digitie/canview/docs/reviews/adversarial/evidence/2026-09-05-r1-hardware-navigation-postfix-manifest.md

# Post-fix 동일 기준선 재검토 요청

## 최종 상세 sheet 수 표기 교정 요청

- 시각:2026-09-05 04:30:31 UTC
- A submission: `01a06fd5-1714-72a0-8322-d575cbdc0821`
- B submission: `01a06fd5-187f-79b1-8d61-fd06d04ad2ec`
- 두 post-fix 원문을 확정·보존한 뒤 동일하게 요청했다. 타 reviewer의 post-fix 판정은 공개하지 않았다.

```text
두 post-fix 원문을 서로 공개하기 전 파일로 보존했습니다. 마지막 기계적 count 교정 1줄만 독립 확인 요청합니다. 최종 c1c15b573476e176e0f445ea74d408bc923fa025, parent 57ac03a7394c98a1464bf0d9f2777df666f711ad. Windows Git object-only diff이며 hardware/communicator/README.md의 27개 상세 sheet를 28개(+root 총29)로 고칩니다. USB 감지 LDO sheet가 늘어난 최종 root/schematic.pdf와 수가 일치하는지, 다른 diff 없고 기존 PASS가 그대로 유지되는지 짧은 final addendum을 주세요. 기존 전체 review 반복 필요 없음. 두 reviewer에게 같은 요청. 타 reviewer의 post-fix verdict는 전달하지 않음.
```

## 기능 수정 재검토 요청

- 요청 시각:2026-09-05 04:17:14 UTC
- Reviewer A: `01a06f2e-7129-7261-99bc-1bf2a1d6d490`, submission `01a06fc8-ea0f-7b73-97ec-02bd05ec7990`
- Reviewer B: `01a06f2e-735a-7221-9541-de848f1984b2`, submission `01a06fc8-eb7c-72b2-8a0a-a746994bc732`
- Windows KiCad Python의 Git blob 검사 결과: revision `59b2412627eb9773410545690f0609175b80e756`, `git_blob_digest_mismatches=[]`, exit0

## 두 reviewer에게 전달한 공통 요청 원문

```text
R1 post-fix 동일 immutable 재검토 요청.
기준 commit=59b2412627eb9773410545690f0609175b80e756; parent/base(initial candidate)=06bb51c72180f9c040db3ccf0b223a823c570409. Repository F:/dev/canview. Windows native Git object-only 방식 유지. plain worktree는 계속 source 금지, 생성/코드 실행이 필요하면 Git blob bytes를 메모리로 로드하거나 별도 clean detached 방식 사용. 기존 AGENTS/runbook 적용. 두 최초 원문은 docs/reviews/adversarial/evidence/2026-09-05-r1-hardware-navigation-reviewer-a.md / -reviewer-b.md에 모두 독립 확정 후 보존했으므로 이제 cross-report 확인 가능.
Scope: 본인 findings 전부 closure 확인 + initial->postfix 전체 delta 회귀. 특히 Q1/Q2 BUK7Y12 DC±20V vs LM14.5/13V; FT U28/U29 active-high SN74AHCT1G126-Q1 CAHCT1G126DBVRQ1, AUTO5V supply +OE마다1k GND PD; USB detection-only U16 TPS7A2033 pre-limiter supply, U1/U2/pullup USB_CC3V3; USB3k minimum1mAload; PHY0 fault, startup/rail sequencing and other logic effects. 새 manufacturer PDF2개 저장(전체56개1745p). Current exports343physical BOM1235namedpads,4ERC0/waiver0. Main Windows full exporter completed including5hardware net/Boolean tests;16protocol host tests pass; allPDFhash/parse pass. 정적 회귀는 analog HIL이 아님.
B fixes: rate-array-derived mask, DR/profile/NAV/age crosschecks, UNAUTHORIZED non-public zero/digest, version strict2u8, WaveJ8 25TX43/27RX44 NC labels; encode와 raw-wire decode 모두 test. LF normalization+.gitattributes; --git-revision 검사로 immutable bytes check. Main command Windows KiCadPython validate_exports.py --git-revision 59b2412627eb9773410545690f0609175b80e756 --git-executable C:/Program Files/Git/cmd/git.exe.
Additional delta: native export normalization, artifact checks, document link validator preserving immutable reviewer original absolute paths, current docs/ref index/HIL cases, original reports preservation. Main independent C-01 hashes/C-02 FTpower duplicates are coordinator-audit.md.
Expected output: actual hash/isolation/time/id, each originalfinding FIXED or stillOPEN with primary evidence, whole delta newfoundP0~P3, scope/unperformedtests, final PASS/CONDITIONAL/BLOCK only for design-review integration. Explicitly do not approve PCB/G1/HIL/vehicleTX. Land90-0409 and missing latestPDFs/PCBthermal/SOA/micSI remain known physical release gates. No mutations. Please perform focused closure in ~5-10min without extending to unrelated backlog; do not omit non-fabrication defects.
```

A 추가 요청: 본인의 R1-A-001..004 원판정을 재확인하며 P1 closure를 명확히 판정하십시오.

B 추가 요청: 본인의 B-R1-001..004와 추가 version boundary를 재현하여 closure 확인하십시오.

## 후속 단일 쪽수 교정 — 동일 추가 요청

```text
작업을 처음부터 다시 시작하지 말고 마지막에 이 추가1줄 correction도 확인해 주세요. 추가 immutable commit 57ac03a7394c98a1464bf0d9f2777df666f711ad (parent59b2412627eb9773410545690f0609175b80e756)는 hardware/references/README.md의 AHCT DBV 도면 쪽수만17~19로 바로잡습니다. 20~22는DCK였고 실제회로/footprint에는변화없습니다. main이PDF17/19/20/22를 직접읽어확인했습니다. 기존59b2412의 전체postfix closure검토를 계속하되 final에서 이추가diff원문도확인하고 최종57ac03a까지대상으로 기록하십시오. 두 reviewer에게 동일하게전달합니다. 감사범위를 다른backlog로확장할필요없습니다.
```
