digitie/canview/docs/reviews/adversarial/evidence/2026-09-05-r1-hardware-navigation-postfix-reviewer-b.md

# Reviewer B 수정 후 원문

- 대상: `57ac03a7394c98a1464bf0d9f2777df666f711ad`
- 원 서브에이전트: `01a06f2e-735a-7221-9541-de848f1984b2`
- [공통 요청](2026-09-05-r1-hardware-navigation-postfix-manifest.md)
- 아래는 다른 reviewer의 수정 후 판정을 전달하기 전에 보존한 최종 응답 원문이다.

---

## Reviewer B 판정: PASS — 설계 검토본 통합에 한정

**B-R1-001~004와 추가 version boundary 모두 FIXED입니다.** 전체 post-fix delta에서 새 P0~P3 결함은 확인하지 못했습니다. PCB 제작·G1·HIL·차량 TX는 승인하지 않습니다.

### 실행·격리

- 실행 ID: `CANVIEW-R1-B-CLOSURE-20260905T041729Z`
- 시작/종료 UTC: `2026-09-05 04:17:29` → `04:25:05`
- initial: `06bb51c72180f9c040db3ccf0b223a823c570409`
- post-fix: `59b2412627eb9773410545690f0609175b80e756`
- **최종 대상: `57ac03a7394c98a1464bf0d9f2777df666f711ad`**
- Windows native Git으로 두 후속 commit의 type/hash/parent를 확인했습니다.
- **Object-only, clean=N/A — working tree를 소스로 사용하지 않았습니다.**
- 코드·시험은 Git blob에서 메모리로 로드했습니다. 파일 수정·Git mutation 없음.
- 허용된 최초 A/B 원문과 coordinator audit를 확인하되, closure는 실제 코드·생성물·제조사 PDF로 재검증했습니다.

### 기존 finding closure

| 항목 | 상태 | 확인 근거 |
|---|---|---|
| **B-R1-001 · P2** capability 모순 | **FIXED** | [codec:38](/mnt/f/dev/canview/tools/protocol/navigation_codec.py:38)의 배열 기반 mask와 profile/NAV/DR/age 교차 검사 확인. 기존 두 공격 입력 및 추가 undefined-bit 47개를 **encode·raw-wire decode 양쪽에서 거부**. DR age 0/1/45000/45001 경계도 확인했습니다. |
| **B-R1-002 · P2** UNAUTHORIZED snapshot 노출 | **FIXED** | [codec:67](/mnt/f/dev/canview/tools/protocol/navigation_codec.py:67)에서 status3의 공개 필드 외 값·digest를 0으로 강제합니다. 기존 노출 payload와 비공개 필드별 변조를 양방향에서 거부하고 정상 redacted 응답은 수용했습니다. |
| **B-R1-003 · P2** immutable hash 불일치 | **FIXED** | [LF 정책](/mnt/f/dev/canview/.gitattributes:1), [normalizer](/mnt/f/dev/canview/tools/hardware/normalize_exports.py:8), [immutable 검사](/mnt/f/dev/canview/tools/hardware/validate_exports.py:91) 확인. **59b2412와 최종 57ac03a 모두 16개 artifact digest mismatch=0, exit=0**입니다. |
| **B-R1-004 · P3** Waveshare UART 이름 반전 | **FIXED** | [생성 입력:76](/mnt/f/dev/canview/tools/hardware/sensor_circuits.py:76)과 생성물에서 **25=TXD43_NC, 27=RXD44_NC**, 두 접점 NC 유지 확인. 공식 schematic J8과 일치합니다. |
| 추가 version boundary | **FIXED** | [codec:89](/mnt/f/dev/canview/tools/protocol/navigation_codec.py:89)가 정확히 두 u8 정수만 허용합니다. 추가 원소·float·bool·누락·None·문자열·범위 초과를 거부하고 정상 tuple/list 경계는 수용했습니다. |

### 전체 delta의 전원·논리 회귀 확인

- **Q1/Q2:** BUK7Y12-100E의 DC VGS ±20V와 LM74800 최대 HGATE 14.5V/DGATE 13V를 원문으로 대조했습니다. 연결과 LFPAK56 유지도 확인했습니다. DC 여유는 각각 5.5V/7V이며, 동적 overshoot·SOA 승인은 아닙니다. 근거: [BUK7Y12 p.2](/mnt/f/dev/canview/hardware/references/pdf/buk7y12-100e.pdf), [LM7480 p.6](/mnt/f/dev/canview/hardware/references/pdf/lm7480.pdf).
- **FT U28/U29:** `CAHCT1G126DBVRQ1`, AUTO5V 공급, active-high OE, 각 1k GND pull-down을 실제 netlist에서 확인했습니다. 제조사 핀·진리표와 일치하며, PHY3V3=0의 정상상태에서는 TXD pull-up/EN pull-down으로 차단됩니다. 1k의 약 3.3mA 부하는 permit 구동기의 정상 전원 구동 능력 안입니다. 근거: [AHCT p.3–5, 8, 13](/mnt/f/dev/canview/hardware/references/pdf/sn74ahct1g126-q1.pdf).
- **USB 감지부:** 두 보드 모두 U16이 limiter/mux 앞에서 USB_CC3V3를 만들고 U1/U2/pull-up을 공급합니다. SYS3V3 순환 의존성이 없습니다. 3k 최소부하와 LDO ±1.5% 조건, TUSB320LAI 권장 VDD 범위도 대조했습니다. 급격한 collapse·느린 ramp·detach 과도응답은 정적 검사로 승인하지 않았습니다.

A의 원 finding에 대한 공식 closure 판정은 Reviewer A의 재확인이 별도로 필요합니다.

### 마지막 1줄 correction

`59b2412 → 57ac03a` 전체 diff는 **[reference 색인:68](/mnt/f/dev/canview/hardware/references/README.md:68)의 한 줄뿐**입니다.

PDF를 직접 확인한 결과:

- 17/18/19쪽: **DBV0005A** 외형/land/stencil
- 20/21/22쪽: **DCK0005A** 외형/land/stencil

수정이 정확하며 회로·footprint·코드·시험 객체에는 변화가 없습니다.

### 실제 재현 결과

| 검증 | 결과 |
|---|---|
| Windows protocol host 시험 | **16/16 PASS** |
| Hardware net·정상상태 Boolean 시험 | **5/5 PASS** |
| 생성 소스 → 연결 모델 → BOM/pinmap/XML/sexpr netlist/named pad | **343개 / 1,235개 일치** |
| Schematic S-expression 파싱 | **45개 PASS** |
| 제조사 PDF hash·크기·전체 페이지 파싱 | **56개 / 1,745쪽 / 95,230,736byte PASS** |
| 문서 링크 검사 | **113문서 / 690 local target, 오류 0** |
| CRLF 주입·LF 정규화·재실행 무변경 | 메모리의 지정 24파일에서 **PASS** |
| Margin 계산 | 저장 결과와 일치 |
| 저장된 ERC/waiver | 네 보드 **0/0 확인** |

시험·전체 생성물 검사는 `59b2412`에서 수행했고, 마지막 commit의 변경이 색인 한 줄뿐임을 확인했습니다. 최종 hash에 대한 immutable digest 검사는 별도로 재실행했습니다.

Native 전체 export/ERC 자체, analog fault injection, PCB/열/SOA, 실제 replay cache·동시 allocator, GNSS/PPS qualification, 마이크 3m SI는 실행하지 않았습니다. `embedded-documentation`은 변경된 핀·전원 소유권·문서 계약의 정합성 기준으로만 사용했습니다.

**결론: Reviewer B의 비제작 결함은 모두 닫혔습니다. 설계 검토본 통합은 PASS이며, land90-0409·미확보/최신 PDF·물리 검증 및 기존 제작/G1 차단은 그대로 유지해야 합니다.**
