digitie/canview/firmware/docs/esp-core-bench.md

# ESP32 공용 bench core

[T-200a](../../docs/tasks/T-200a-esp32-core-bench.md)의 Communicator core를 [T-400a](../../docs/tasks/T-400a-bridge-core-bench.md)에서 Bridge와 공용화한다. 후속 UART/무선/OTA와 실물 T-200/T-400 gate는 포함하지 않는다.

## 구성·소유권

`firmware/app/esp_core.c`는 SDK가 생성한 main task에서 BSP/runtime → portable boot → 고정 pool → 주기 health를 조합한다. `firmware/module/esp_core/health.c`, `pool.c`와 `firmware/interface/canview_esp_*.h`는 strict C99이며 HAL·SDK·FreeRTOS·heap API를 포함하지 않는다. 각 project의 `bsp/board.c`는 생성 pin 정본으로 안전 출력을 설정하고, `bsp/runtime.c`는 메모리와 진단 입력 pin을 SDK 독립 config에 연결한다. 실제 SDK include와 호출은 `firmware/platform/esp32s3/core_runtime.c`/`canview_esp32_runtime` component 하나에 둔다.

core·pool·runtime은 app의 정적 저장소이며 reset 전 재초기화하지 않는다. app stack에는 작은 port 사본만 둔다. 입력 config와 port, 0이 아닌 Flash/PSRAM 가용 byte 계약은 값으로 복사하며 callback context는 사용 완료까지 살아 있어야 한다. runtime의 main owner identity와 고정 주기 tick은 다른 task에서 접근하지 않는다. SDK adapter의 private 정적 spinlock 두 개는 watchdog과 pool용으로 분리한다. core callback은 open한 main owner task만 호출할 수 있으며 ISR과 같은 runtime callback의 재진입을 `INVALID_ARGUMENT`으로 거부한다. app은 그 실패를 service fault로 처리해 feed를 중단한다.

## Boot와 실패

| 단계 | 성공 조건 | 실패 시 |
|---|---|---|
| Communicator BSP | RUN_OK7 LOW → BOOT0 요청2 LOW → GPS47 LOW → reset1 HIGH → recovery9 OD HIGH → RTS15 HIGH → TX17 HIGH, 입력8/16/18/48/38 pull 없음 | 이후 단계 중단, 외부 default-safe gate 유지 필요 |
| Bridge BSP | LED5 LOW → button4 입력, 내부 pull 없음(R14 외부10k pull-up) | 이후 단계 중단, 입력이 서비스/페어링 허가로 승격되지 않음 |
| watchdog | TWDT2초 panic, 두 idle core 감시, 현재 main task 신규 등록 | 기존 subscription 탈취·자동 재시도 없음 |
| memory/clock | BSP 고정 Flash/PSRAM 정확 일치, internal heap≥80KiB/largest≥32KiB, main stack 여유≥1024B | 최초 fault 보존, feed 없음 |
| bench | pool 초기화와 USB metadata 진단 후 주기 health | UART/radio/CAN/OTA/NVS write 시작 없음 |

state는 UNINITIALIZED → STARTING → SAFE_BENCH 또는 FAULT다. boot 성공 자체는 watchdog feed가 아니다. clock backward/freeze, 이전 진척250ms 초과, health 실행20ms 초과, SDK 오류 또는 메모리 하한 위반이면 FAULT로 고정한다. callback에서 이미 latch한 fault도 덮어쓰지 않는다. wait/pool 오류도 app의 service status로 기록하고 loop를 빠져나가 더 이상 feed하지 않는다. `core.state`는 마지막 core 검사 상태이며 로그의 `status`와 함께 해석한다.

GPIO는 latch를 먼저 기록한 뒤 mode를 바꾼다. Communicator ESP와 Bridge는 partial GPIO 오류가 나도 이 표의 모든 safe output/input을 순서대로 시도하고 최초 오류를 보존한 뒤 다음 lifecycle 단계로 가지 않는다. RTS HIGH는 송신 흐름 정지, TX HIGH는 idle이다. UART driver를 설치하지 않는다. sense48은 서비스 RUN 감지, sense38은 USB mux 선택 진단일 뿐 rail PGOOD나 차량 권한이 아니다. cap/TX는 항상0이다. MCU 코드 실행 이전 reset/brownout 안전은 외부 pull/gate와 실물 계측 없이는 증명할 수 없다.

## 보드별 계약과 진단

| 보드 | Flash/PSRAM 실제 SDK 가용량 | 입력 valid mask와 bit 의미 | SDK project metadata |
|---|---|---|---|
| Communicator N16R8 | 16777216 /7864320B, Octal80MHz·ECC | 3: bit0 GPIO48 RUN sense, bit1 GPIO38 USB sense | canview_communicator_esp32 |
| Bridge N8R2 | 8388608 /2097152B, Quad80MHz·ECC 없음 | 1: bit0 GPIO4 PAIR_BUTTON_N, LOW=눌림, bit1 부재 | canview_diagnostic_bridge |

메모리는 board manifest/generator가 raw 용량과 ECC overhead를 구분하여 BSP header로 제공한다. generator는 wire와 무관한 0이 아닌 `CANVIEW_BOARD_PROFILE`도 header에 고정한다. 이 tag는 board ID만이 아니라 canonical board manifest 항목과 pin source를 함께 digest하므로 같은 ID의 stale pin contract도 다른 profile이 된다. `app_main()`은 BSP port를 한 번 복사한 뒤 `canview_esp_board_preflight()`로 runtime object의 생성 profile을 GPIO·idle·SDK open보다 먼저 대조한다. Communicator/Bridge runtime은 다시 같은 preflight를 적용하므로 서로 다른 BSP object를 교차 link하면 GPIO 0회·runtime open 0회로 거부한다. SDK sample은 측정값이며 boot/health의 고정 계약을 바꾸지 않는다. 다른 보드의 Flash 또는 PSRAM 값을 섞으면 terminal memory fault다. 공용 core는 SKU나 GPIO를 알지 않는다. 역할 표시는 SDK의 고정 project metadata에서 오며 외부 패킷으로 선택하지 않는다.

runtime은 입력 수1..2, SoC GPIO 유효성·중복·미사용 원소0을 검사한다. 실제 모듈 pad 제한은 generator가 별도로 검사하고, 독립 BSP fixture는 고정 핀을 대조한다. 로그의 input-valid는 존재하고 읽은 입력, input-level은 그 bit의 전기적 HIGH다. 미존재 bit를 LOW로 해석하지 않는다. Bridge 버튼은 폴링 진단이며 debounce/ISR/서비스 window/OTA/페어링을 시작하지 않는다. 어떤 sense 조합에서도 cap/TX0은 변하지 않는다.

## RTOS·시간·watchdog

| owner | 분류·우선순위·stack | 주기·예산 | 통신/감시 |
|---|---|---|---|
| IDF main service | soft real-time bench health, IDF main priority1/CPU0, stack8192B | 100ms fixed-rate, 이전 진척250ms, 실행20ms | 현재 task TWDT subscription 하나 |
| SDK idle CPU0/1 | SDK 소유, idle priority | SDK 스케줄링 | 각각 TWDT 감시; main은 대리 feed하지 않음 |

SDK 초기화·watchdog 등록에서 SDK 내부 allocation은 존재할 수 있다. core/pool runtime에는 malloc/free가 없다. Flash/PSRAM은 SDK 부팅이 초기화하며 application이 재초기화하거나 NVS를 열지 않는다. IDF6.0.3 `uxTaskGetStackHighWaterMark`는 **byte** 단위다. PSRAM get_size는 ECC 제외 가용 크기다. heap 수치는 internal·8-bit capability의 free와 largest block이며 PSRAM을 internal RAM으로 합산하지 않는다.

첫 wait에서 tick 기준을 잡고 이후 `xTaskDelayUntil`의 이전 wake tick을 보존한다. 지연 없이 반환되는 overrun은 TIMEOUT이다. catch-up loop로 여러 feed를 만들지 않는다. 32-bit tick wrap은 SDK API에 맡기며 health는 별도의 64-bit monotonic microsecond clock을 검사한다.

core는 sample 완료 뒤 시간을 검사하고, adapter는 자신의 critical section 진입 뒤 clock을 검사한 후 `esp_task_wdt_reset`을 호출하며 호출 직후 clock을 다시 확인한다. `fed_at`은 SDK 호출 직후 확인한 **post-call 시각**이다. task 선점은 막지만 SDK 내부 spinlock 대기, NMI/고우선순위 interrupt·cache stall 상한과 watchdog reset latency는 HIL 미검증이다. 이 상한을 이미 보장했다고 주장하거나 차량 safety deadline으로 재사용하면 안 된다. 다른 worker를 추가할 때 각 worker가 자기 subscription과 진척을 소유해야 한다.

실패 후 app은 한 번 상태를 출력하고 idle만 호출한다. 등록 후에는 main이 feed하지 않아 TWDT panic/reset을 기다리며, 등록 전 실패는 safe idle로 남는다. USB가 연결되지 않은 경우 출력 지연도 health deadline에 포함된다. journal/자동 NVS erase/reboot 복구는 구현하지 않는다.

## 고정 pool 계약

정적16slot × payload256B, capacity1..16이다. 초기화와 acquire/copy/release/stats 모두 platform context validator를 먼저 호출해 ISR을 상태 변경·lock 진입 전에 거부한다. task 또는 SDK callback이 동일 bounded lock을 통해 acquire/copy/release/stats를 호출한다. pool은 lock을 잡은 채 client callback을 실행하지 않으며, consumer가 lock 내부에서 다시 pool API를 호출하는 것은 금지한다. ISR·lock 내부 callback·token의 동시 다중 owner 사용은 금지한다. 256B 복사/clear는 lock 아래 수행하며 실제 critical WCET는 아직 계측하지 않았다. radio ingress에 사용하기 전 T-202에서 예산을 측정한다.

acquire는 payload를 복사하고 pool 주소·slot·generation token을 반환한다. 내부 pointer를 노출하지 않는다. context/output/source alias와 크기 오류를 거부한다. 해제는 payload를 지우고 generation이 UINT32_MAX인 slot은 영구 retire하여 wrap ABA를 막는다. token은 RAM 전용이며 serialize/reboot 뒤 재사용하지 않는다. exhaustion/stale은 UINT32_MAX에서 포화하며 used/high-water/retired를 lock 아래 snapshot으로 반환한다. 부족하거나 잘못된 token이면 출력 버퍼/길이를 변경하지 않는다.
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
