digitie/canview/docs/tasks/T-400a-bridge-core-bench.md

# T-400a Bridge 최소 core와 ESP 공용화

- 상태: `DONE`
- merge: [PR #23](https://github.com/digitie/canview/pull/23), `25eba080907257c6d90abaeec6d578d9dff6585a`
- 우선순위: `P0`
- Gate: `G0 / G1 software 준비`; 실제 G1/G2 물리 gate는 `NOT_RUN`
- 선행: `T-001`, `T-200a`

## 목표와 분리 이유

Communicator ESP32 core merge 다음으로 Bridge N8R2의 boot/health/watchdog 기반을 구현한다. T-400의 SoftAP·인증·무선·휴대폰·부하·실물 acceptance는 유지하고 최소 core 소프트웨어만 분리한다. 공통 동작을 복제하지 않고 재사용하되 Communicator N16R8의 검증된 안전 초기화와 실패 동작을 보존한다.
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
