digitie/canview/docs/reviews/adversarial/evidence/2026-09-09-T-104-validation-14ea3c9.md

# T-104 수정 candidate 로컬 검증

- Candidate: `14ea3c9bcad22ac27fa8989291ea54656f6f4952`
- Base: `b17bdfc0bb2a1bfa9d300c1e7662cac05c96df40`
- 실행: 2026-09-09, Windows PowerShell; Linux는 WSL 보충 검증이다.
- firmware/shared/protocol canonical source SHA-256:
  `8ccfe8d227ba3454dab51864cc65634f4922c5351aabe4296564061f63e47b56`
- 검증은 commit 직전 동일 source에서 수행했고, host fixture provenance의 commit
  필드는 당시 HEAD `bdc6798`이다. firmware source digest로 수정 source를 구분한다.
- 독립 reviewer verdict나 CI 결과를 이 문서가 대신하지 않는다.

## 실제 실행 결과

| Gate | 결과 |
|---|---|
| Windows Clang Debug CTest | 120/120, 24.17초 |
| Windows Clang Release CTest | 120/120, 19.98초 |
| Python unit (Windows CTest 포함) | 117/117 |
| WSL GCC Release CTest | 120/120, 117.88초 |
| WSL Clang ASan/UBSan CTest | 120/120, 120.84초 |
| WSL TSan `esp32-pool-threads` | 1/1 |
| SDK 설정 negative/mutation | 13/13 |
| STM32 core binary gate unit | 7/7, GNU note/symbol/BIN malformed 포함 |
| STM32 coverage 기존 core/FDCAN/register | 설정된 function100/line95/branch90 gate 통과 |
| UART owner coverage function/line/branch | 100/73.4844/58.4282%, gate 100/70/50 |
| UART platform coverage function/line/branch | 100/79.5812/58.3851%, gate 100/70/50 |
| ESP32 core/pool/runtime coverage | function100/line95/branch90 및 app/wrong-BSP profile gate 통과 |
| shared wire/app coverage | line/function100%, branch99% 이상 |
| Doxygen 1.18.0 + Sphinx strict | PASS, 설정된 public API 71개 |
| board/UART/generated/plan/link | PASS; 문서 313개, local target 1317개, 오류 0 |
| staged diff 수동·제한된 secret/VIN/key pattern scan | match 0 |

HELLO reset의 digest 보존 assertion 추가 후 Windows/WSL 전체 시험과 STM32·ESP32·
shared wire/app coverage를 모두 재실행했다. STM32 UART source 실측 수치는 동일했다.

WSL 첫 GCC 실행은 Python provenance suite 실패로 전체 `FAIL`이었다. Windows
worktree `.git` 파일 안의 `F:/...`가 Linux에서 유효하지 않아 commit이 `unknown`으로
반환됐다. `GIT_DIR=/mnt/f/dev/canview/.git/worktrees/t104-stm32-uart-control`와
`GIT_WORK_TREE=/mnt/f/dev/canview-wt/t104-stm32-uart-control`를 해당 shell에만 설정하고
`git rev-parse HEAD`를 대조한 뒤 위 전체 GCC/ASan/UBSan 성공 결과를 얻었다.
Git metadata, source, timeout, 검사 조건은 수정하지 않았다.

## STM32 실제 target

STM32CubeG4 `1.6.3`, Arm GNU `15.3.rel1`, Ninja, Windows native build다.
각 build의 `cmake --build <build> --clean-first -j 6` stdout/stderr를
`t104-final-build.log`에 저장하고 `warning:|CMake Warning|ld\.exe: warning|error:`를
대소문자 무관 scan했다. Debug/Release 모두 compiler/linker/CMake 진단 0건이다.

| 항목 | Debug (`build-t104-target-debug3`) | Release (`build-t104-target-release`) |
|---|---:|---:|
| Flash used | 51716 B | 39720 B |
| RAM used | 79816 B | 79816 B |
| CCMRAM used | 0 B | 0 B |
| 최대 개별 stack frame | 928 B | 992 B |
| GNU SHA-1 build ID 앞 16 byte | `579f8e9de845abfc08abb195dfa5cf74` | `20cc3b17ecdec7df7dcc061ca8675d52` |

개별 frame은 최악 call-chain·ISR 중첩 stack 실측이 아니다. ELF note를 objcopy로
추출해 GNU owner/type/20-byte descriptor를 확인하고, BSP linker symbol 주소와
Flash BIN의 동일 위치를 자동 대조했다. 독립 `readelf -n`도 해당 ID를 확인했다.
FDCAN RAM layout·54 CMSIS/model constants·23 C object stack 파일 gate도 통과했다.

artifact basename은 모두 `canview-communicator-stm32`다.

| Build | 형식 | 크기 B | SHA-256 |
|---|---|---:|---|
| Debug | BIN | 51716 | `865d82ebaf54d0b4dee61844fe3f7288a088ff6e6fd1dc64727b04a60f6d0f8b` |
| Debug | ELF | 1078332 | `b6fa73b82b1a8986067d715e7a69a281ecbfd26f7dbeeebd0dedd1caf60f0908` |
| Debug | HEX | 145564 | `a874298a2de897d8af7d9f0613688f33dcef2ca53b607868076f35f15860b8d4` |
| Debug | MAP | 322532 | `083378ab841f1f5823da6fe3d905251c950fd91524d176a904a9880bdb58c833` |
| Release | BIN | 39720 | `5694eea4399f67954420aff56ad41db3e76792e8ededd9f11391ba0ca1a68469` |
| Release | ELF | 62576 | `f11a5fddf9ef49eec779378f4f4e4c48dd97f621e98c618ee07122a1ef80c3e3` |
| Release | HEX | 111814 | `714e6b9234a8b846beeaaca37f02fc24edb99ddb781e4dc6bbf1409d083c2bab` |
| Release | MAP | 236658 | `75226b55ce550863c99e419f6834f9db245ff45ba1b9cd1ad6975a76ad604b53` |

build log SHA-256:

- Debug: `1cbe67488ddc10319eb10f28a9b8f1b454cd0ff2c18e2da5259d63512778de54`
- Release: `fc891b0f5fbe0b27ff23a9b3865abe01a2cb404fe353a1939be9969f2a08115e`

## 남은 gate

최신 candidate CI와 세 ESP target의 CI artifact 대조, 원 reviewer post-fix verdict는
별도 closure 대상이다. 이전 `bdc6798` CI `34322587967`의 6개 job 성공은 확인했지만
이를 `14ea3c9`의 CI 결과로 사용하지 않는다. 이전 24시간 분량 가속 C codec soak는
전기선·DMA·RTS/CTS 24시간 측정이 아니다.

실제 board flash/ST-LINK/USB, 전원·reset·brownout·watchdog 장시간 실측, 4 Mbps
UART·DMA/IRQ·CTS/RTS 및 physical 24시간 PRBS, CAN analyzer·차량 evidence,
security provisioning은 모두 `NOT_RUN`이다. G1/G2 물리 승인이나 vehicle TX
권한을 부여하지 않는다. 현재 `CAPTURE_ONLY`, 차량 CAN TX `NO-GO`를 유지한다.
