digitie/canview/docs/reviews/adversarial/evidence/2026-09-05-latest-toolchain-bootstrap-post-fix-reviewer-a.md

# Reviewer A 원본 결과

- Review ID: `CV-20260905-ENV-01-POST-A`
- 실행 ID: `01a06f3e-a770-7d61-a07a-32bbb40e928a`
- 전문 영역: embedded safety·target build·PowerShell
- 기준 commit: `cb7aae92e741f4bdeb5dc9a8a81011fc3b17c391`
- parent: `e7ad3c9e3a13ddcb2fe5b53364f12f582e9eaf2f`
- 작업 방식: read-only commit review, 파일 변경·commit 없음

## 결과

**PASS — P0–P3 finding 없음.**

`cb7aae9`와 parent hash를 확인했다. 추가된 recursive submodule cleanliness check가 incomplete·dirty clone을 올바르게 차단하며, tag·peeled commit·PATH·failure cleanup 검증을 약화시키지 않는다.

Windows PowerShell 실행과 target build는 이 Linux review 환경에 필요한 도구가 없어 미검증이다. build 성공으로 표시하지 않았다.
