digitie/canview/docs/reviews/adversarial/evidence/2026-09-05-latest-toolchain-bootstrap-post-fix-reviewer-b.md

# Reviewer B 원본 결과

- Review ID: `CV-20260905-ENV-01-POST-B`
- 실행 ID: `01a06f3e-a9c9-75a1-a3d3-6969e1b0dbd8`
- 전문 영역: protocol·security·reproducibility·integration·문서
- 기준 commit: `cb7aae92e741f4bdeb5dc9a8a81011fc3b17c391`
- parent: `e7ad3c9e3a13ddcb2fe5b53364f12f582e9eaf2f`
- 작업 방식: read-only commit review, 파일 변경·commit 없음

## 결과

**PASS — P0–P3 finding 없음.**

`cb7aae9`와 parent hash를 확인했다. 최종 commit은 `tools/environment/setup-windows.ps1`의 recursive submodule dirty-worktree 검증만 변경하며, manifest·version·source·CMake·문서·secret leakage를 악화시키지 않는다.

PowerShell, CMake, Ninja, Arm toolchain executable이 이 Linux review 환경에 없어 target build/runtime 검증은 미실행이다. build 성공으로 표시하지 않았다.
