digitie/canview/docs/reviews/adversarial/evidence/2026-09-05-document-information-architecture-post-fix-reviewer-a.md

# Reviewer A post-fix 재검토 결과 — 문서 정보구조

- Review ID: `ADV-2026-09-05-DOC-IA-01`
- Reviewer 역할: 문서 정보구조·AI agent 인지부하·Windows/worktree·CodeGraph·탐색성
- Subagent thread ID: `01a06e67-2e3f-7343-b605-e72ad615a94b`
- 분석 turn ID: `01a06ef2-bcc8-7651-a62a-43b04313e637`
- 결과 재출력 turn ID: `01a06ef8-9395-7ed3-b8ea-b22245c23166`
- 시작: `2026-09-05T09:23:17+09:00`
- 종료: `2026-09-05T09:29:58+09:00`
- Review candidate: `b6f523fe1d5fdaa01b337facbbda127cc384cda5`
- Post-fix commit: `ab613c8f70d6bb5658c20b662e152e61d421c239`
- 격리 방식: commit object-only (`git cat-file`, `git rev-parse`, `git show`, `git diff`)
- 작업 트리 변경·commit·push: 없음
- Reviewer verdict: `CONDITIONAL`

## 실행과 관찰

두 commit을 object로 확인하고 plain working-tree 내용 대신 snapshot과 diff만 읽었다. `git diff --check`가 통과했고 Markdown 87개의 상대 link 487개에서 누락 target 0개를 확인했다. task 없는 작업 진입 규칙, stale label, Windows 문서의 workflow 위임, 일반·detached worktree parent directory 생성, report와 두 최초 evidence의 연결을 교차 검사했다.

## Finding 재판정

| Finding | 판정 | 근거 |
|---|---|---|
| A-P1-01 | `FIXED*` | 통합 report, Reviewer A/B 최초 evidence와 archive index가 추가됐다. 별표 조건은 post-fix 결과를 report에 기록하는 closure뿐이다. |
| A-P2-01 | `FIXED` | task가 있을 때만 상세 task를 읽고 문서·review 전용 작업은 관련 runbook/template을 사용하도록 정본이 정렬됐다. |
| A-P3-01 | `FIXED` | 이동 전 basename label이 역할 기반 label로 교체됐다. |
| A 추가 관찰 — worktree 중복 | `FIXED` | Windows 문서는 실행 절차를 agent workflow에 위임한다. |
| A 추가 관찰 — parent directory | `FIXED` | 일반 worktree와 detached review 절차 모두 parent directory를 먼저 만든다. |

`b6f523f..ab613c8`에서 firmware, protocol schema, hardware source 변경이나 신규 `P0`/`P1` 회귀는 발견하지 못했다.

## 한계와 verdict

실제 Windows PowerShell, CodeGraph CLI, SDK/build, CI, HIL·hardware와 외부 link 내용은 실행하지 않았다. Reviewer A는 자신의 모든 항목을 해소된 것으로 판정했고, Reviewer B 재검토와 통합 report의 post-fix hash·두 verdict·최종 disposition 기록을 조건으로 `CONDITIONAL`을 부여했다. 통합 report의 closure 절에서 이 조건의 충족을 기록한다.
