digitie/canview/docs/reviews/adversarial/evidence/2026-09-05-document-information-architecture-post-fix-reviewer-b.md

# Reviewer B post-fix 재검토 결과 — 리뷰 gate와 감사성

- Review ID: `ADV-2026-09-05-DOC-IA-01`
- Reviewer 역할: 품질 gate·독립성·disposition·ADR/task/review 책임·Git/PR 감사성
- Subagent thread ID: `01a06e67-3b80-77f1-80b0-e6616ec4e4eb`
- Turn ID: `01a06ef2-c439-7fc3-8495-7ee835dd6870`
- 시작: `2026-09-05T09:23:19+09:00`
- 종료: `2026-09-05T09:26:33+09:00`
- Review candidate: `b6f523fe1d5fdaa01b337facbbda127cc384cda5`
- Post-fix commit: `ab613c8f70d6bb5658c20b662e152e61d421c239`
- 격리 방식: commit object-only (`git cat-file`, `git rev-parse`, `git show`, `git diff`)
- 작업 트리 변경·commit·push: 없음
- Reviewer verdict: `CONDITIONAL`

## 실행과 관찰

두 commit object와 full hash를 확인하고 post-fix commit의 parent가 review candidate와 정확히 일치함을 검증했다. `git diff --check`가 통과했고 snapshot Markdown local link 471개에서 누락 0개를 확인했다. P0/P1 disposition과 면제 규칙의 상충 검색, reviewer evidence metadata, T-001의 Windows/Linux 역할, template field와 `ui/prototype/README.md` 존재를 교차 검사했다.

## Finding 재판정

| Finding | 판정 | 근거 |
|---|---|---|
| B-P1-01 | `FIXED` | workflow가 object-only와 detached worktree, hash·clean 검증을 실행 명령으로 정의한다. |
| B-P1-02 | `FIXED` | reviewer별 thread/turn, 시각, commit과 원본 evidence가 보존된다. |
| B-P1-03 | `FIXED` | P0/P1은 원 reviewer 확인을 거친 `FIXED` 또는 `REJECTED_WITH_EVIDENCE`만 허용한다. |
| B-P1-04 | `FIXED` | normative 문서는 면제하지 않고 일반 면제를 좁은 조건과 비작성자 승인으로 제한한다. |
| B-P1-05 | `FIXED` | T-001이 Windows 필수 기준과 Linux portability/sanitizer matrix를 분리한다. |
| B-P2-01 | `FIXED` | template에 재현·실패 형태와 영향 field가 있다. |
| B-P2-02 | `FIXED` | workflow에 P0~P3 정의와 merge 효과가 있다. |
| B-P3-01 | `FIXED` | `ui/prototype/README.md`가 존재하고 문서 지도에서 직접 연결된다. |

`b6f523f..ab613c8`에서 신규 `P0`/`P1` 회귀는 발견하지 못했다.

## 한계와 verdict

firmware runtime, hardware safety, HIL과 외부 link 내용은 검토 범위 밖이다. Reviewer B는 자신의 모든 finding을 해소된 것으로 판정했고, Reviewer A 재확인과 통합 report의 `FIXED` 상태·최종 verdict·재검증 기록을 조건으로 `CONDITIONAL`을 부여했다. 통합 report의 closure 절에서 이 조건의 충족을 기록한다.
