digitie/canview/hardware/bridge/kicad/01_usb_c.kicad_sch

## KiCad design hardware/bridge/kicad/01_usb_c.kicad_sch (2026-09-06)

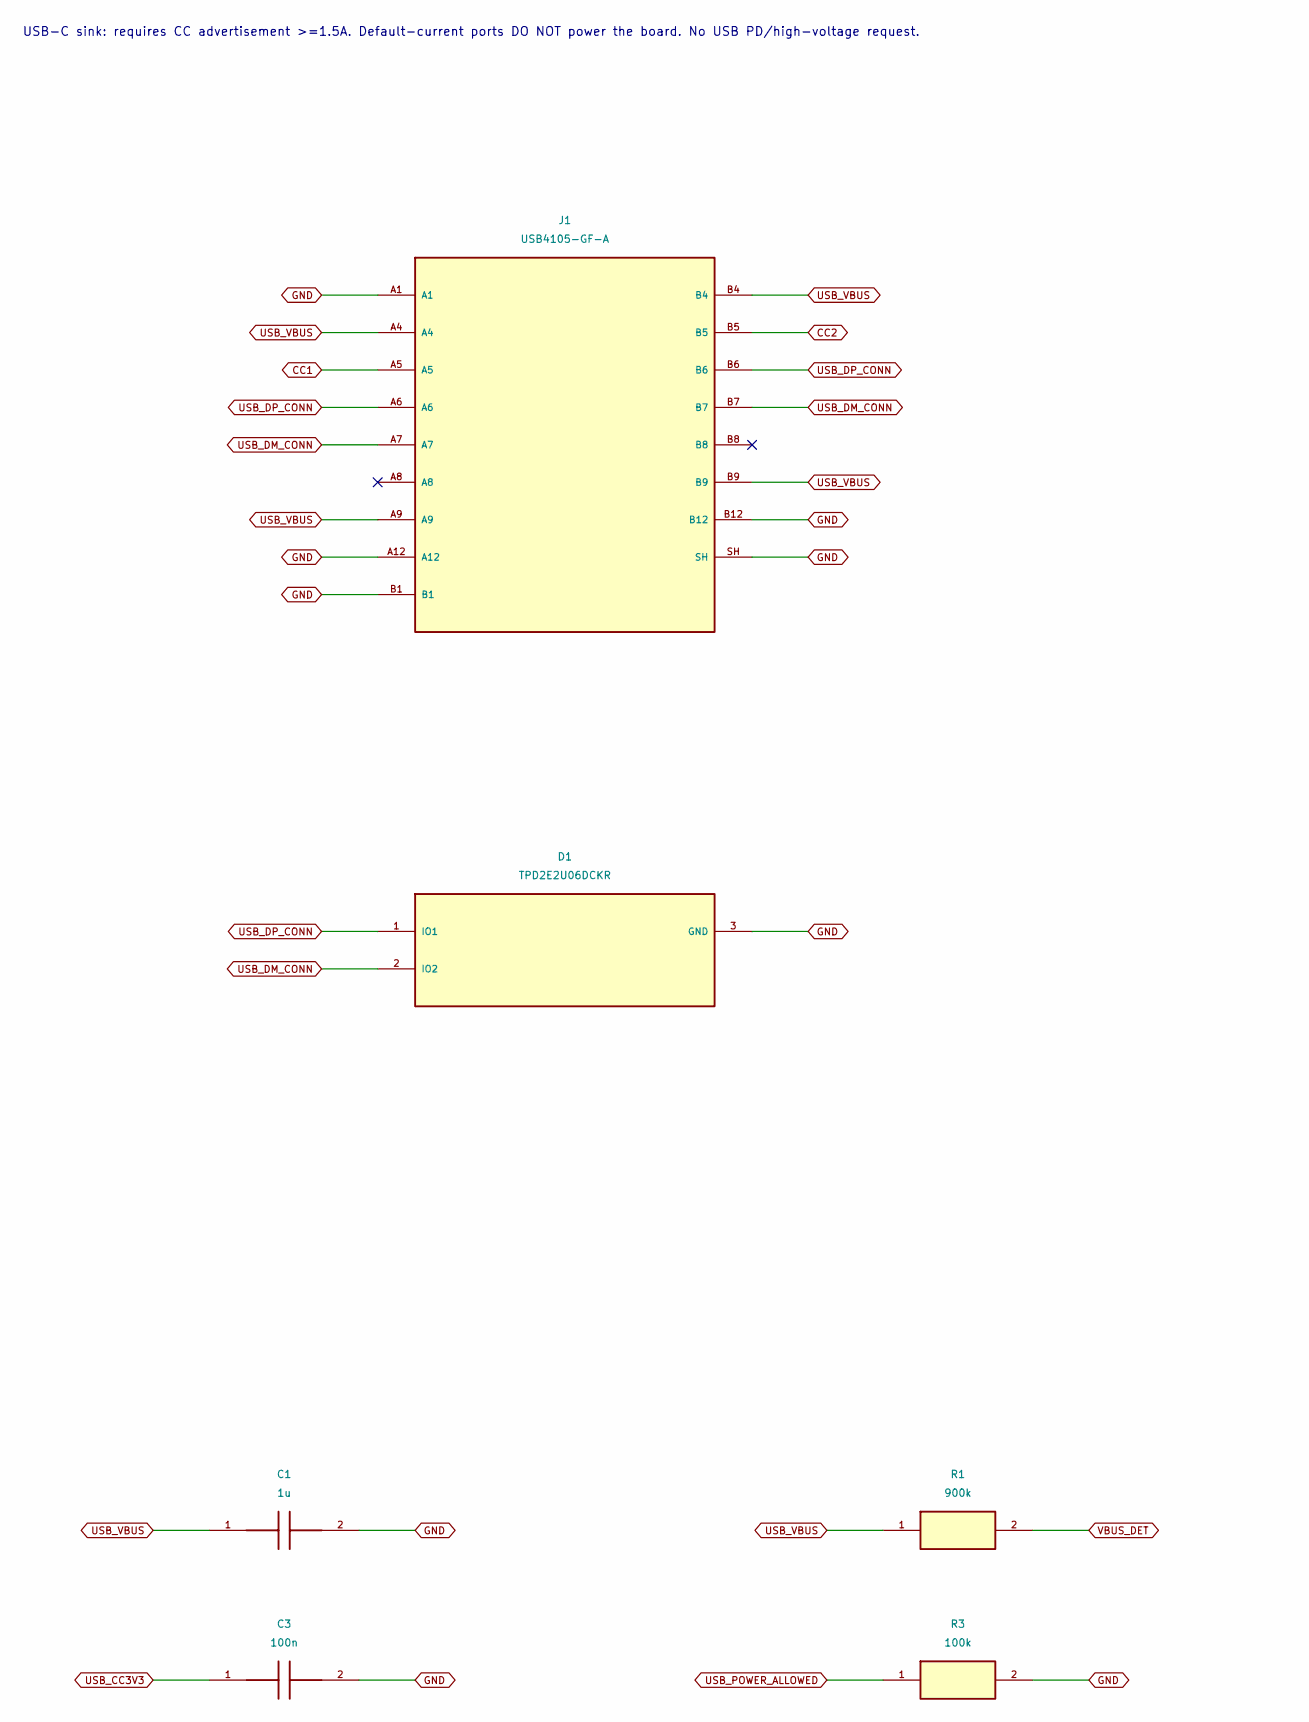
[picture p66: schematic 01_usb_c.kicad_sch, part in row 1, column 1]

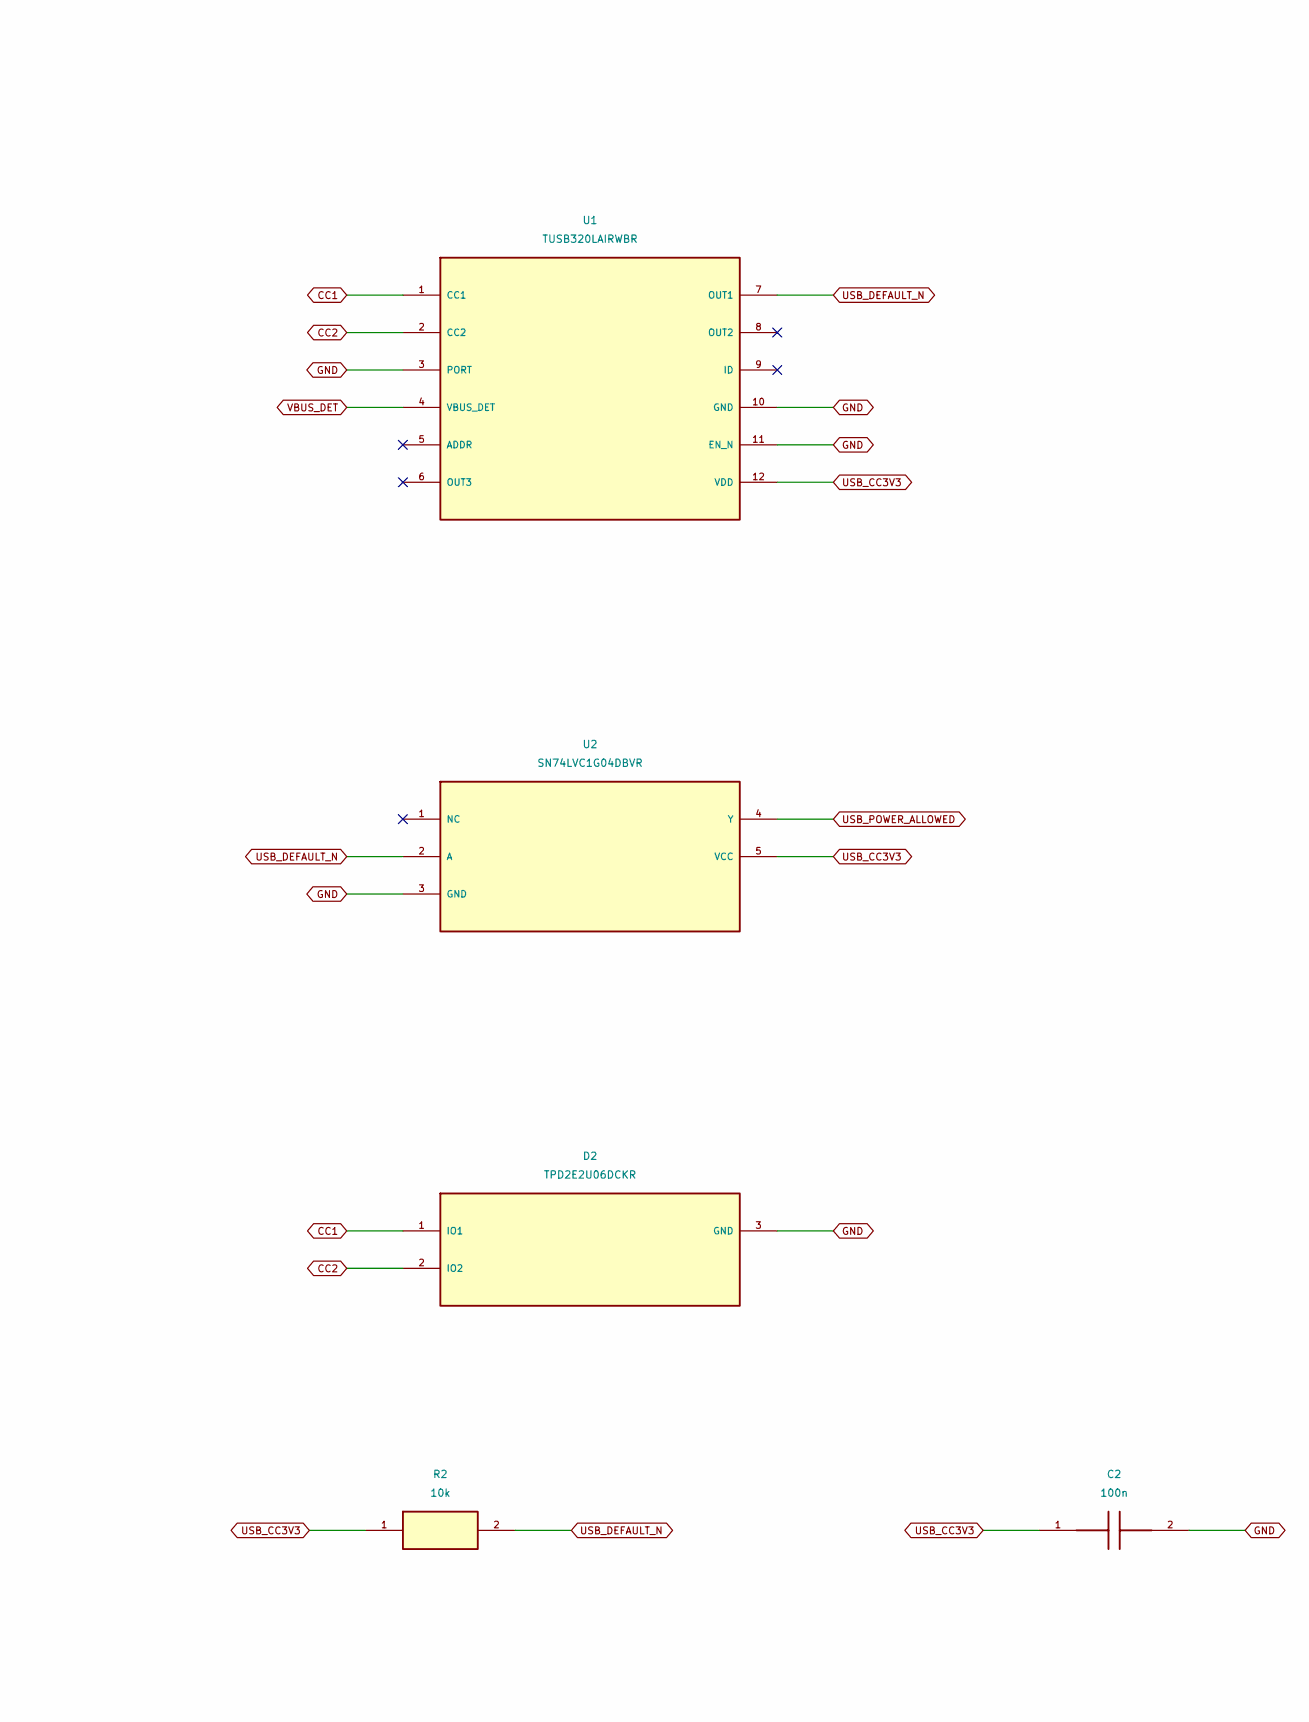
[picture p67: schematic 01_usb_c.kicad_sch, part in row 1, column 2]

Parts:
C1: 1u; Capacitor_SMD__C_0603_1608Metric; MPN GEN-C-0603-1u-16V-X7R
C2, C3: 100n; Capacitor_SMD__C_0402_1005Metric; MPN GEN-C-0402-100n-16V-X7R
D1, D2: TPD2E2U06DCKR; Package_TO_SOT_SMD__SOT-323_SC-70; MPN TPD2E2U06DCKR
J1: USB4105-GF-A; Connector_USB__USB_C_Receptacle_GCT_USB4105-xx-A_16P_TopMnt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; MPN USB4105-GF-A
R1: 900k; Resistor_SMD__R_0402_1005Metric; MPN GEN-R-0402-900k-1%
R2: 10k; Resistor_SMD__R_0402_1005Metric; MPN GEN-R-0402-10k-1%
R3: 100k; Resistor_SMD__R_0402_1005Metric; MPN GEN-R-0402-100k-1%
U1: TUSB320LAIRWBR; Package_DFN_QFN__Texas_X2QFN-12_1.6x1.6mm_P0.4mm; MPN TUSB320LAIRWBR
U2: SN74LVC1G04DBVR; Package_TO_SOT_SMD__SOT-23-5; MPN SN74LVC1G04DBVR

Connections:
CC1: D2.1 (IO1), J1.A5, U1.1 (CC1)
CC2: D2.2 (IO2), J1.B5, U1.2 (CC2)
GND: C1.2, C2.2, C3.2, D1.3 (GND), D2.3 (GND), J1.A1, J1.A12, J1.B1, J1.B12, J1.SH, R3.2, U1.3 (PORT), U1.10 (GND), U1.11 (EN_N), U2.3 (GND)
USB_CC3V3: C2.1, C3.1, R2.1, U1.12 (VDD), U2.5 (VCC)
USB_DEFAULT_N: R2.2, U1.7 (OUT1), U2.2 (A)
USB_DM_CONN: D1.2 (IO2), J1.A7, J1.B7
USB_DP_CONN: D1.1 (IO1), J1.A6, J1.B6
USB_POWER_ALLOWED: R3.1, U2.4 (Y)
USB_VBUS: C1.1, J1.A4, J1.A9, J1.B4, J1.B9, R1.1
VBUS_DET: R1.2, U1.4 (VBUS_DET)

Notes on the sheet:
USB-C sink: requires CC advertisement >=1.5A. Default-current ports DO NOT power the board. No USB PD/high-voltage request.
