digitie/canview/hardware/bridge/kicad/01a_usb_cc_supply.kicad_sch

## KiCad design hardware/bridge/kicad/01a_usb_cc_supply.kicad_sch (2026-09-06)

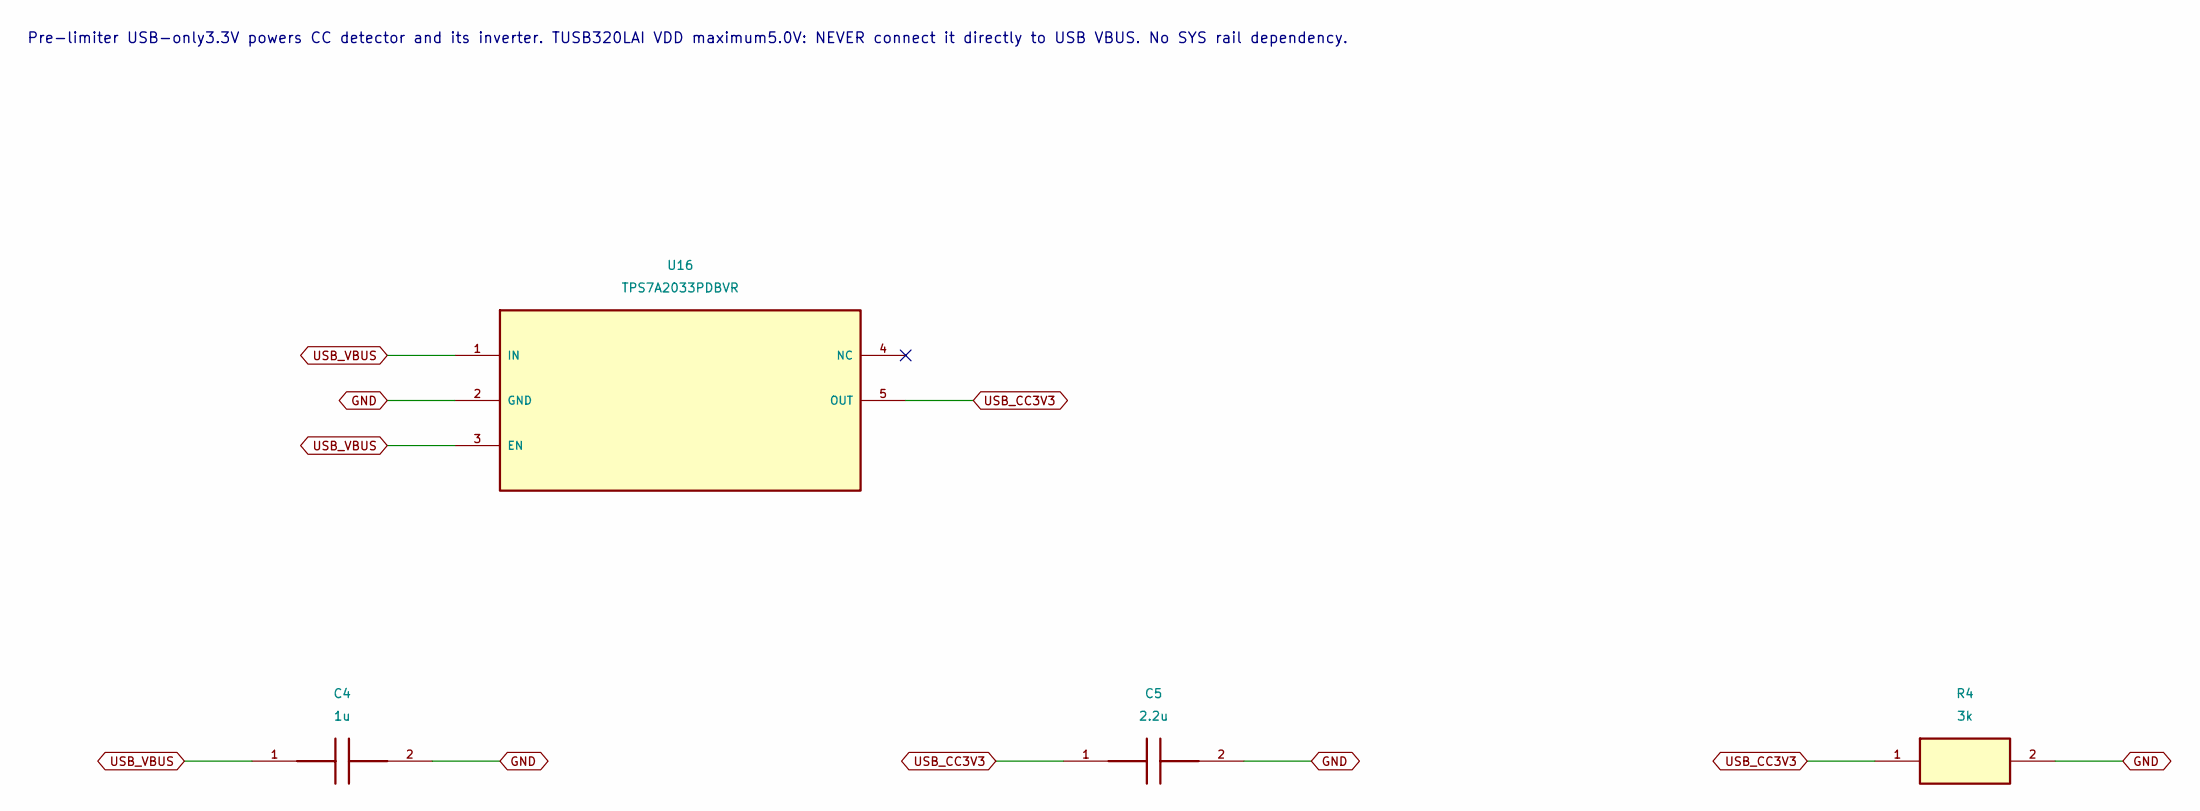
[picture p68: schematic 01a_usb_cc_supply.kicad_sch]

Parts:
C4: 1u; Capacitor_SMD__C_0603_1608Metric; MPN GEN-C-0603-1u-16V-X7R
C5: 2.2u; Capacitor_SMD__C_0603_1608Metric; MPN GEN-C-0603-2.2u-16V-X7R
R4: 3k; Resistor_SMD__R_0402_1005Metric; MPN GEN-R-0402-3k-1%
U16: TPS7A2033PDBVR; Package_TO_SOT_SMD__SOT-23-5; MPN TPS7A2033PDBVR

Connections:
GND: C4.2, C5.2, R4.2, U16.2 (GND)
USB_CC3V3: C5.1, R4.1, U16.5 (OUT)
USB_VBUS: C4.1, U16.1 (IN), U16.3 (EN)

Notes on the sheet:
Pre-limiter USB-only3.3V powers CC detector and its inverter. TUSB320LAI VDD maximum5.0V: NEVER connect it directly to USB VBUS. No SYS rail dependency.
