digitie/canview/hardware/bridge/kicad/02_esp32.kicad_sch

## KiCad design hardware/bridge/kicad/02_esp32.kicad_sch (2026-09-06)

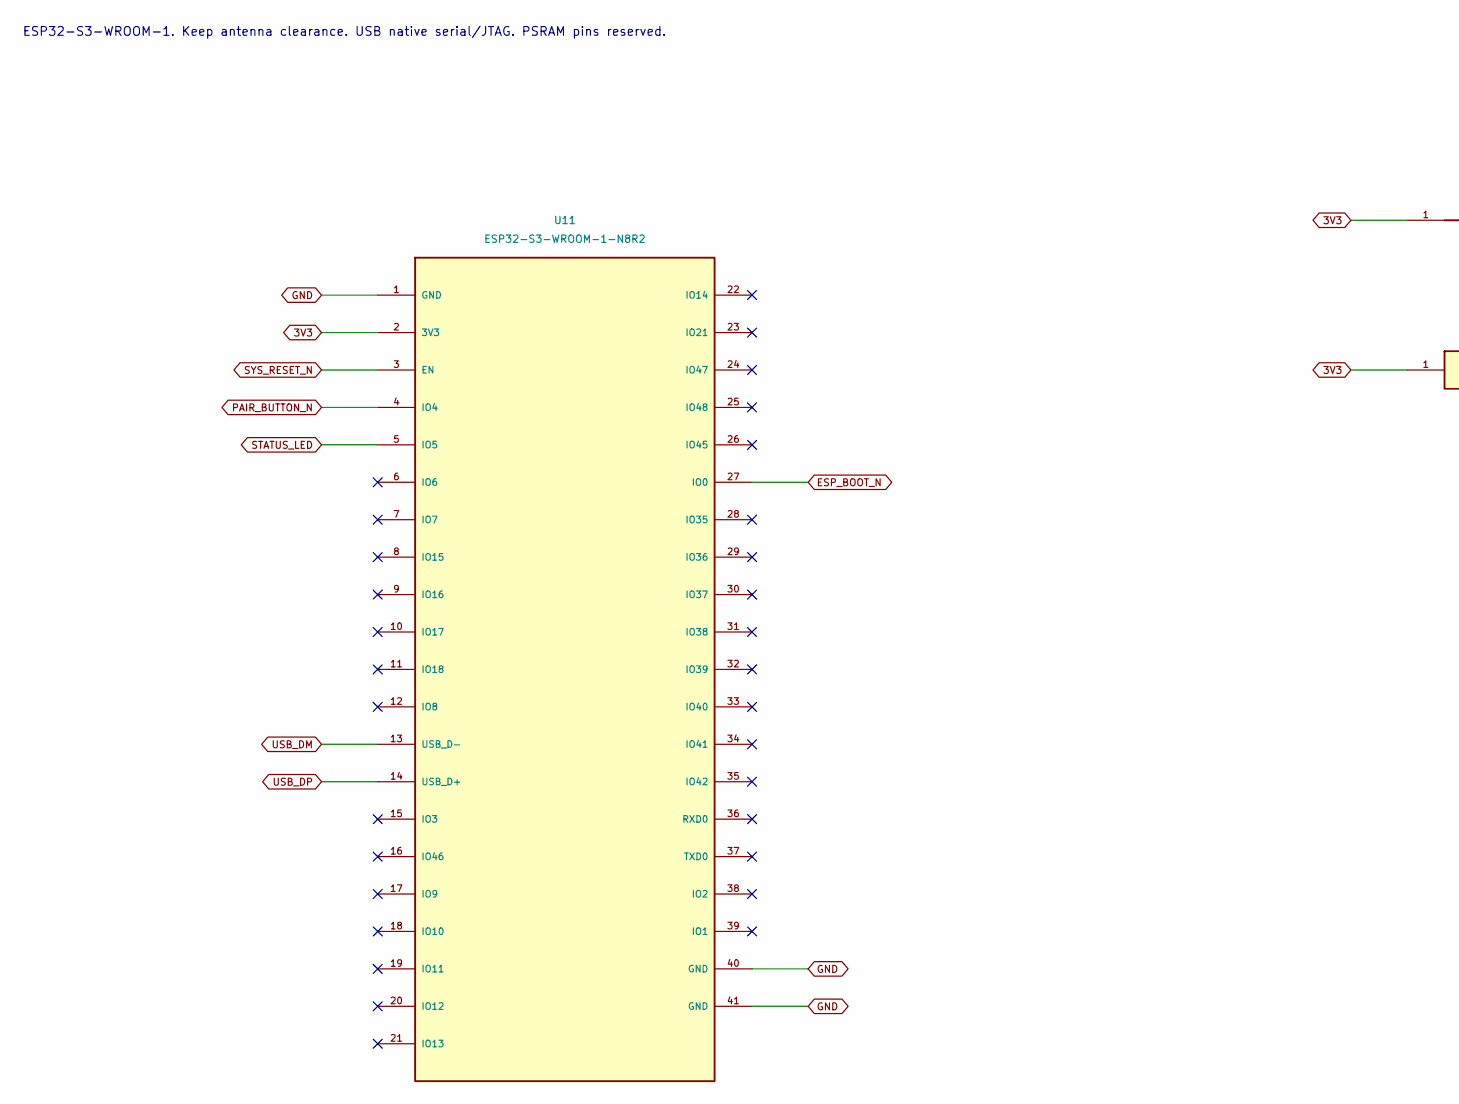
[picture p71: schematic 02_esp32.kicad_sch, part in row 1, column 1]

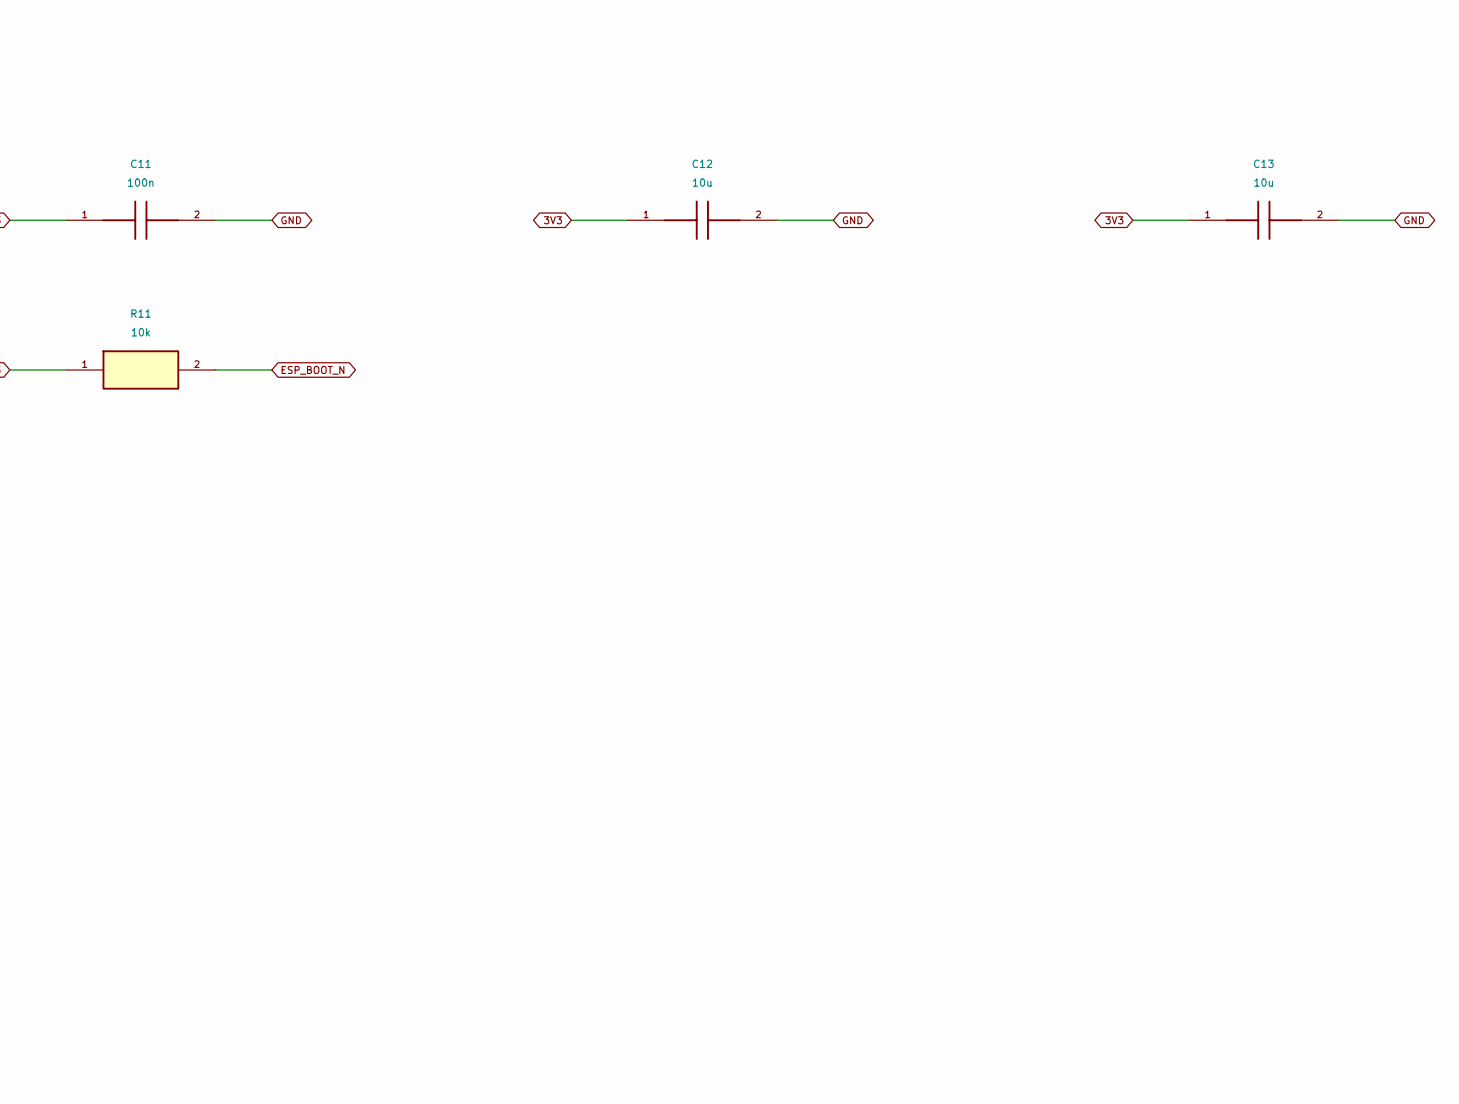
[picture p72: schematic 02_esp32.kicad_sch, part in row 1, column 2]

Parts:
C11: 100n; Capacitor_SMD__C_0603_1608Metric; MPN GEN-C-0603-100n-16V-X7R
C12, C13: 10u; Capacitor_SMD__C_0603_1608Metric; MPN GEN-C-0603-10u-16V-X7R
R11: 10k; Resistor_SMD__R_0402_1005Metric; MPN GEN-R-0402-10k-1%
U11: ESP32-S3-WROOM-1-N8R2; RF_Module__ESP32-S3-WROOM-1; MPN ESP32-S3-WROOM-1-N8R2

Connections:
3V3: C11.1, C12.1, C13.1, R11.1, U11.2 (3V3)
ESP_BOOT_N: R11.2, U11.27 (IO0)
GND: C11.2, C12.2, C13.2, U11.1 (GND), U11.40 (GND), U11.41 (GND)
PAIR_BUTTON_N: U11.4 (IO4)
STATUS_LED: U11.5 (IO5)
SYS_RESET_N: U11.3 (EN)
USB_DM: U11.13 (USB_D-)
USB_DP: U11.14 (USB_D+)

Notes on the sheet:
ESP32-S3-WROOM-1. Keep antenna clearance. USB native serial/JTAG. PSRAM pins reserved.
