digitie/canview/hardware/bridge/kicad/02_system_power.kicad_sch

## KiCad design hardware/bridge/kicad/02_system_power.kicad_sch (2026-09-06)

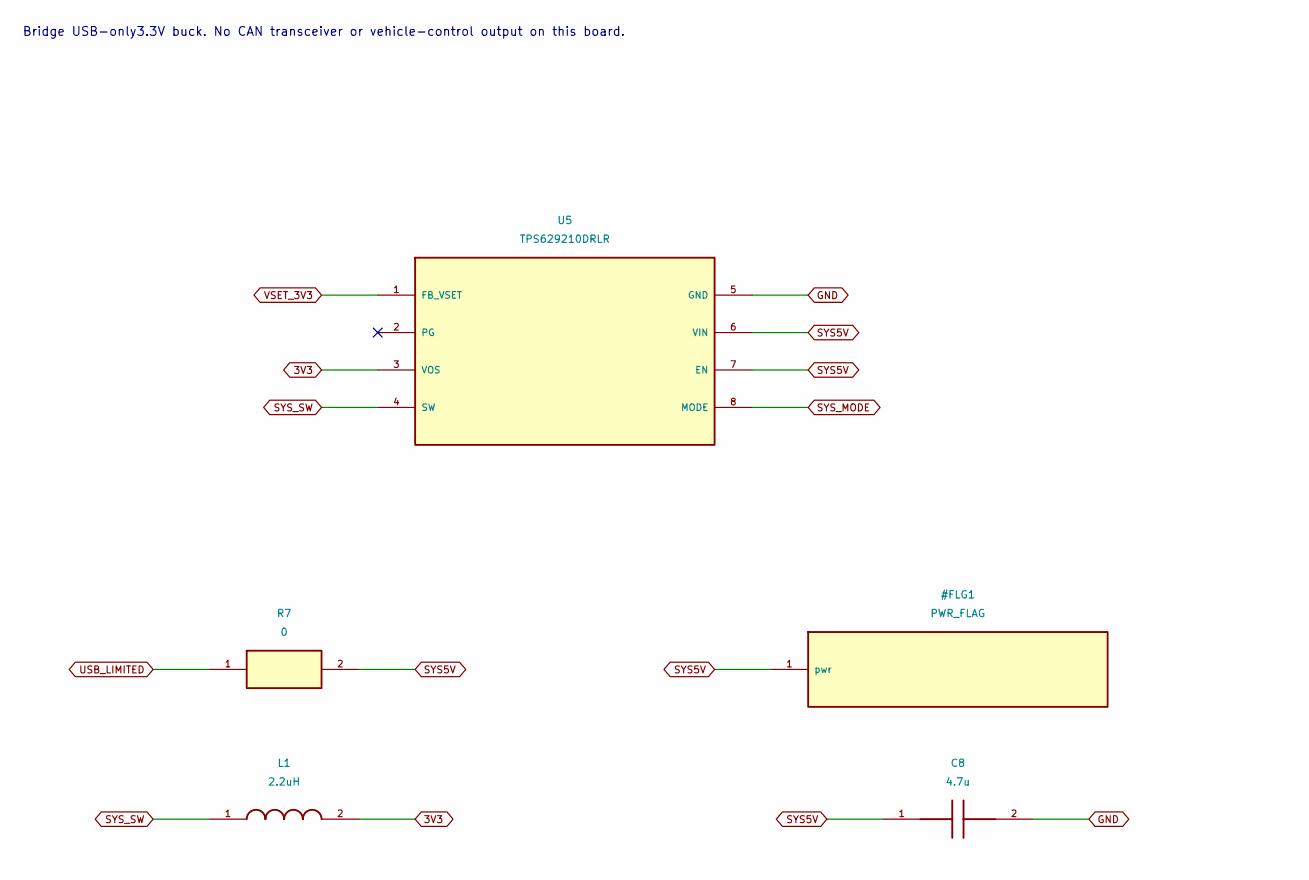
[picture p73: schematic 02_system_power.kicad_sch, part in row 1, column 1]

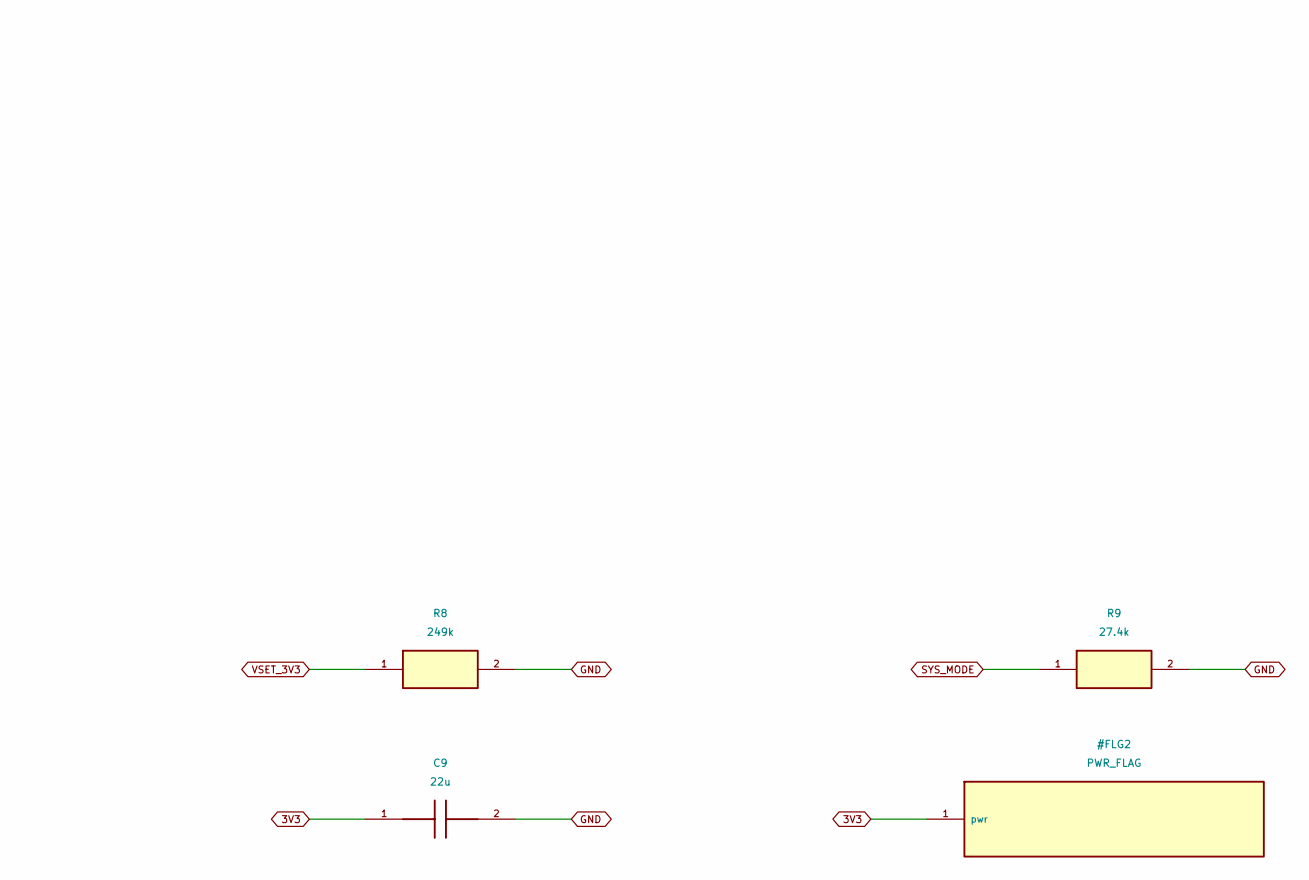
[picture p74: schematic 02_system_power.kicad_sch, part in row 1, column 2]

Parts:
C8: 4.7u; Capacitor_SMD__C_0603_1608Metric; MPN GEN-C-0603-4.7u-16V-X7R
C9: 22u; Capacitor_SMD__C_0805_2012Metric; MPN GEN-C-0805-22u-10V-X7R
L1: 2.2uH; Murata_DFE252012PD; MPN DFE252012PD-2R2M=P2
R7: 0; Resistor_SMD__R_0805_2012Metric; MPN GEN-R-0805-0-1%
R8: 249k; Resistor_SMD__R_0402_1005Metric; MPN GEN-R-0402-249k-1%
R9: 27.4k; Resistor_SMD__R_0402_1005Metric; MPN GEN-R-0402-27.4k-1%
U5: TPS629210DRLR; Package_TO_SOT_SMD__SOT-583-8; MPN TPS629210DRLR

Connections:
3V3: C9.1, L1.2, U5.3 (VOS)
GND: C8.2, C9.2, R8.2, R9.2, U5.5 (GND)
SYS5V: C8.1, R7.2, U5.6 (VIN), U5.7 (EN)
SYS_MODE: R9.1, U5.8 (MODE)
SYS_SW: L1.1, U5.4 (SW)
USB_LIMITED: R7.1
VSET_3V3: R8.1, U5.1 (FB_VSET)

Notes on the sheet:
Bridge USB-only3.3V buck. No CAN transceiver or vehicle-control output on this board.
