digitie/canview/hardware/bridge/kicad/03_reset.kicad_sch

## KiCad design hardware/bridge/kicad/03_reset.kicad_sch (2026-09-06)

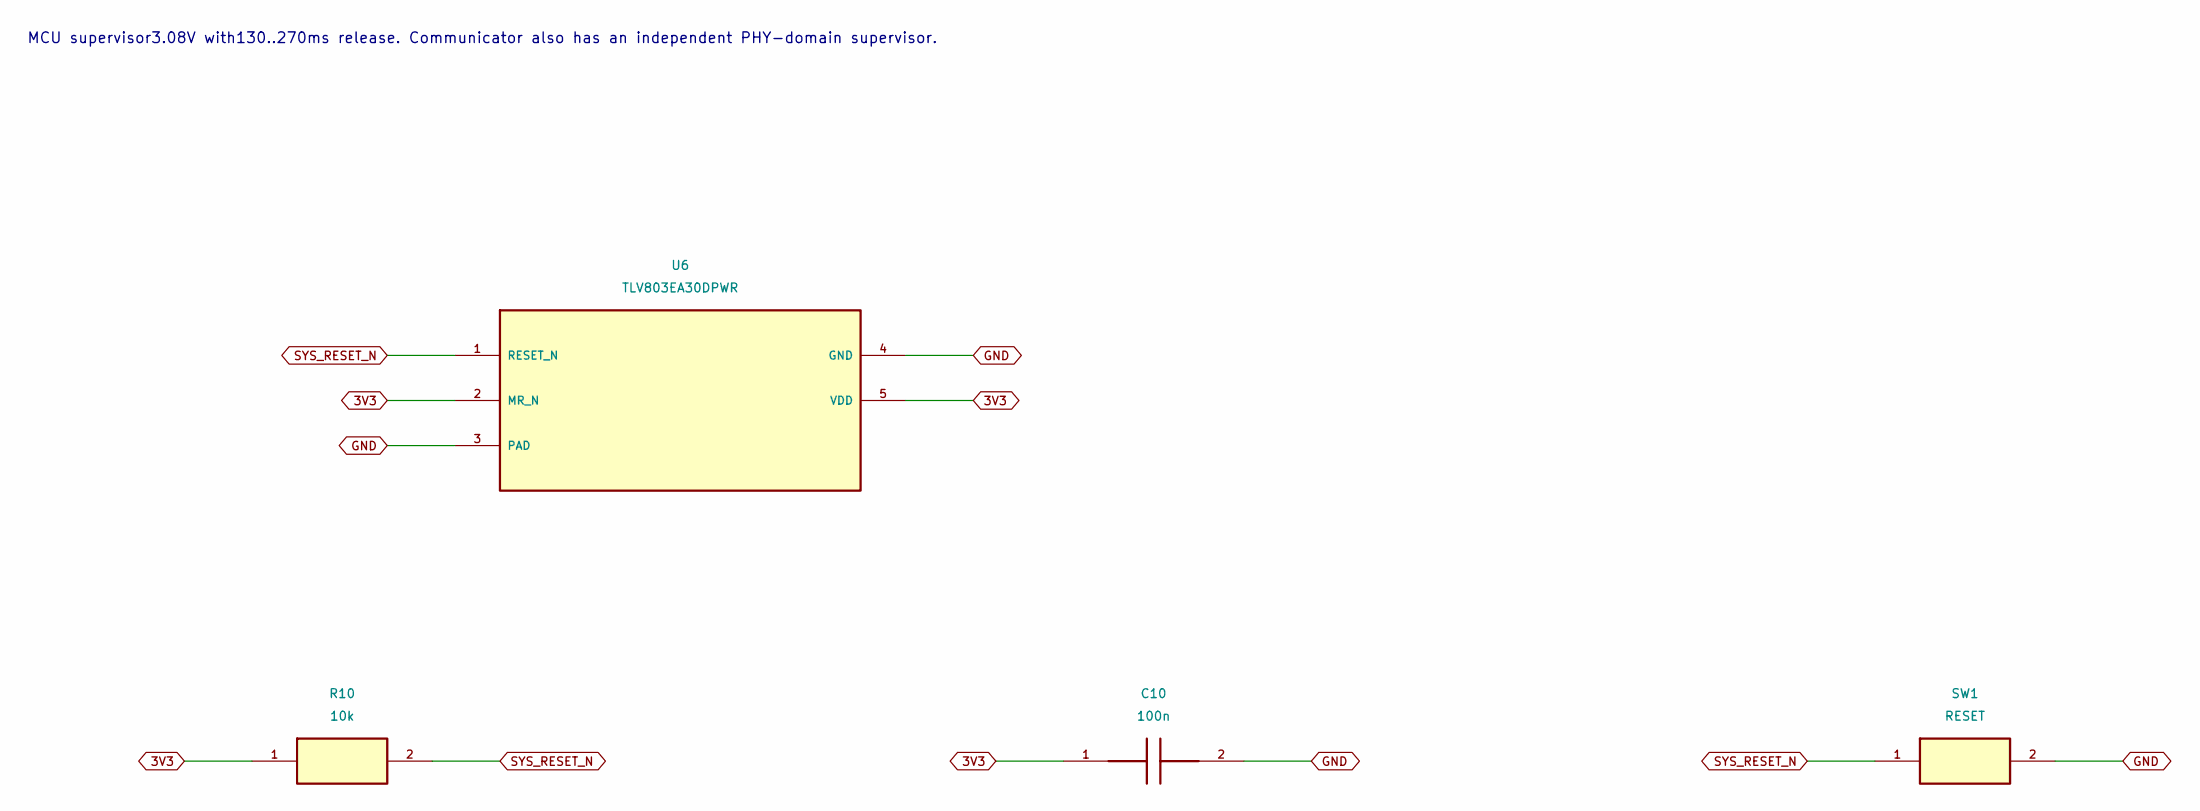
[picture p75: schematic 03_reset.kicad_sch]

Parts:
C10: 100n; Capacitor_SMD__C_0402_1005Metric; MPN GEN-C-0402-100n-16V-X7R
R10: 10k; Resistor_SMD__R_0402_1005Metric; MPN GEN-R-0402-10k-1%
SW1: RESET; Button_Switch_SMD__SW_SPST_TL3342; MPN TL3342F160QG
U6: TLV803EA30DPWR; Package_SON__Texas_X2SON-5_0.8x0.8mm_P0.48mm; MPN TLV803EA30DPWR

Connections:
3V3: C10.1, R10.1, U6.2 (MR_N), U6.5 (VDD)
GND: C10.2, SW1.2, U6.3 (PAD), U6.4 (GND)
SYS_RESET_N: R10.2, SW1.1, U6.1 (RESET_N)

Notes on the sheet:
MCU supervisor3.08V with130..270ms release. Communicator also has an independent PHY-domain supervisor.
