digitie/canview/hardware/bridge/kicad/03_service.kicad_sch

## KiCad design hardware/bridge/kicad/03_service.kicad_sch (2026-09-06)

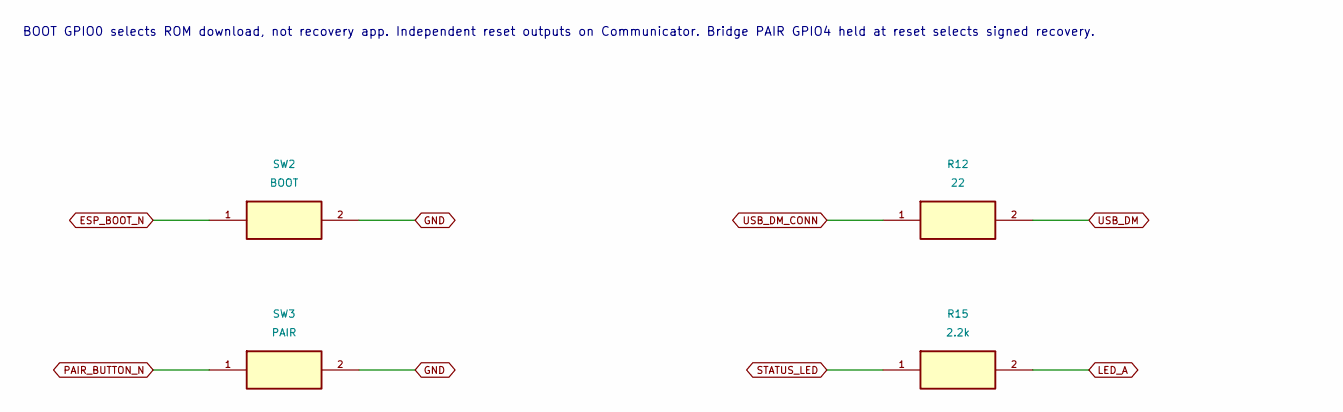
[picture p76: schematic 03_service.kicad_sch, part in row 1, column 1]

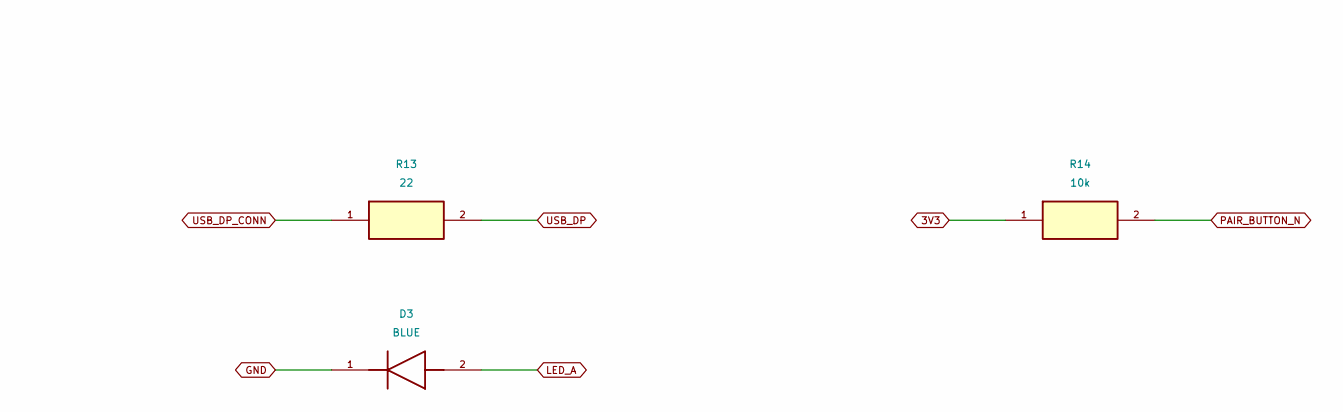
[picture p77: schematic 03_service.kicad_sch, part in row 1, column 2]

Parts:
D3: BLUE; LED_SMD__LED_0603_1608Metric; MPN GEN-LED-0603-BLUE
R12, R13: 22; Resistor_SMD__R_0402_1005Metric; MPN GEN-R-0402-22-1%
R14: 10k; Resistor_SMD__R_0402_1005Metric; MPN GEN-R-0402-10k-1%
R15: 2.2k; Resistor_SMD__R_0402_1005Metric; MPN GEN-R-0402-2.2k-1%
SW2: BOOT; Button_Switch_SMD__SW_SPST_TL3342; MPN TL3342F160QG
SW3: PAIR; Button_Switch_SMD__SW_SPST_TL3342; MPN TL3342F160QG

Connections:
3V3: R14.1
ESP_BOOT_N: SW2.1
GND: D3.1 (K), SW2.2, SW3.2
LED_A: D3.2 (A), R15.2
PAIR_BUTTON_N: R14.2, SW3.1
STATUS_LED: R15.1
USB_DM: R12.2
USB_DM_CONN: R12.1
USB_DP: R13.2
USB_DP_CONN: R13.1

Notes on the sheet:
BOOT GPIO0 selects ROM download, not recovery app. Independent reset outputs on Communicator. Bridge PAIR GPIO4 held at reset selects signed recovery.
