digitie/canview/hardware/communicator/kicad/00_vehicle_input.kicad_sch

## KiCad design hardware/communicator/kicad/00_vehicle_input.kicad_sch (2026-09-06)

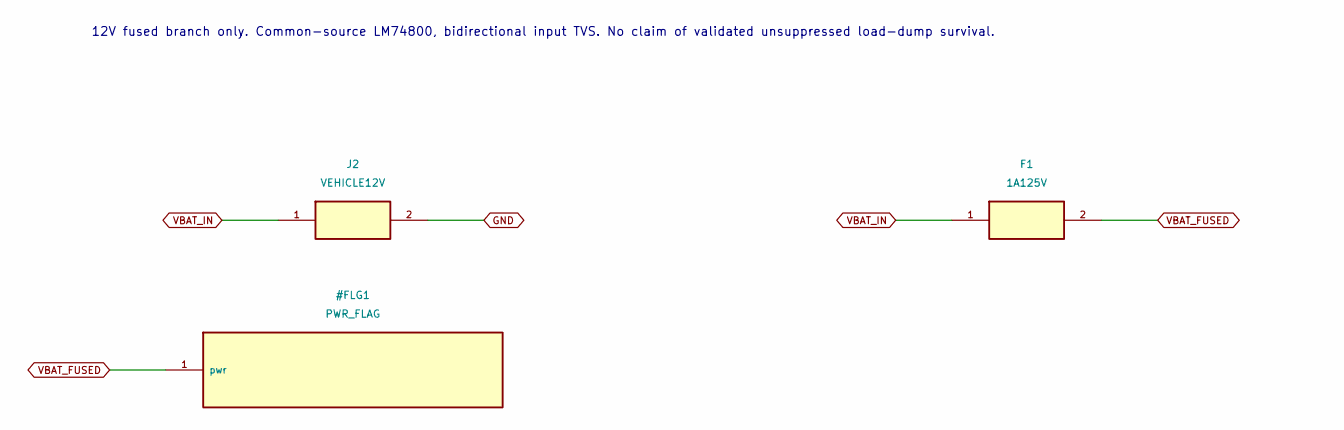
[picture p78: schematic 00_vehicle_input.kicad_sch, part in row 1, column 1]

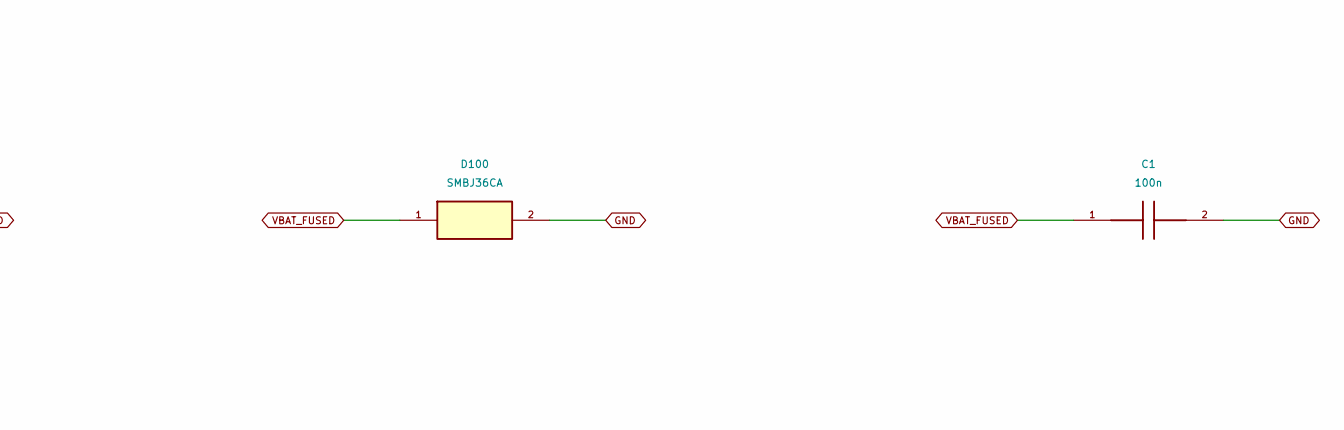
[picture p79: schematic 00_vehicle_input.kicad_sch, part in row 1, column 2]

Parts:
C1: 100n; Capacitor_SMD__C_0805_2012Metric; MPN GEN-C-0805-100n-100V-X7R
D100: SMBJ36CA; Diode_SMD__D_SMB; MPN SMBJ36CA
F1: 1A125V; Fuse__Fuse_Littelfuse-NANO2-451_453; MPN 0451001.MRL
J2: VEHICLE12V; Connector_JST__JST_XH_B2B-XH-A_1x02_P2.50mm_Vertical; MPN B2B-XH-A(LF)(SN)

Connections:
GND: C1.2, D100.2 (IO2), J2.2 (GND)
VBAT_FUSED: C1.1, D100.1 (IO1), F1.2
VBAT_IN: F1.1, J2.1 (VBAT)

Notes on the sheet:
12V fused branch only. Common-source LM74800, bidirectional input TVS. No claim of validated unsuppressed load-dump survival.
