digitie/canview/hardware/communicator/kicad/00b_reverse_ov.kicad_sch

## KiCad design hardware/communicator/kicad/00b_reverse_ov.kicad_sch (2026-09-06)

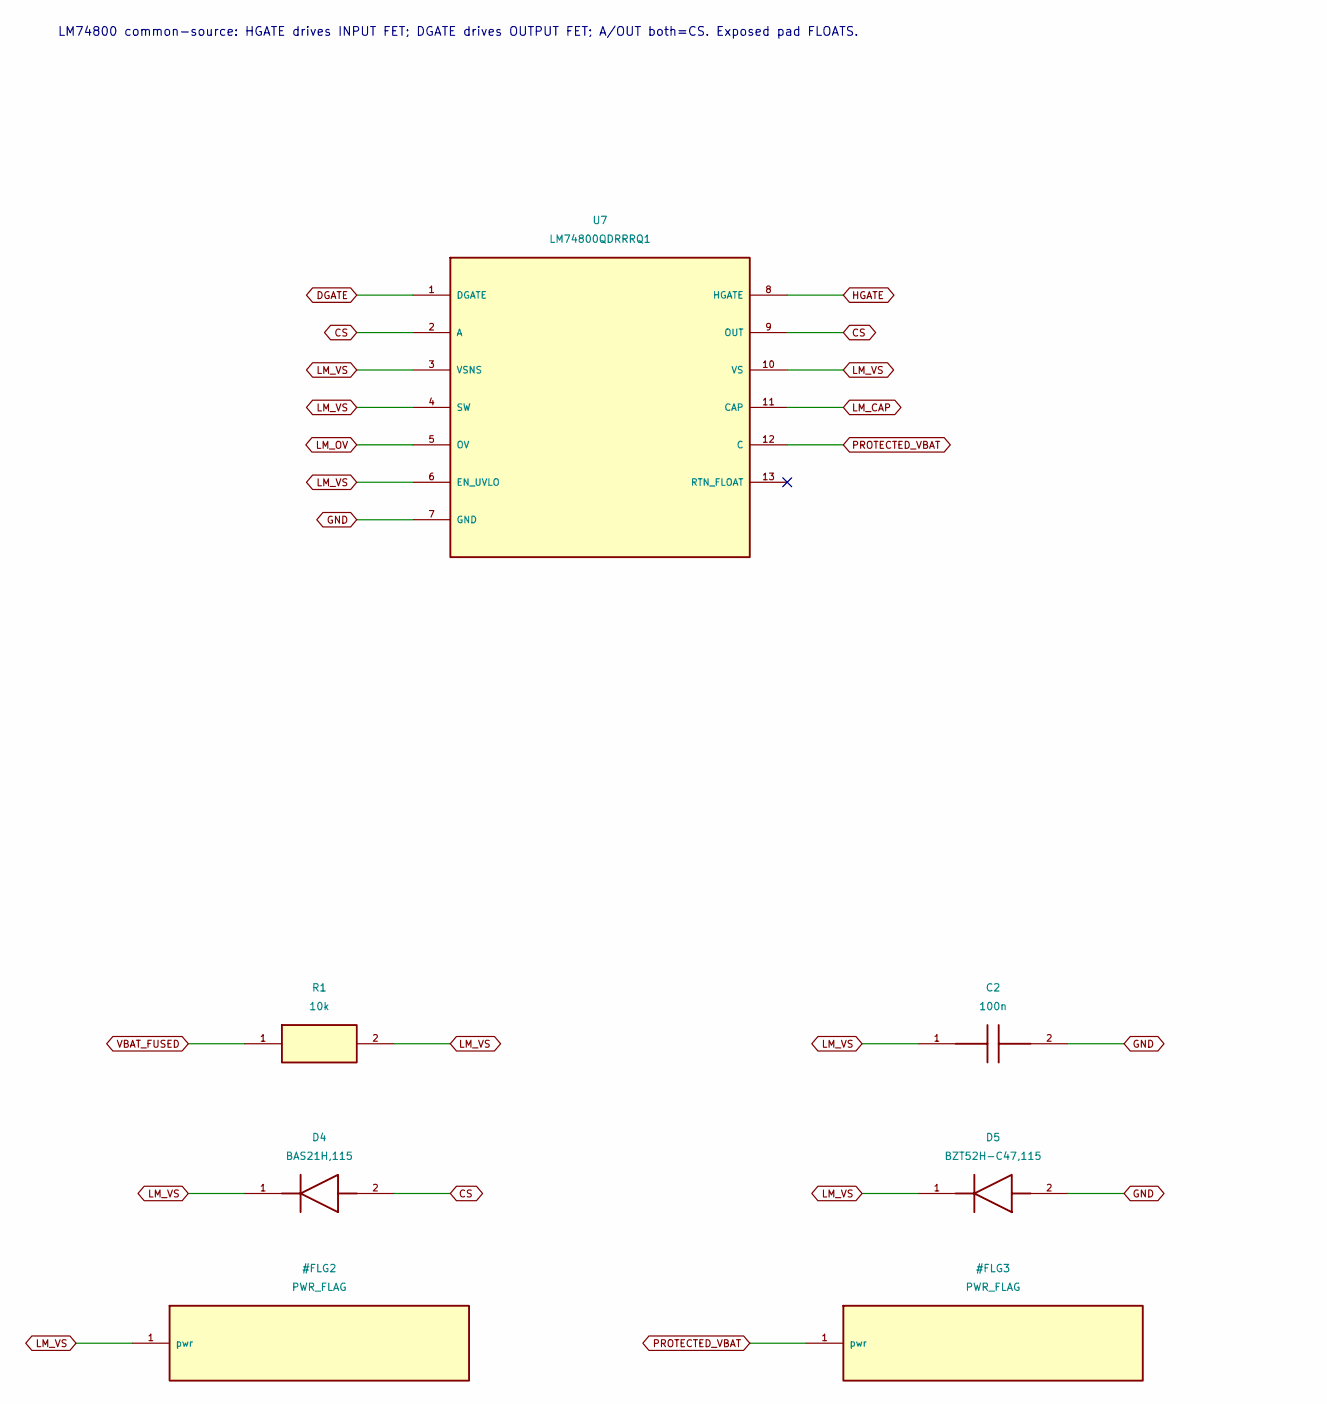
[picture p80: schematic 00b_reverse_ov.kicad_sch, part in row 1, column 1]

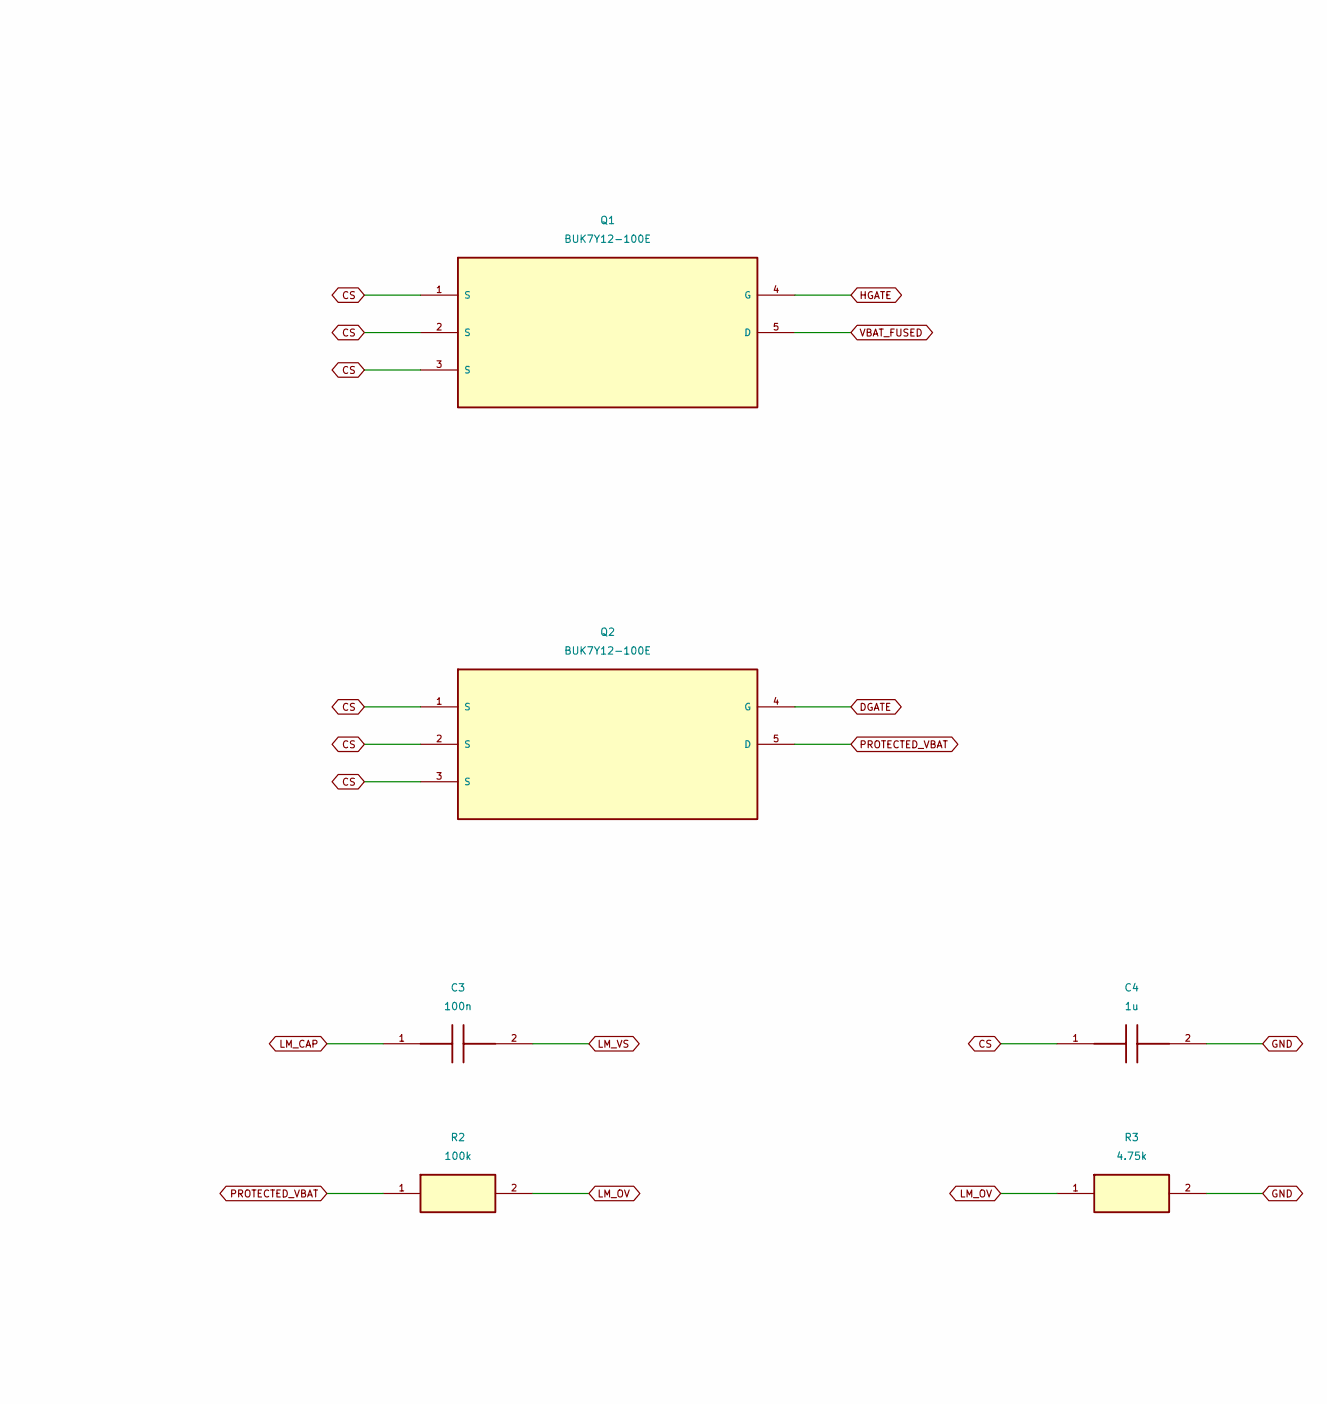
[picture p81: schematic 00b_reverse_ov.kicad_sch, part in row 1, column 2]

Parts:
C2: 100n; Capacitor_SMD__C_0805_2012Metric; MPN GEN-C-0805-100n-100V-X7R
C3: 100n; Capacitor_SMD__C_0402_1005Metric; MPN GEN-C-0402-100n-25V-X7R
C4: 1u; Capacitor_SMD__C_1206_3216Metric; MPN GEN-C-1206-1u-100V-X7R
D4: BAS21H,115; Diode_SMD__D_SOD-123F; MPN BAS21H,115
D5: BZT52H-C47,115; Diode_SMD__D_SOD-123F; MPN BZT52H-C47,115
Q1, Q2: BUK7Y12-100E; Package_TO_SOT_SMD__LFPAK56; MPN BUK7Y12-100E
R1: 10k; Resistor_SMD__R_0805_2012Metric; MPN GEN-R-0805-10k-1%
R2: 100k; Resistor_SMD__R_0603_1608Metric; MPN GEN-R-0603-100k-0.1%
R3: 4.75k; Resistor_SMD__R_0603_1608Metric; MPN GEN-R-0603-4.75k-0.1%
U7: LM74800QDRRRQ1; Package_SON__WSON-12-1EP_3x3mm_P0.5mm_EP1.5x2.5mm; MPN LM74800QDRRRQ1

Connections:
CS: C4.1, D4.2 (A), Q1.1 (S), Q1.2 (S), Q1.3 (S), Q2.1 (S), Q2.2 (S), Q2.3 (S), U7.2 (A), U7.9 (OUT)
DGATE: Q2.4 (G), U7.1 (DGATE)
GND: C2.2, C4.2, D5.2 (A), R3.2, U7.7 (GND)
HGATE: Q1.4 (G), U7.8 (HGATE)
LM_CAP: C3.1, U7.11 (CAP)
LM_OV: R2.2, R3.1, U7.5 (OV)
LM_VS: C2.1, C3.2, D4.1 (K), D5.1 (K), R1.2, U7.3 (VSNS), U7.4 (SW), U7.6 (EN_UVLO), U7.10 (VS)
PROTECTED_VBAT: Q2.5 (D), R2.1, U7.12 (C)
VBAT_FUSED: Q1.5 (D), R1.1

Notes on the sheet:
LM74800 common-source: HGATE drives INPUT FET; DGATE drives OUTPUT FET; A/OUT both=CS. Exposed pad FLOATS.
