digitie/canview/hardware/communicator/kicad/00c_auto_5v.kicad_sch

## KiCad design hardware/communicator/kicad/00c_auto_5v.kicad_sch (2026-09-06)

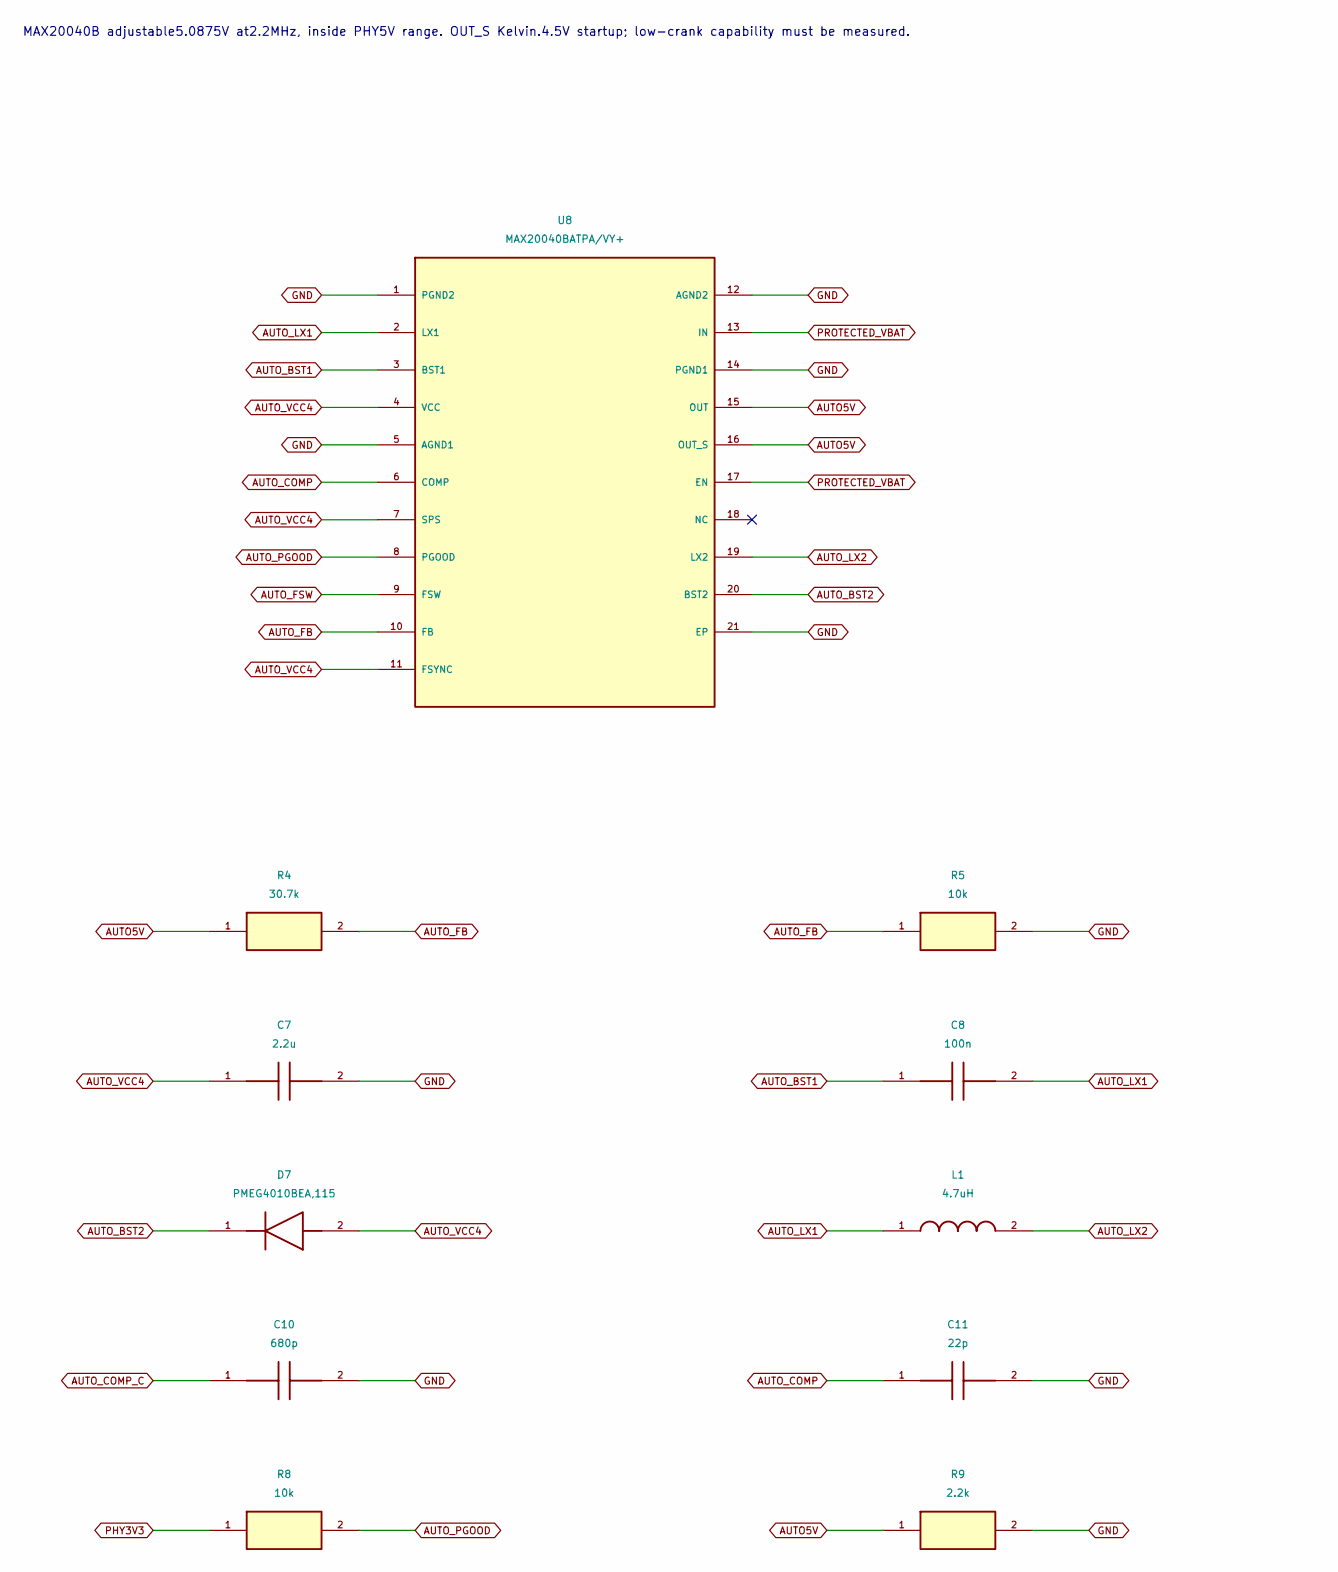
[picture p82: schematic 00c_auto_5v.kicad_sch, part in row 1, column 1]

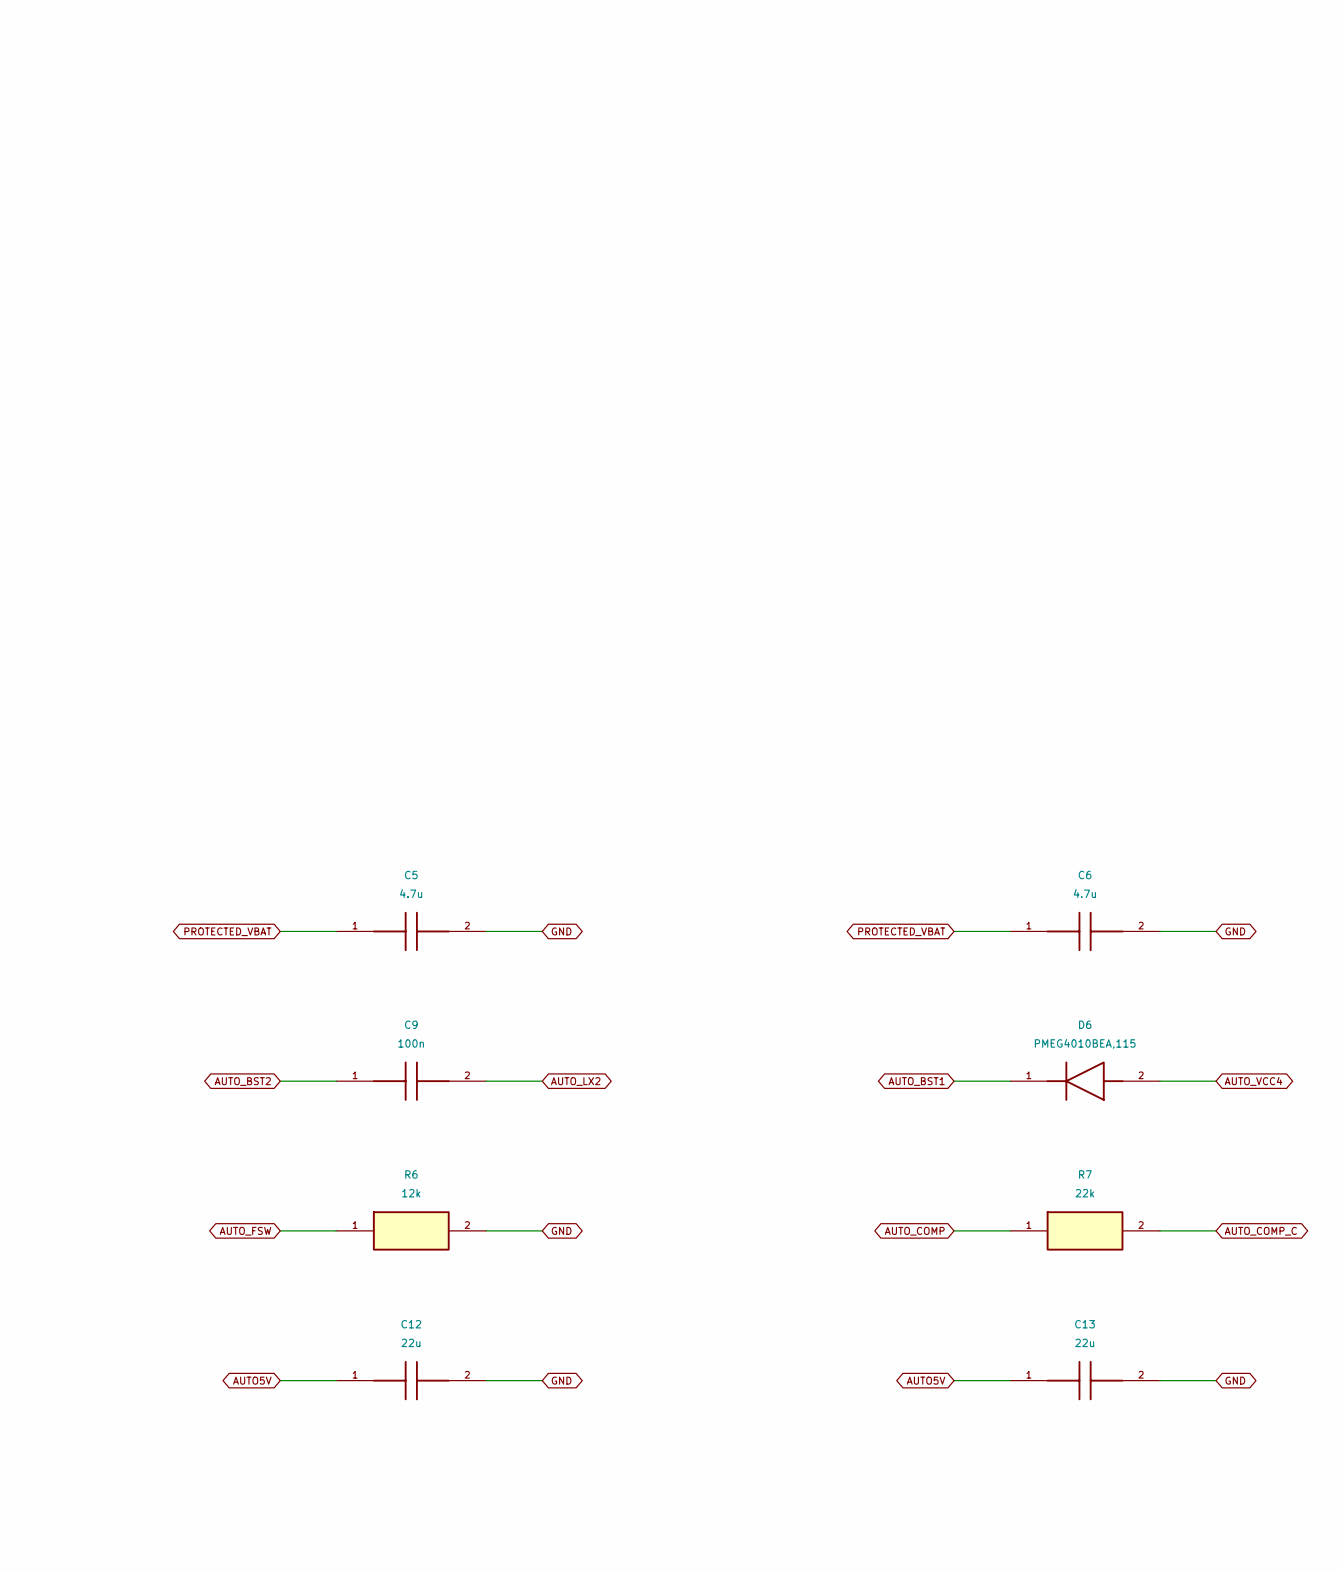
[picture p83: schematic 00c_auto_5v.kicad_sch, part in row 1, column 2]

Parts:
C5, C6: 4.7u; Capacitor_SMD__C_1210_3225Metric; MPN GRM32ER71H475KA88L
C7: 2.2u; Capacitor_SMD__C_0603_1608Metric; MPN GRM188R61C225KE15D
C8, C9: 100n; Capacitor_SMD__C_0402_1005Metric; MPN GRM155R71H104KE14D
C10: 680p; Capacitor_SMD__C_0402_1005Metric; MPN GEN-C-0402-680p-16V-C0G
C11: 22p; Capacitor_SMD__C_0402_1005Metric; MPN GEN-C-0402-22p-16V-C0G
C12, C13: 22u; Capacitor_SMD__C_1210_3225Metric; MPN GRM32ER71E226KE15L
D6, D7: PMEG4010BEA,115; Diode_SMD__D_SOD-323; MPN PMEG4010BEA,115
L1: 4.7uH; Inductor_SMD__L_Coilcraft_XAL5030-XXX; MPN XAL5030-472MEC
R4: 30.7k; Resistor_SMD__R_0603_1608Metric; MPN GEN-R-0603-30.7k-0.1%
R5: 10k; Resistor_SMD__R_0603_1608Metric; MPN GEN-R-0603-10k-0.1%
R6: 12k; Resistor_SMD__R_0402_1005Metric; MPN GEN-R-0402-12k-1%
R7: 22k; Resistor_SMD__R_0402_1005Metric; MPN GEN-R-0402-22k-1%
R8: 10k; Resistor_SMD__R_0402_1005Metric; MPN GEN-R-0402-10k-1%
R9: 2.2k; Resistor_SMD__R_0402_1005Metric; MPN GEN-R-0402-2.2k-1%
U8: MAX20040BATPA/VY+; Package_DFN_QFN__TQFN-20-1EP_4x4mm_P0.5mm_EP2.9x2.9mm; MPN MAX20040BATPA/VY+

Connections:
AUTO5V: C12.1, C13.1, R4.1, R9.1, U8.15 (OUT), U8.16 (OUT_S)
AUTO_BST1: C8.1, D6.1 (K), U8.3 (BST1)
AUTO_BST2: C9.1, D7.1 (K), U8.20 (BST2)
AUTO_COMP: C11.1, R7.1, U8.6 (COMP)
AUTO_COMP_C: C10.1, R7.2
AUTO_FB: R4.2, R5.1, U8.10 (FB)
AUTO_FSW: R6.1, U8.9 (FSW)
AUTO_LX1: C8.2, L1.1, U8.2 (LX1)
AUTO_LX2: C9.2, L1.2, U8.19 (LX2)
AUTO_PGOOD: R8.2, U8.8 (PGOOD)
AUTO_VCC4: C7.1, D6.2 (A), D7.2 (A), U8.4 (VCC), U8.7 (SPS), U8.11 (FSYNC)
GND: C5.2, C6.2, C7.2, C10.2, C11.2, C12.2, C13.2, R5.2, R6.2, R9.2, U8.1 (PGND2), U8.5 (AGND1), U8.12 (AGND2), U8.14 (PGND1), U8.21 (EP)
PHY3V3: R8.1
PROTECTED_VBAT: C5.1, C6.1, U8.13 (IN), U8.17 (EN)

Notes on the sheet:
MAX20040B adjustable5.0875V at2.2MHz, inside PHY5V range. OUT_S Kelvin.4.5V startup; low-crank capability must be measured.
