digitie/canview/hardware/communicator/kicad/01b_usb_limit.kicad_sch

## KiCad design hardware/communicator/kicad/01b_usb_limit.kicad_sch (2026-09-06)

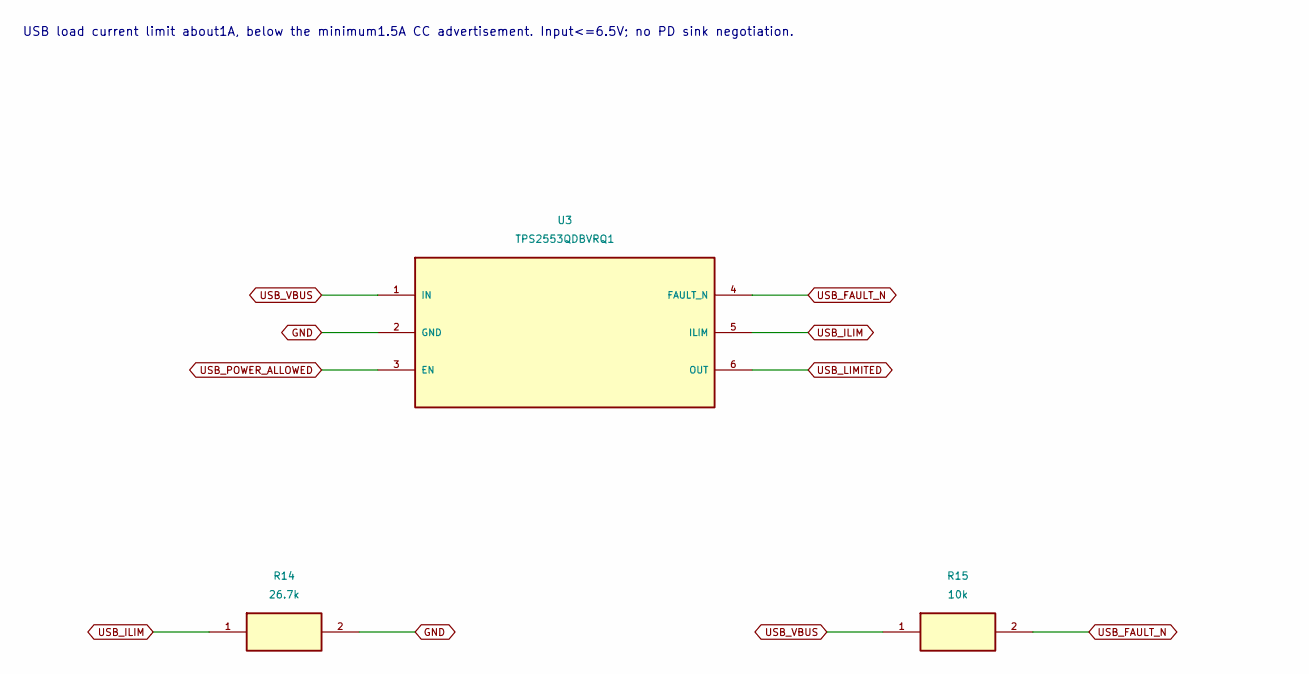
[picture p87: schematic 01b_usb_limit.kicad_sch, part in row 1, column 1]

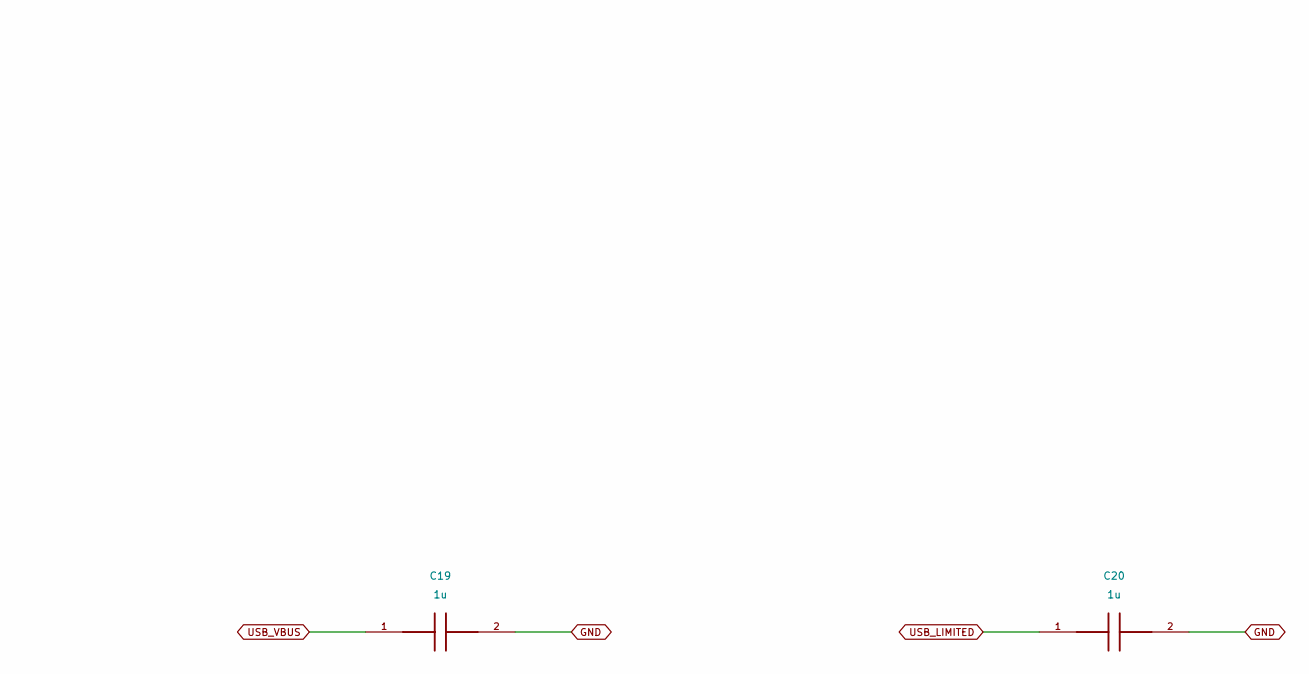
[picture p88: schematic 01b_usb_limit.kicad_sch, part in row 1, column 2]

Parts:
C19, C20: 1u; Capacitor_SMD__C_0603_1608Metric; MPN GEN-C-0603-1u-16V-X7R
R14: 26.7k; Resistor_SMD__R_0402_1005Metric; MPN GEN-R-0402-26.7k-1%
R15: 10k; Resistor_SMD__R_0402_1005Metric; MPN GEN-R-0402-10k-1%
U3: TPS2553QDBVRQ1; Package_TO_SOT_SMD__SOT-23-6; MPN TPS2553QDBVRQ1

Connections:
GND: C19.2, C20.2, R14.2, U3.2 (GND)
USB_FAULT_N: R15.2, U3.4 (FAULT_N)
USB_ILIM: R14.1, U3.5 (ILIM)
USB_LIMITED: C20.1, U3.6 (OUT)
USB_POWER_ALLOWED: U3.3 (EN)
USB_VBUS: C19.1, R15.1, U3.1 (IN)

Notes on the sheet:
USB load current limit about1A, below the minimum1.5A CC advertisement. Input<=6.5V; no PD sink negotiation.
