digitie/canview/hardware/communicator/kicad/02_system_power.kicad_sch

## KiCad design hardware/communicator/kicad/02_system_power.kicad_sch (2026-09-06)

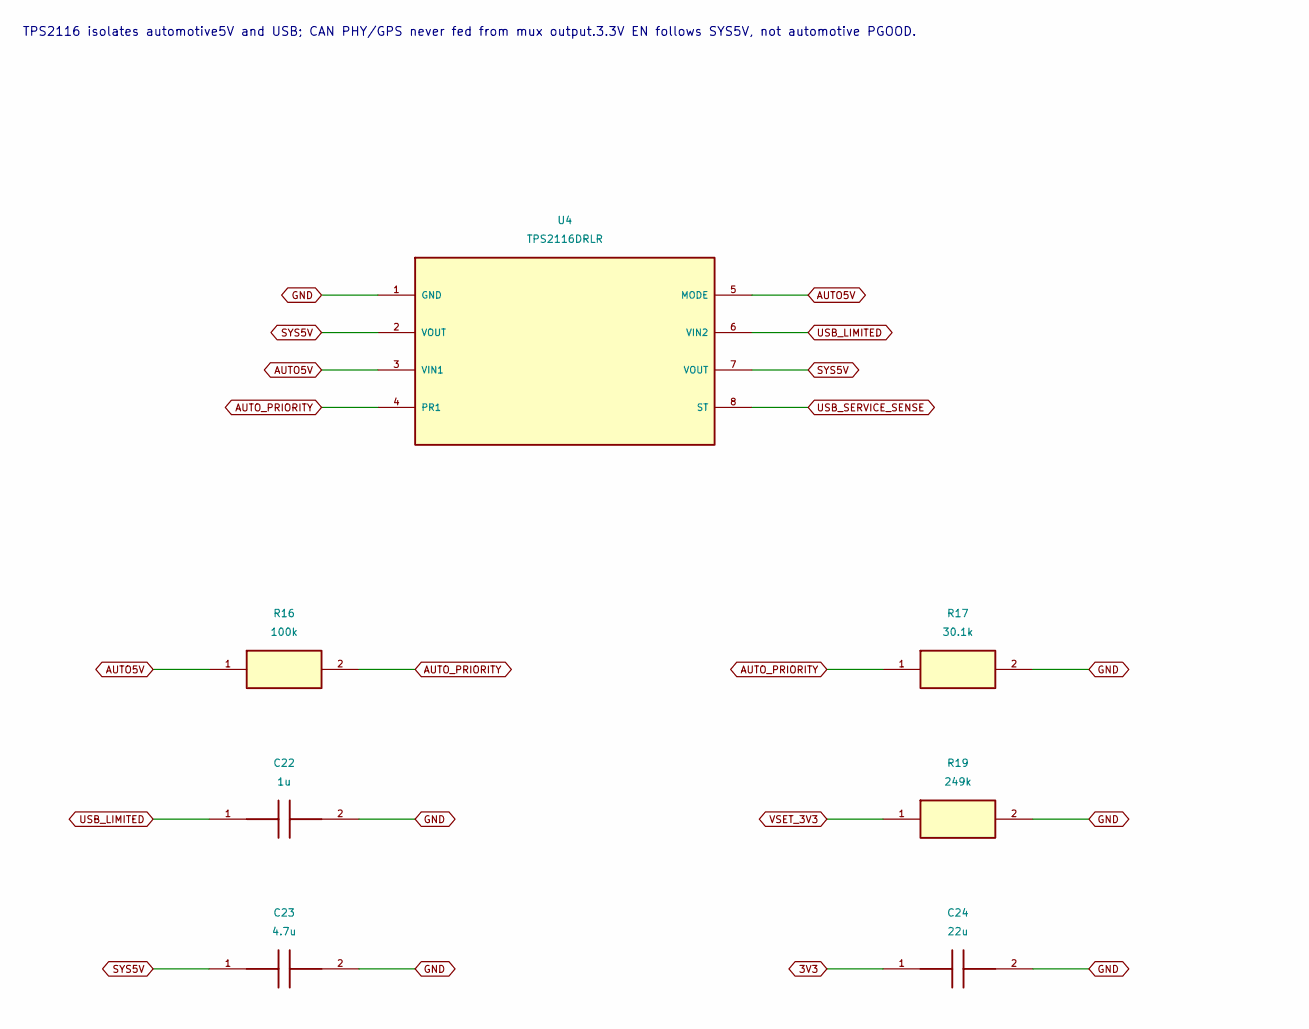
[picture p89: schematic 02_system_power.kicad_sch, part in row 1, column 1]

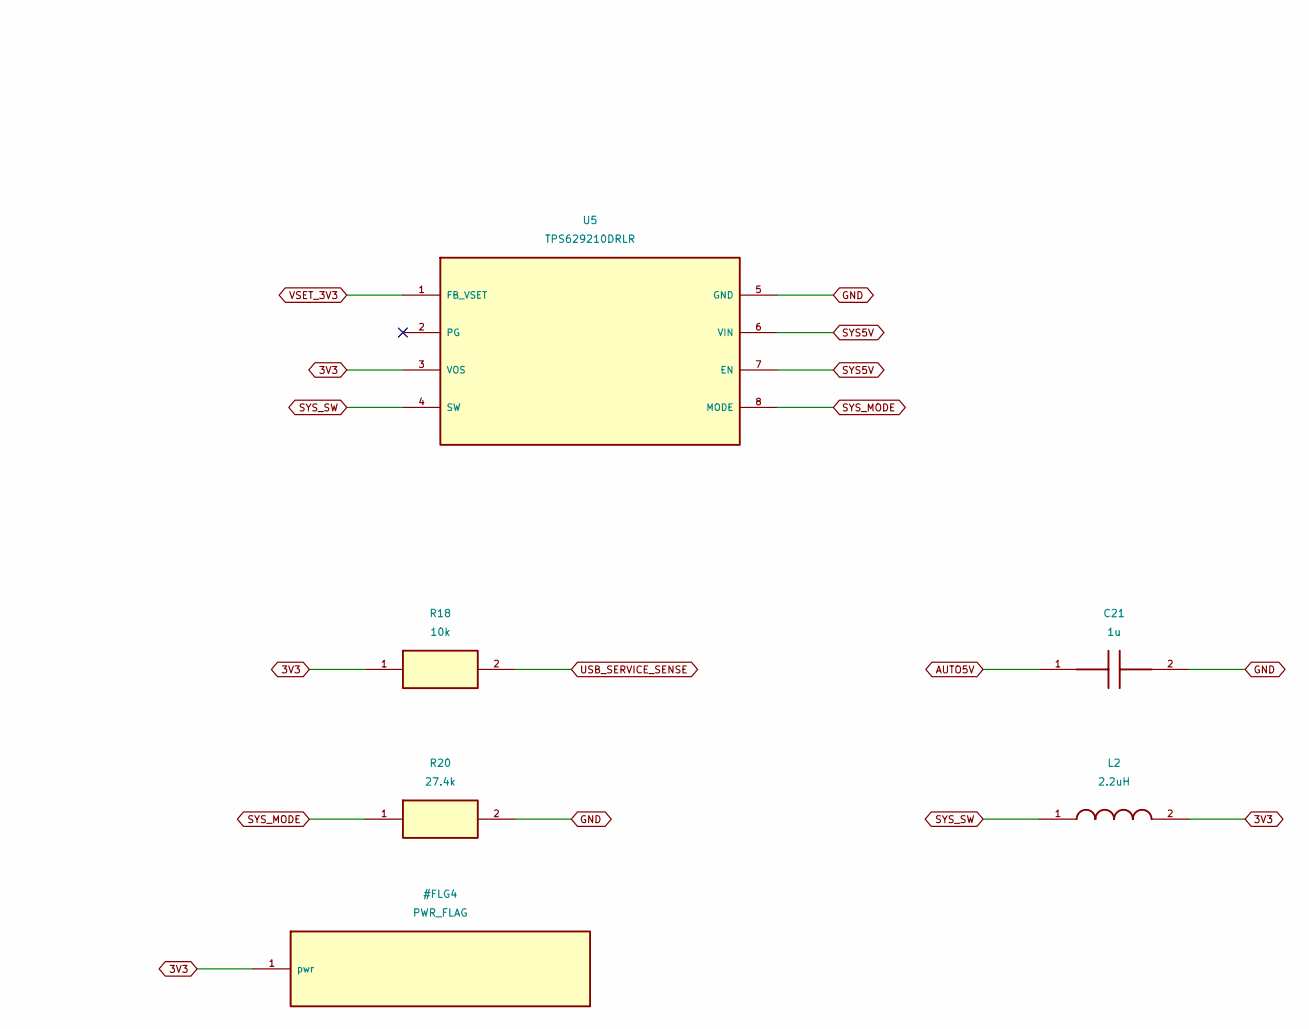
[picture p90: schematic 02_system_power.kicad_sch, part in row 1, column 2]

Parts:
C21, C22: 1u; Capacitor_SMD__C_0603_1608Metric; MPN GEN-C-0603-1u-16V-X7R
C23: 4.7u; Capacitor_SMD__C_0603_1608Metric; MPN GEN-C-0603-4.7u-16V-X7R
C24: 22u; Capacitor_SMD__C_0805_2012Metric; MPN GEN-C-0805-22u-10V-X7R
L2: 2.2uH; Murata_DFE252012PD; MPN DFE252012PD-2R2M=P2
R16: 100k; Resistor_SMD__R_0402_1005Metric; MPN GEN-R-0402-100k-1%
R17: 30.1k; Resistor_SMD__R_0402_1005Metric; MPN GEN-R-0402-30.1k-1%
R18: 10k; Resistor_SMD__R_0402_1005Metric; MPN GEN-R-0402-10k-1%
R19: 249k; Resistor_SMD__R_0402_1005Metric; MPN GEN-R-0402-249k-1%
R20: 27.4k; Resistor_SMD__R_0402_1005Metric; MPN GEN-R-0402-27.4k-1%
U4: TPS2116DRLR; Package_TO_SOT_SMD__SOT-583-8; MPN TPS2116DRLR
U5: TPS629210DRLR; Package_TO_SOT_SMD__SOT-583-8; MPN TPS629210DRLR

Connections:
3V3: C24.1, L2.2, R18.1, U5.3 (VOS)
AUTO5V: C21.1, R16.1, U4.3 (VIN1), U4.5 (MODE)
AUTO_PRIORITY: R16.2, R17.1, U4.4 (PR1)
GND: C21.2, C22.2, C23.2, C24.2, R17.2, R19.2, R20.2, U4.1 (GND), U5.5 (GND)
SYS5V: C23.1, U4.2 (VOUT), U4.7 (VOUT), U5.6 (VIN), U5.7 (EN)
SYS_MODE: R20.1, U5.8 (MODE)
SYS_SW: L2.1, U5.4 (SW)
USB_LIMITED: C22.1, U4.6 (VIN2)
USB_SERVICE_SENSE: R18.2, U4.8 (ST)
VSET_3V3: R19.1, U5.1 (FB_VSET)

Notes on the sheet:
TPS2116 isolates automotive5V and USB; CAN PHY/GPS never fed from mux output.3.3V EN follows SYS5V, not automotive PGOOD.
