digitie/canview/hardware/communicator/kicad/03b_phy_power.kicad_sch

## KiCad design hardware/communicator/kicad/03b_phy_power.kicad_sch (2026-09-06)

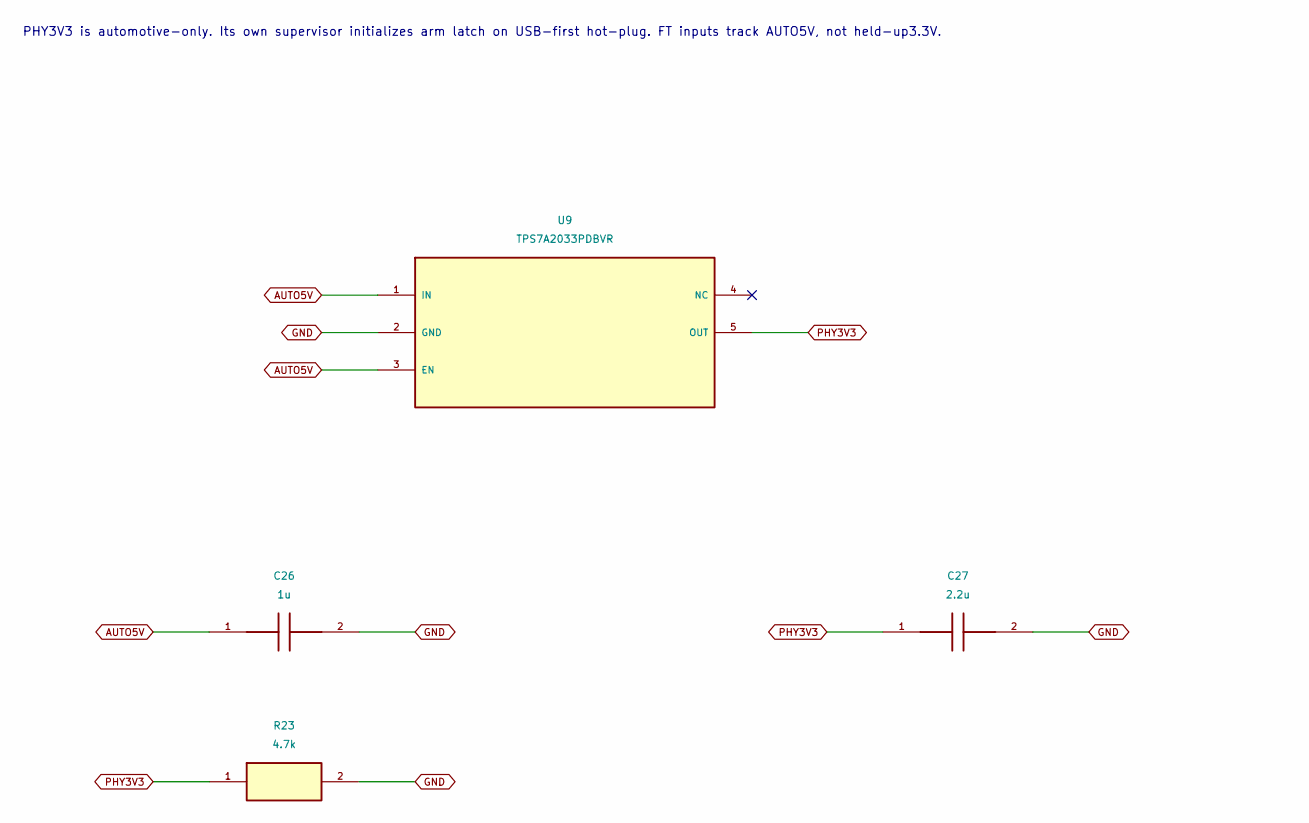
[picture p92: schematic 03b_phy_power.kicad_sch, part in row 1, column 1]

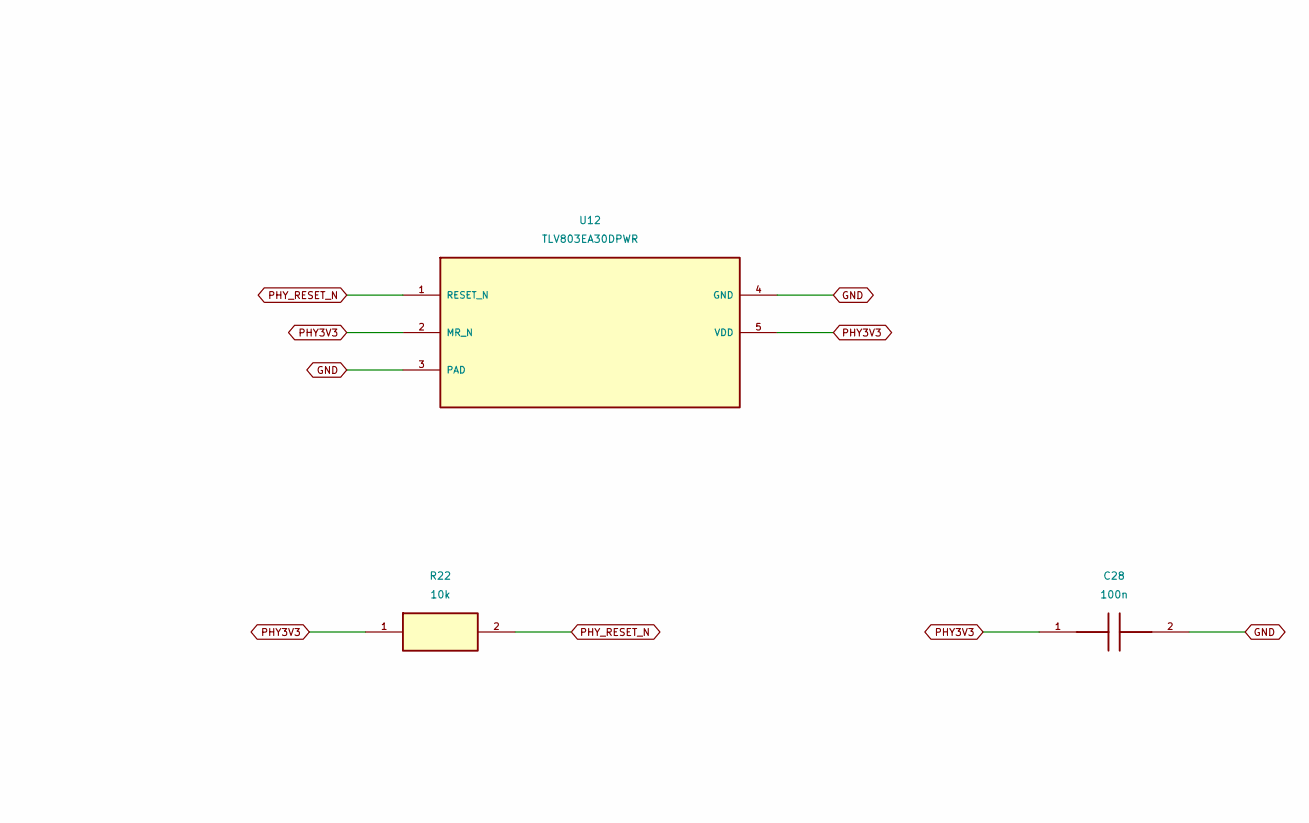
[picture p93: schematic 03b_phy_power.kicad_sch, part in row 1, column 2]

Parts:
C26: 1u; Capacitor_SMD__C_0603_1608Metric; MPN GEN-C-0603-1u-16V-X7R
C27: 2.2u; Capacitor_SMD__C_0603_1608Metric; MPN GEN-C-0603-2.2u-16V-X7R
C28: 100n; Capacitor_SMD__C_0402_1005Metric; MPN GEN-C-0402-100n-16V-X7R
R22: 10k; Resistor_SMD__R_0402_1005Metric; MPN GEN-R-0402-10k-1%
R23: 4.7k; Resistor_SMD__R_0402_1005Metric; MPN GEN-R-0402-4.7k-1%
U9: TPS7A2033PDBVR; Package_TO_SOT_SMD__SOT-23-5; MPN TPS7A2033PDBVR
U12: TLV803EA30DPWR; Package_SON__Texas_X2SON-5_0.8x0.8mm_P0.48mm; MPN TLV803EA30DPWR

Connections:
AUTO5V: C26.1, U9.1 (IN), U9.3 (EN)
GND: C26.2, C27.2, C28.2, R23.2, U9.2 (GND), U12.3 (PAD), U12.4 (GND)
PHY3V3: C27.1, C28.1, R22.1, R23.1, U9.5 (OUT), U12.2 (MR_N), U12.5 (VDD)
PHY_RESET_N: R22.2, U12.1 (RESET_N)

Notes on the sheet:
PHY3V3 is automotive-only. Its own supervisor initializes arm latch on USB-first hot-plug. FT inputs track AUTO5V, not held-up3.3V.
