digitie/canview/hardware/communicator/kicad/03c_auto_qualification.kicad_sch

## KiCad design hardware/communicator/kicad/03c_auto_qualification.kicad_sch (2026-09-06)

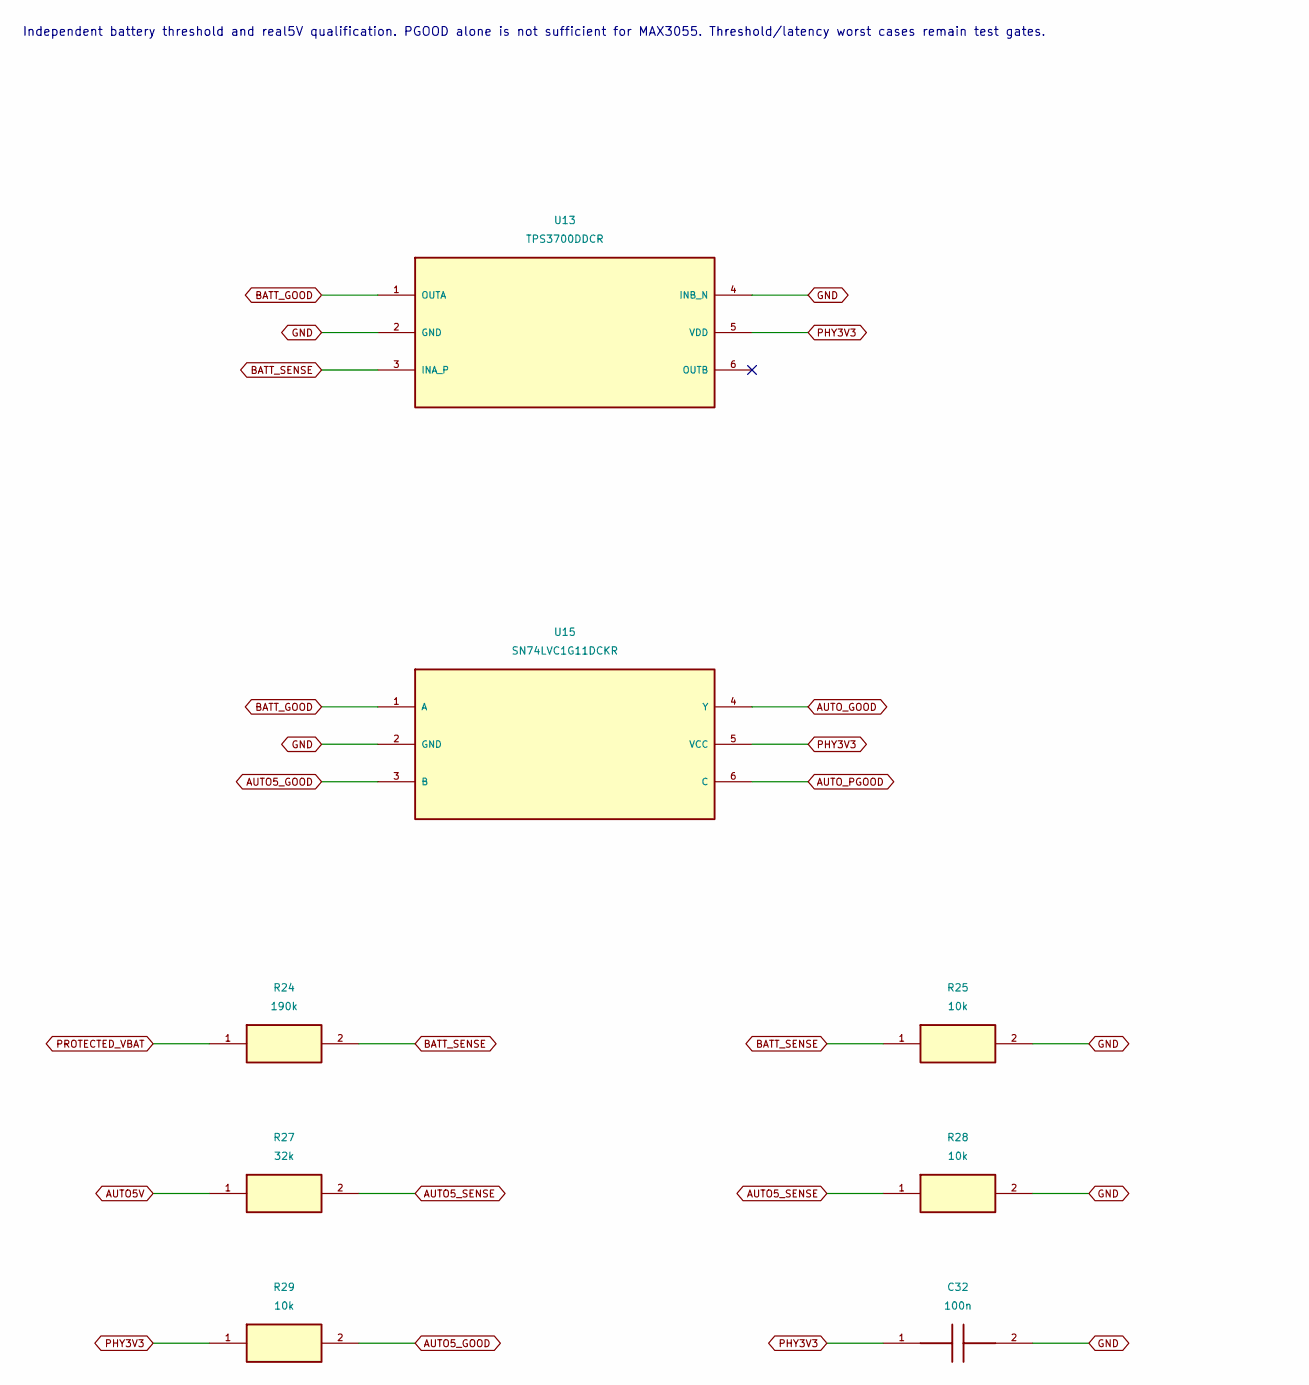
[picture p94: schematic 03c_auto_qualification.kicad_sch, part in row 1, column 1]

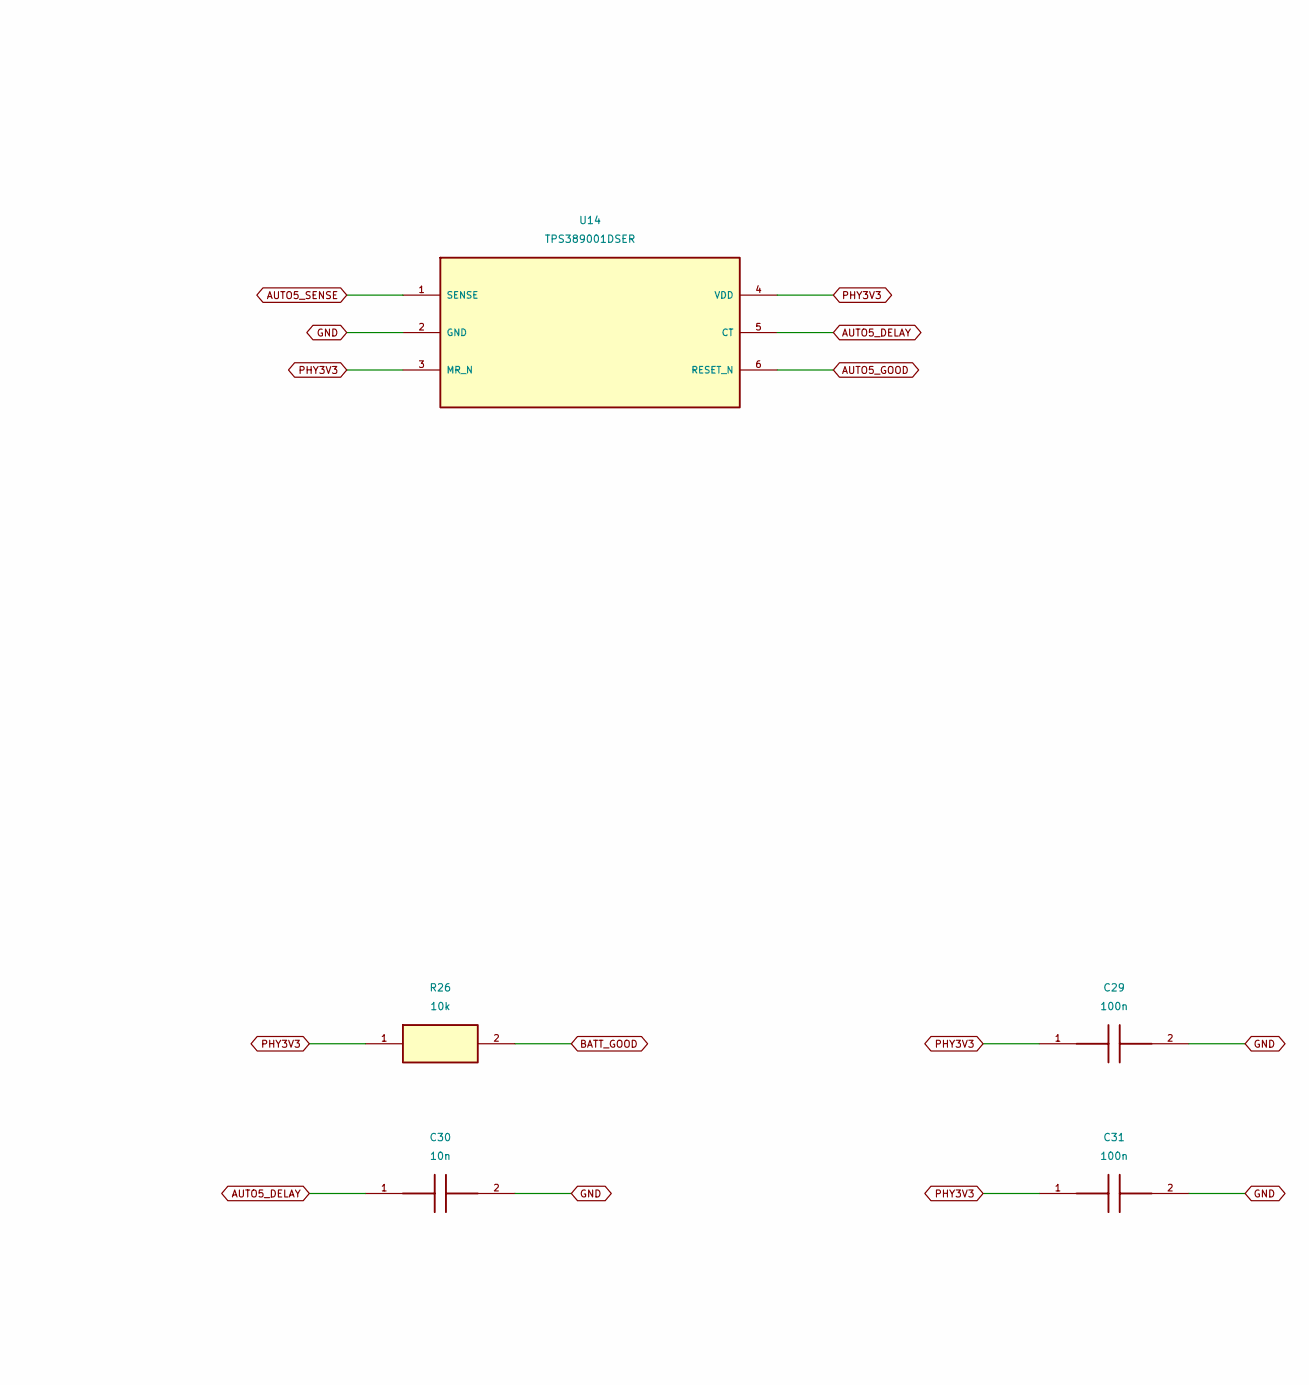
[picture p95: schematic 03c_auto_qualification.kicad_sch, part in row 1, column 2]

Parts:
C29, C31, C32: 100n; Capacitor_SMD__C_0402_1005Metric; MPN GEN-C-0402-100n-16V-X7R
C30: 10n; Capacitor_SMD__C_0603_1608Metric; MPN GEN-C-0603-10n-16V-C0G
R24: 190k; Resistor_SMD__R_0603_1608Metric; MPN GEN-R-0603-190k-0.1%
R25: 10k; Resistor_SMD__R_0402_1005Metric; MPN GEN-R-0402-10k-0.1%
R26, R29: 10k; Resistor_SMD__R_0402_1005Metric; MPN GEN-R-0402-10k-1%
R27: 32k; Resistor_SMD__R_0603_1608Metric; MPN GEN-R-0603-32k-0.05%
R28: 10k; Resistor_SMD__R_0603_1608Metric; MPN GEN-R-0603-10k-0.05%
U13: TPS3700DDCR; Package_TO_SOT_SMD__SOT-23-6; MPN TPS3700DDCR
U14: TPS389001DSER; Package_SON__WSON-6_1.5x1.5mm_P0.5mm; MPN TPS389001DSER
U15: SN74LVC1G11DCKR; Package_TO_SOT_SMD__SOT-363_SC-70-6; MPN SN74LVC1G11DCKR

Connections:
AUTO5V: R27.1
AUTO5_DELAY: C30.1, U14.5 (CT)
AUTO5_GOOD: R29.2, U14.6 (RESET_N), U15.3 (B)
AUTO5_SENSE: R27.2, R28.1, U14.1 (SENSE)
AUTO_GOOD: U15.4 (Y)
AUTO_PGOOD: U15.6 (C)
BATT_GOOD: R26.2, U13.1 (OUTA), U15.1 (A)
BATT_SENSE: R24.2, R25.1, U13.3 (INA_P)
GND: C29.2, C30.2, C31.2, C32.2, R25.2, R28.2, U13.2 (GND), U13.4 (INB_N), U14.2 (GND), U15.2 (GND)
PHY3V3: C29.1, C31.1, C32.1, R26.1, R29.1, U13.5 (VDD), U14.3 (MR_N), U14.4 (VDD), U15.5 (VCC)
PROTECTED_VBAT: R24.1

Notes on the sheet:
Independent battery threshold and real5V qualification. PGOOD alone is not sufficient for MAX3055. Threshold/latency worst cases remain test gates.
