digitie/canview/hardware/communicator/kicad/04_stm32.kicad_sch

## KiCad design hardware/communicator/kicad/04_stm32.kicad_sch (2026-09-06)

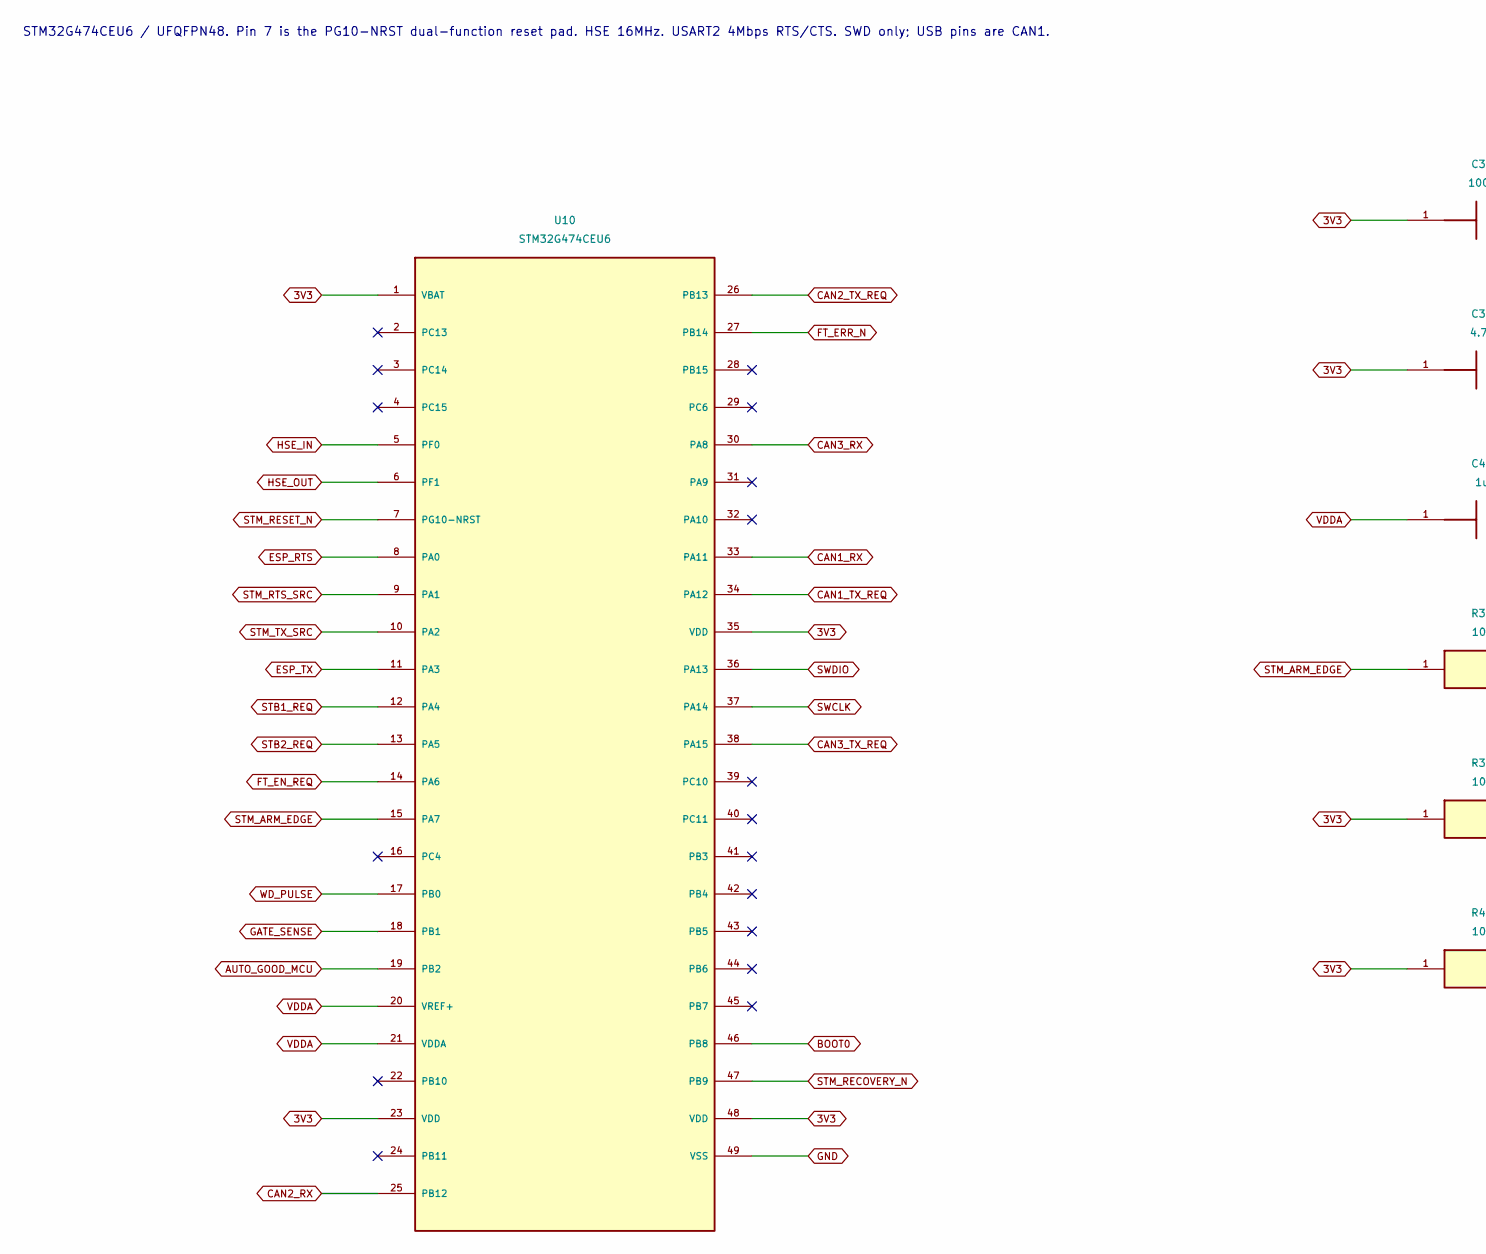
[picture p96: schematic 04_stm32.kicad_sch, part in row 1, column 1]

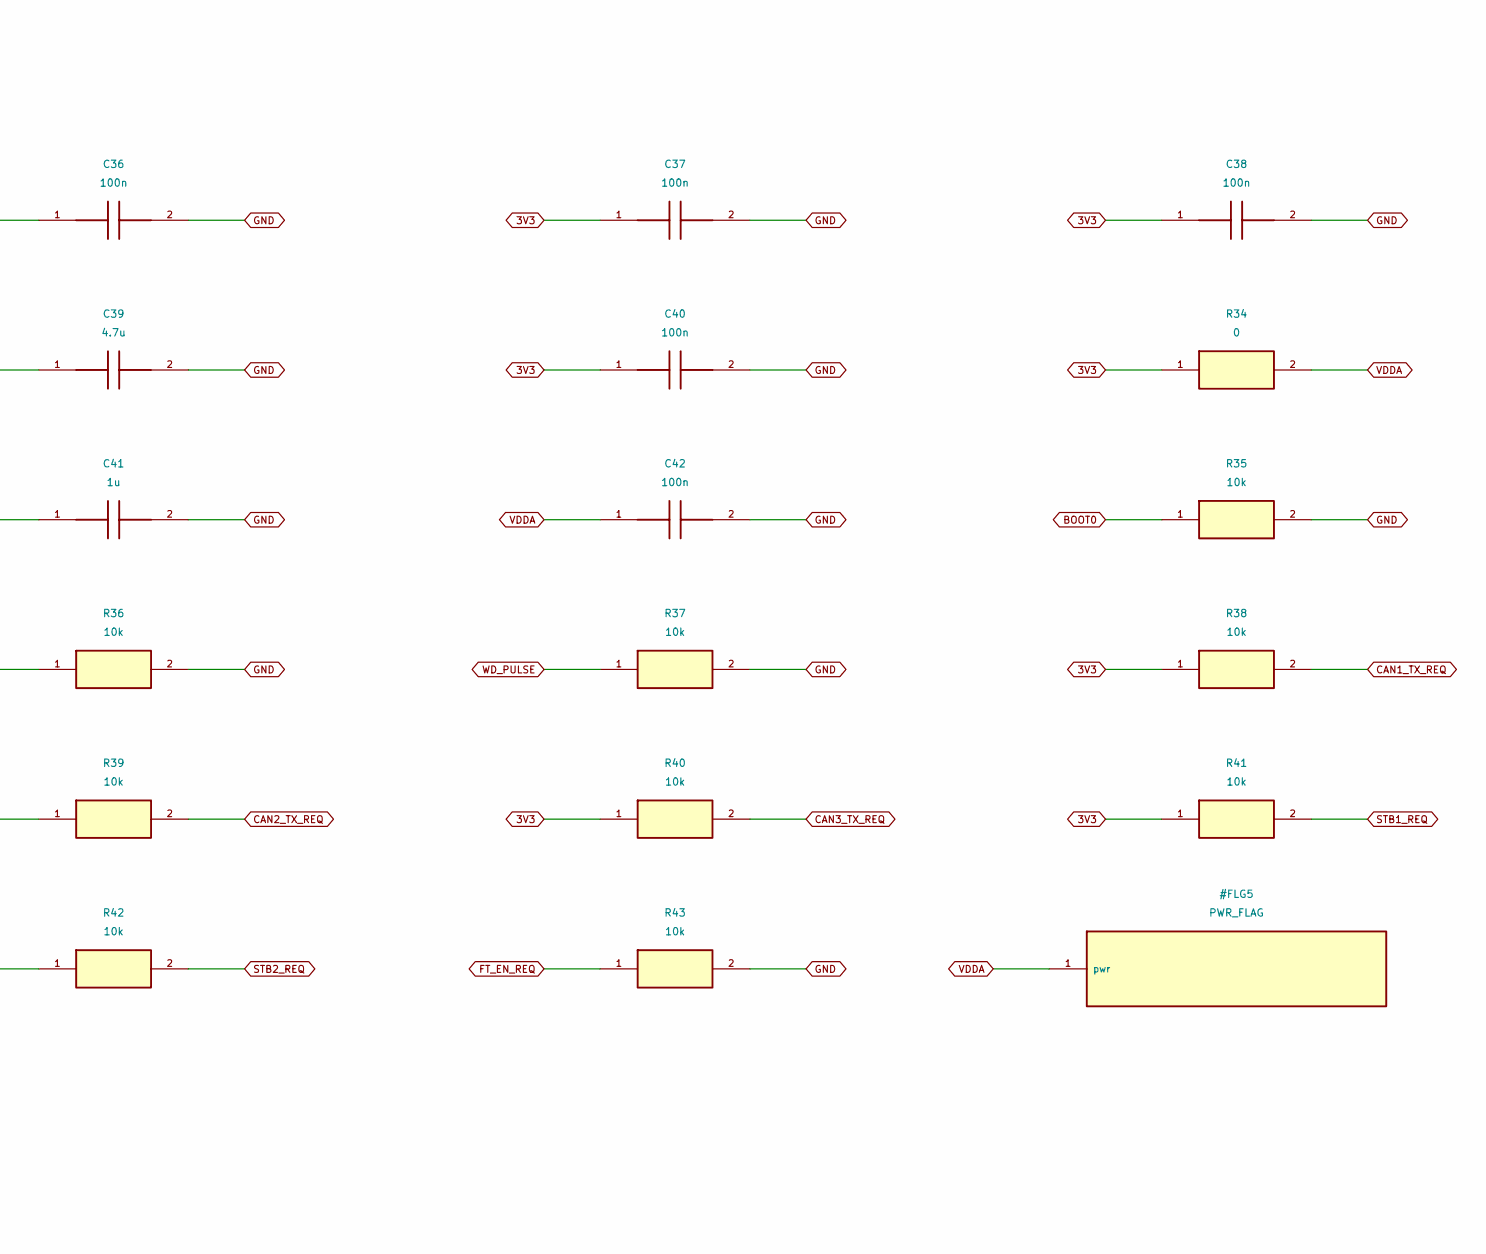
[picture p97: schematic 04_stm32.kicad_sch, part in row 1, column 2]

Parts:
C36, C37, C38, C40, C42: 100n; Capacitor_SMD__C_0402_1005Metric; MPN GEN-C-0402-100n-16V-X7R
C39: 4.7u; Capacitor_SMD__C_0603_1608Metric; MPN GEN-C-0603-4.7u-16V-X7R
C41: 1u; Capacitor_SMD__C_0603_1608Metric; MPN GEN-C-0603-1u-16V-X7R
R34: 0; Resistor_SMD__R_0402_1005Metric; MPN GEN-R-0402-0-1%
R35, R36, R37, R38, R39, R40, R41, R42, R43: 10k; Resistor_SMD__R_0402_1005Metric; MPN GEN-R-0402-10k-1%
U10: STM32G474CEU6; Package_DFN_QFN__QFN-48-1EP_7x7mm_P0.5mm_EP5.6x5.6mm; MPN STM32G474CEU6

Connections:
3V3: C36.1, C37.1, C38.1, C39.1, C40.1, R34.1, R38.1, R39.1, R40.1, R41.1, R42.1, U10.1 (VBAT), U10.23 (VDD), U10.35 (VDD), U10.48 (VDD)
AUTO_GOOD_MCU: U10.19 (PB2)
BOOT0: R35.1, U10.46 (PB8)
CAN1_RX: U10.33 (PA11)
CAN1_TX_REQ: R38.2, U10.34 (PA12)
CAN2_RX: U10.25 (PB12)
CAN2_TX_REQ: R39.2, U10.26 (PB13)
CAN3_RX: U10.30 (PA8)
CAN3_TX_REQ: R40.2, U10.38 (PA15)
ESP_RTS: U10.8 (PA0)
ESP_TX: U10.11 (PA3)
FT_EN_REQ: R43.1, U10.14 (PA6)
FT_ERR_N: U10.27 (PB14)
GATE_SENSE: U10.18 (PB1)
GND: C36.2, C37.2, C38.2, C39.2, C40.2, C41.2, C42.2, R35.2, R36.2, R37.2, R43.2, U10.49 (VSS)
HSE_IN: U10.5 (PF0)
HSE_OUT: U10.6 (PF1)
STB1_REQ: R41.2, U10.12 (PA4)
STB2_REQ: R42.2, U10.13 (PA5)
STM_ARM_EDGE: R36.1, U10.15 (PA7)
STM_RECOVERY_N: U10.47 (PB9)
STM_RESET_N: U10.7 (PG10-NRST)
STM_RTS_SRC: U10.9 (PA1)
STM_TX_SRC: U10.10 (PA2)
SWCLK: U10.37 (PA14)
SWDIO: U10.36 (PA13)
VDDA: C41.1, C42.1, R34.2, U10.20 (VREF+), U10.21 (VDDA)
WD_PULSE: R37.1, U10.17 (PB0)

Notes on the sheet:
STM32G474CEU6 / UFQFPN48. Pin 7 is the PG10-NRST dual-function reset pad. HSE 16MHz. USART2 4Mbps RTS/CTS. SWD only; USB pins are CAN1.
