digitie/canview/hardware/communicator/kicad/05_debug_clock_uart.kicad_sch

## KiCad design hardware/communicator/kicad/05_debug_clock_uart.kicad_sch (2026-09-06)

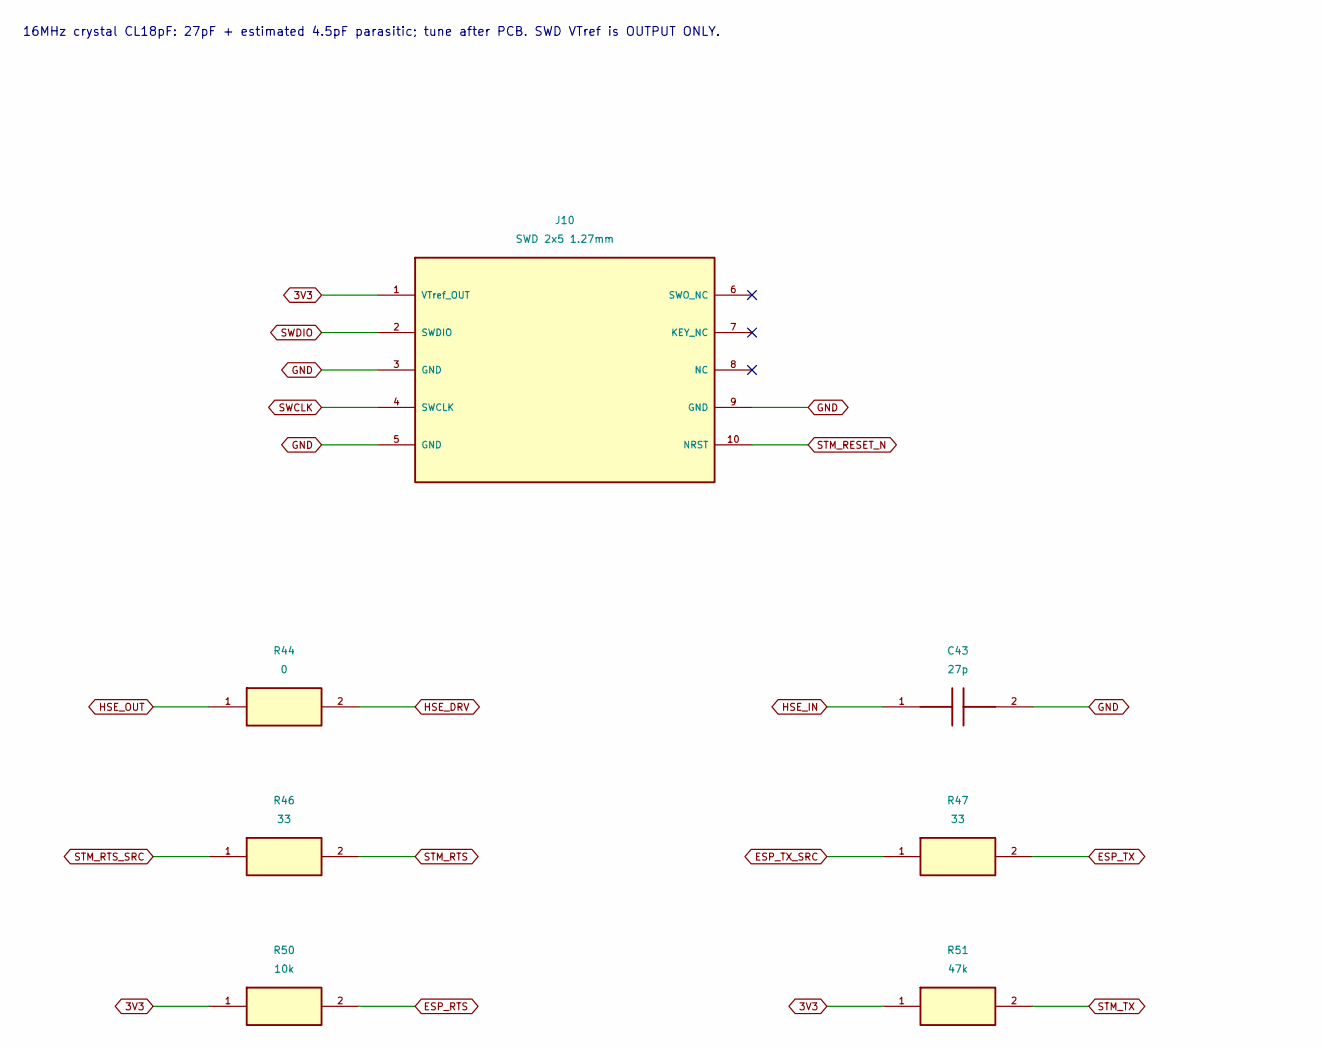
[picture p98: schematic 05_debug_clock_uart.kicad_sch, part in row 1, column 1]

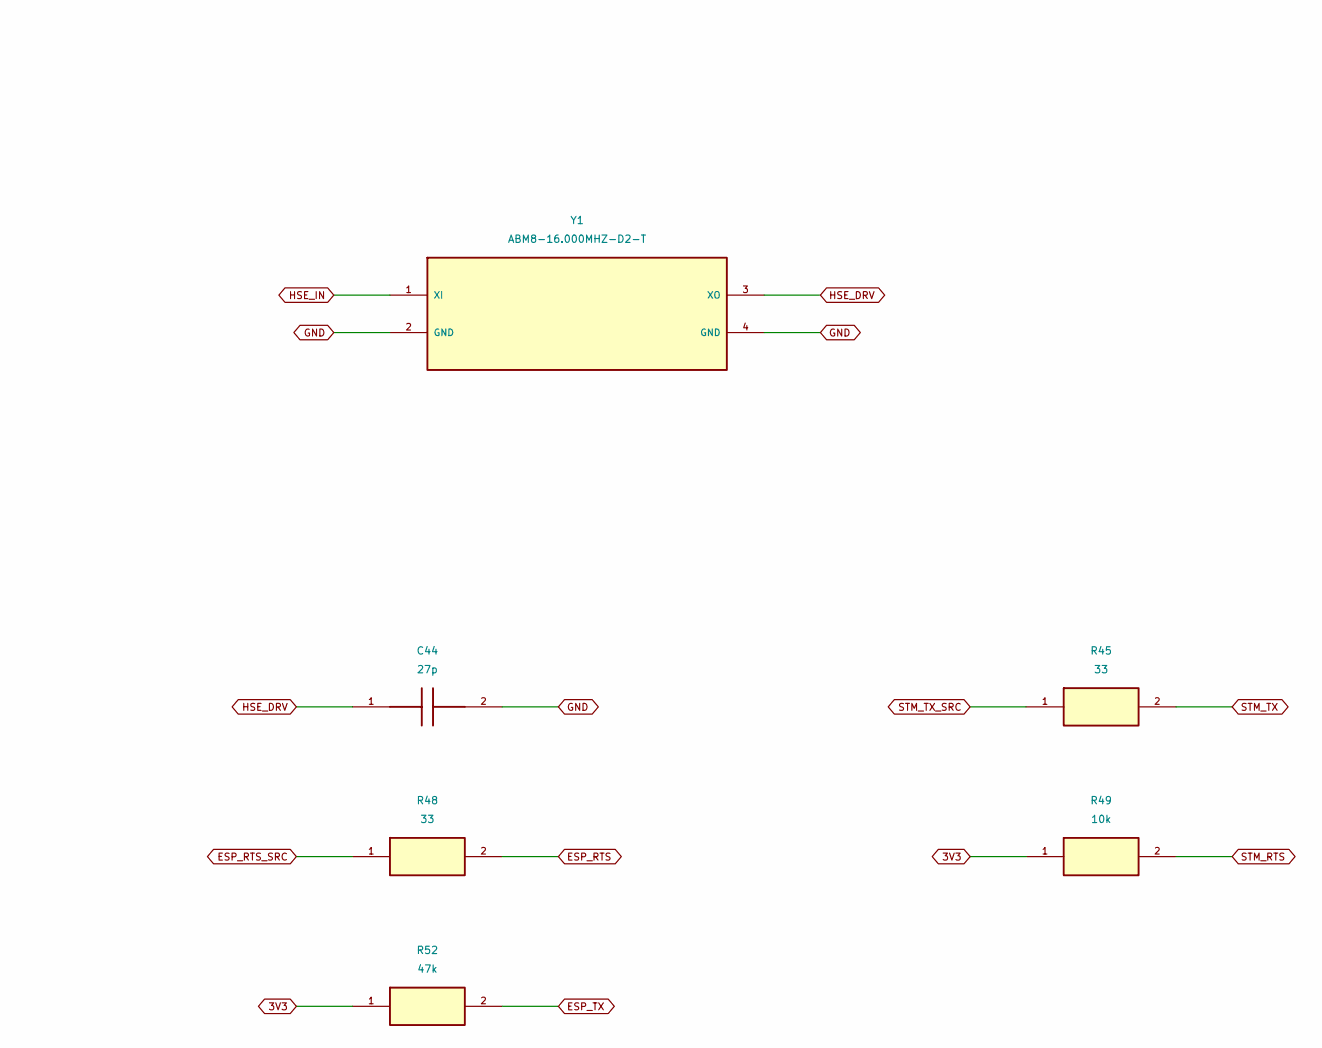
[picture p99: schematic 05_debug_clock_uart.kicad_sch, part in row 1, column 2]

Parts:
C43, C44: 27p; Capacitor_SMD__C_0402_1005Metric; MPN GEN-C-0402-27p-50V-C0G
J10: SWD 2x5 1.27mm; Connector_PinHeader_1.27mm__PinHeader_2x05_P1.27mm_Vertical; MPN SWD 2x5 1.27mm
R44: 0; Resistor_SMD__R_0402_1005Metric; MPN GEN-R-0402-0-1%
R45, R46, R47, R48: 33; Resistor_SMD__R_0402_1005Metric; MPN GEN-R-0402-33-1%
R49, R50: 10k; Resistor_SMD__R_0402_1005Metric; MPN GEN-R-0402-10k-1%
R51, R52: 47k; Resistor_SMD__R_0402_1005Metric; MPN GEN-R-0402-47k-1%
Y1: ABM8-16.000MHZ-D2-T; Crystal__Crystal_SMD_3225-4Pin_3.2x2.5mm; MPN ABM8-16.000MHZ-D2-T

Connections:
3V3: J10.1 (VTref_OUT), R49.1, R50.1, R51.1, R52.1
ESP_RTS: R48.2, R50.2
ESP_RTS_SRC: R48.1
ESP_TX: R47.2, R52.2
ESP_TX_SRC: R47.1
GND: C43.2, C44.2, J10.3 (GND), J10.5 (GND), J10.9 (GND), Y1.2 (GND), Y1.4 (GND)
HSE_DRV: C44.1, R44.2, Y1.3 (XO)
HSE_IN: C43.1, Y1.1 (XI)
HSE_OUT: R44.1
STM_RESET_N: J10.10 (NRST)
STM_RTS: R46.2, R49.2
STM_RTS_SRC: R46.1
STM_TX: R45.2, R51.2
STM_TX_SRC: R45.1
SWCLK: J10.4 (SWCLK)
SWDIO: J10.2 (SWDIO)

Notes on the sheet:
16MHz crystal CL18pF: 27pF + estimated 4.5pF parasitic; tune after PCB. SWD VTref is OUTPUT ONLY.
