digitie/canview/hardware/communicator/kicad/06_esp32.kicad_sch

## KiCad design hardware/communicator/kicad/06_esp32.kicad_sch (2026-09-06)

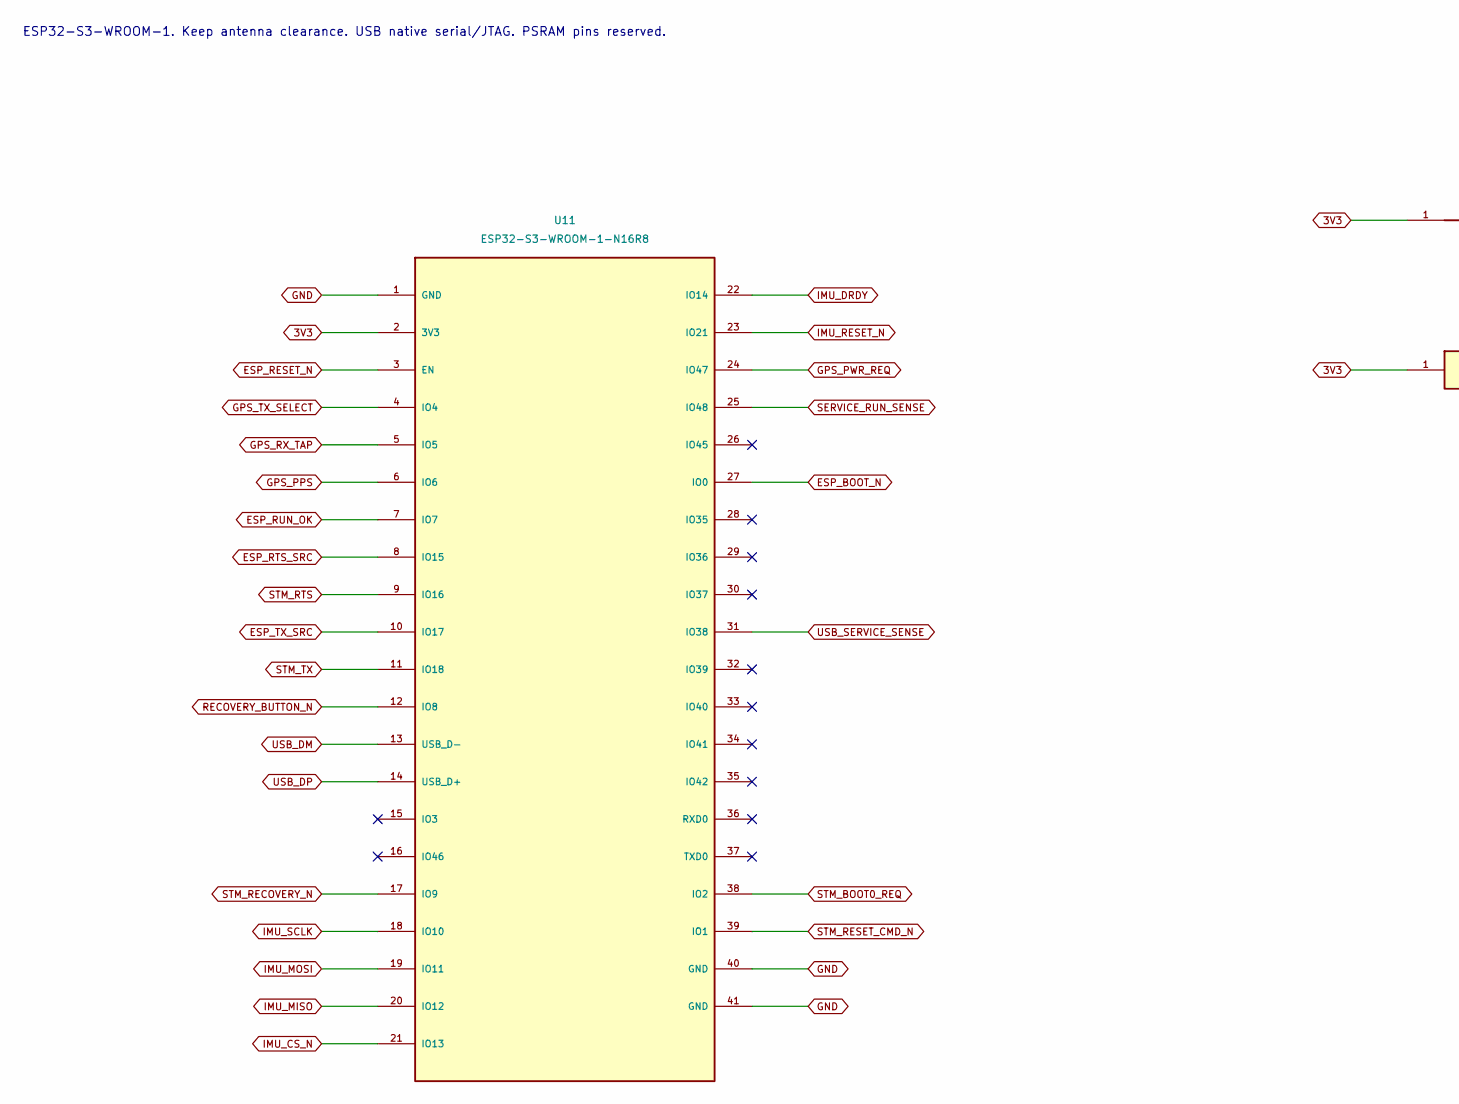
[picture p100: schematic 06_esp32.kicad_sch, part in row 1, column 1]

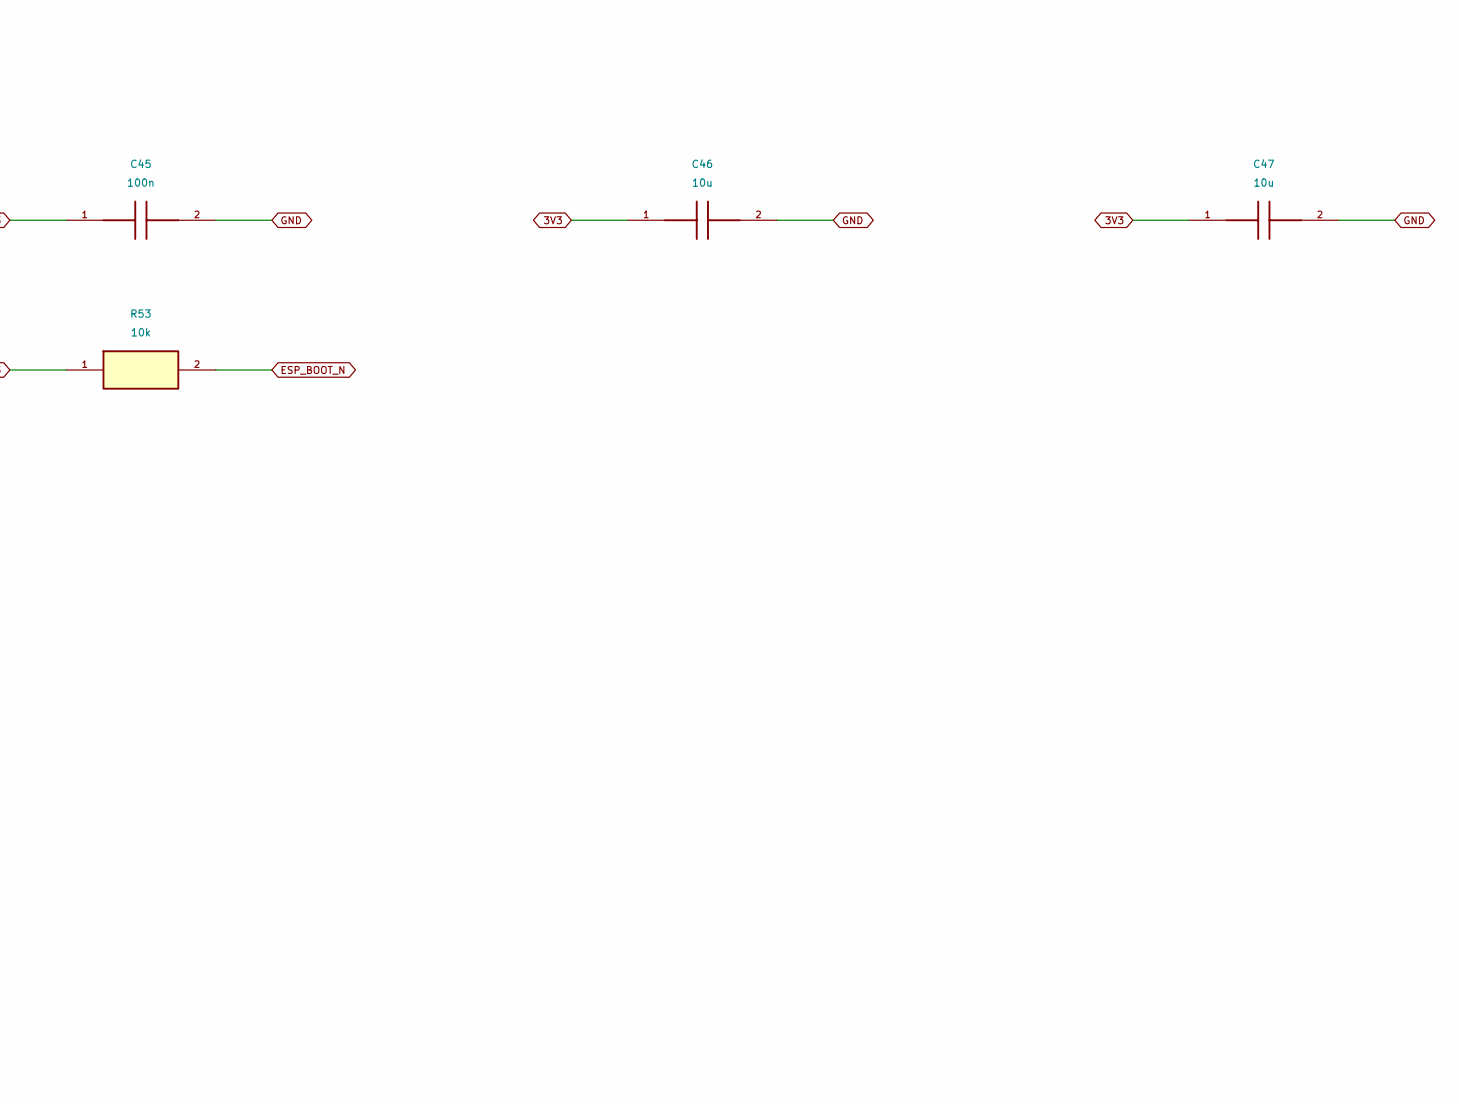
[picture p101: schematic 06_esp32.kicad_sch, part in row 1, column 2]

Parts:
C45: 100n; Capacitor_SMD__C_0603_1608Metric; MPN GEN-C-0603-100n-16V-X7R
C46, C47: 10u; Capacitor_SMD__C_0603_1608Metric; MPN GEN-C-0603-10u-16V-X7R
R53: 10k; Resistor_SMD__R_0402_1005Metric; MPN GEN-R-0402-10k-1%
U11: ESP32-S3-WROOM-1-N16R8; RF_Module__ESP32-S3-WROOM-1; MPN ESP32-S3-WROOM-1-N16R8

Connections:
3V3: C45.1, C46.1, C47.1, R53.1, U11.2 (3V3)
ESP_BOOT_N: R53.2, U11.27 (IO0)
ESP_RESET_N: U11.3 (EN)
ESP_RTS_SRC: U11.8 (IO15)
ESP_RUN_OK: U11.7 (IO7)
ESP_TX_SRC: U11.10 (IO17)
GND: C45.2, C46.2, C47.2, U11.1 (GND), U11.40 (GND), U11.41 (GND)
GPS_PPS: U11.6 (IO6)
GPS_PWR_REQ: U11.24 (IO47)
GPS_RX_TAP: U11.5 (IO5)
GPS_TX_SELECT: U11.4 (IO4)
IMU_CS_N: U11.21 (IO13)
IMU_DRDY: U11.22 (IO14)
IMU_MISO: U11.20 (IO12)
IMU_MOSI: U11.19 (IO11)
IMU_RESET_N: U11.23 (IO21)
IMU_SCLK: U11.18 (IO10)
RECOVERY_BUTTON_N: U11.12 (IO8)
SERVICE_RUN_SENSE: U11.25 (IO48)
STM_BOOT0_REQ: U11.38 (IO2)
STM_RECOVERY_N: U11.17 (IO9)
STM_RESET_CMD_N: U11.39 (IO1)
STM_RTS: U11.9 (IO16)
STM_TX: U11.11 (IO18)
USB_DM: U11.13 (USB_D-)
USB_DP: U11.14 (USB_D+)
USB_SERVICE_SENSE: U11.31 (IO38)

Notes on the sheet:
ESP32-S3-WROOM-1. Keep antenna clearance. USB native serial/JTAG. PSRAM pins reserved.
