digitie/canview/hardware/communicator/kicad/07_esp_service.kicad_sch

## KiCad design hardware/communicator/kicad/07_esp_service.kicad_sch (2026-09-06)

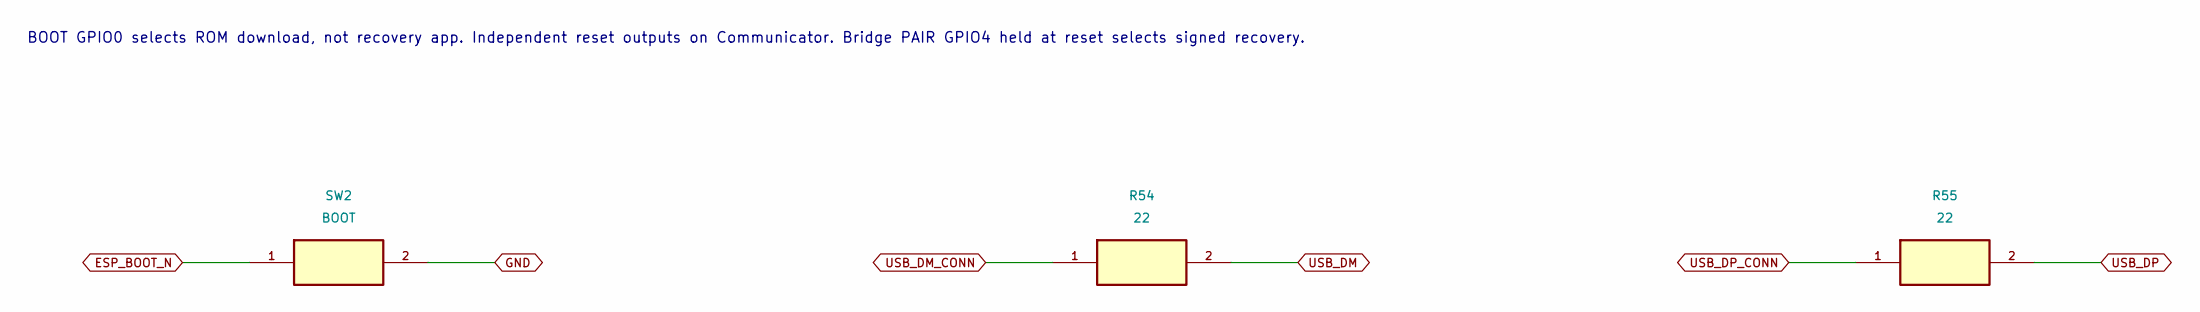
[picture p102: schematic 07_esp_service.kicad_sch]

Parts:
R54, R55: 22; Resistor_SMD__R_0402_1005Metric; MPN GEN-R-0402-22-1%
SW2: BOOT; Button_Switch_SMD__SW_SPST_TL3342; MPN TL3342F160QG

Connections:
ESP_BOOT_N: SW2.1
GND: SW2.2
USB_DM: R54.2
USB_DM_CONN: R54.1
USB_DP: R55.2
USB_DP_CONN: R55.1

Notes on the sheet:
BOOT GPIO0 selects ROM download, not recovery app. Independent reset outputs on Communicator. Bridge PAIR GPIO4 held at reset selects signed recovery.
