digitie/canview/hardware/communicator/kicad/08_can_fd.kicad_sch

## KiCad design hardware/communicator/kicad/08_can_fd.kicad_sch (2026-09-06)

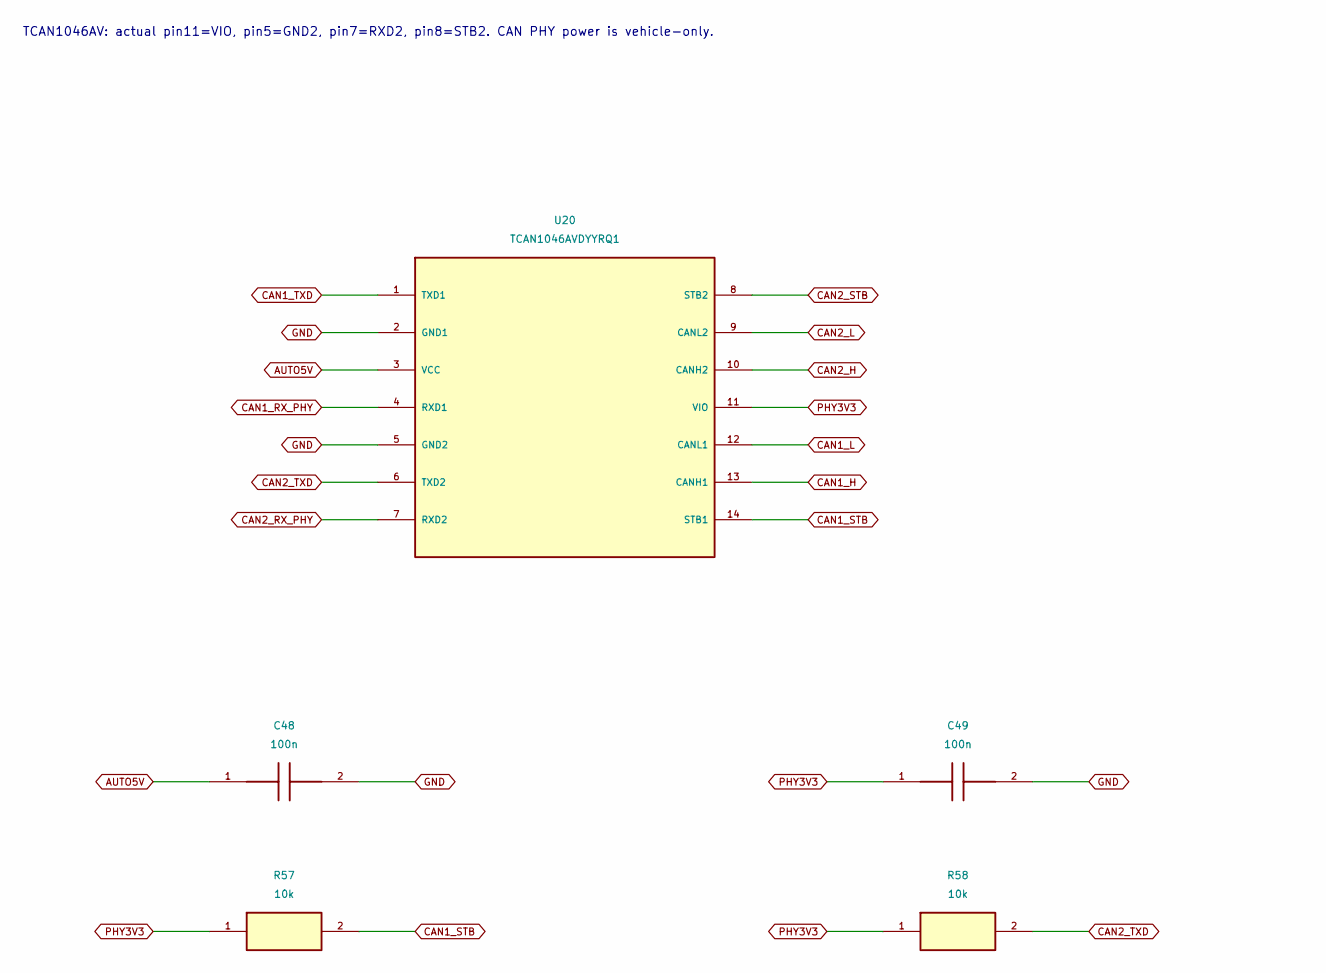
[picture p103: schematic 08_can_fd.kicad_sch, part in row 1, column 1]

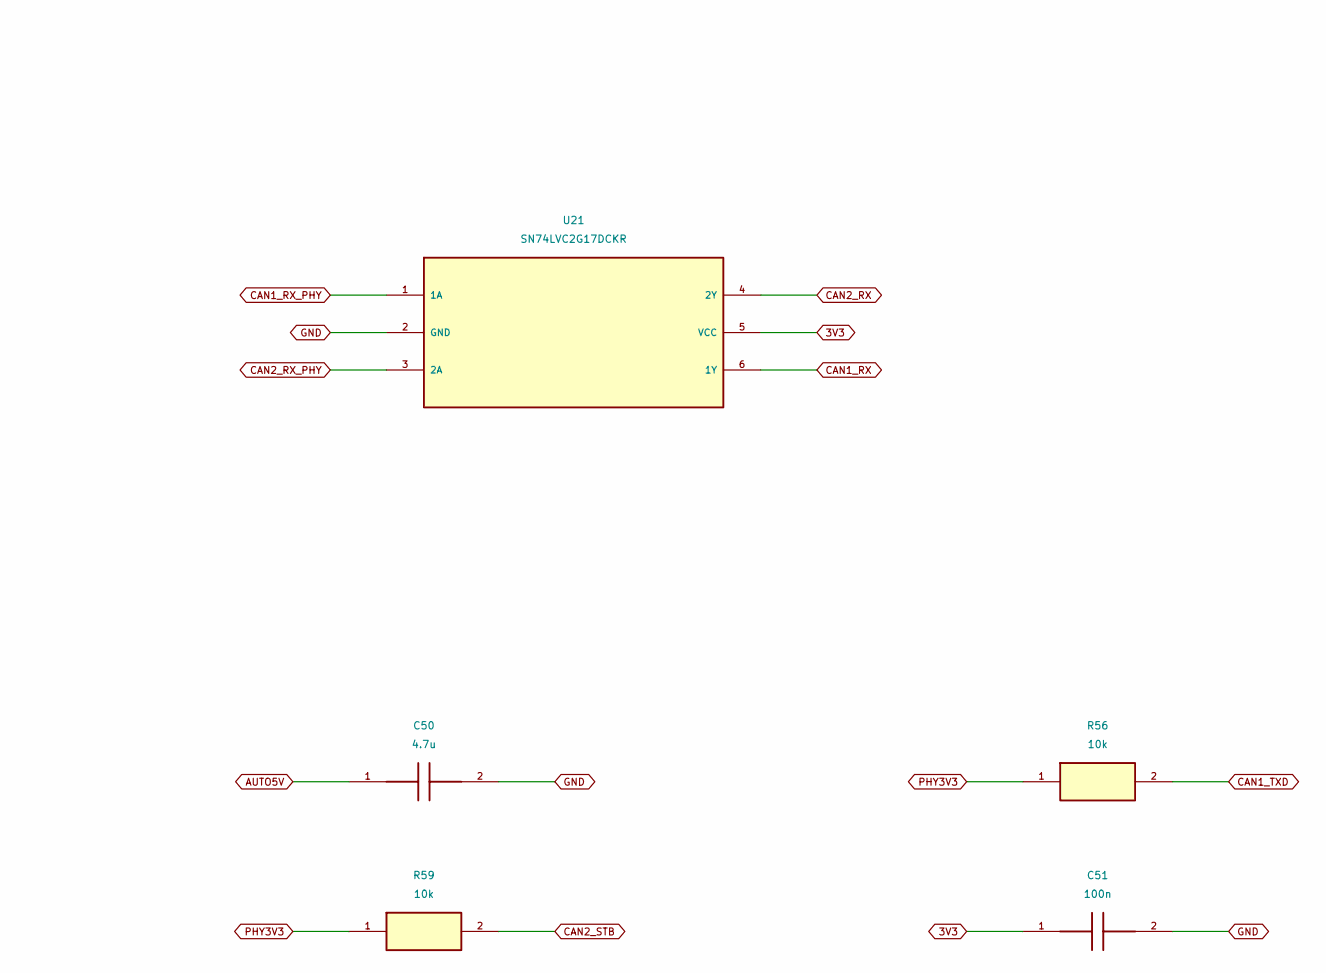
[picture p104: schematic 08_can_fd.kicad_sch, part in row 1, column 2]

Parts:
C48, C49, C51: 100n; Capacitor_SMD__C_0402_1005Metric; MPN GEN-C-0402-100n-16V-X7R
C50: 4.7u; Capacitor_SMD__C_0603_1608Metric; MPN GEN-C-0603-4.7u-16V-X7R
R56, R57, R58, R59: 10k; Resistor_SMD__R_0402_1005Metric; MPN GEN-R-0402-10k-1%
U20: TCAN1046AVDYYRQ1; TI_DYY0014A; MPN TCAN1046AVDYYRQ1
U21: SN74LVC2G17DCKR; Package_TO_SOT_SMD__SOT-363_SC-70-6; MPN SN74LVC2G17DCKR

Connections:
3V3: C51.1, U21.5 (VCC)
AUTO5V: C48.1, C50.1, U20.3 (VCC)
CAN1_H: U20.13 (CANH1)
CAN1_L: U20.12 (CANL1)
CAN1_RX: U21.6 (1Y)
CAN1_RX_PHY: U20.4 (RXD1), U21.1 (1A)
CAN1_STB: R57.2, U20.14 (STB1)
CAN1_TXD: R56.2, U20.1 (TXD1)
CAN2_H: U20.10 (CANH2)
CAN2_L: U20.9 (CANL2)
CAN2_RX: U21.4 (2Y)
CAN2_RX_PHY: U20.7 (RXD2), U21.3 (2A)
CAN2_STB: R59.2, U20.8 (STB2)
CAN2_TXD: R58.2, U20.6 (TXD2)
GND: C48.2, C49.2, C50.2, C51.2, U20.2 (GND1), U20.5 (GND2), U21.2 (GND)
PHY3V3: C49.1, R56.1, R57.1, R58.1, R59.1, U20.11 (VIO)

Notes on the sheet:
TCAN1046AV: actual pin11=VIO, pin5=GND2, pin7=RXD2, pin8=STB2. CAN PHY power is vehicle-only.
