digitie/canview/hardware/communicator/kicad/09_can_ft.kicad_sch

## KiCad design hardware/communicator/kicad/09_can_ft.kicad_sch (2026-09-06)

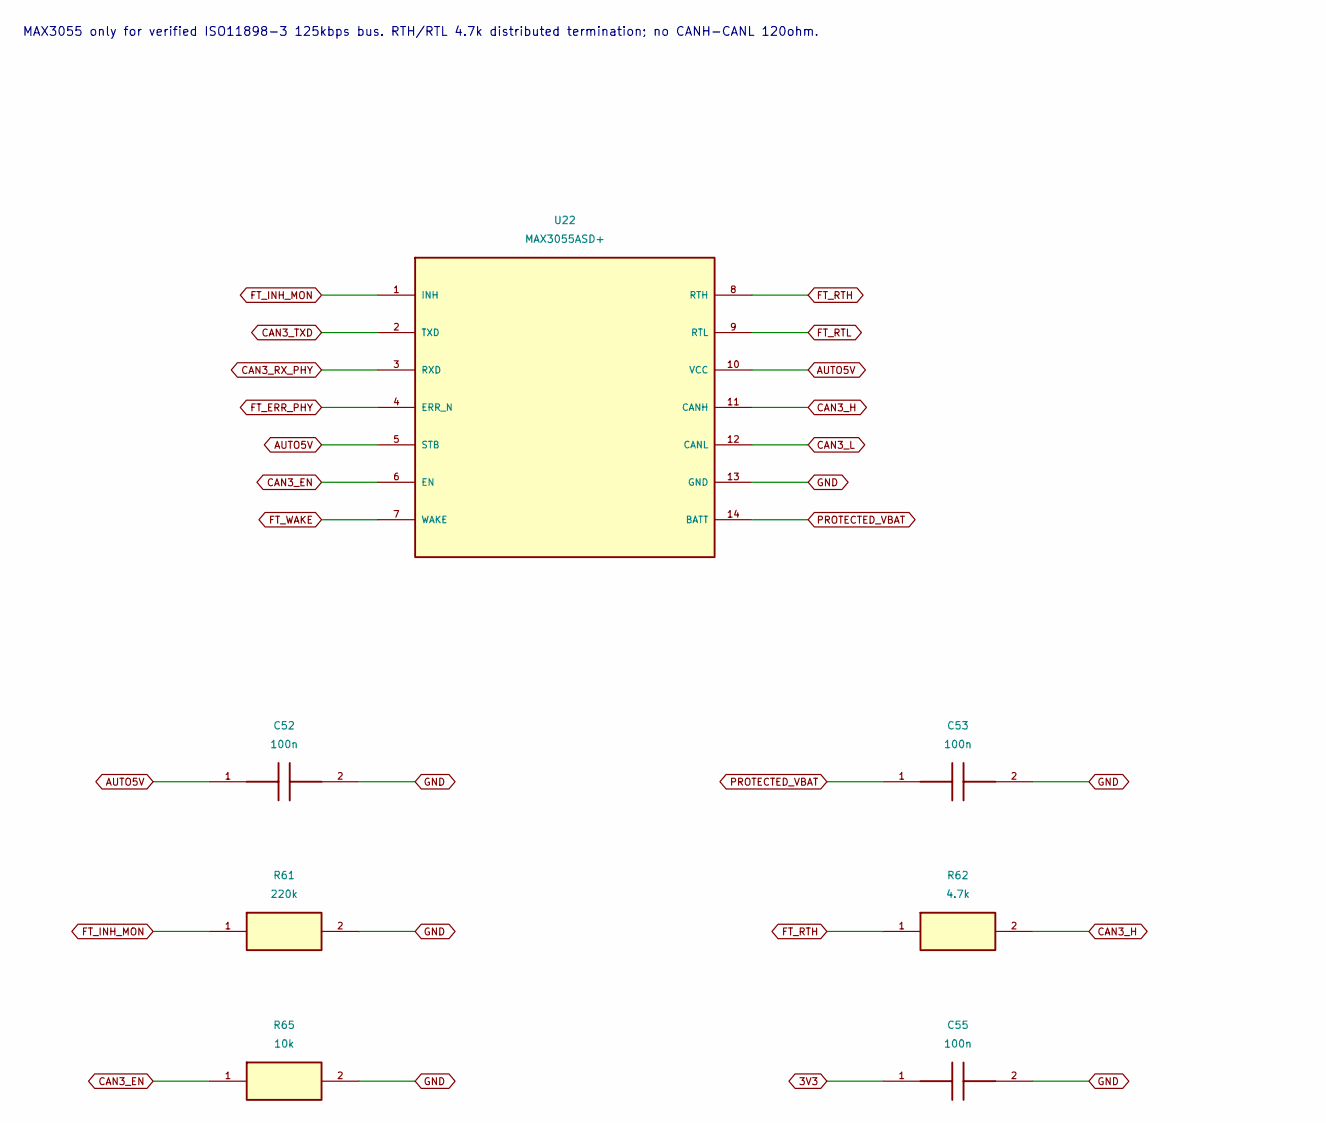
[picture p105: schematic 09_can_ft.kicad_sch, part in row 1, column 1]

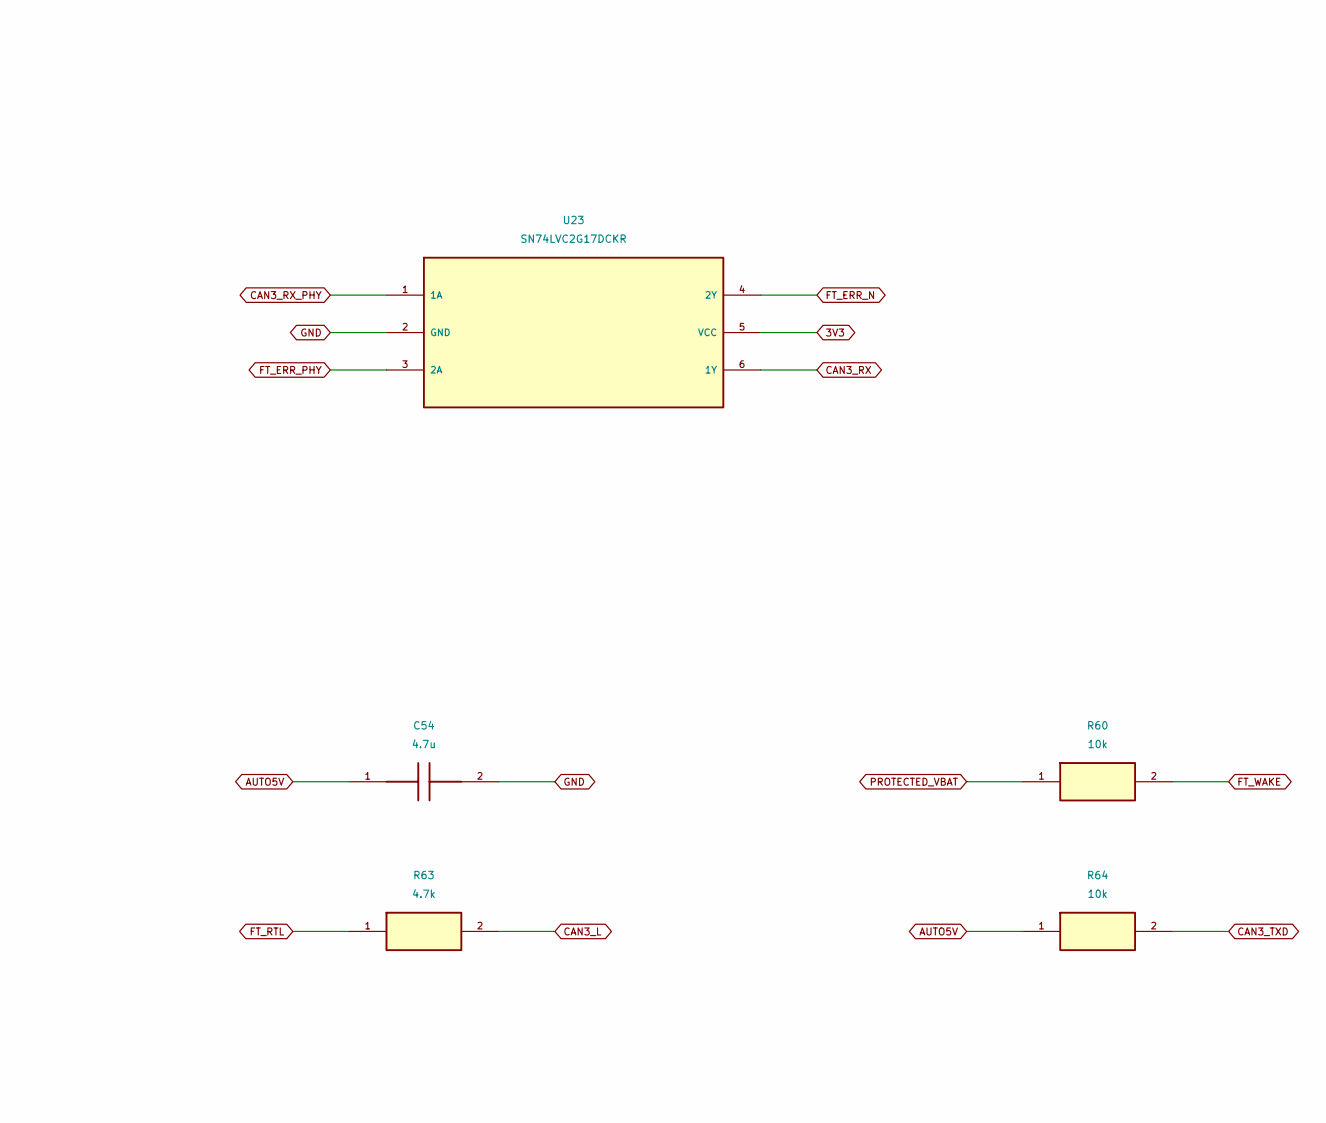
[picture p106: schematic 09_can_ft.kicad_sch, part in row 1, column 2]

Parts:
C52, C55: 100n; Capacitor_SMD__C_0402_1005Metric; MPN GEN-C-0402-100n-16V-X7R
C53: 100n; Capacitor_SMD__C_0603_1608Metric; MPN GEN-C-0603-100n-50V-X7R
C54: 4.7u; Capacitor_SMD__C_0603_1608Metric; MPN GEN-C-0603-4.7u-16V-X7R
R60: 10k; Resistor_SMD__R_0603_1608Metric; MPN GEN-R-0603-10k-1%
R61: 220k; Resistor_SMD__R_0603_1608Metric; MPN GEN-R-0603-220k-1%
R62, R63: 4.7k; Resistor_SMD__R_0805_2012Metric; MPN GEN-R-0805-4.7k-1%
R64, R65: 10k; Resistor_SMD__R_0402_1005Metric; MPN GEN-R-0402-10k-1%
U22: MAX3055ASD+; Package_SO__SOIC-14_3.9x8.7mm_P1.27mm; MPN MAX3055ASD+
U23: SN74LVC2G17DCKR; Package_TO_SOT_SMD__SOT-363_SC-70-6; MPN SN74LVC2G17DCKR

Connections:
3V3: C55.1, U23.5 (VCC)
AUTO5V: C52.1, C54.1, R64.1, U22.5 (STB), U22.10 (VCC)
CAN3_EN: R65.1, U22.6 (EN)
CAN3_H: R62.2, U22.11 (CANH)
CAN3_L: R63.2, U22.12 (CANL)
CAN3_RX: U23.6 (1Y)
CAN3_RX_PHY: U22.3 (RXD), U23.1 (1A)
CAN3_TXD: R64.2, U22.2 (TXD)
FT_ERR_N: U23.4 (2Y)
FT_ERR_PHY: U22.4 (ERR_N), U23.3 (2A)
FT_INH_MON: R61.1, U22.1 (INH)
FT_RTH: R62.1, U22.8 (RTH)
FT_RTL: R63.1, U22.9 (RTL)
FT_WAKE: R60.2, U22.7 (WAKE)
GND: C52.2, C53.2, C54.2, C55.2, R61.2, R65.2, U22.13 (GND), U23.2 (GND)
PROTECTED_VBAT: C53.1, R60.1, U22.14 (BATT)

Notes on the sheet:
MAX3055 only for verified ISO11898-3 125kbps bus. RTH/RTL 4.7k distributed termination; no CANH-CANL 120ohm.
