digitie/canview/hardware/communicator/kicad/10_tx_gate.kicad_sch

## KiCad design hardware/communicator/kicad/10_tx_gate.kicad_sch (2026-09-06)

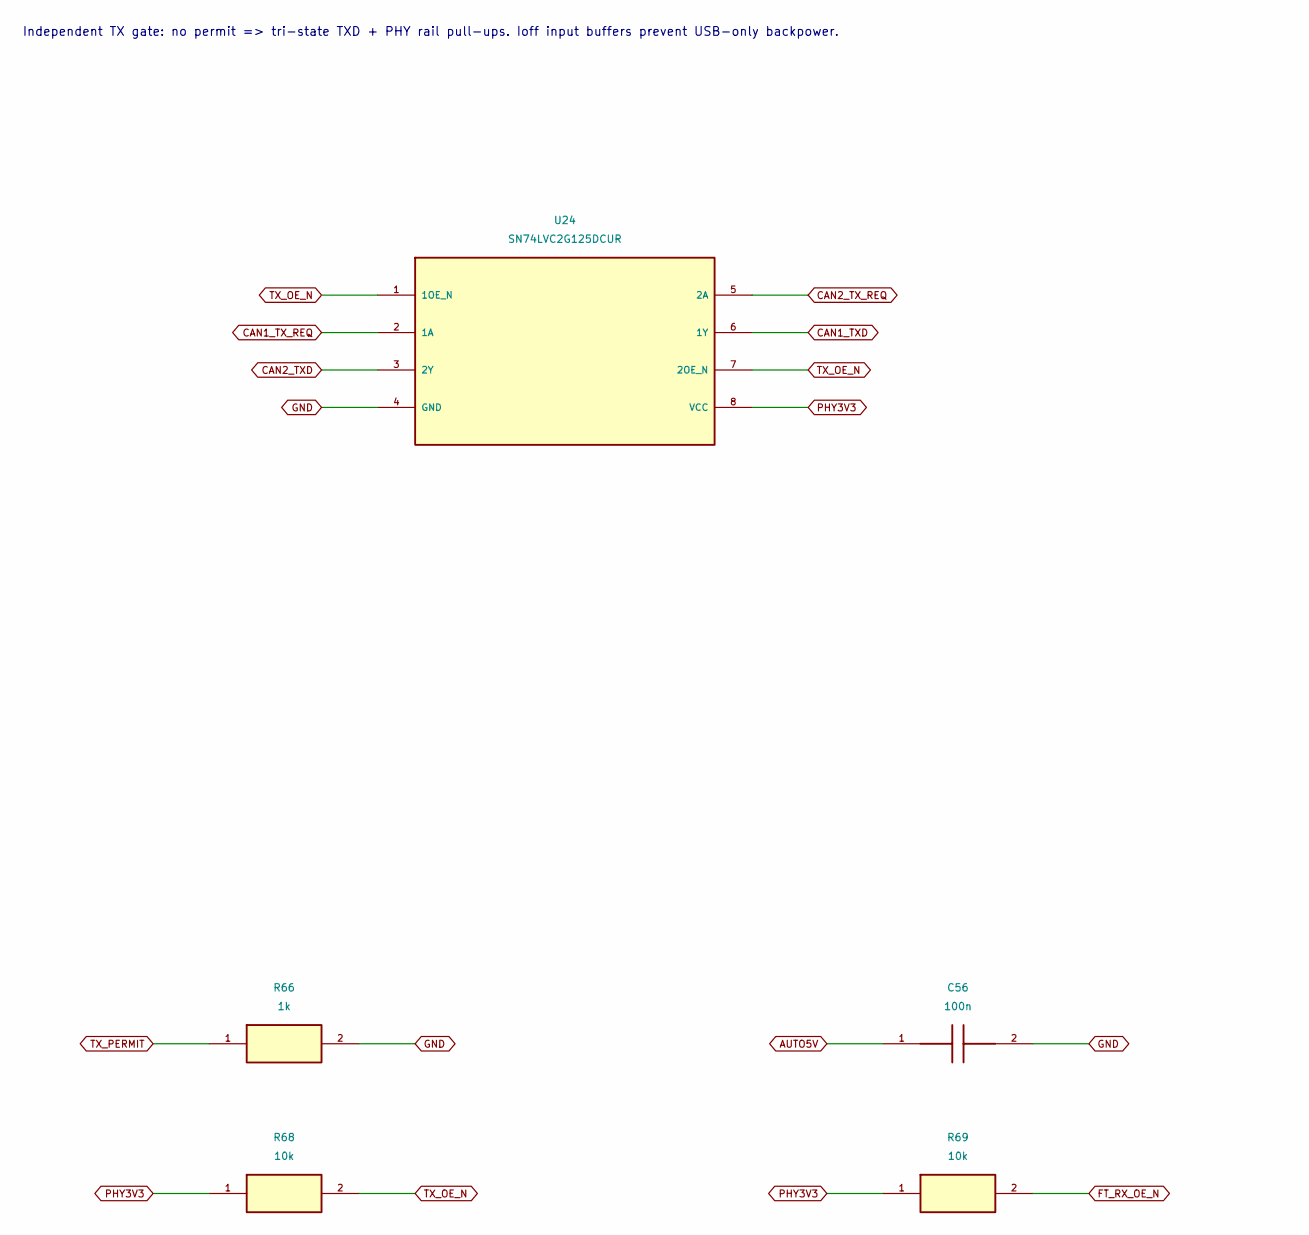
[picture p107: schematic 10_tx_gate.kicad_sch, part in row 1, column 1]

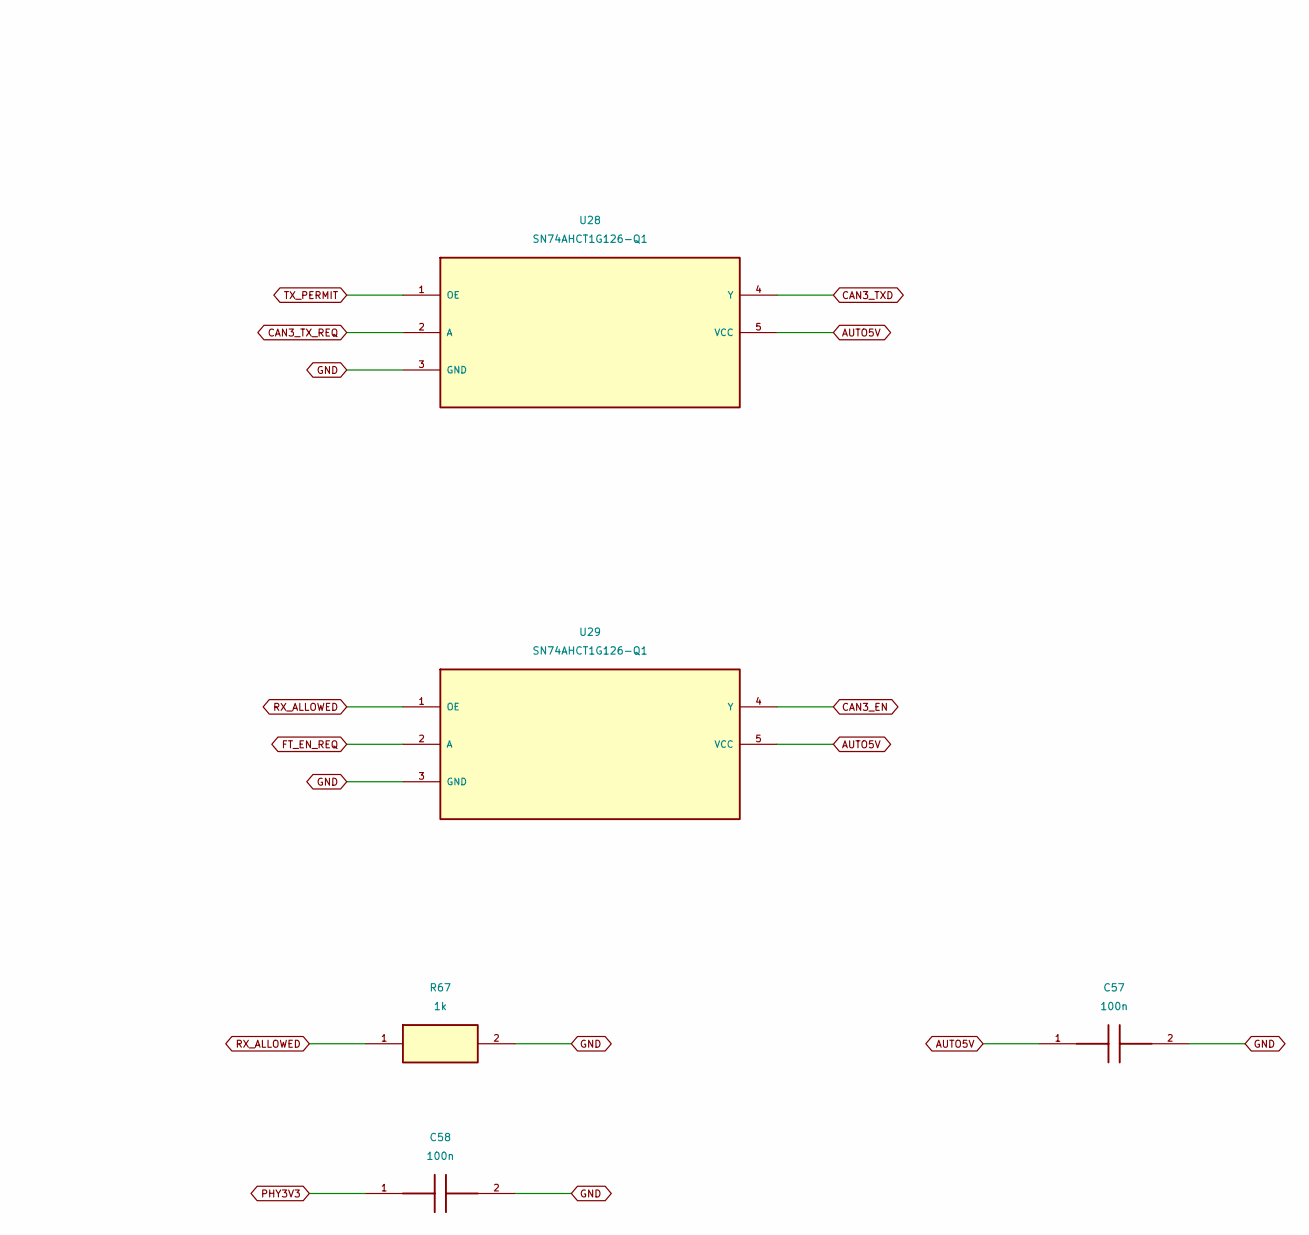
[picture p108: schematic 10_tx_gate.kicad_sch, part in row 1, column 2]

Parts:
C56, C57, C58: 100n; Capacitor_SMD__C_0402_1005Metric; MPN GEN-C-0402-100n-16V-X7R
R66, R67: 1k; Resistor_SMD__R_0402_1005Metric; MPN GEN-R-0402-1k-1%
R68, R69: 10k; Resistor_SMD__R_0402_1005Metric; MPN GEN-R-0402-10k-1%
U24: SN74LVC2G125DCUR; Package_SO__VSSOP-8_2.3x2mm_P0.5mm; MPN SN74LVC2G125DCUR
U28, U29: SN74AHCT1G126-Q1; Package_TO_SOT_SMD__SOT-23-5; MPN CAHCT1G126DBVRQ1

Connections:
AUTO5V: C56.1, C57.1, U28.5 (VCC), U29.5 (VCC)
CAN1_TXD: U24.6 (1Y)
CAN1_TX_REQ: U24.2 (1A)
CAN2_TXD: U24.3 (2Y)
CAN2_TX_REQ: U24.5 (2A)
CAN3_EN: U29.4 (Y)
CAN3_TXD: U28.4 (Y)
CAN3_TX_REQ: U28.2 (A)
FT_EN_REQ: U29.2 (A)
FT_RX_OE_N: R69.2
GND: C56.2, C57.2, C58.2, R66.2, R67.2, U24.4 (GND), U28.3 (GND), U29.3 (GND)
PHY3V3: C58.1, R68.1, R69.1, U24.8 (VCC)
RX_ALLOWED: R67.1, U29.1 (OE)
TX_OE_N: R68.2, U24.1 (1OE_N), U24.7 (2OE_N)
TX_PERMIT: R66.1, U28.1 (OE)

Notes on the sheet:
Independent TX gate: no permit => tri-state TXD + PHY rail pull-ups. Ioff input buffers prevent USB-only backpower.
