digitie/canview/hardware/communicator/kicad/11_phy_modes.kicad_sch

## KiCad design hardware/communicator/kicad/11_phy_modes.kicad_sch (2026-09-06)

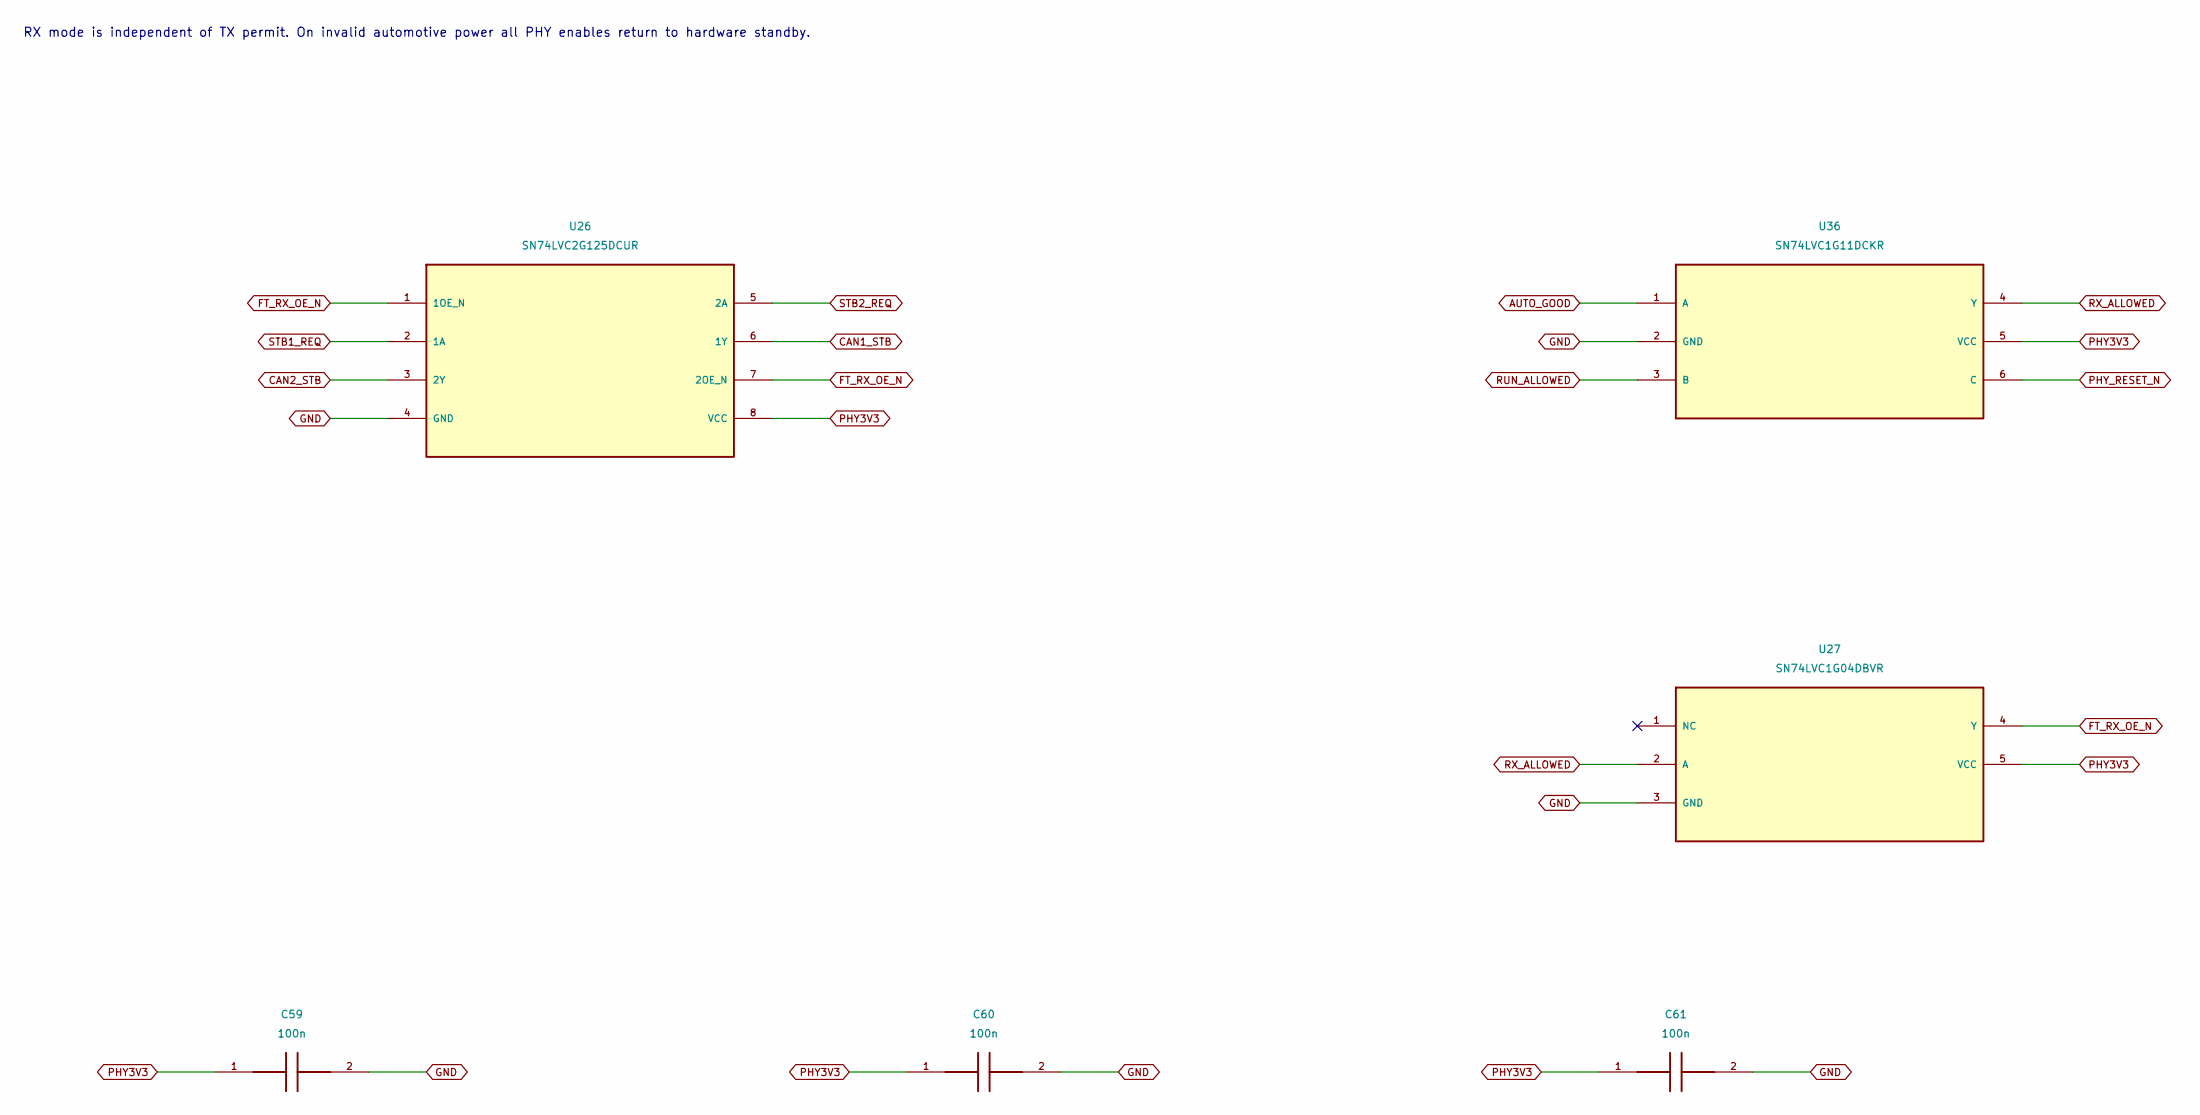
[picture p109: schematic 11_phy_modes.kicad_sch]

Parts:
C59, C60, C61: 100n; Capacitor_SMD__C_0402_1005Metric; MPN GEN-C-0402-100n-16V-X7R
U26: SN74LVC2G125DCUR; Package_SO__VSSOP-8_2.3x2mm_P0.5mm; MPN SN74LVC2G125DCUR
U27: SN74LVC1G04DBVR; Package_TO_SOT_SMD__SOT-23-5; MPN SN74LVC1G04DBVR
U36: SN74LVC1G11DCKR; Package_TO_SOT_SMD__SOT-363_SC-70-6; MPN SN74LVC1G11DCKR

Connections:
AUTO_GOOD: U36.1 (A)
CAN1_STB: U26.6 (1Y)
CAN2_STB: U26.3 (2Y)
FT_RX_OE_N: U26.1 (1OE_N), U26.7 (2OE_N), U27.4 (Y)
GND: C59.2, C60.2, C61.2, U26.4 (GND), U27.3 (GND), U36.2 (GND)
PHY3V3: C59.1, C60.1, C61.1, U26.8 (VCC), U27.5 (VCC), U36.5 (VCC)
PHY_RESET_N: U36.6 (C)
RUN_ALLOWED: U36.3 (B)
RX_ALLOWED: U27.2 (A), U36.4 (Y)
STB1_REQ: U26.2 (1A)
STB2_REQ: U26.5 (2A)

Notes on the sheet:
RX mode is independent of TX permit. On invalid automotive power all PHY enables return to hardware standby.
