digitie/canview/hardware/communicator/kicad/12_watchdog_latch.kicad_sch

## KiCad design hardware/communicator/kicad/12_watchdog_latch.kicad_sch (2026-09-06)

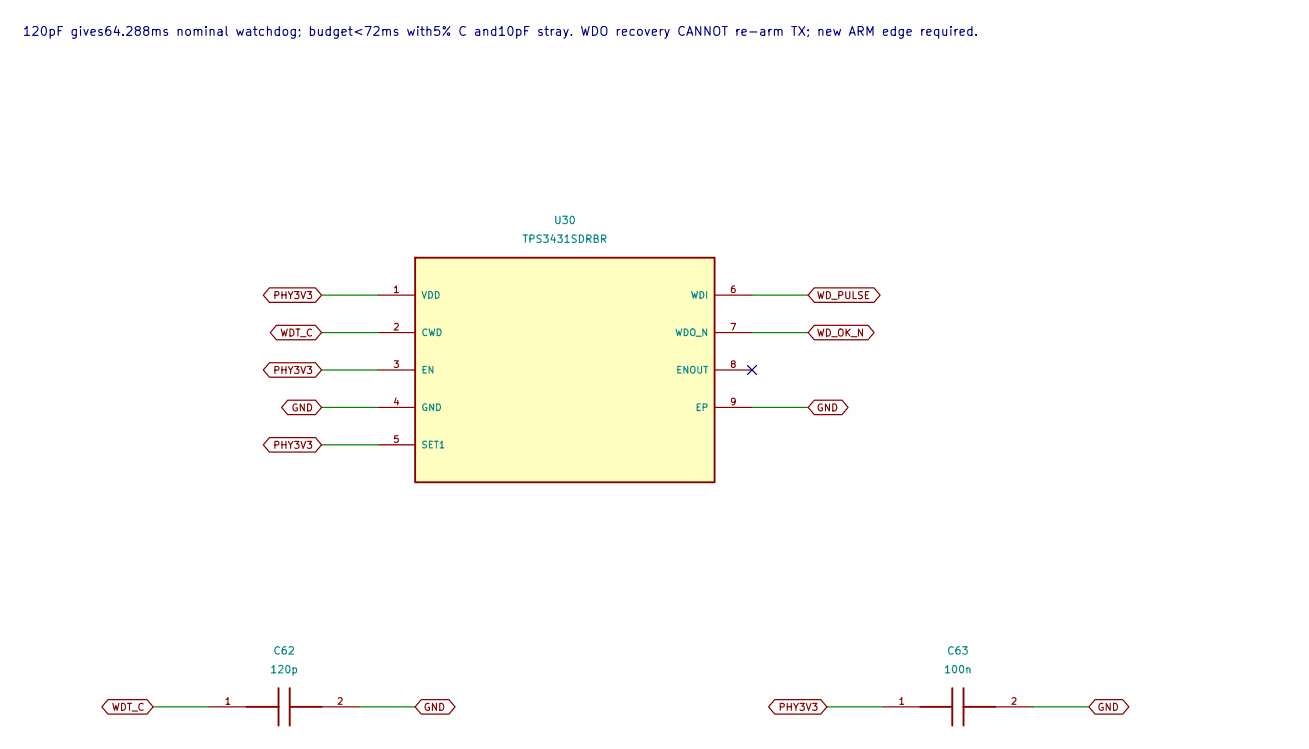
[picture p110: schematic 12_watchdog_latch.kicad_sch, part in row 1, column 1]

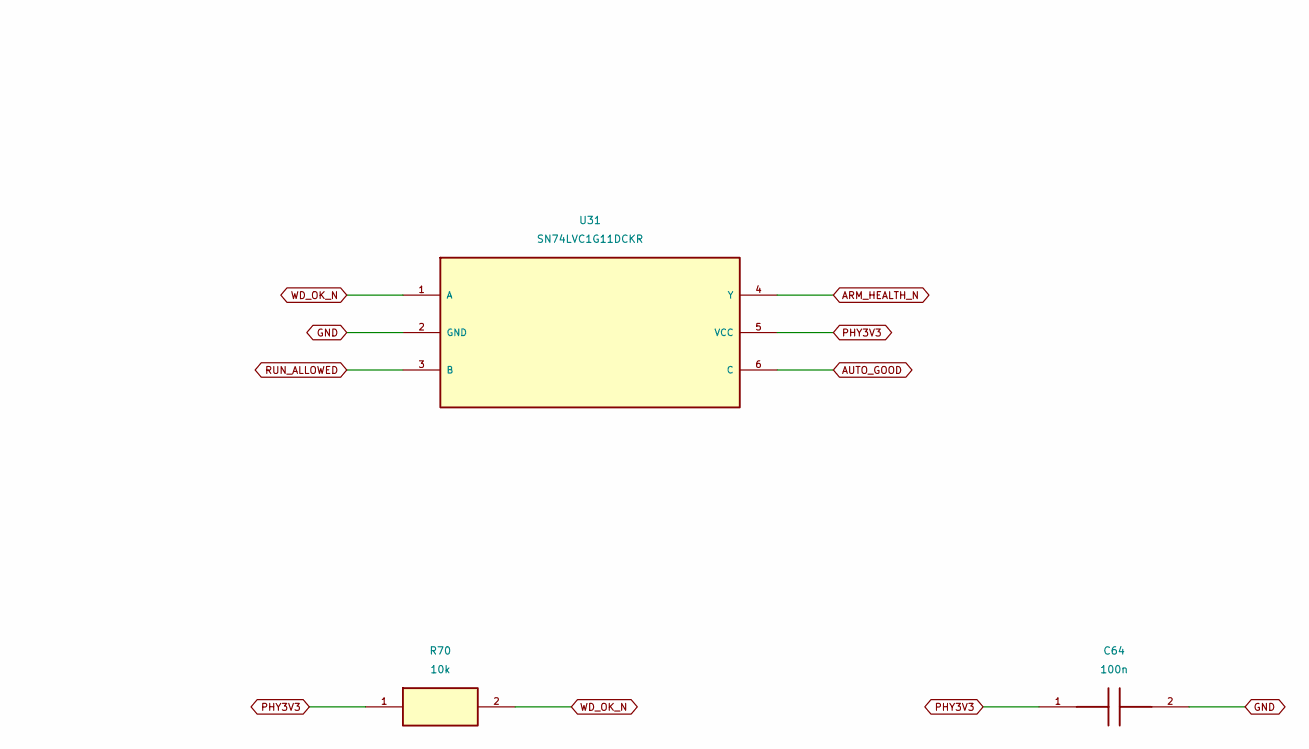
[picture p111: schematic 12_watchdog_latch.kicad_sch, part in row 1, column 2]

Parts:
C62: 120p; Capacitor_SMD__C_0402_1005Metric; MPN GEN-C-0402-120p-16V-C0G
C63, C64: 100n; Capacitor_SMD__C_0402_1005Metric; MPN GEN-C-0402-100n-16V-X7R
R70: 10k; Resistor_SMD__R_0402_1005Metric; MPN GEN-R-0402-10k-1%
U30: TPS3431SDRBR; TI_DRB0008A; MPN TPS3431SDRBR
U31: SN74LVC1G11DCKR; Package_TO_SOT_SMD__SOT-363_SC-70-6; MPN SN74LVC1G11DCKR

Connections:
ARM_HEALTH_N: U31.4 (Y)
AUTO_GOOD: U31.6 (C)
GND: C62.2, C63.2, C64.2, U30.4 (GND), U30.9 (EP), U31.2 (GND)
PHY3V3: C63.1, C64.1, R70.1, U30.1 (VDD), U30.3 (EN), U30.5 (SET1), U31.5 (VCC)
RUN_ALLOWED: U31.3 (B)
WDT_C: C62.1, U30.2 (CWD)
WD_OK_N: R70.2, U30.7 (WDO_N), U31.1 (A)
WD_PULSE: U30.6 (WDI)

Notes on the sheet:
120pF gives64.288ms nominal watchdog; budget<72ms with5% C and10pF stray. WDO recovery CANNOT re-arm TX; new ARM edge required.
