digitie/canview/hardware/communicator/kicad/12b_latch_clear.kicad_sch

## KiCad design hardware/communicator/kicad/12b_latch_clear.kicad_sch (2026-09-06)

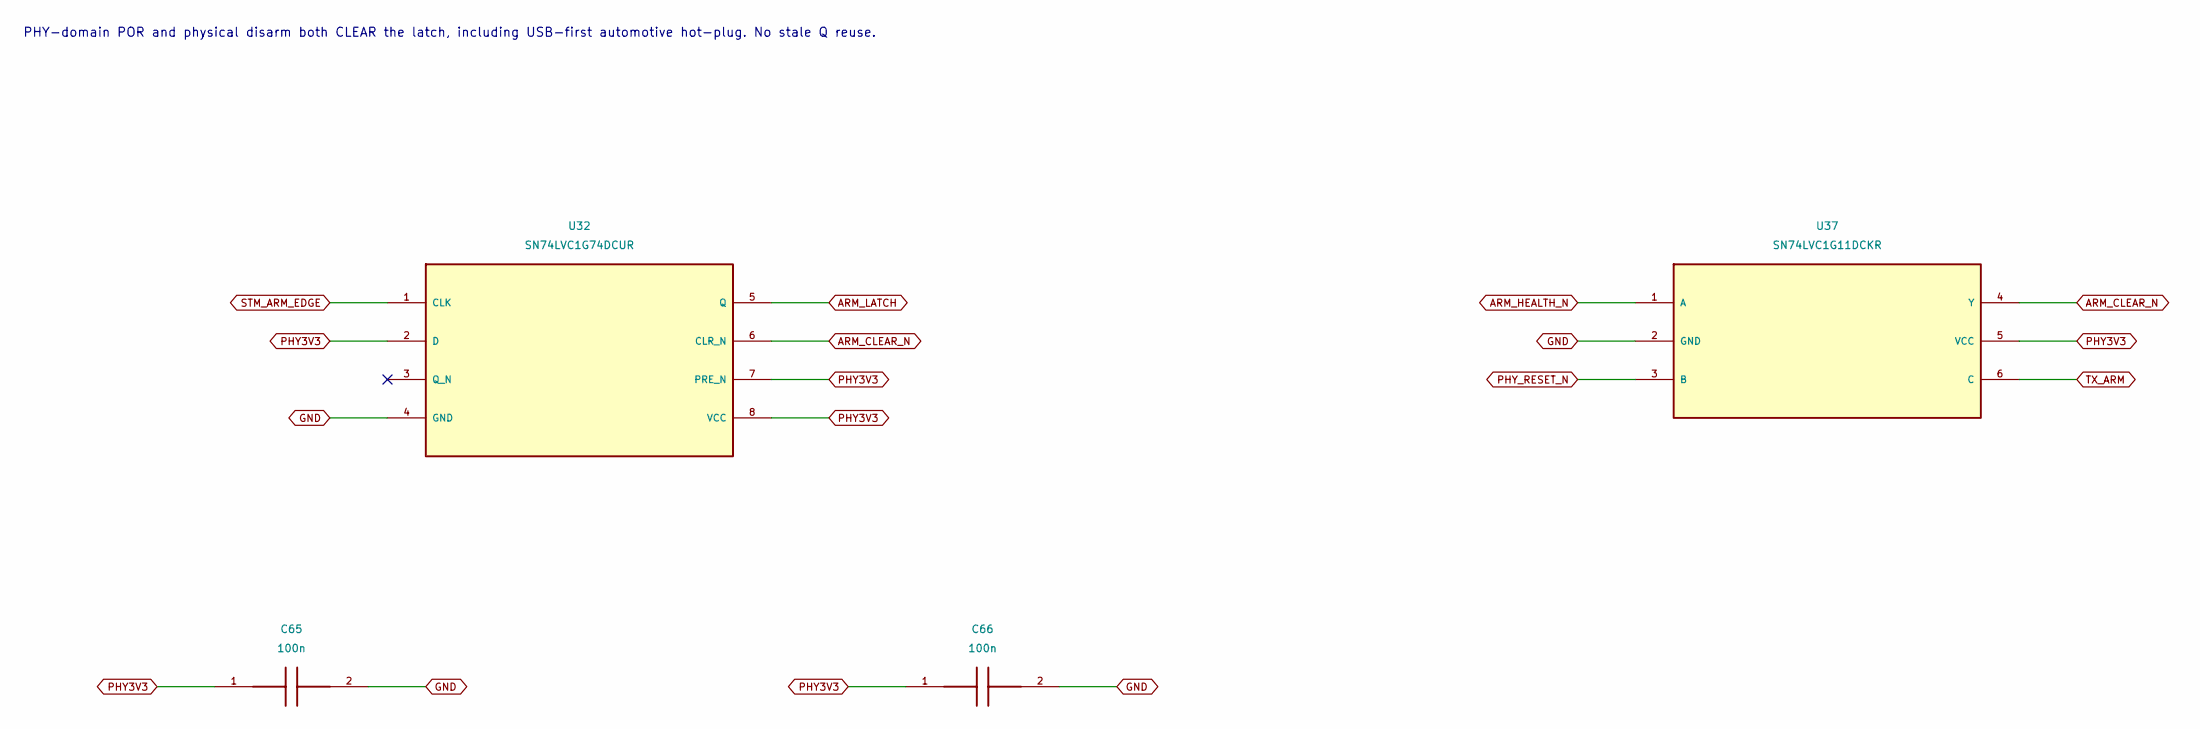
[picture p112: schematic 12b_latch_clear.kicad_sch]

Parts:
C65, C66: 100n; Capacitor_SMD__C_0402_1005Metric; MPN GEN-C-0402-100n-16V-X7R
U32: SN74LVC1G74DCUR; Package_SO__VSSOP-8_2.3x2mm_P0.5mm; MPN SN74LVC1G74DCUR
U37: SN74LVC1G11DCKR; Package_TO_SOT_SMD__SOT-363_SC-70-6; MPN SN74LVC1G11DCKR

Connections:
ARM_CLEAR_N: U32.6 (CLR_N), U37.4 (Y)
ARM_HEALTH_N: U37.1 (A)
ARM_LATCH: U32.5 (Q)
GND: C65.2, C66.2, U32.4 (GND), U37.2 (GND)
PHY3V3: C65.1, C66.1, U32.2 (D), U32.7 (PRE_N), U32.8 (VCC), U37.5 (VCC)
PHY_RESET_N: U37.3 (B)
STM_ARM_EDGE: U32.1 (CLK)
TX_ARM: U37.6 (C)

Notes on the sheet:
PHY-domain POR and physical disarm both CLEAR the latch, including USB-first automotive hot-plug. No stale Q reuse.
