digitie/canview/hardware/communicator/kicad/13_arm_switch.kicad_sch

## KiCad design hardware/communicator/kicad/13_arm_switch.kicad_sch (2026-09-06)

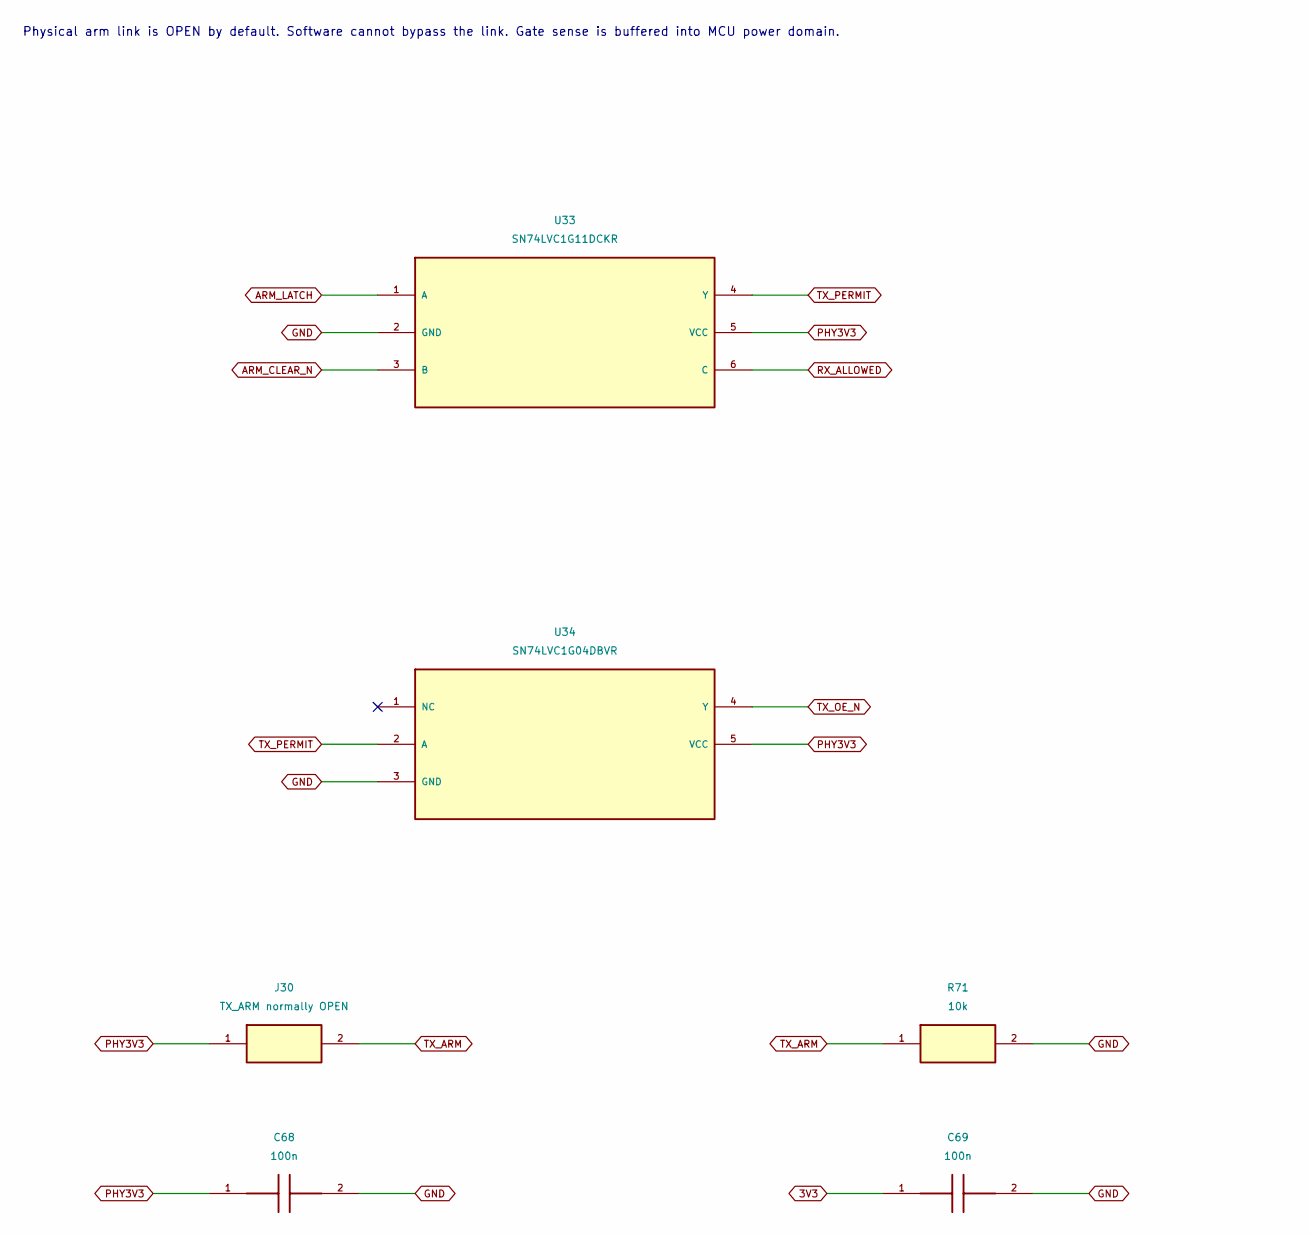
[picture p113: schematic 13_arm_switch.kicad_sch, part in row 1, column 1]

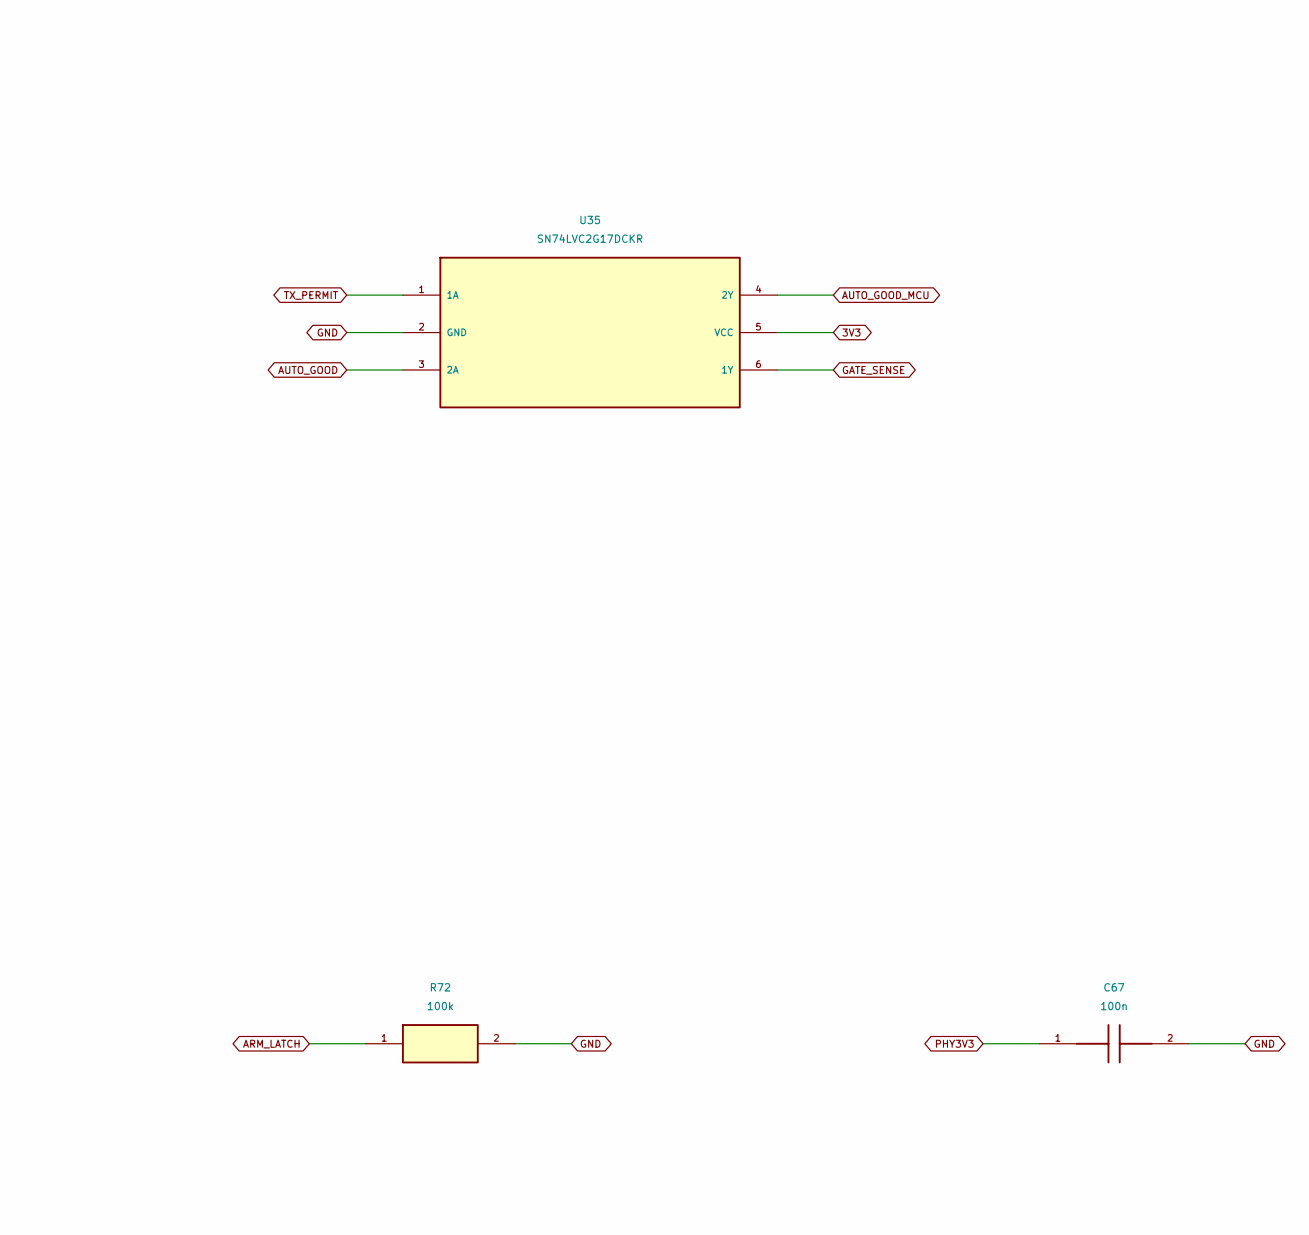
[picture p114: schematic 13_arm_switch.kicad_sch, part in row 1, column 2]

Parts:
C67, C68, C69: 100n; Capacitor_SMD__C_0402_1005Metric; MPN GEN-C-0402-100n-16V-X7R
J30: TX_ARM normally OPEN; Connector_PinHeader_1.27mm__PinHeader_1x02_P1.27mm_Vertical; MPN TX_ARM normally OPEN
R71: 10k; Resistor_SMD__R_0402_1005Metric; MPN GEN-R-0402-10k-1%
R72: 100k; Resistor_SMD__R_0402_1005Metric; MPN GEN-R-0402-100k-1%
U33: SN74LVC1G11DCKR; Package_TO_SOT_SMD__SOT-363_SC-70-6; MPN SN74LVC1G11DCKR
U34: SN74LVC1G04DBVR; Package_TO_SOT_SMD__SOT-23-5; MPN SN74LVC1G04DBVR
U35: SN74LVC2G17DCKR; Package_TO_SOT_SMD__SOT-363_SC-70-6; MPN SN74LVC2G17DCKR

Connections:
3V3: C69.1, U35.5 (VCC)
ARM_CLEAR_N: U33.3 (B)
ARM_LATCH: R72.1, U33.1 (A)
AUTO_GOOD: U35.3 (2A)
AUTO_GOOD_MCU: U35.4 (2Y)
GATE_SENSE: U35.6 (1Y)
GND: C67.2, C68.2, C69.2, R71.2, R72.2, U33.2 (GND), U34.3 (GND), U35.2 (GND)
PHY3V3: C67.1, C68.1, J30.1 (PHY3V3), U33.5 (VCC), U34.5 (VCC)
RX_ALLOWED: U33.6 (C)
TX_ARM: J30.2 (TX_ARM), R71.1
TX_OE_N: U34.4 (Y)
TX_PERMIT: U33.4 (Y), U34.2 (A), U35.1 (1A)

Notes on the sheet:
Physical arm link is OPEN by default. Software cannot bypass the link. Gate sense is buffered into MCU power domain.
