digitie/canview/hardware/communicator/kicad/14_can_connectors.kicad_sch

## KiCad design hardware/communicator/kicad/14_can_connectors.kicad_sch (2026-09-06)

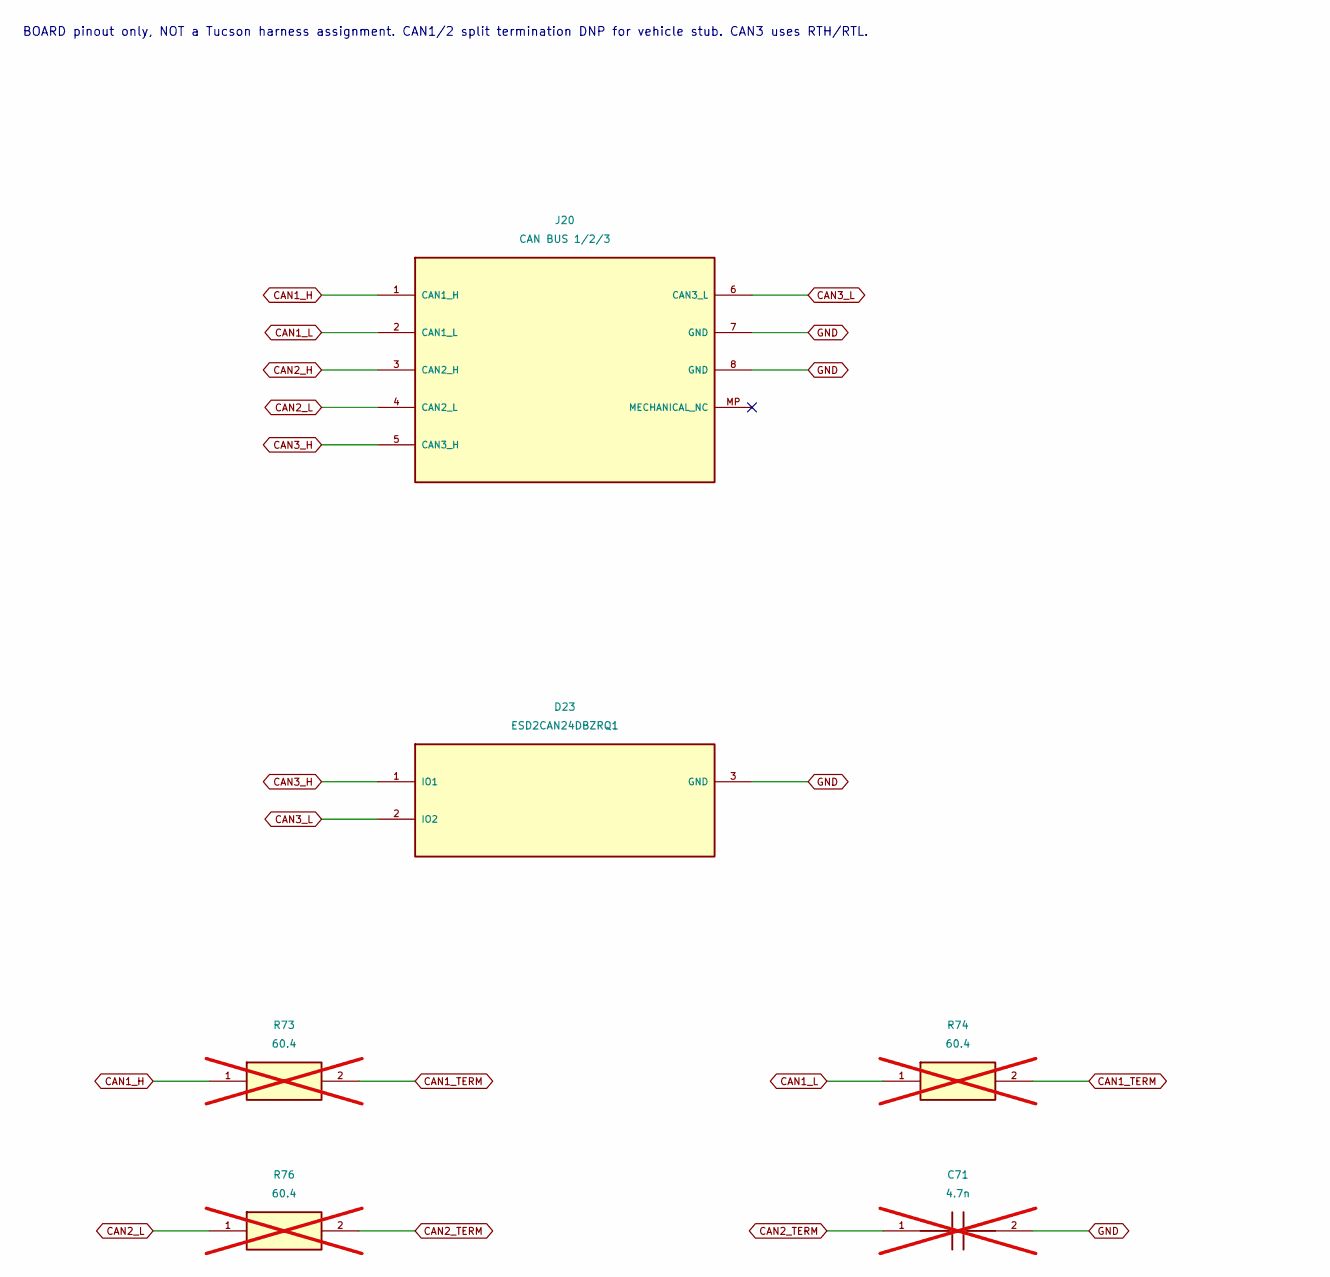
[picture p115: schematic 14_can_connectors.kicad_sch, part in row 1, column 1]

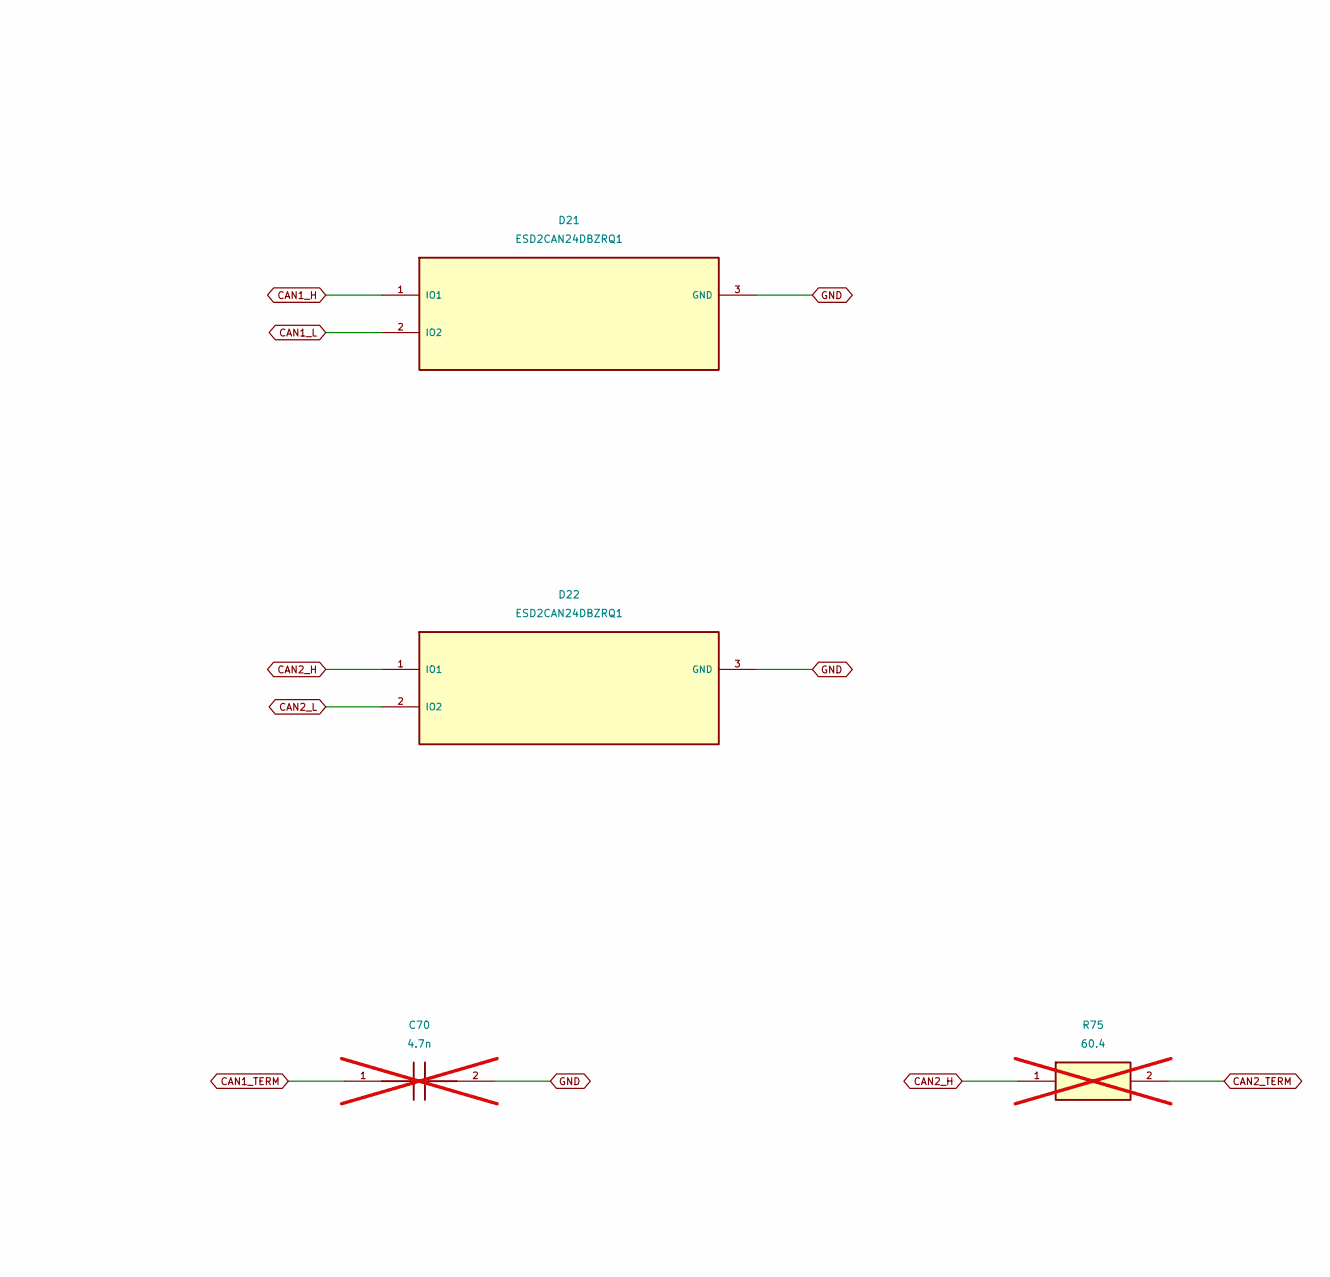
[picture p116: schematic 14_can_connectors.kicad_sch, part in row 1, column 2]

Parts:
C70, C71: 4.7n; Capacitor_SMD__C_0805_2012Metric; MPN GEN-C-0805-4.7n-100V-C0G; not fitted
D21, D22, D23: ESD2CAN24DBZRQ1; Package_TO_SOT_SMD__SOT-23; MPN ESD2CAN24DBZRQ1
J20: CAN BUS 1/2/3; Connector_JST__JST_GH_SM08B-GHS-TB_1x08-1MP_P1.25mm_Horizon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; MPN SM08B-GHS-TB(LF)(SN)
R73, R74, R75, R76: 60.4; Resistor_SMD__R_0805_2012Metric; MPN GEN-R-0805-60.4-1%; not fitted

Connections:
CAN1_H: D21.1 (IO1), J20.1 (CAN1_H), R73.1
CAN1_L: D21.2 (IO2), J20.2 (CAN1_L), R74.1
CAN1_TERM: C70.1, R73.2, R74.2
CAN2_H: D22.1 (IO1), J20.3 (CAN2_H), R75.1
CAN2_L: D22.2 (IO2), J20.4 (CAN2_L), R76.1
CAN2_TERM: C71.1, R75.2, R76.2
CAN3_H: D23.1 (IO1), J20.5 (CAN3_H)
CAN3_L: D23.2 (IO2), J20.6 (CAN3_L)
GND: C70.2, C71.2, D21.3 (GND), D22.3 (GND), D23.3 (GND), J20.7 (GND), J20.8 (GND)

Notes on the sheet:
BOARD pinout only, NOT a Tucson harness assignment. CAN1/2 split termination DNP for vehicle stub. CAN3 uses RTH/RTL.
