digitie/canview/hardware/communicator/kicad/15_gnss_ins.kicad_sch

## KiCad design hardware/communicator/kicad/15_gnss_ins.kicad_sch (2026-09-06)

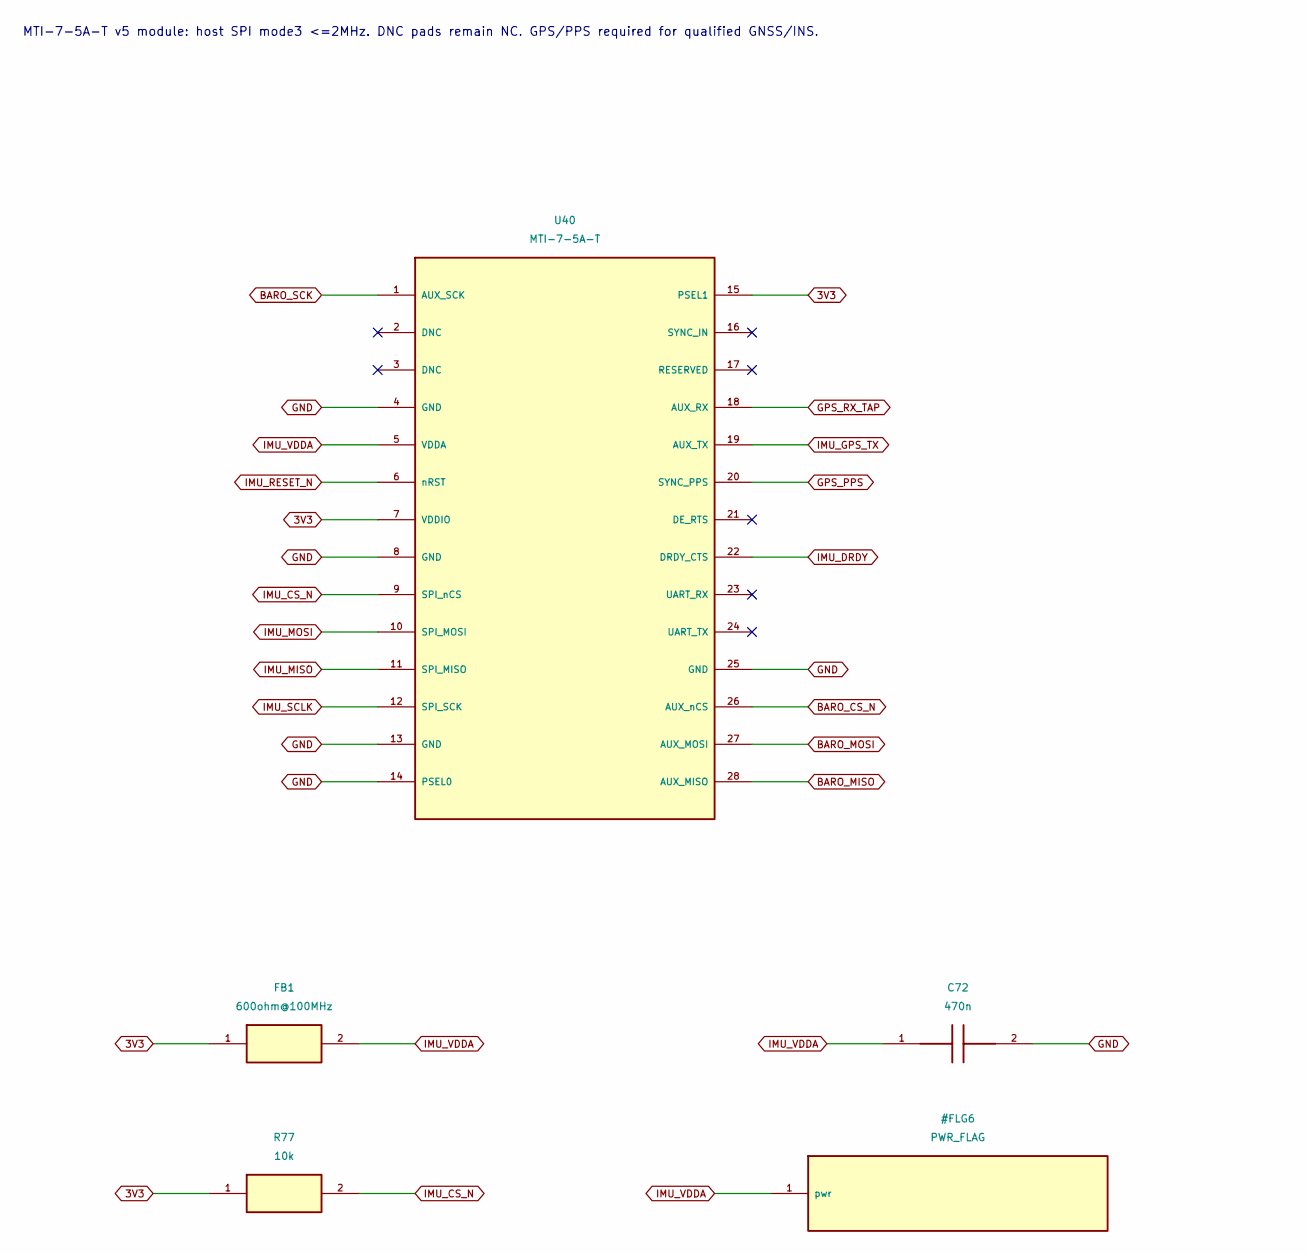
[picture p117: schematic 15_gnss_ins.kicad_sch, part in row 1, column 1]

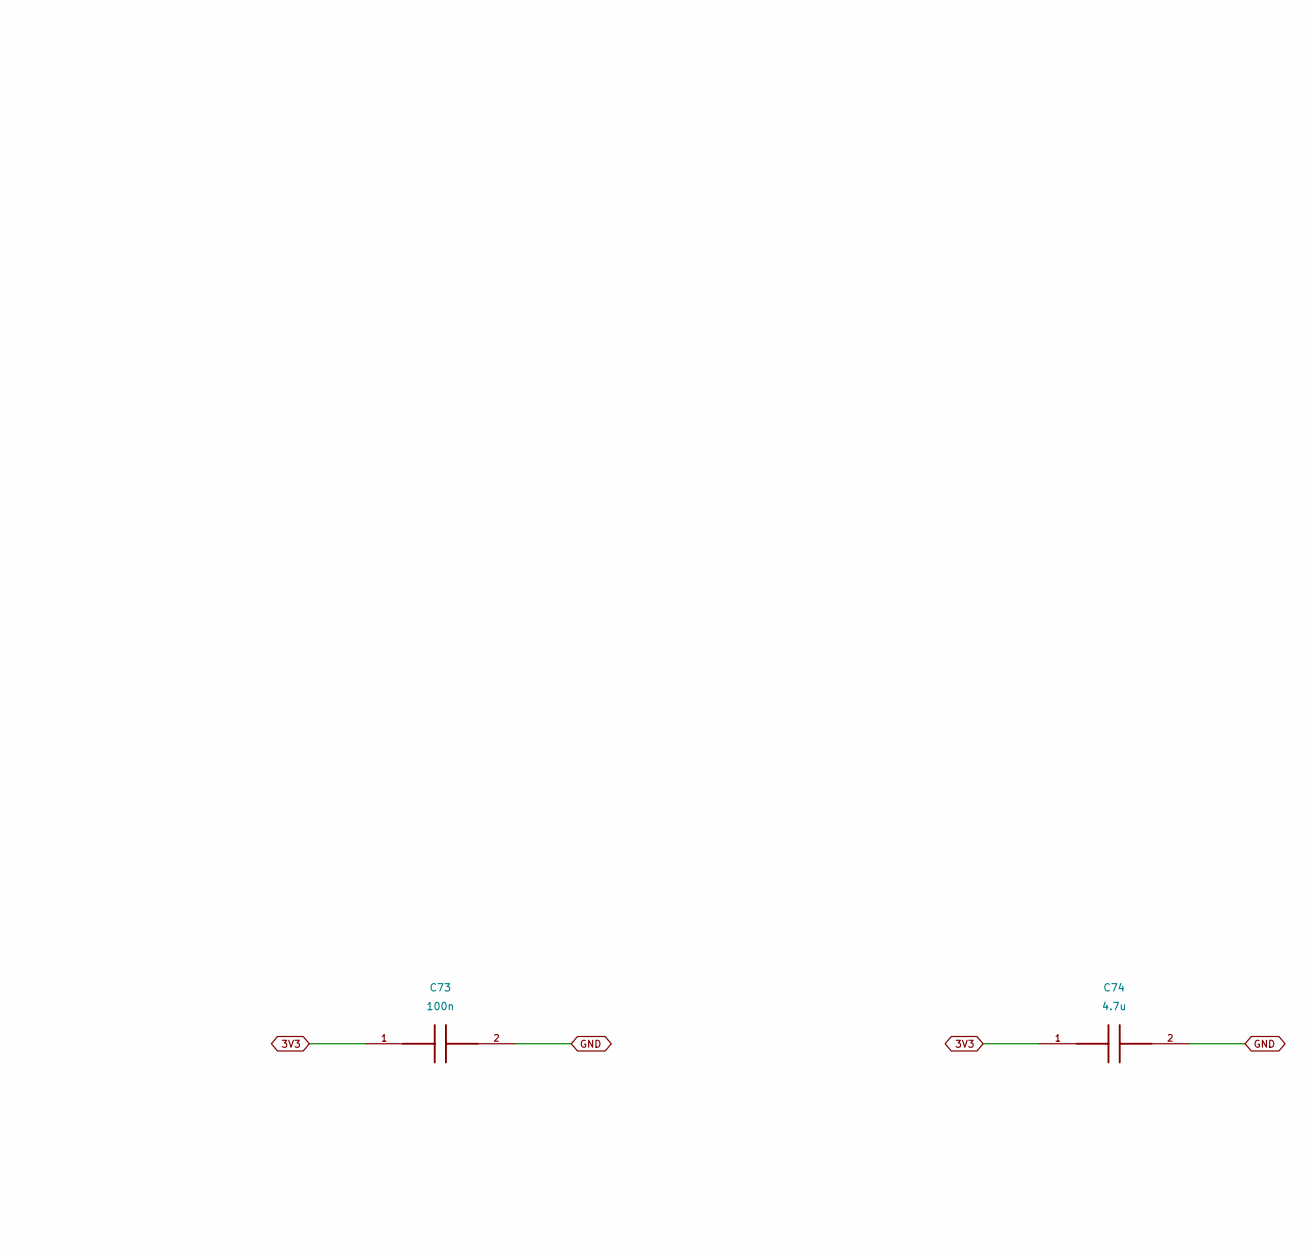
[picture p118: schematic 15_gnss_ins.kicad_sch, part in row 1, column 2]

Parts:
C72: 470n; Capacitor_SMD__C_0402_1005Metric; MPN GEN-C-0402-470n-16V-X7R
C73: 100n; Capacitor_SMD__C_0402_1005Metric; MPN GEN-C-0402-100n-16V-X7R
C74: 4.7u; Capacitor_SMD__C_0603_1608Metric; MPN GEN-C-0603-4.7u-16V-X7R
FB1: 600ohm@100MHz; Inductor_SMD__L_0402_1005Metric; MPN 74279279
R77: 10k; Resistor_SMD__R_0402_1005Metric; MPN GEN-R-0402-10k-1%
U40: MTI-7-5A-T; Xsens_MTi_1_series; MPN MTI-7-5A-T

Connections:
3V3: C73.1, C74.1, FB1.1, R77.1, U40.7 (VDDIO), U40.15 (PSEL1)
BARO_CS_N: U40.26 (AUX_nCS)
BARO_MISO: U40.28 (AUX_MISO)
BARO_MOSI: U40.27 (AUX_MOSI)
BARO_SCK: U40.1 (AUX_SCK)
GND: C72.2, C73.2, C74.2, U40.4 (GND), U40.8 (GND), U40.13 (GND), U40.14 (PSEL0), U40.25 (GND)
GPS_PPS: U40.20 (SYNC_PPS)
GPS_RX_TAP: U40.18 (AUX_RX)
IMU_CS_N: R77.2, U40.9 (SPI_nCS)
IMU_DRDY: U40.22 (DRDY_CTS)
IMU_GPS_TX: U40.19 (AUX_TX)
IMU_MISO: U40.11 (SPI_MISO)
IMU_MOSI: U40.10 (SPI_MOSI)
IMU_RESET_N: U40.6 (nRST)
IMU_SCLK: U40.12 (SPI_SCK)
IMU_VDDA: C72.1, FB1.2, U40.5 (VDDA)

Notes on the sheet:
MTI-7-5A-T v5 module: host SPI mode3 <=2MHz. DNC pads remain NC. GPS/PPS required for qualified GNSS/INS.
