digitie/canview/hardware/communicator/kicad/16_barometer.kicad_sch

## KiCad design hardware/communicator/kicad/16_barometer.kicad_sch (2026-09-06)

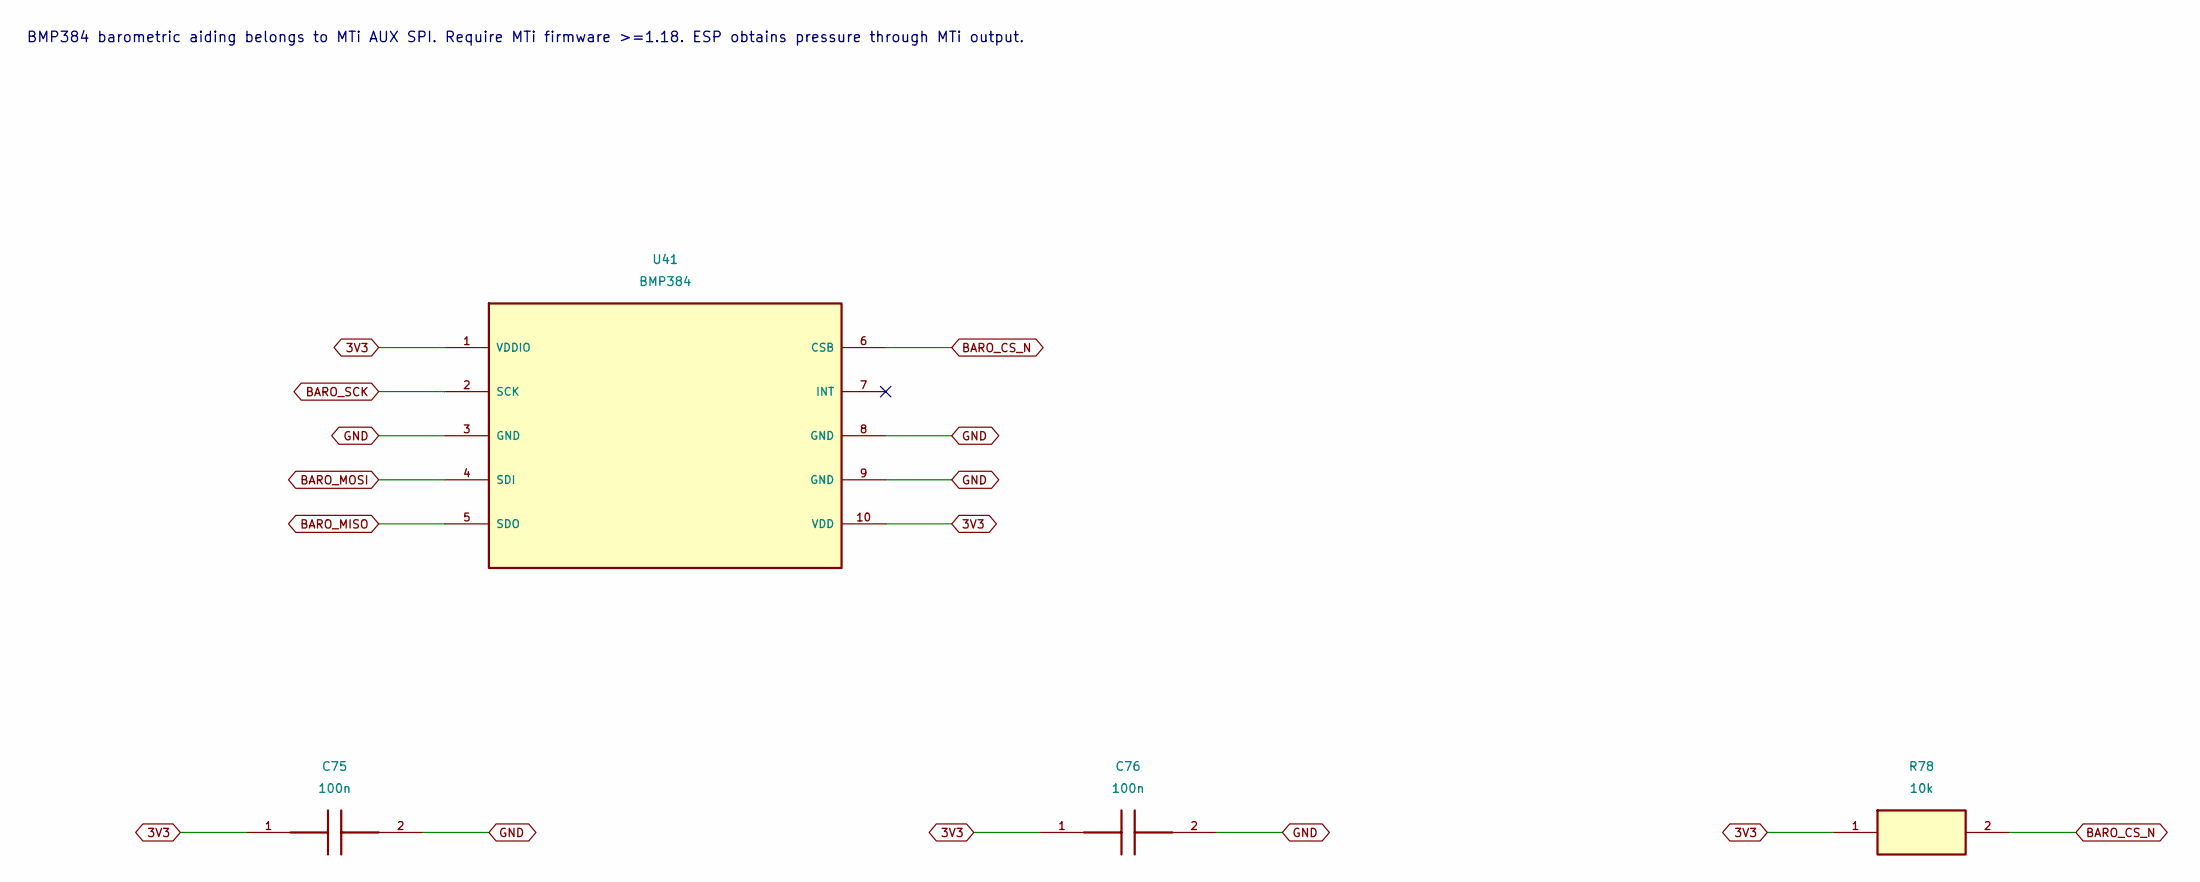
[picture p119: schematic 16_barometer.kicad_sch]

Parts:
C75, C76: 100n; Capacitor_SMD__C_0402_1005Metric; MPN GEN-C-0402-100n-16V-X7R
R78: 10k; Resistor_SMD__R_0402_1005Metric; MPN GEN-R-0402-10k-1%
U41: BMP384; Bosch_BMP384_LGA10; MPN BMP384

Connections:
3V3: C75.1, C76.1, R78.1, U41.1 (VDDIO), U41.10 (VDD)
BARO_CS_N: R78.2, U41.6 (CSB)
BARO_MISO: U41.5 (SDO)
BARO_MOSI: U41.4 (SDI)
BARO_SCK: U41.2 (SCK)
GND: C75.2, C76.2, U41.3 (GND), U41.8 (GND), U41.9 (GND)

Notes on the sheet:
BMP384 barometric aiding belongs to MTi AUX SPI. Require MTi firmware >=1.18. ESP obtains pressure through MTi output.
