digitie/canview/hardware/communicator/kicad/17_gps_ports.kicad_sch

## KiCad design hardware/communicator/kicad/17_gps_ports.kicad_sch (2026-09-06)

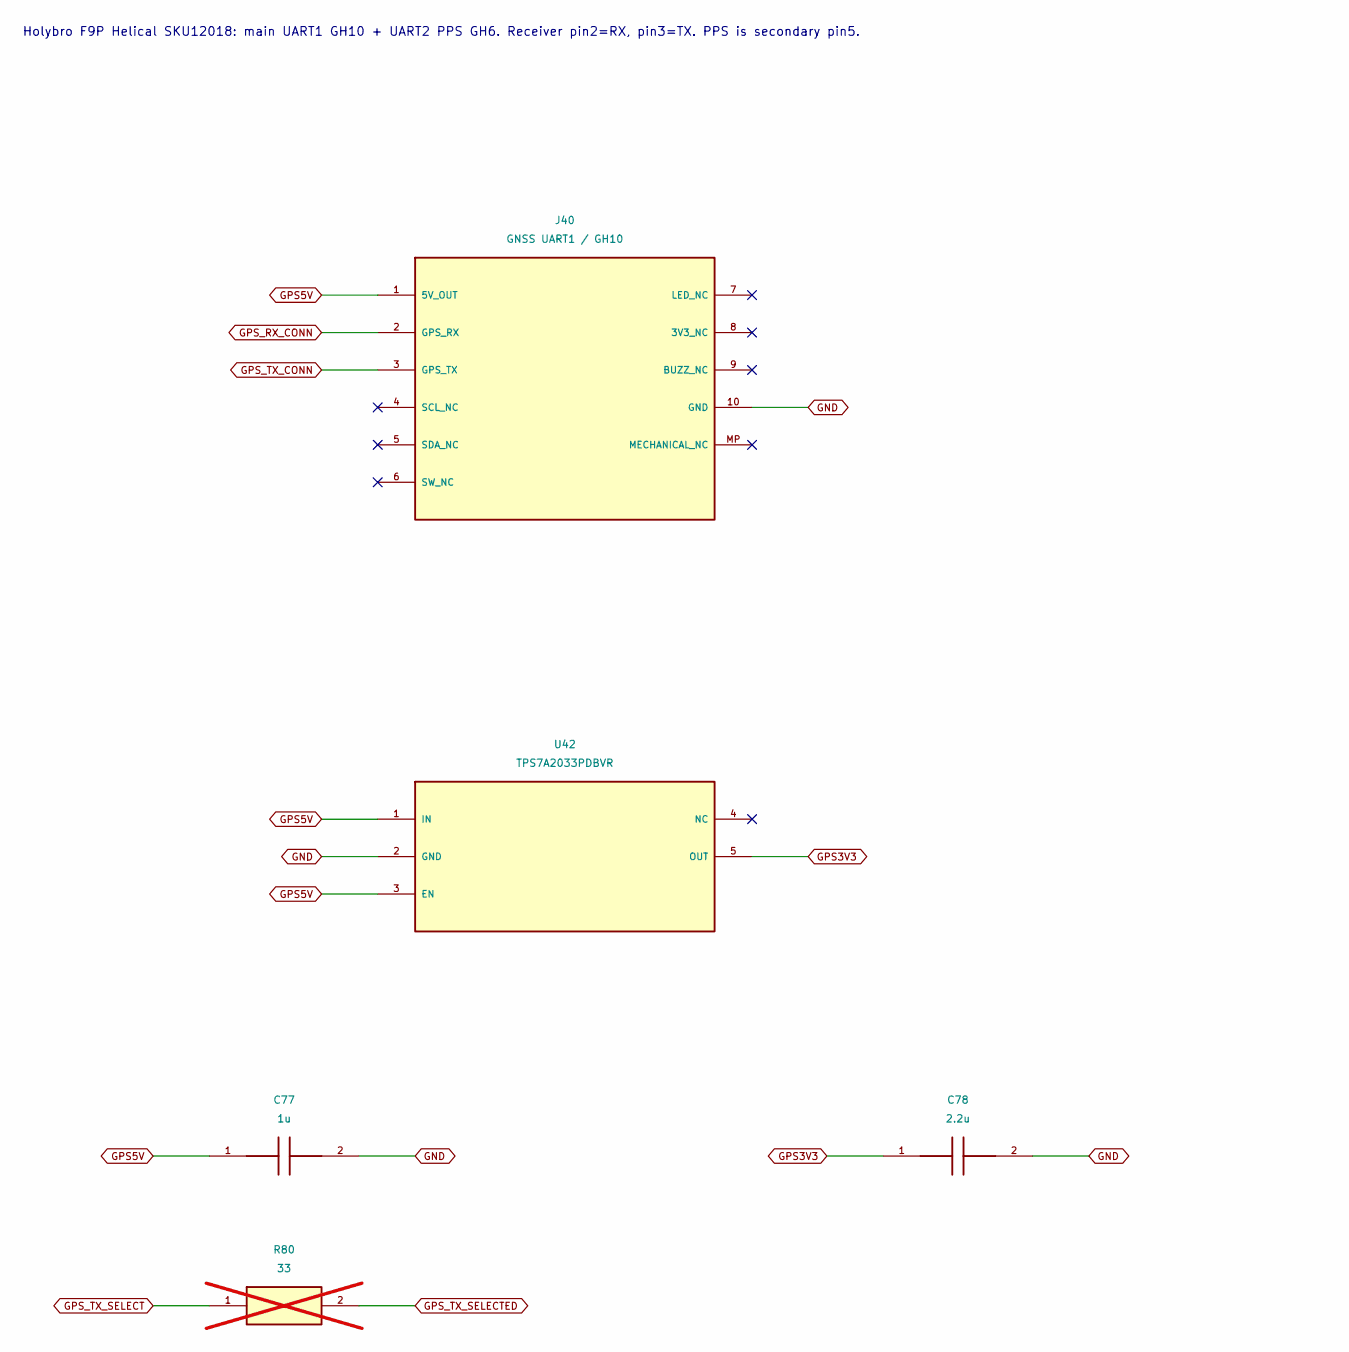
[picture p120: schematic 17_gps_ports.kicad_sch, part in row 1, column 1]

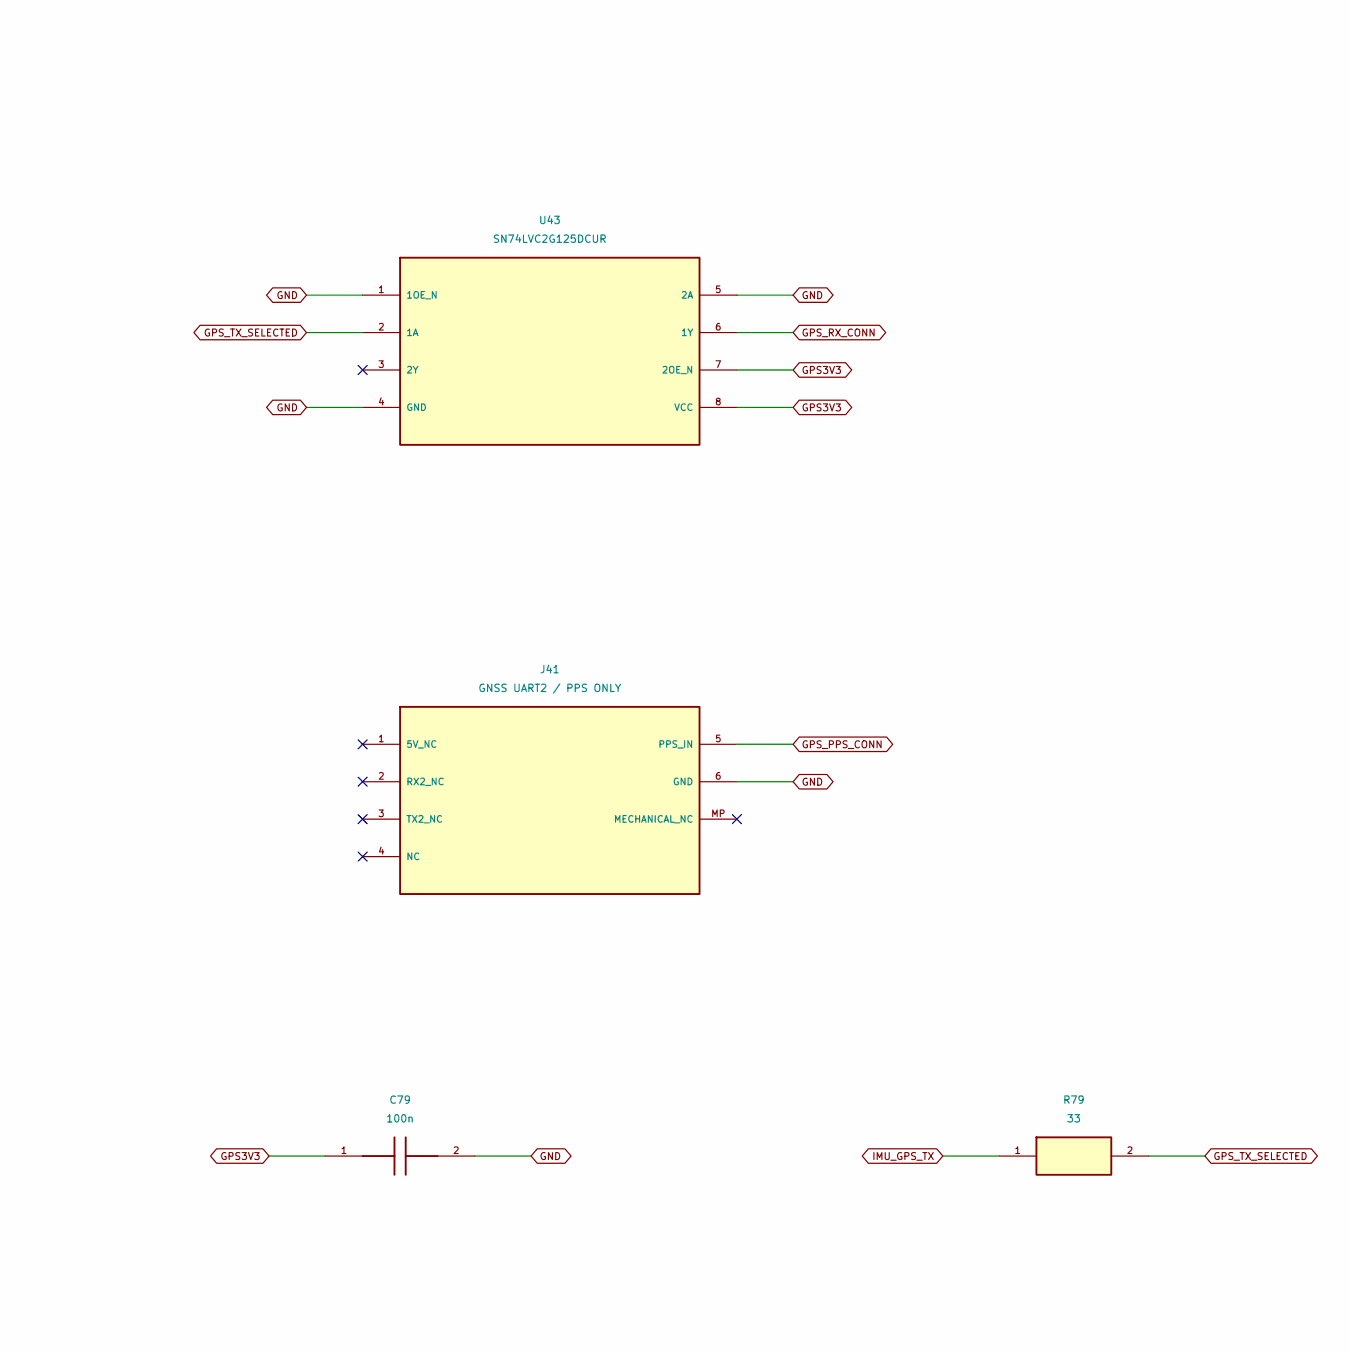
[picture p121: schematic 17_gps_ports.kicad_sch, part in row 1, column 2]

Parts:
C77: 1u; Capacitor_SMD__C_0603_1608Metric; MPN GEN-C-0603-1u-16V-X7R
C78: 2.2u; Capacitor_SMD__C_0603_1608Metric; MPN GEN-C-0603-2.2u-16V-X7R
C79: 100n; Capacitor_SMD__C_0402_1005Metric; MPN GEN-C-0402-100n-16V-X7R
J40: GNSS UART1 / GH10; Connector_JST__JST_GH_SM10B-GHS-TB_1x10-1MP_P1.25mm_Horizon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; MPN SM10B-GHS-TB(LF)(SN)
J41: GNSS UART2 / PPS ONLY; Connector_JST__JST_GH_SM06B-GHS-TB_1x06-1MP_P1.25mm_Horizon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; MPN SM06B-GHS-TB(LF)(SN)
R79: 33; Resistor_SMD__R_0402_1005Metric; MPN GEN-R-0402-33-1%
R80: 33; Resistor_SMD__R_0402_1005Metric; MPN GEN-R-0402-33-1%; not fitted
U42: TPS7A2033PDBVR; Package_TO_SOT_SMD__SOT-23-5; MPN TPS7A2033PDBVR
U43: SN74LVC2G125DCUR; Package_SO__VSSOP-8_2.3x2mm_P0.5mm; MPN SN74LVC2G125DCUR

Connections:
GND: C77.2, C78.2, C79.2, J40.10 (GND), J41.6 (GND), U42.2 (GND), U43.1 (1OE_N), U43.4 (GND), U43.5 (2A)
GPS3V3: C78.1, C79.1, U42.5 (OUT), U43.7 (2OE_N), U43.8 (VCC)
GPS5V: C77.1, J40.1 (5V_OUT), U42.1 (IN), U42.3 (EN)
GPS_PPS_CONN: J41.5 (PPS_IN)
GPS_RX_CONN: J40.2 (GPS_RX), U43.6 (1Y)
GPS_TX_CONN: J40.3 (GPS_TX)
GPS_TX_SELECT: R80.1
GPS_TX_SELECTED: R79.2, R80.2, U43.2 (1A)
IMU_GPS_TX: R79.1

Notes on the sheet:
Holybro F9P Helical SKU12018: main UART1 GH10 + UART2 PPS GH6. Receiver pin2=RX, pin3=TX. PPS is secondary pin5.
