digitie/canview/hardware/communicator/kicad/18_gps_protection.kicad_sch

## KiCad design hardware/communicator/kicad/18_gps_protection.kicad_sch (2026-09-06)

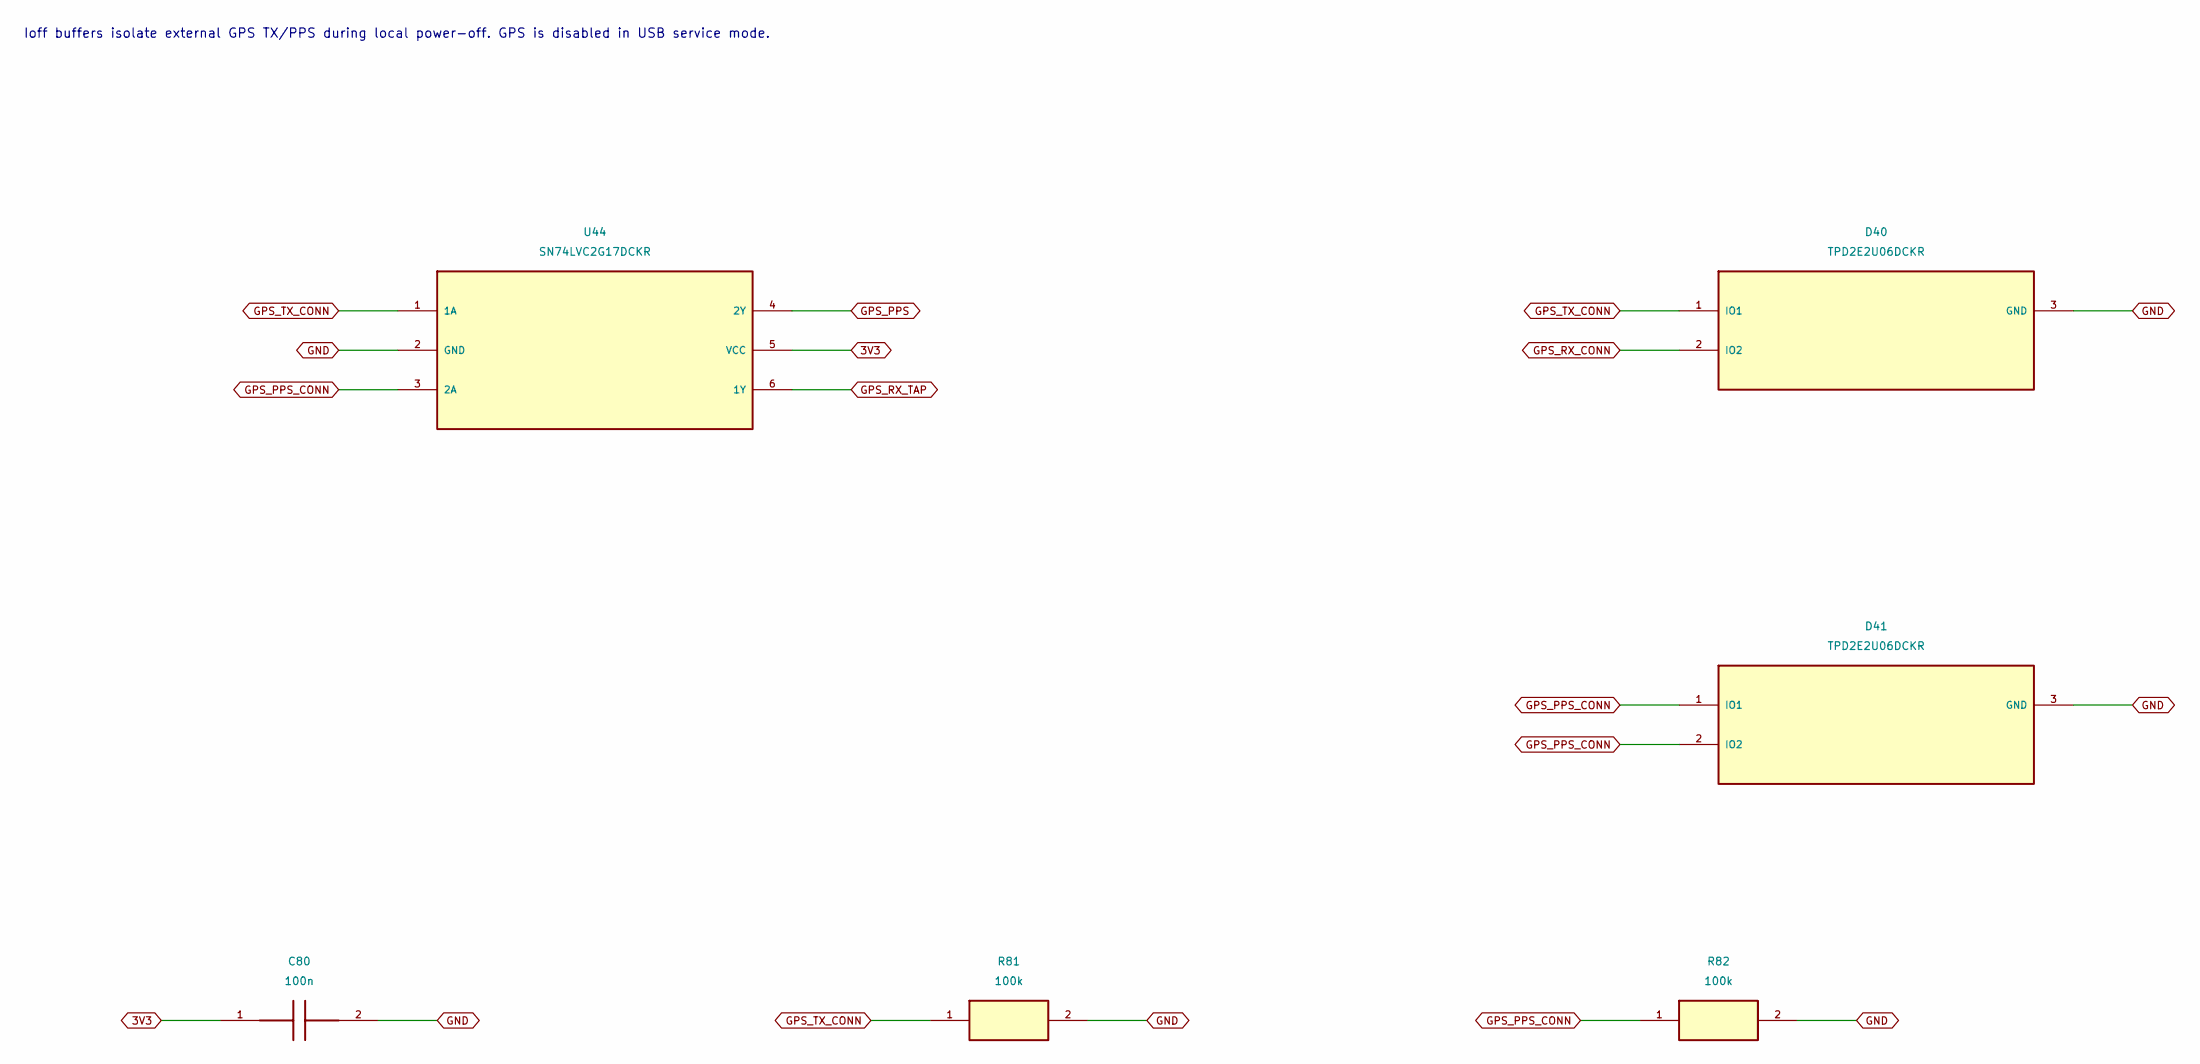
[picture p122: schematic 18_gps_protection.kicad_sch]

Parts:
C80: 100n; Capacitor_SMD__C_0402_1005Metric; MPN GEN-C-0402-100n-16V-X7R
D40, D41: TPD2E2U06DCKR; Package_TO_SOT_SMD__SOT-323_SC-70; MPN TPD2E2U06DCKR
R81, R82: 100k; Resistor_SMD__R_0402_1005Metric; MPN GEN-R-0402-100k-1%
U44: SN74LVC2G17DCKR; Package_TO_SOT_SMD__SOT-363_SC-70-6; MPN SN74LVC2G17DCKR

Connections:
3V3: C80.1, U44.5 (VCC)
GND: C80.2, D40.3 (GND), D41.3 (GND), R81.2, R82.2, U44.2 (GND)
GPS_PPS: U44.4 (2Y)
GPS_PPS_CONN: D41.1 (IO1), D41.2 (IO2), R82.1, U44.3 (2A)
GPS_RX_CONN: D40.2 (IO2)
GPS_RX_TAP: U44.6 (1Y)
GPS_TX_CONN: D40.1 (IO1), R81.1, U44.1 (1A)

Notes on the sheet:
Ioff buffers isolate external GPS TX/PPS during local power-off. GPS is disabled in USB service mode.
