digitie/canview/hardware/communicator/kicad/19_gps_power.kicad_sch

## KiCad design hardware/communicator/kicad/19_gps_power.kicad_sch (2026-09-06)

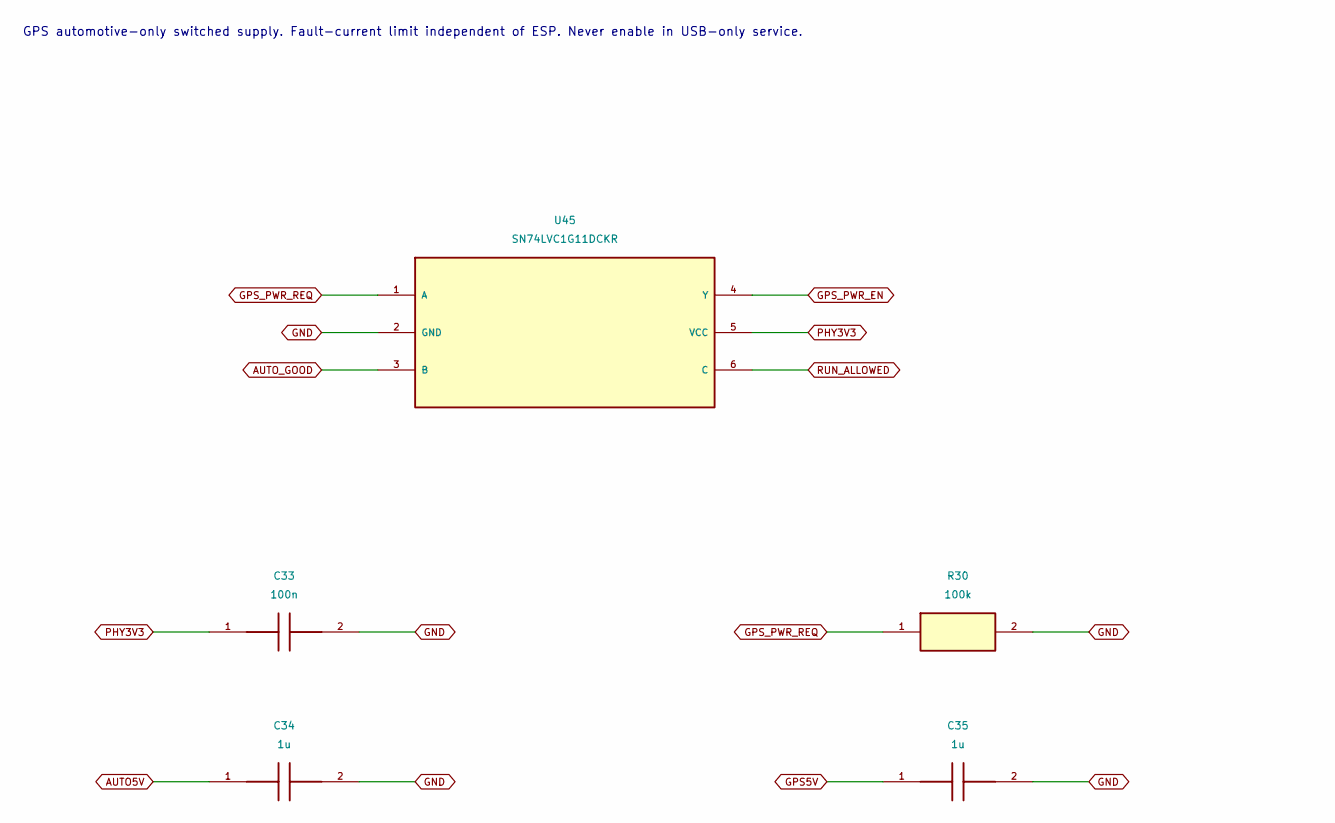
[picture p123: schematic 19_gps_power.kicad_sch, part in row 1, column 1]

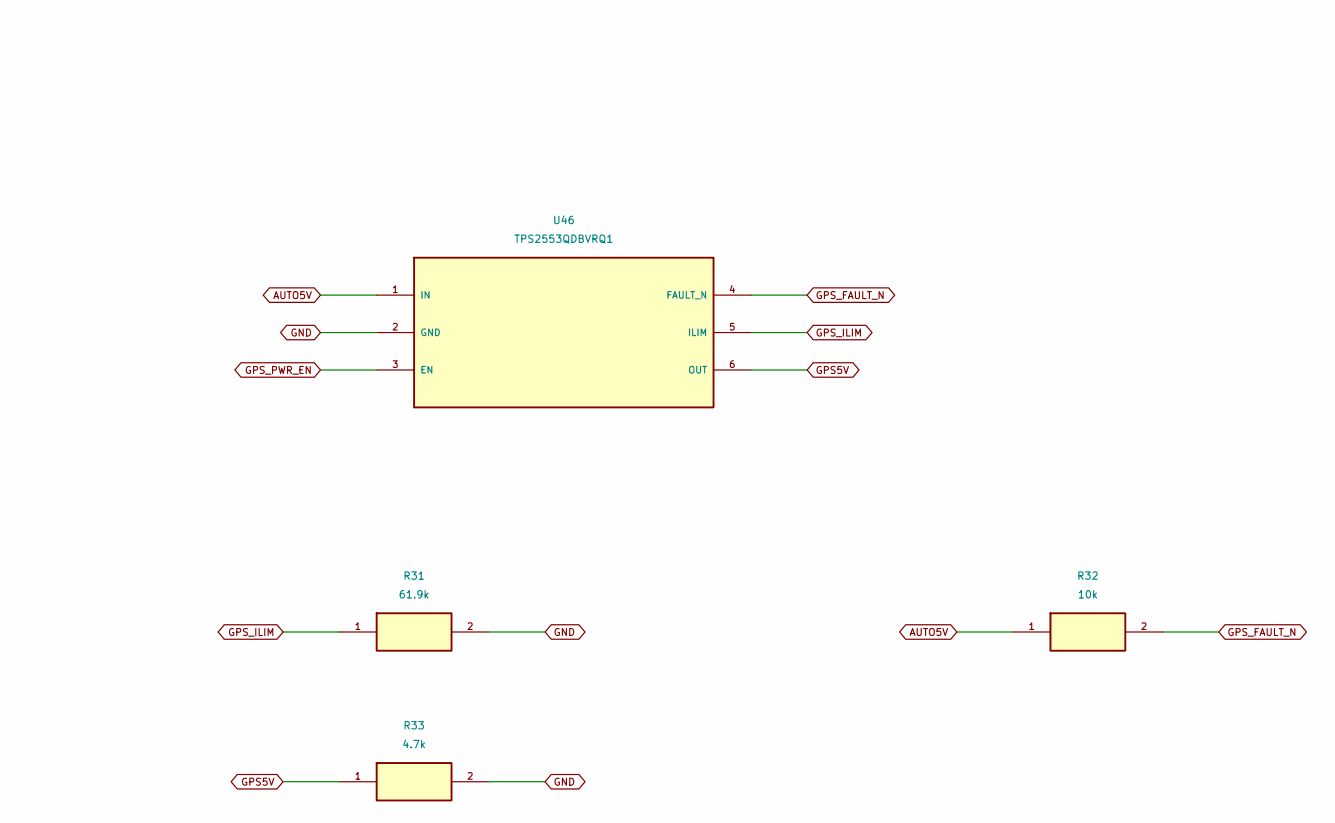
[picture p124: schematic 19_gps_power.kicad_sch, part in row 1, column 2]

Parts:
C33: 100n; Capacitor_SMD__C_0402_1005Metric; MPN GEN-C-0402-100n-16V-X7R
C34, C35: 1u; Capacitor_SMD__C_0603_1608Metric; MPN GEN-C-0603-1u-16V-X7R
R30: 100k; Resistor_SMD__R_0402_1005Metric; MPN GEN-R-0402-100k-1%
R31: 61.9k; Resistor_SMD__R_0402_1005Metric; MPN GEN-R-0402-61.9k-1%
R32: 10k; Resistor_SMD__R_0402_1005Metric; MPN GEN-R-0402-10k-1%
R33: 4.7k; Resistor_SMD__R_0402_1005Metric; MPN GEN-R-0402-4.7k-1%
U45: SN74LVC1G11DCKR; Package_TO_SOT_SMD__SOT-363_SC-70-6; MPN SN74LVC1G11DCKR
U46: TPS2553QDBVRQ1; Package_TO_SOT_SMD__SOT-23-6; MPN TPS2553QDBVRQ1

Connections:
AUTO5V: C34.1, R32.1, U46.1 (IN)
AUTO_GOOD: U45.3 (B)
GND: C33.2, C34.2, C35.2, R30.2, R31.2, R33.2, U45.2 (GND), U46.2 (GND)
GPS5V: C35.1, R33.1, U46.6 (OUT)
GPS_FAULT_N: R32.2, U46.4 (FAULT_N)
GPS_ILIM: R31.1, U46.5 (ILIM)
GPS_PWR_EN: U45.4 (Y), U46.3 (EN)
GPS_PWR_REQ: R30.1, U45.1 (A)
PHY3V3: C33.1, U45.5 (VCC)
RUN_ALLOWED: U45.6 (C)

Notes on the sheet:
GPS automotive-only switched supply. Fault-current limit independent of ESP. Never enable in USB-only service.
