digitie/canview/hardware/communicator/kicad/20_test_points.kicad_sch

## KiCad design hardware/communicator/kicad/20_test_points.kicad_sch (2026-09-06)

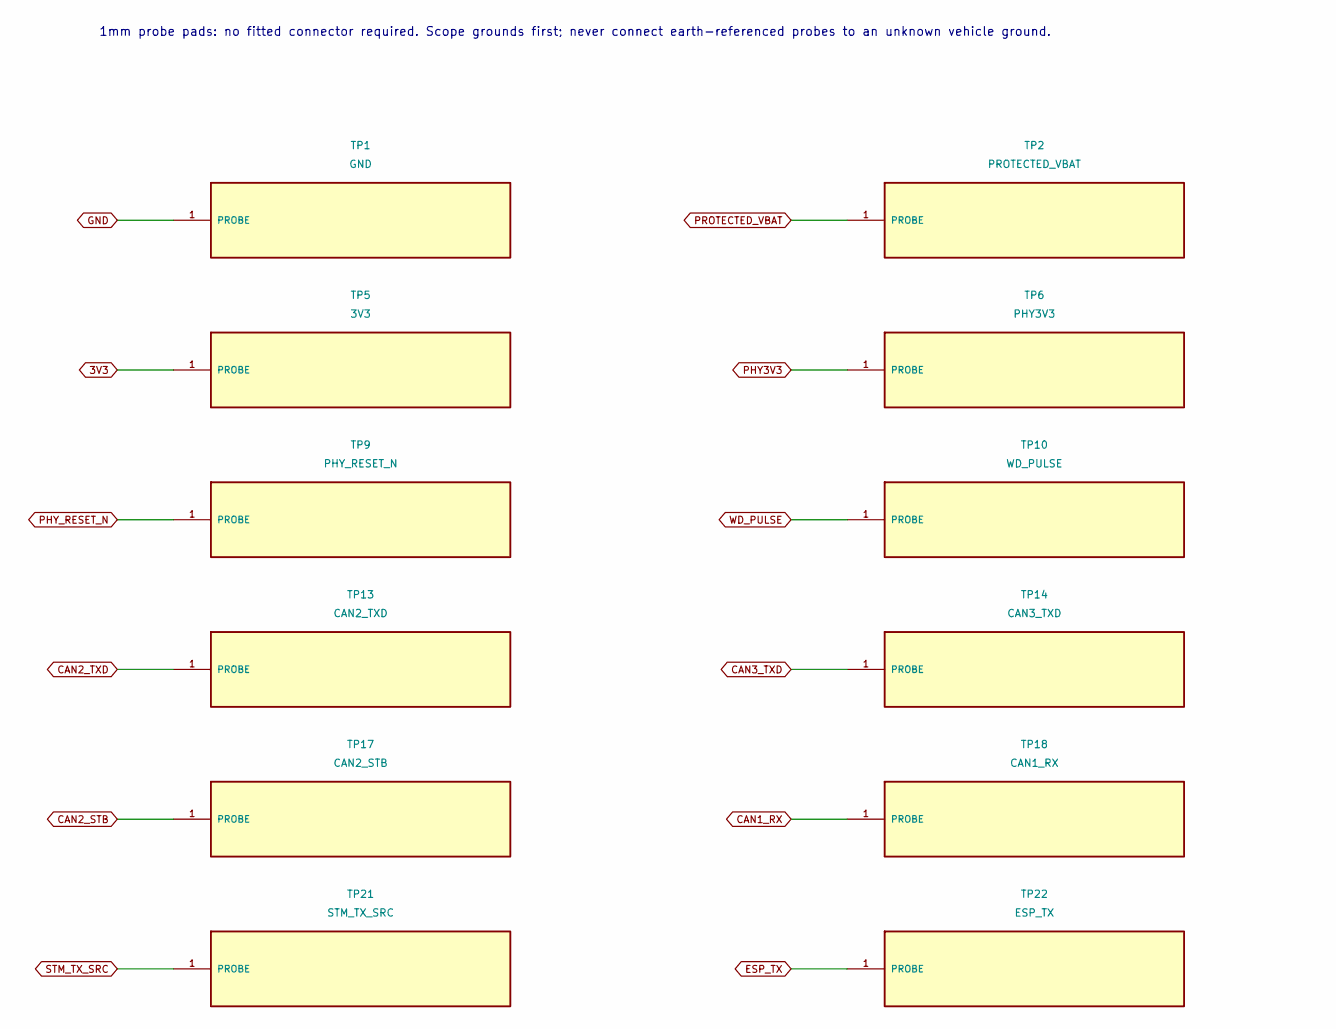
[picture p125: schematic 20_test_points.kicad_sch, part in row 1, column 1]

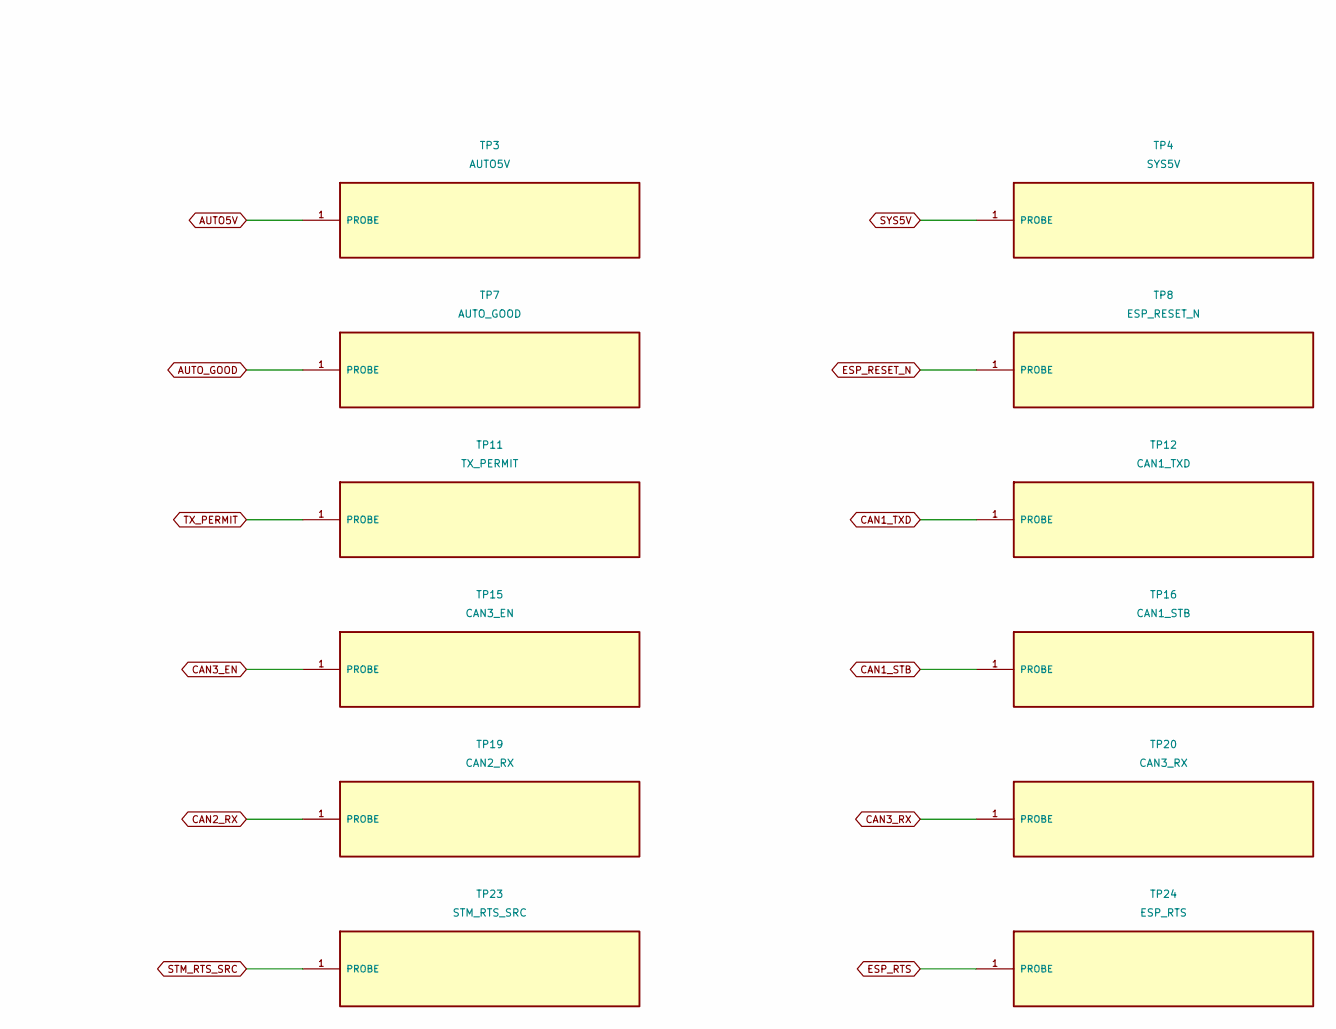
[picture p126: schematic 20_test_points.kicad_sch, part in row 1, column 2]

Parts:
TP1: GND; TestPoint__TestPoint_Pad_D1.0mm; MPN PCB-PAD-1MM
TP2: PROTECTED_VBAT; TestPoint__TestPoint_Pad_D1.0mm; MPN PCB-PAD-1MM
TP3: AUTO5V; TestPoint__TestPoint_Pad_D1.0mm; MPN PCB-PAD-1MM
TP4: SYS5V; TestPoint__TestPoint_Pad_D1.0mm; MPN PCB-PAD-1MM
TP5: 3V3; TestPoint__TestPoint_Pad_D1.0mm; MPN PCB-PAD-1MM
TP6: PHY3V3; TestPoint__TestPoint_Pad_D1.0mm; MPN PCB-PAD-1MM
TP7: AUTO_GOOD; TestPoint__TestPoint_Pad_D1.0mm; MPN PCB-PAD-1MM
TP8: ESP_RESET_N; TestPoint__TestPoint_Pad_D1.0mm; MPN PCB-PAD-1MM
TP9: PHY_RESET_N; TestPoint__TestPoint_Pad_D1.0mm; MPN PCB-PAD-1MM
TP10: WD_PULSE; TestPoint__TestPoint_Pad_D1.0mm; MPN PCB-PAD-1MM
TP11: TX_PERMIT; TestPoint__TestPoint_Pad_D1.0mm; MPN PCB-PAD-1MM
TP12: CAN1_TXD; TestPoint__TestPoint_Pad_D1.0mm; MPN PCB-PAD-1MM
TP13: CAN2_TXD; TestPoint__TestPoint_Pad_D1.0mm; MPN PCB-PAD-1MM
TP14: CAN3_TXD; TestPoint__TestPoint_Pad_D1.0mm; MPN PCB-PAD-1MM
TP15: CAN3_EN; TestPoint__TestPoint_Pad_D1.0mm; MPN PCB-PAD-1MM
TP16: CAN1_STB; TestPoint__TestPoint_Pad_D1.0mm; MPN PCB-PAD-1MM
TP17: CAN2_STB; TestPoint__TestPoint_Pad_D1.0mm; MPN PCB-PAD-1MM
TP18: CAN1_RX; TestPoint__TestPoint_Pad_D1.0mm; MPN PCB-PAD-1MM
TP19: CAN2_RX; TestPoint__TestPoint_Pad_D1.0mm; MPN PCB-PAD-1MM
TP20: CAN3_RX; TestPoint__TestPoint_Pad_D1.0mm; MPN PCB-PAD-1MM
TP21: STM_TX_SRC; TestPoint__TestPoint_Pad_D1.0mm; MPN PCB-PAD-1MM
TP22: ESP_TX; TestPoint__TestPoint_Pad_D1.0mm; MPN PCB-PAD-1MM
TP23: STM_RTS_SRC; TestPoint__TestPoint_Pad_D1.0mm; MPN PCB-PAD-1MM
TP24: ESP_RTS; TestPoint__TestPoint_Pad_D1.0mm; MPN PCB-PAD-1MM

Connections:
3V3: TP5.1
AUTO5V: TP3.1
AUTO_GOOD: TP7.1
CAN1_RX: TP18.1
CAN1_STB: TP16.1
CAN1_TXD: TP12.1
CAN2_RX: TP19.1
CAN2_STB: TP17.1
CAN2_TXD: TP13.1
CAN3_EN: TP15.1
CAN3_RX: TP20.1
CAN3_TXD: TP14.1
ESP_RESET_N: TP8.1
ESP_RTS: TP24.1
ESP_TX: TP22.1
GND: TP1.1
PHY3V3: TP6.1
PHY_RESET_N: TP9.1
PROTECTED_VBAT: TP2.1
STM_RTS_SRC: TP23.1
STM_TX_SRC: TP21.1
SYS5V: TP4.1
TX_PERMIT: TP11.1
WD_PULSE: TP10.1

Notes on the sheet:
1mm probe pads: no fitted connector required. Scope grounds first; never connect earth-referenced probes to an unknown vehicle ground.
