digitie/canview/hardware/communicator/kicad/21_ota_reset.kicad_sch

## KiCad design hardware/communicator/kicad/21_ota_reset.kicad_sch (2026-09-06)

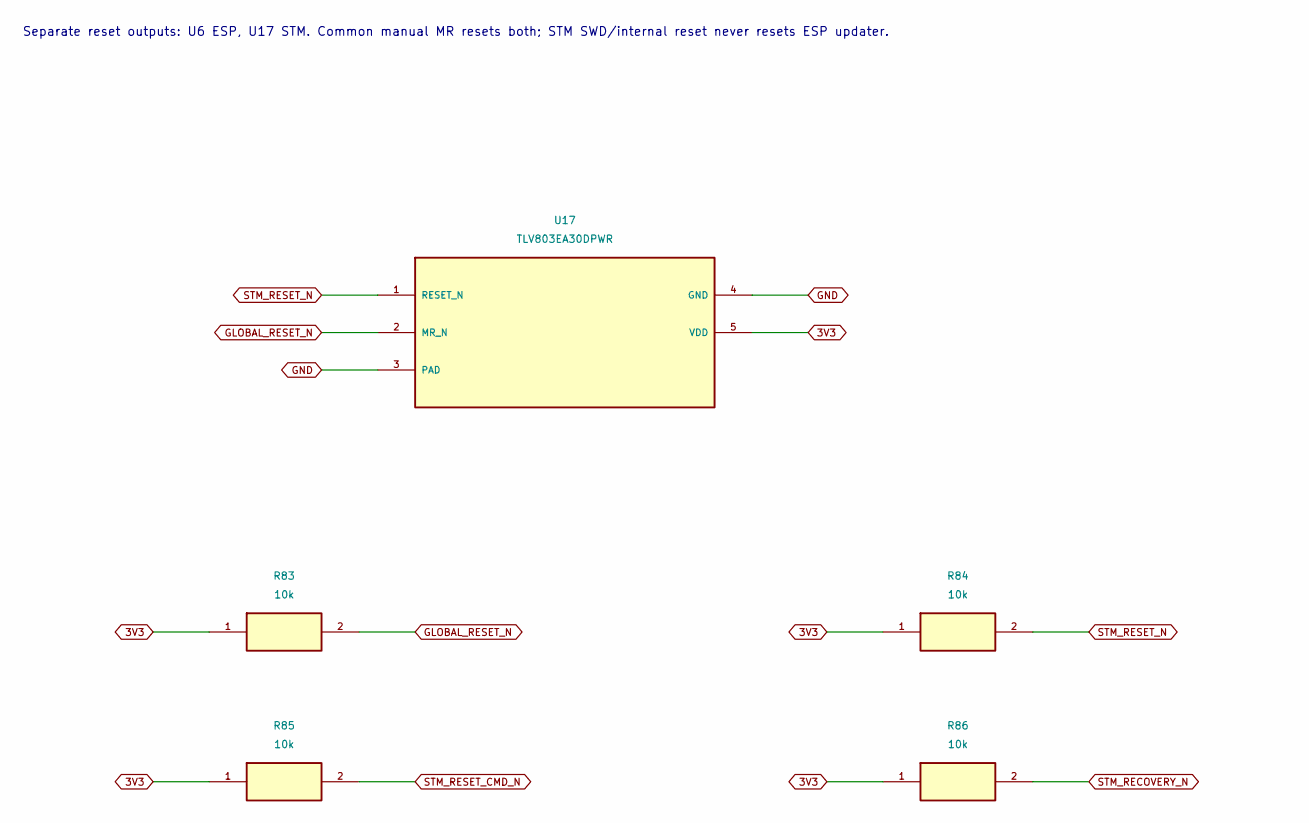
[picture p127: schematic 21_ota_reset.kicad_sch, part in row 1, column 1]

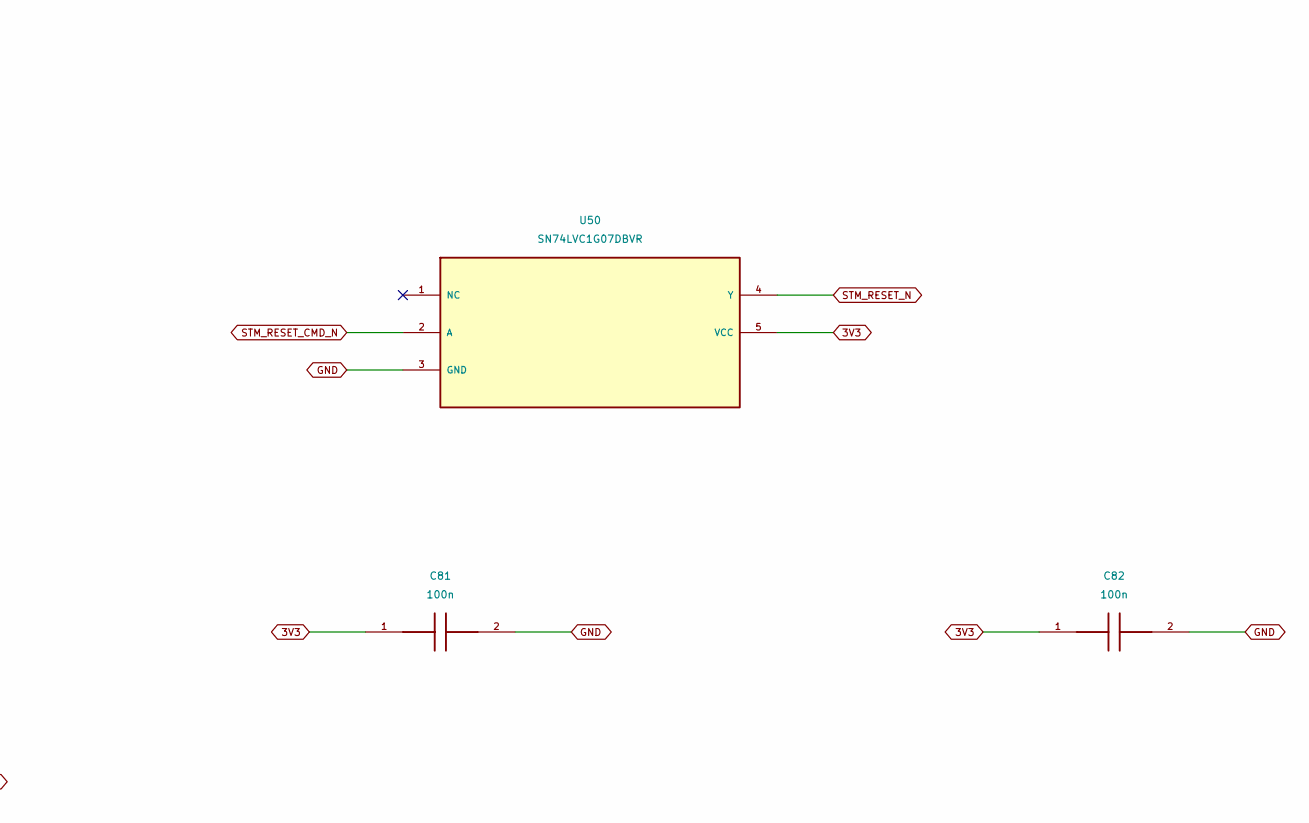
[picture p128: schematic 21_ota_reset.kicad_sch, part in row 1, column 2]

Parts:
C81, C82: 100n; Capacitor_SMD__C_0402_1005Metric; MPN GEN-C-0402-100n-16V-X7R
R83, R84, R85, R86: 10k; Resistor_SMD__R_0402_1005Metric; MPN GEN-R-0402-10k-1%
U17: TLV803EA30DPWR; Package_SON__Texas_X2SON-5_0.8x0.8mm_P0.48mm; MPN TLV803EA30DPWR
U50: SN74LVC1G07DBVR; Package_TO_SOT_SMD__SOT-23-5; MPN SN74LVC1G07DBVR

Connections:
3V3: C81.1, C82.1, R83.1, R84.1, R85.1, R86.1, U17.5 (VDD), U50.5 (VCC)
GLOBAL_RESET_N: R83.2, U17.2 (MR_N)
GND: C81.2, C82.2, U17.3 (PAD), U17.4 (GND), U50.3 (GND)
STM_RECOVERY_N: R86.2
STM_RESET_CMD_N: R85.2, U50.2 (A)
STM_RESET_N: R84.2, U17.1 (RESET_N), U50.4 (Y)

Notes on the sheet:
Separate reset outputs: U6 ESP, U17 STM. Common manual MR resets both; STM SWD/internal reset never resets ESP updater.
