digitie/canview/hardware/communicator/kicad/22_ota_interlock.kicad_sch

## KiCad design hardware/communicator/kicad/22_ota_interlock.kicad_sch (2026-09-06)

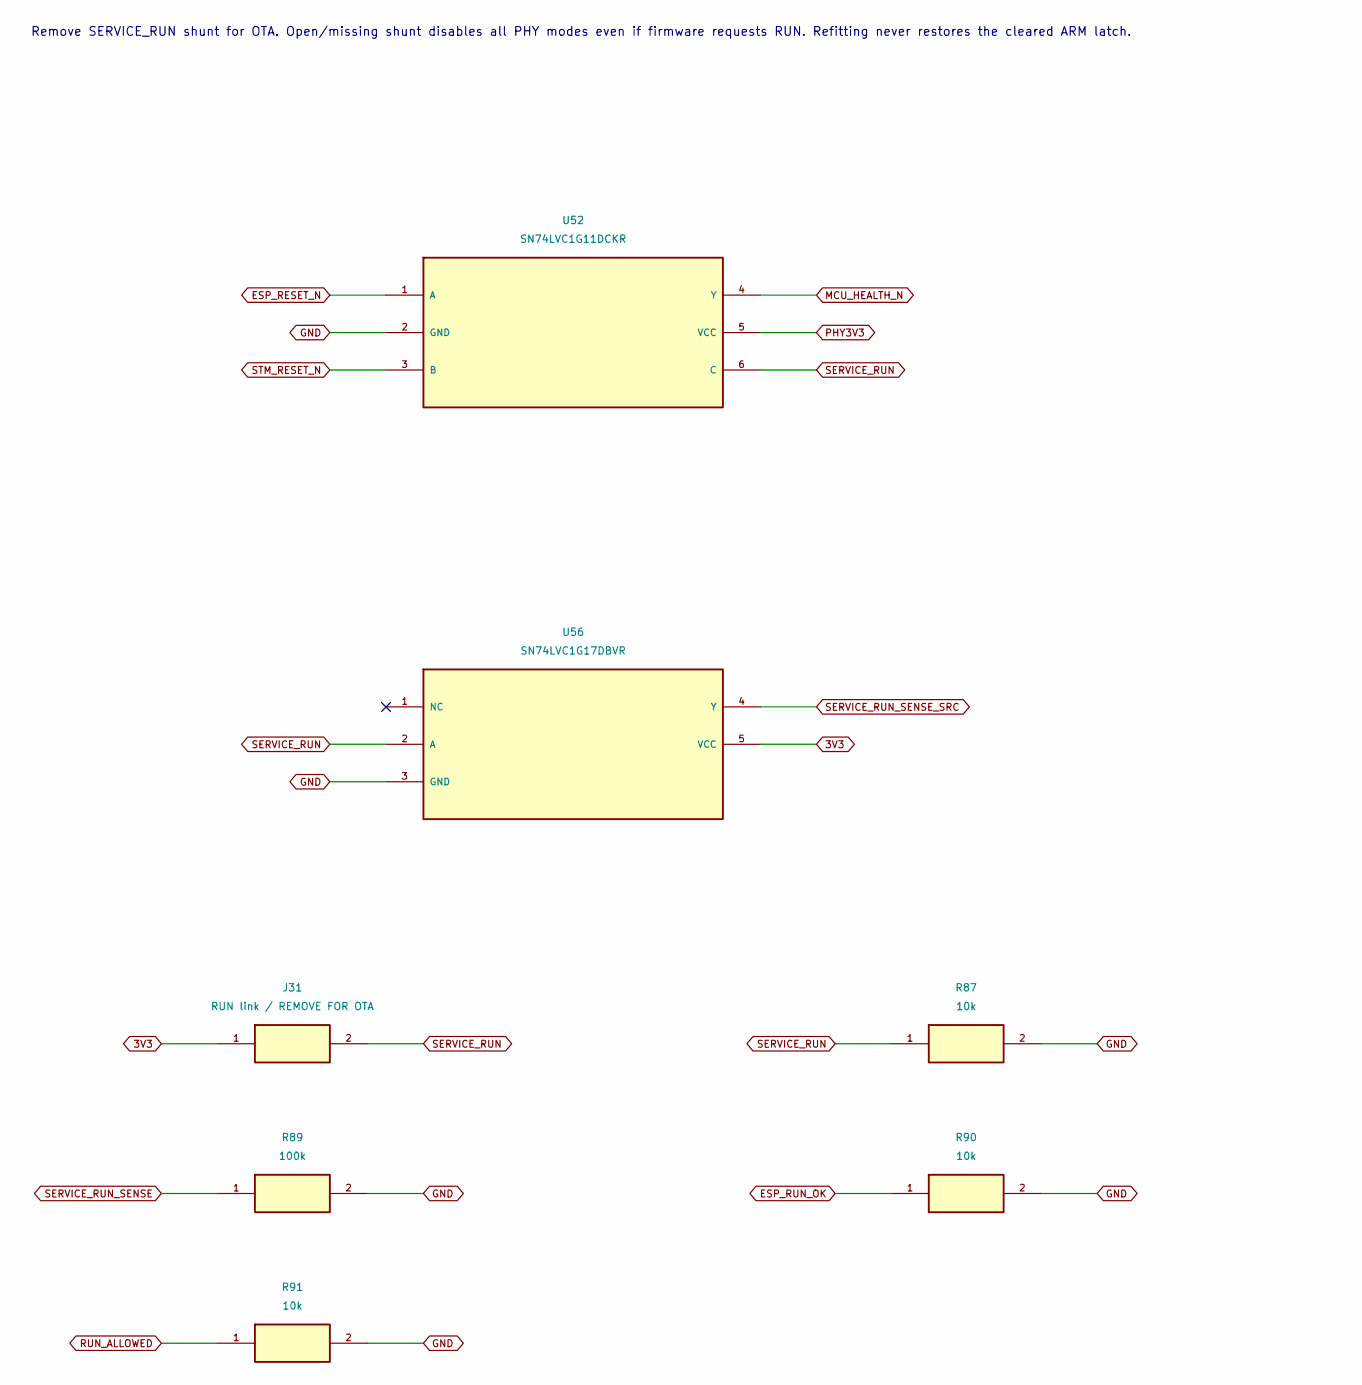
[picture p129: schematic 22_ota_interlock.kicad_sch, part in row 1, column 1]

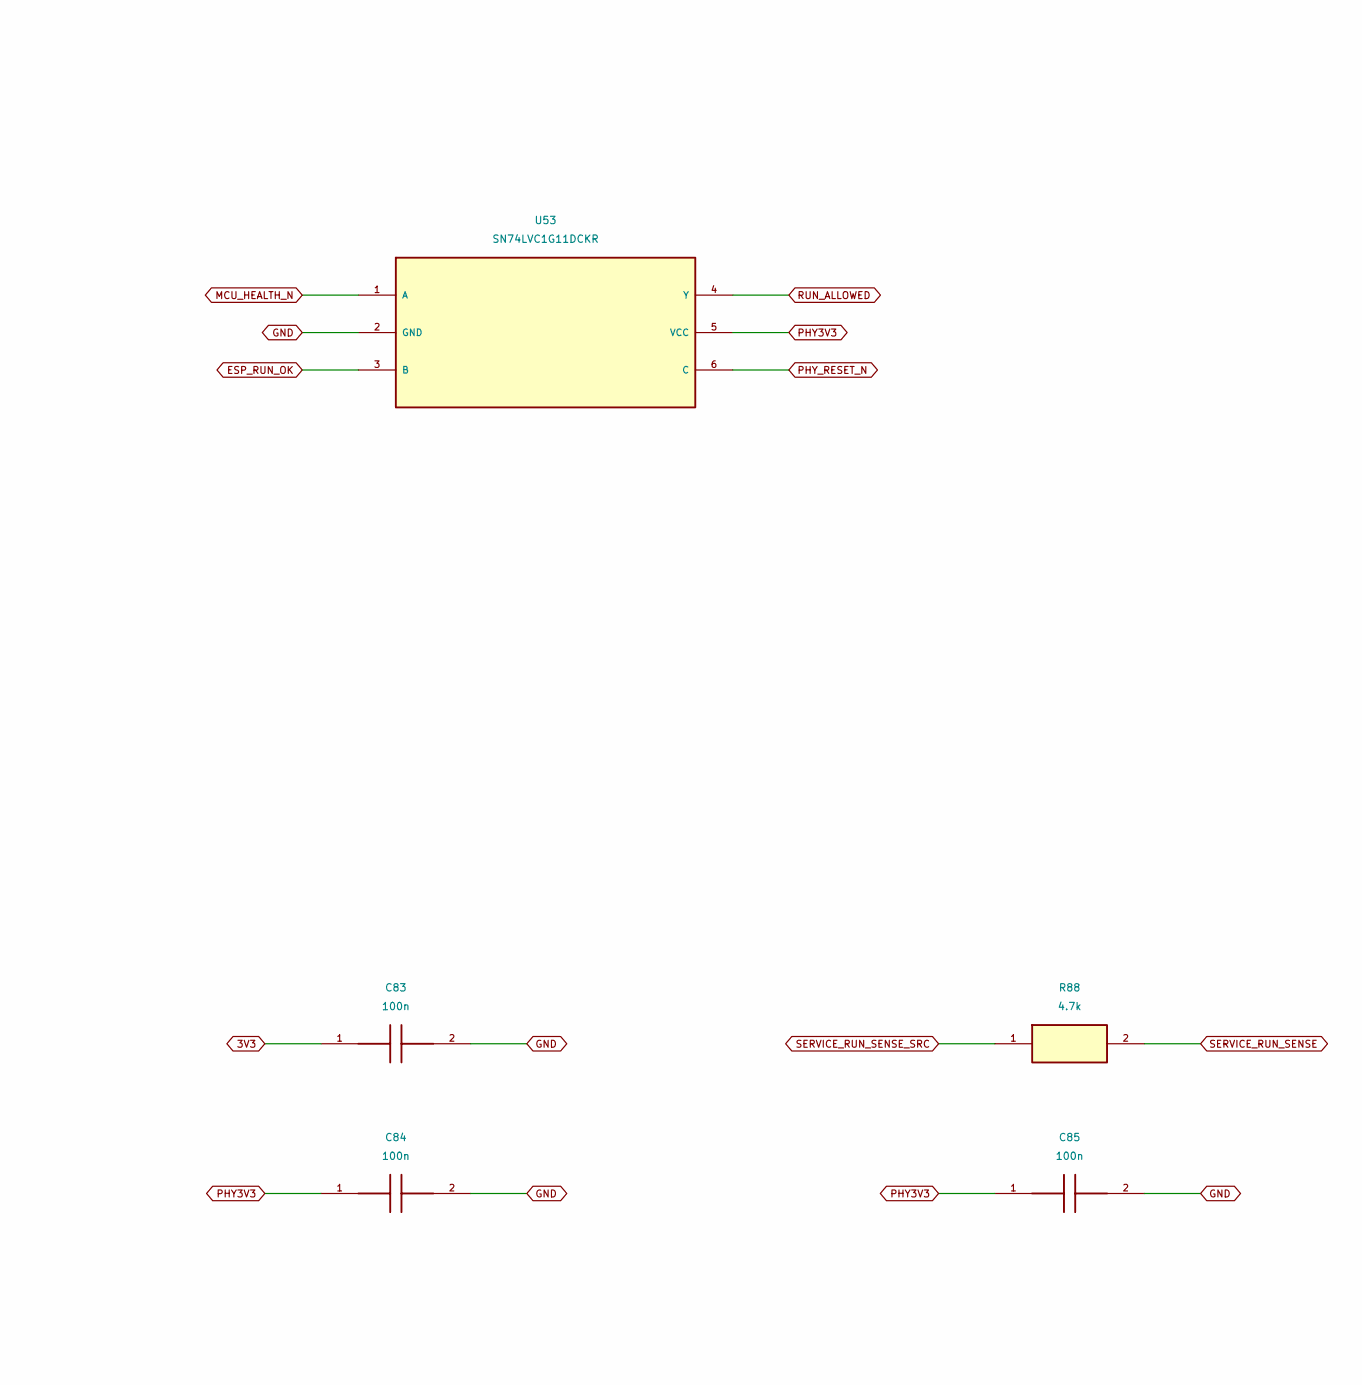
[picture p130: schematic 22_ota_interlock.kicad_sch, part in row 1, column 2]

Parts:
C83, C84, C85: 100n; Capacitor_SMD__C_0402_1005Metric; MPN GEN-C-0402-100n-16V-X7R
J31: RUN link / REMOVE FOR OTA; Connector_PinHeader_1.27mm__PinHeader_1x02_P1.27mm_Vertical; MPN RUN link / REMOVE FOR OTA
R87, R90, R91: 10k; Resistor_SMD__R_0402_1005Metric; MPN GEN-R-0402-10k-1%
R88: 4.7k; Resistor_SMD__R_0402_1005Metric; MPN GEN-R-0402-4.7k-1%
R89: 100k; Resistor_SMD__R_0402_1005Metric; MPN GEN-R-0402-100k-1%
U52, U53: SN74LVC1G11DCKR; Package_TO_SOT_SMD__SOT-363_SC-70-6; MPN SN74LVC1G11DCKR
U56: SN74LVC1G17DBVR; Package_TO_SOT_SMD__SOT-23-5; MPN SN74LVC1G17DBVR

Connections:
3V3: C83.1, J31.1 (3V3), U56.5 (VCC)
ESP_RESET_N: U52.1 (A)
ESP_RUN_OK: R90.1, U53.3 (B)
GND: C83.2, C84.2, C85.2, R87.2, R89.2, R90.2, R91.2, U52.2 (GND), U53.2 (GND), U56.3 (GND)
MCU_HEALTH_N: U52.4 (Y), U53.1 (A)
PHY3V3: C84.1, C85.1, U52.5 (VCC), U53.5 (VCC)
PHY_RESET_N: U53.6 (C)
RUN_ALLOWED: R91.1, U53.4 (Y)
SERVICE_RUN: J31.2 (SERVICE_RUN), R87.1, U52.6 (C), U56.2 (A)
SERVICE_RUN_SENSE: R88.2, R89.1
SERVICE_RUN_SENSE_SRC: R88.1, U56.4 (Y)
STM_RESET_N: U52.3 (B)

Notes on the sheet:
Remove SERVICE_RUN shunt for OTA. Open/missing shunt disables all PHY modes even if firmware requests RUN. Refitting never restores the cleared ARM latch.
