digitie/canview/hardware/communicator/kicad/23_ota_recovery.kicad_sch

## KiCad design hardware/communicator/kicad/23_ota_recovery.kicad_sch (2026-09-06)

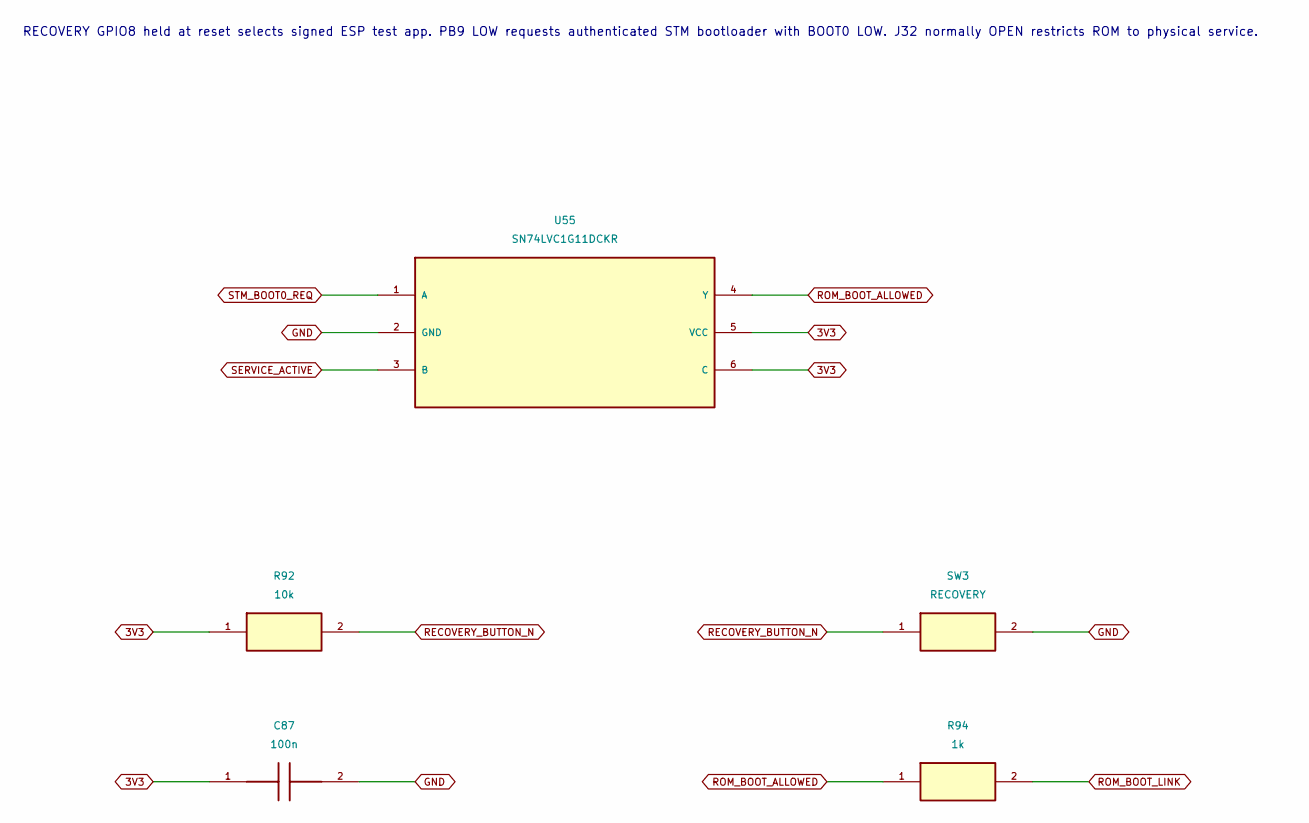
[picture p131: schematic 23_ota_recovery.kicad_sch, part in row 1, column 1]

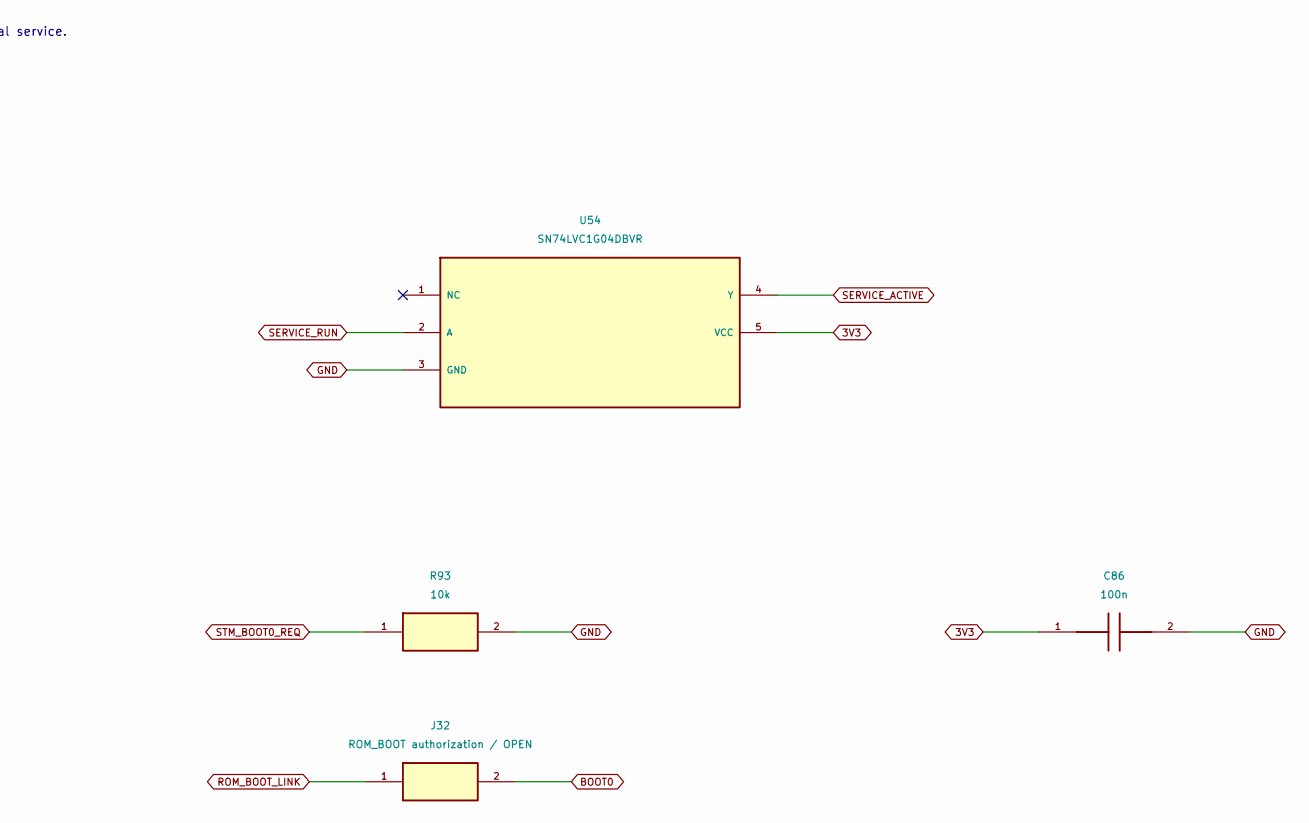
[picture p132: schematic 23_ota_recovery.kicad_sch, part in row 1, column 2]

Parts:
C86, C87: 100n; Capacitor_SMD__C_0402_1005Metric; MPN GEN-C-0402-100n-16V-X7R
J32: ROM_BOOT authorization / OPEN; Connector_PinHeader_1.27mm__PinHeader_1x02_P1.27mm_Vertical; MPN ROM_BOOT authorization / OPEN
R92, R93: 10k; Resistor_SMD__R_0402_1005Metric; MPN GEN-R-0402-10k-1%
R94: 1k; Resistor_SMD__R_0402_1005Metric; MPN GEN-R-0402-1k-1%
SW3: RECOVERY; Button_Switch_SMD__SW_SPST_TL3342; MPN TL3342F160QG
U54: SN74LVC1G04DBVR; Package_TO_SOT_SMD__SOT-23-5; MPN SN74LVC1G04DBVR
U55: SN74LVC1G11DCKR; Package_TO_SOT_SMD__SOT-363_SC-70-6; MPN SN74LVC1G11DCKR

Connections:
3V3: C86.1, C87.1, R92.1, U54.5 (VCC), U55.5 (VCC), U55.6 (C)
BOOT0: J32.2 (BOOT0)
GND: C86.2, C87.2, R93.2, SW3.2, U54.3 (GND), U55.2 (GND)
RECOVERY_BUTTON_N: R92.2, SW3.1
ROM_BOOT_ALLOWED: R94.1, U55.4 (Y)
ROM_BOOT_LINK: J32.1 (ROM_BOOT_LINK), R94.2
SERVICE_ACTIVE: U54.4 (Y), U55.3 (B)
SERVICE_RUN: U54.2 (A)
STM_BOOT0_REQ: R93.1, U55.1 (A)

Notes on the sheet:
RECOVERY GPIO8 held at reset selects signed ESP test app. PB9 LOW requests authenticated STM bootloader with BOOT0 LOW. J32 normally OPEN restricts ROM to physical service.
