digitie/canview/hardware/communicator/kicad/24_ota_test_points.kicad_sch

## KiCad design hardware/communicator/kicad/24_ota_test_points.kicad_sch (2026-09-06)

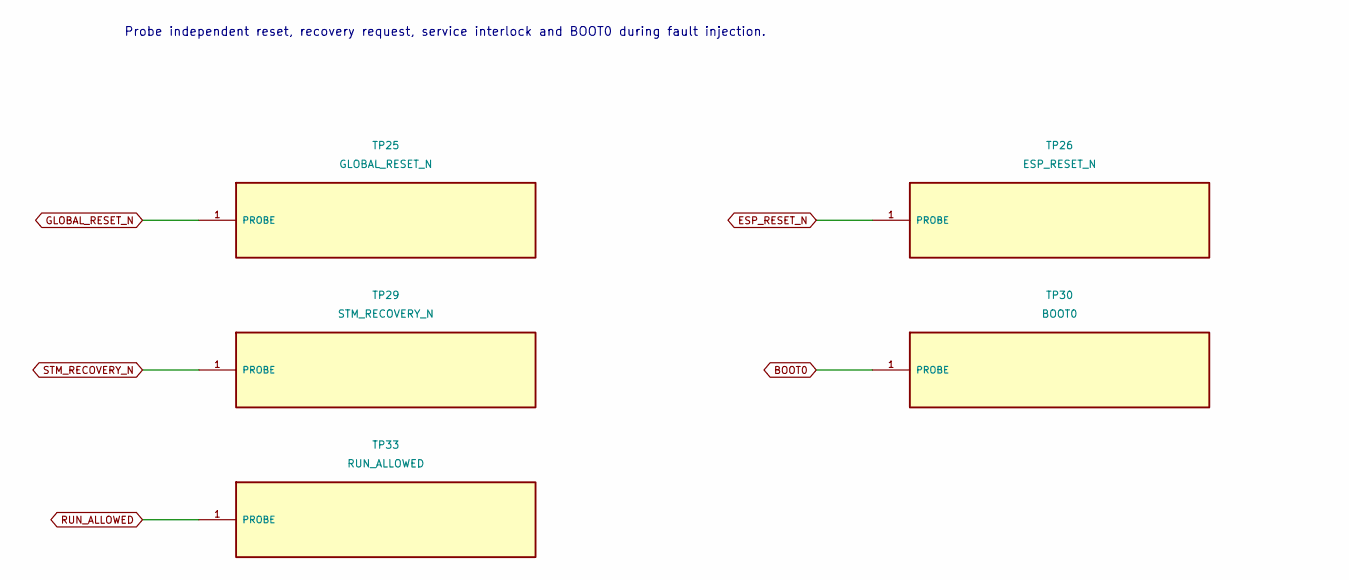
[picture p133: schematic 24_ota_test_points.kicad_sch, part in row 1, column 1]

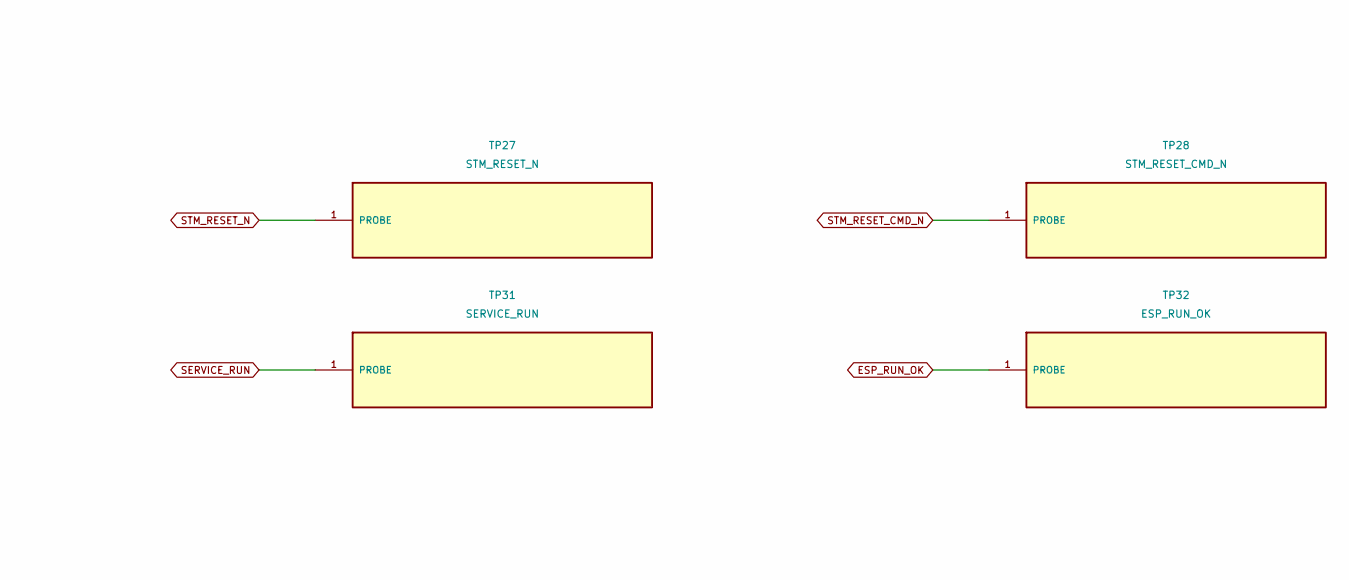
[picture p134: schematic 24_ota_test_points.kicad_sch, part in row 1, column 2]

Parts:
TP25: GLOBAL_RESET_N; TestPoint__TestPoint_Pad_D1.0mm; MPN PCB-PAD-1MM
TP26: ESP_RESET_N; TestPoint__TestPoint_Pad_D1.0mm; MPN PCB-PAD-1MM
TP27: STM_RESET_N; TestPoint__TestPoint_Pad_D1.0mm; MPN PCB-PAD-1MM
TP28: STM_RESET_CMD_N; TestPoint__TestPoint_Pad_D1.0mm; MPN PCB-PAD-1MM
TP29: STM_RECOVERY_N; TestPoint__TestPoint_Pad_D1.0mm; MPN PCB-PAD-1MM
TP30: BOOT0; TestPoint__TestPoint_Pad_D1.0mm; MPN PCB-PAD-1MM
TP31: SERVICE_RUN; TestPoint__TestPoint_Pad_D1.0mm; MPN PCB-PAD-1MM
TP32: ESP_RUN_OK; TestPoint__TestPoint_Pad_D1.0mm; MPN PCB-PAD-1MM
TP33: RUN_ALLOWED; TestPoint__TestPoint_Pad_D1.0mm; MPN PCB-PAD-1MM

Connections:
BOOT0: TP30.1
ESP_RESET_N: TP26.1
ESP_RUN_OK: TP32.1
GLOBAL_RESET_N: TP25.1
RUN_ALLOWED: TP33.1
SERVICE_RUN: TP31.1
STM_RECOVERY_N: TP29.1
STM_RESET_CMD_N: TP28.1
STM_RESET_N: TP27.1

Notes on the sheet:
Probe independent reset, recovery request, service interlock and BOOT0 during fault injection.
