digitie/canview/hardware/controller-adapter/kicad/01_waveshare_header.kicad_sch

## KiCad design hardware/controller-adapter/kicad/01_waveshare_header.kicad_sch (2026-09-06)

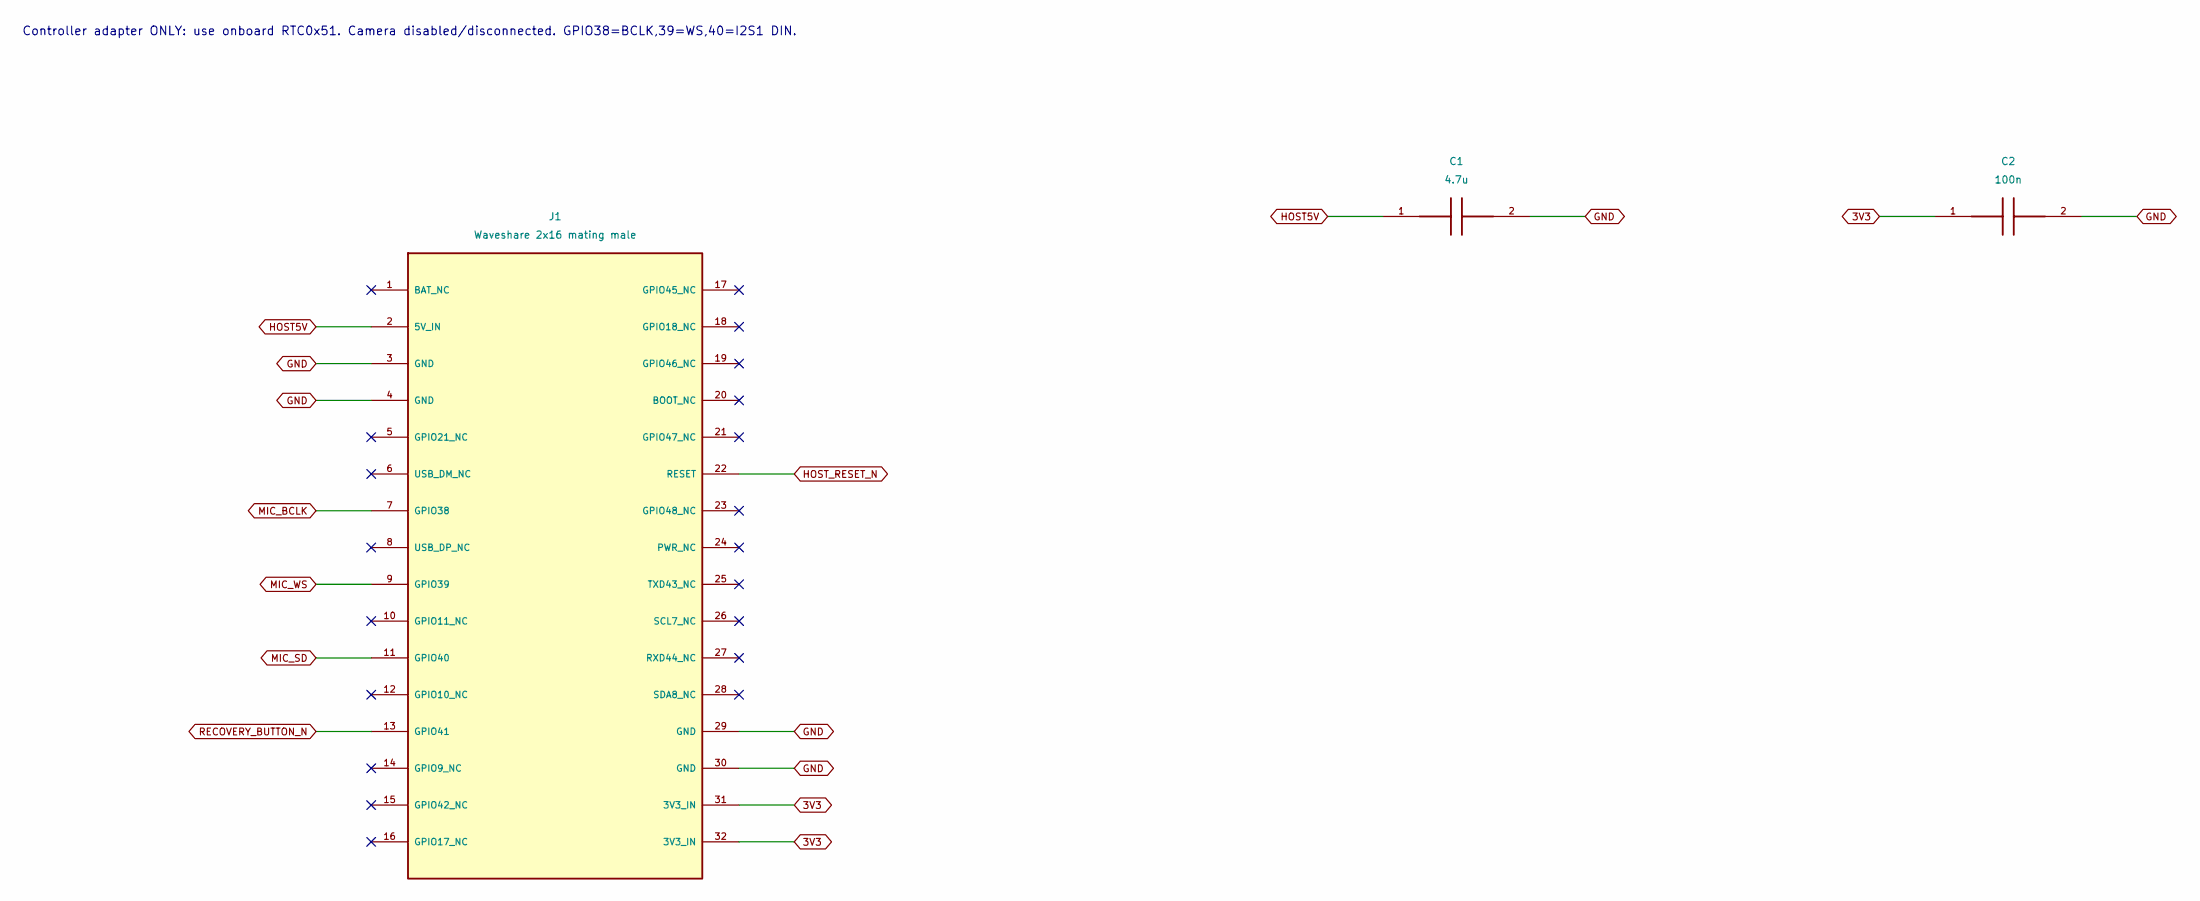
[picture p135: schematic 01_waveshare_header.kicad_sch]

Parts:
C1: 4.7u; Capacitor_SMD__C_0603_1608Metric; MPN GEN-C-0603-4.7u-16V-X7R
C2: 100n; Capacitor_SMD__C_0402_1005Metric; MPN GEN-C-0402-100n-16V-X7R
J1: Waveshare 2x16 mating male; Connector_PinHeader_2.54mm__PinHeader_2x16_P2.54mm_Vertical; MPN GEN-2x16-MALE-2.54

Connections:
3V3: C2.1, J1.31 (3V3_IN), J1.32 (3V3_IN)
GND: C1.2, C2.2, J1.3 (GND), J1.4 (GND), J1.29 (GND), J1.30 (GND)
HOST5V: C1.1, J1.2 (5V_IN)
HOST_RESET_N: J1.22 (RESET)
MIC_BCLK: J1.7 (GPIO38)
MIC_SD: J1.11 (GPIO40)
MIC_WS: J1.9 (GPIO39)
RECOVERY_BUTTON_N: J1.13 (GPIO41)

Notes on the sheet:
Controller adapter ONLY: use onboard RTC0x51. Camera disabled/disconnected. GPIO38=BCLK,39=WS,40=I2S1 DIN.
