digitie/canview/hardware/controller-adapter/kicad/02_i2s_differential.kicad_sch

## KiCad design hardware/controller-adapter/kicad/02_i2s_differential.kicad_sch (2026-09-06)

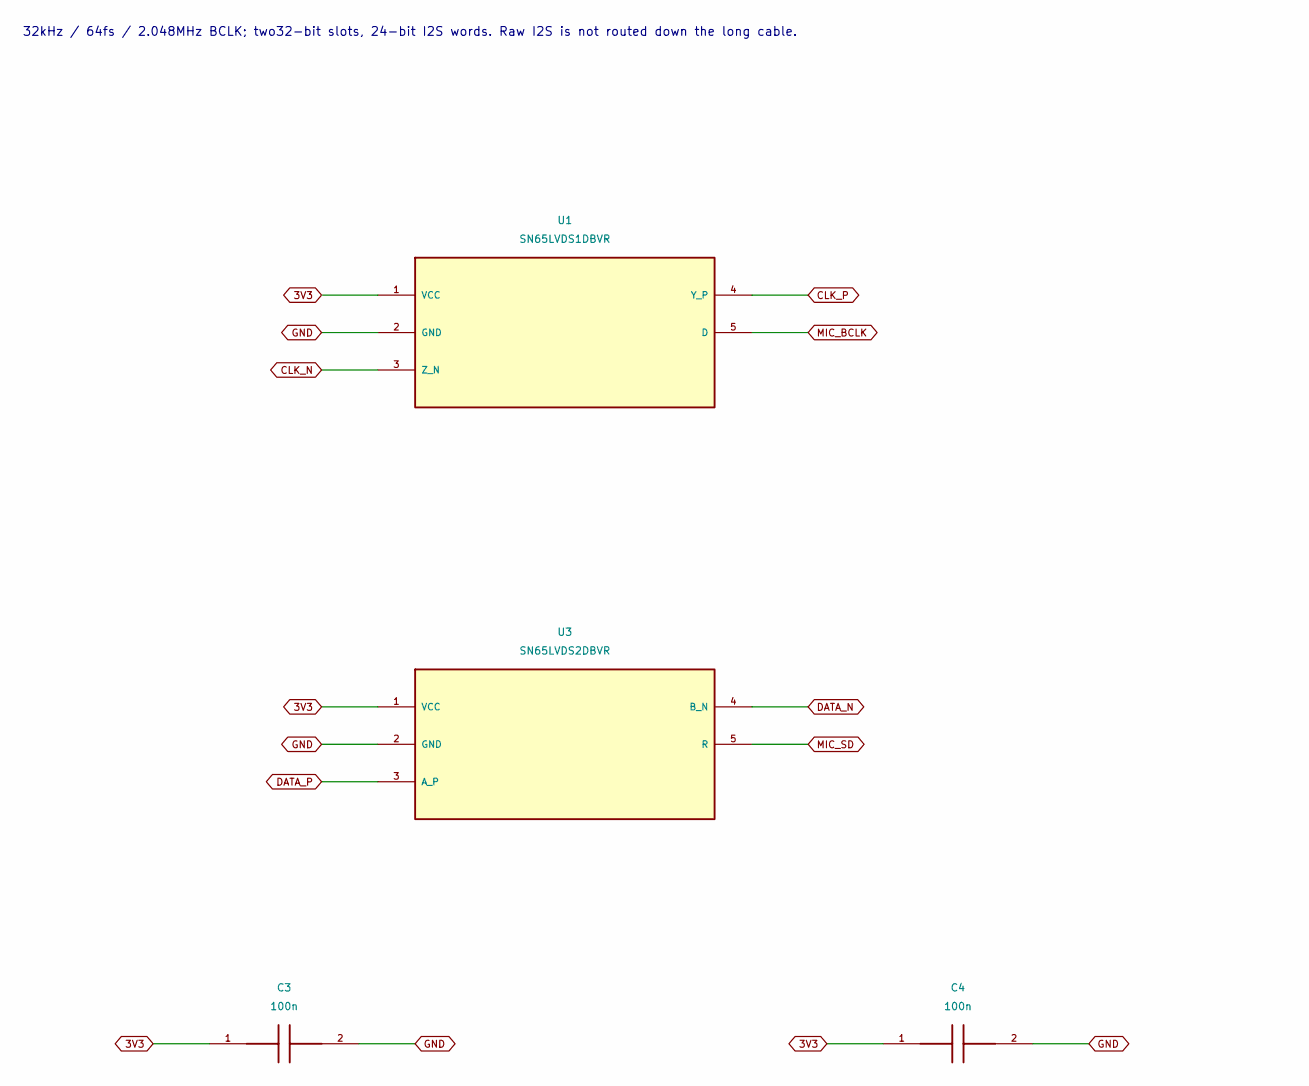
[picture p136: schematic 02_i2s_differential.kicad_sch, part in row 1, column 1]

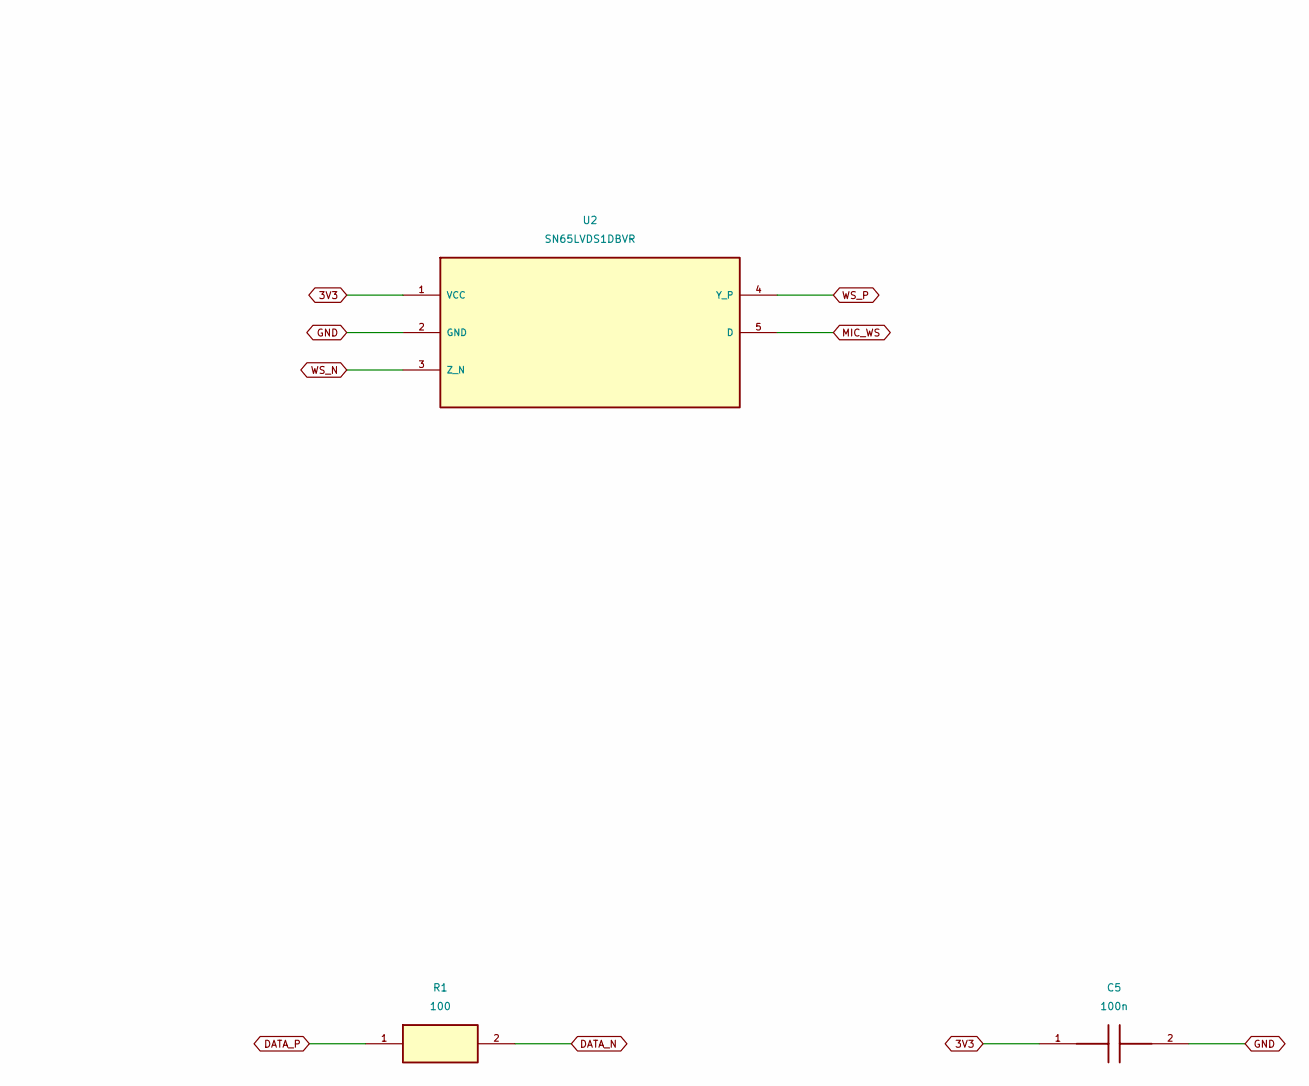
[picture p137: schematic 02_i2s_differential.kicad_sch, part in row 1, column 2]

Parts:
C3, C4, C5: 100n; Capacitor_SMD__C_0402_1005Metric; MPN GEN-C-0402-100n-16V-X7R
R1: 100; Resistor_SMD__R_0402_1005Metric; MPN GEN-R-0402-100-1%
U1, U2: SN65LVDS1DBVR; Package_TO_SOT_SMD__SOT-23-5; MPN SN65LVDS1DBVR
U3: SN65LVDS2DBVR; Package_TO_SOT_SMD__SOT-23-5; MPN SN65LVDS2DBVR

Connections:
3V3: C3.1, C4.1, C5.1, U1.1 (VCC), U2.1 (VCC), U3.1 (VCC)
CLK_N: U1.3 (Z_N)
CLK_P: U1.4 (Y_P)
DATA_N: R1.2, U3.4 (B_N)
DATA_P: R1.1, U3.3 (A_P)
GND: C3.2, C4.2, C5.2, U1.2 (GND), U2.2 (GND), U3.2 (GND)
MIC_BCLK: U1.5 (D)
MIC_SD: U3.5 (R)
MIC_WS: U2.5 (D)
WS_N: U2.3 (Z_N)
WS_P: U2.4 (Y_P)

Notes on the sheet:
32kHz / 64fs / 2.048MHz BCLK; two32-bit slots, 24-bit I2S words. Raw I2S is not routed down the long cable.
