digitie/canview/hardware/controller-adapter/kicad/03_mic_cable.kicad_sch

## KiCad design hardware/controller-adapter/kicad/03_mic_cable.kicad_sch (2026-09-06)

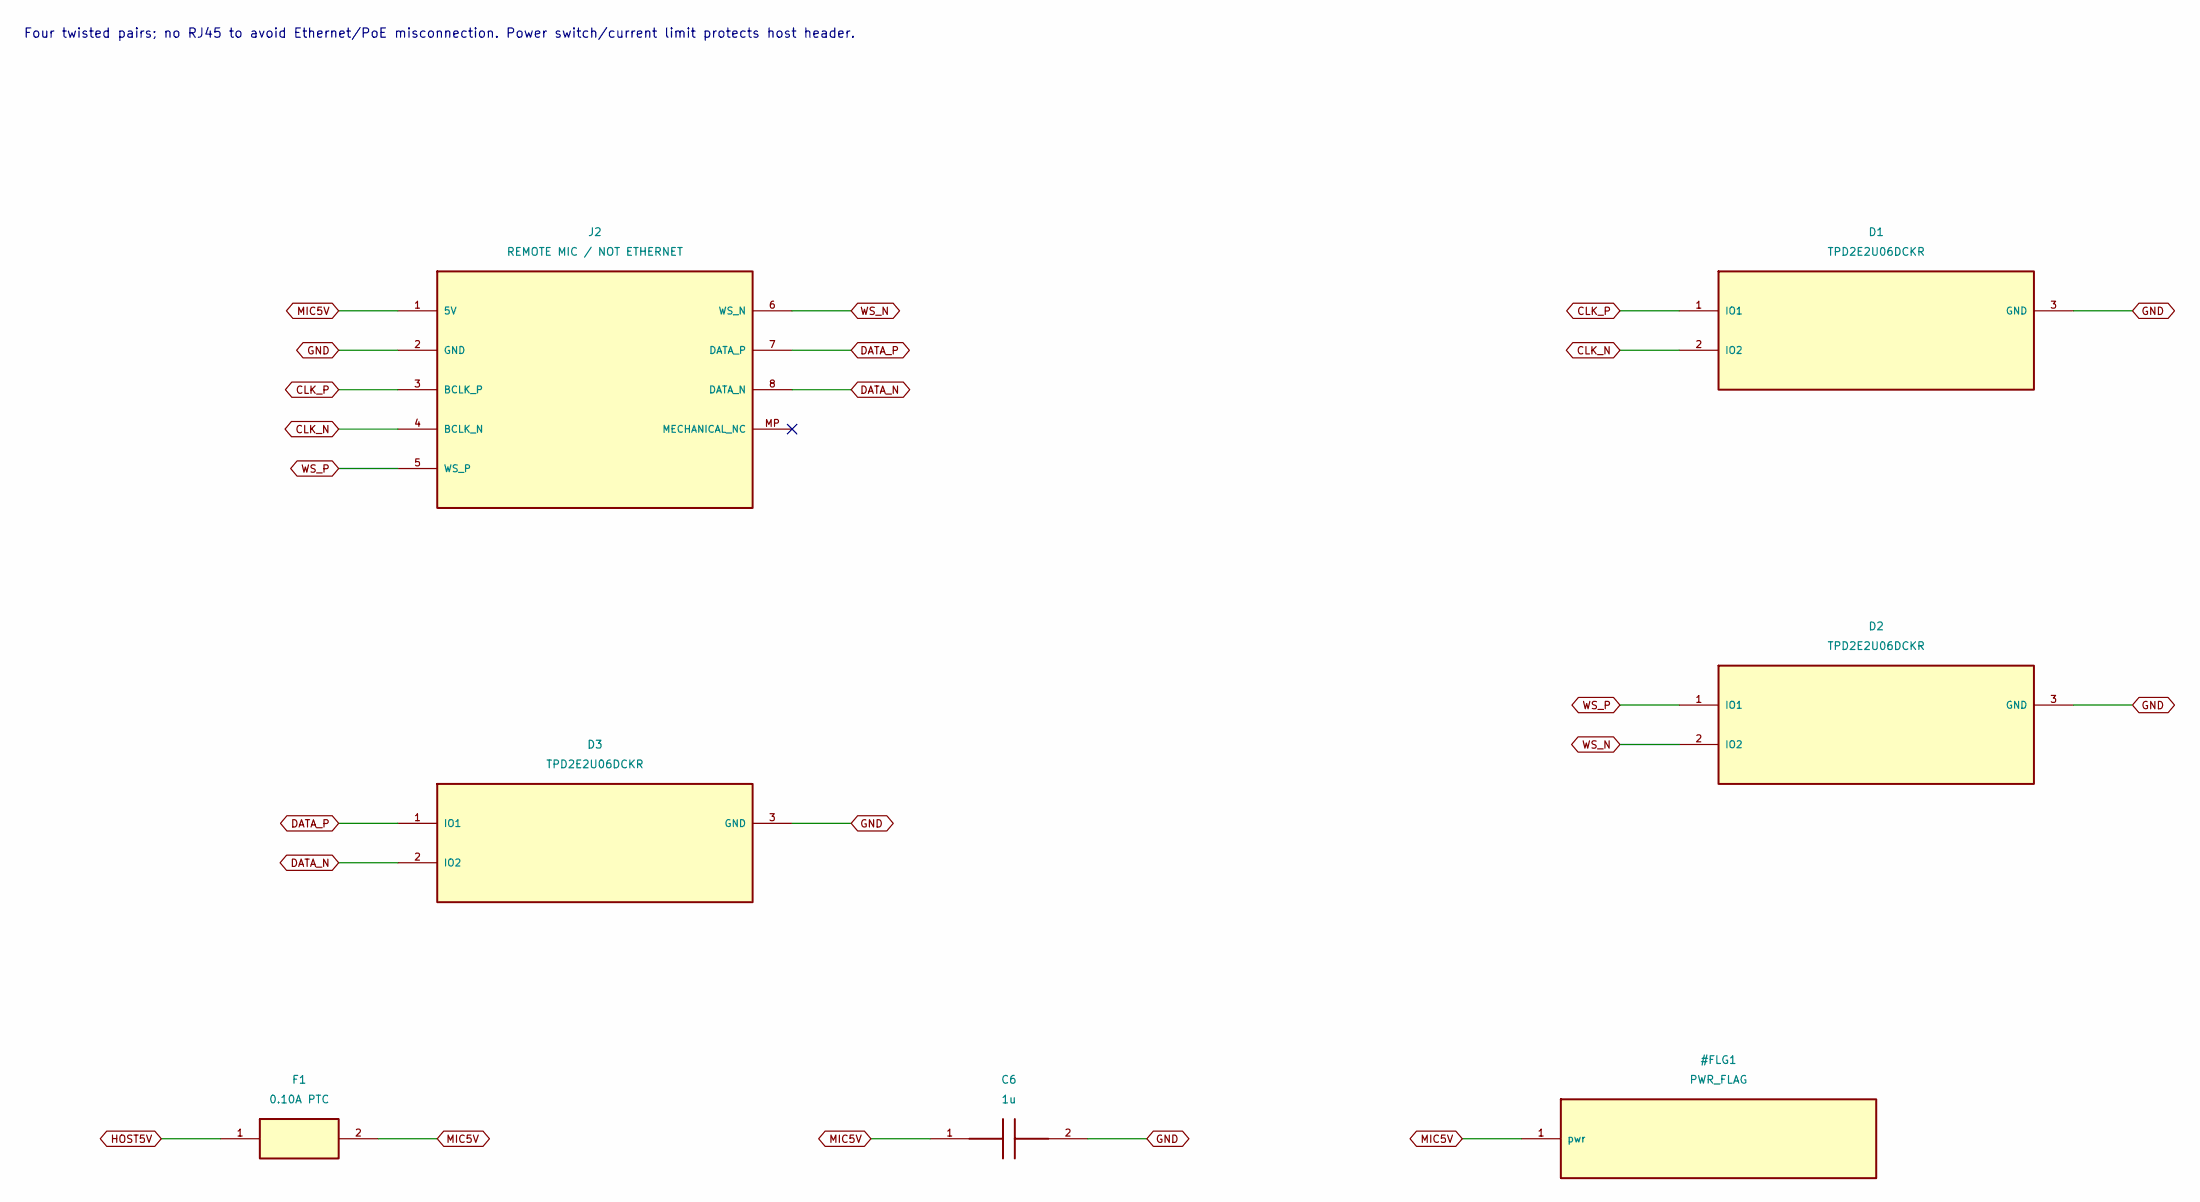
[picture p138: schematic 03_mic_cable.kicad_sch]

Parts:
C6: 1u; Capacitor_SMD__C_0603_1608Metric; MPN GEN-C-0603-1u-16V-X7R
D1, D2, D3: TPD2E2U06DCKR; Package_TO_SOT_SMD__SOT-323_SC-70; MPN TPD2E2U06DCKR
F1: 0.10A PTC; Fuse__Fuse_0805_2012Metric; MPN MF-PSMF010X-2
J2: REMOTE MIC / NOT ETHERNET; Connector_JST__JST_GH_SM08B-GHS-TB_1x08-1MP_P1.25mm_Horizon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; MPN SM08B-GHS-TB(LF)(SN)

Connections:
CLK_N: D1.2 (IO2), J2.4 (BCLK_N)
CLK_P: D1.1 (IO1), J2.3 (BCLK_P)
DATA_N: D3.2 (IO2), J2.8 (DATA_N)
DATA_P: D3.1 (IO1), J2.7 (DATA_P)
GND: C6.2, D1.3 (GND), D2.3 (GND), D3.3 (GND), J2.2 (GND)
HOST5V: F1.1
MIC5V: C6.1, F1.2, J2.1 (5V)
WS_N: D2.2 (IO2), J2.6 (WS_N)
WS_P: D2.1 (IO1), J2.5 (WS_P)

Notes on the sheet:
Four twisted pairs; no RJ45 to avoid Ethernet/PoE misconnection. Power switch/current limit protects host header.
