digitie/canview/hardware/controller-adapter/kicad/04_ota_recovery.kicad_sch

## KiCad design hardware/controller-adapter/kicad/04_ota_recovery.kicad_sch (2026-09-06)

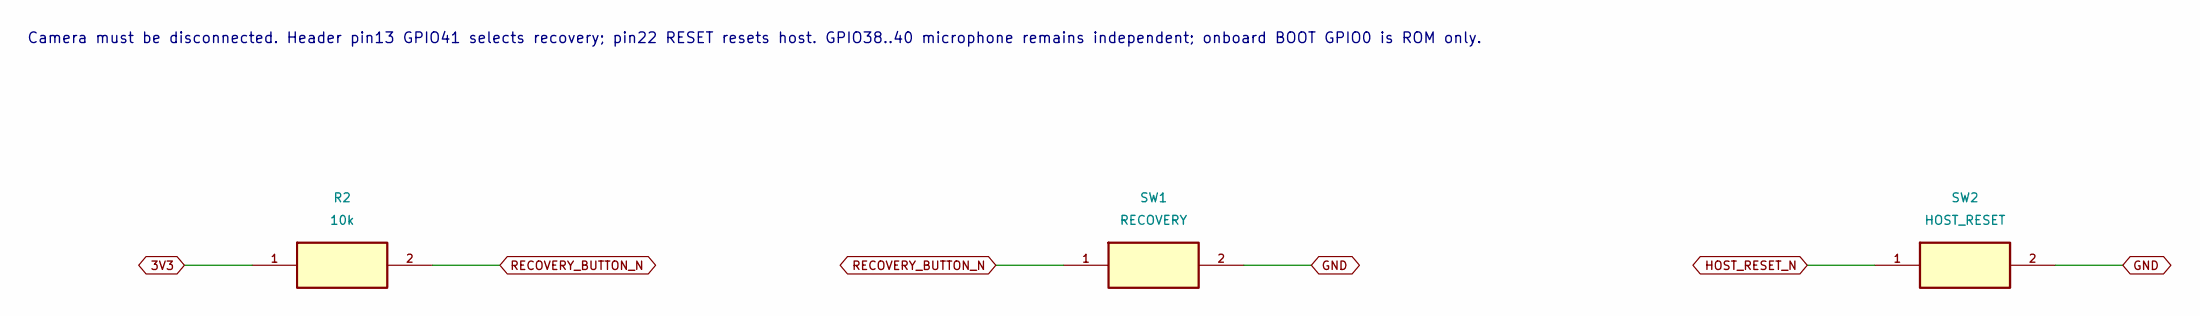
[picture p139: schematic 04_ota_recovery.kicad_sch]

Parts:
R2: 10k; Resistor_SMD__R_0402_1005Metric; MPN GEN-R-0402-10k-1%
SW1: RECOVERY; Button_Switch_SMD__SW_SPST_TL3342; MPN TL3342F160QG
SW2: HOST_RESET; Button_Switch_SMD__SW_SPST_TL3342; MPN TL3342F160QG

Connections:
3V3: R2.1
GND: SW1.2, SW2.2
HOST_RESET_N: SW2.1
RECOVERY_BUTTON_N: R2.2, SW1.1

Notes on the sheet:
Camera must be disconnected. Header pin13 GPIO41 selects recovery; pin22 RESET resets host. GPIO38..40 microphone remains independent; onboard BOOT GPIO0 is ROM only.
