digitie/canview/hardware/microphone/kicad/01_receiver_power.kicad_sch

## KiCad design hardware/microphone/kicad/01_receiver_power.kicad_sch (2026-09-06)

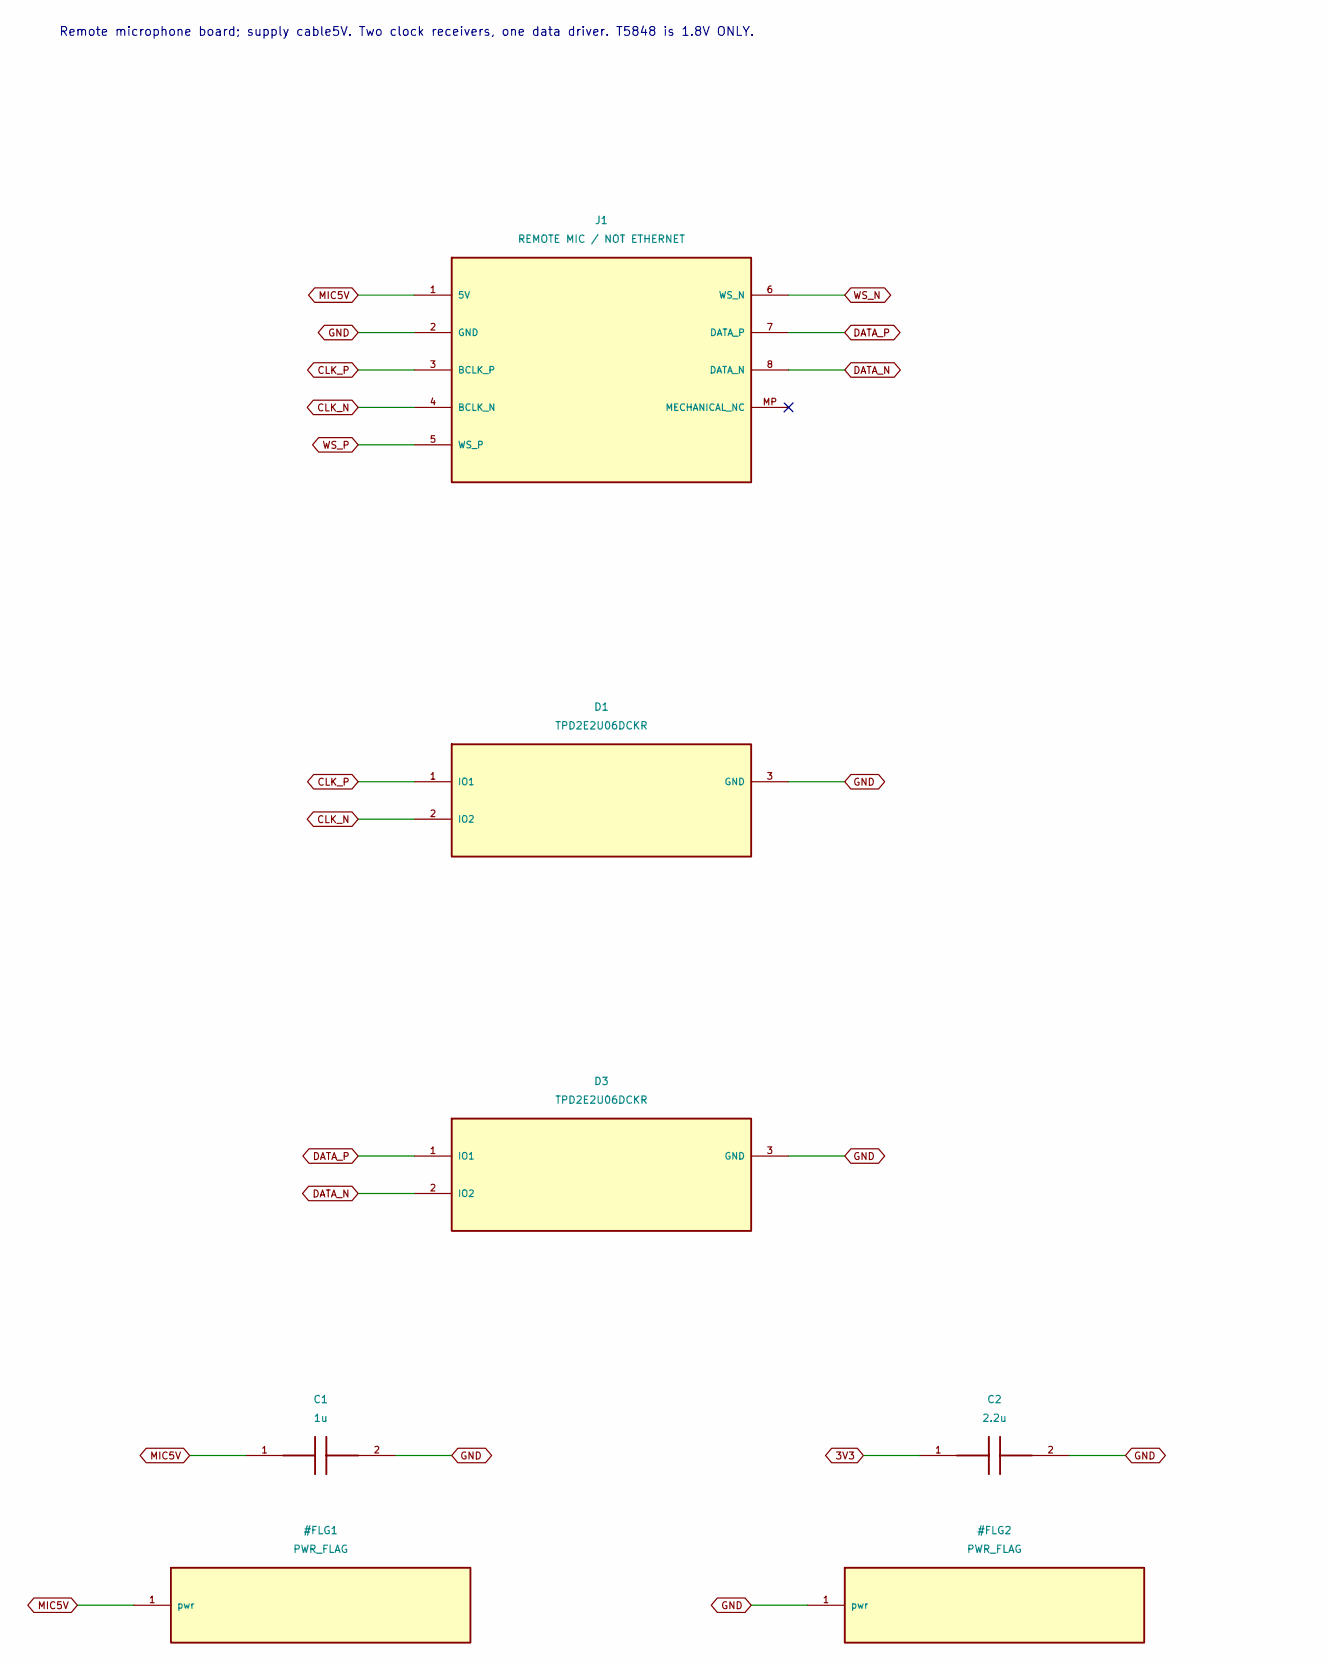
[picture p140: schematic 01_receiver_power.kicad_sch, part in row 1, column 1]

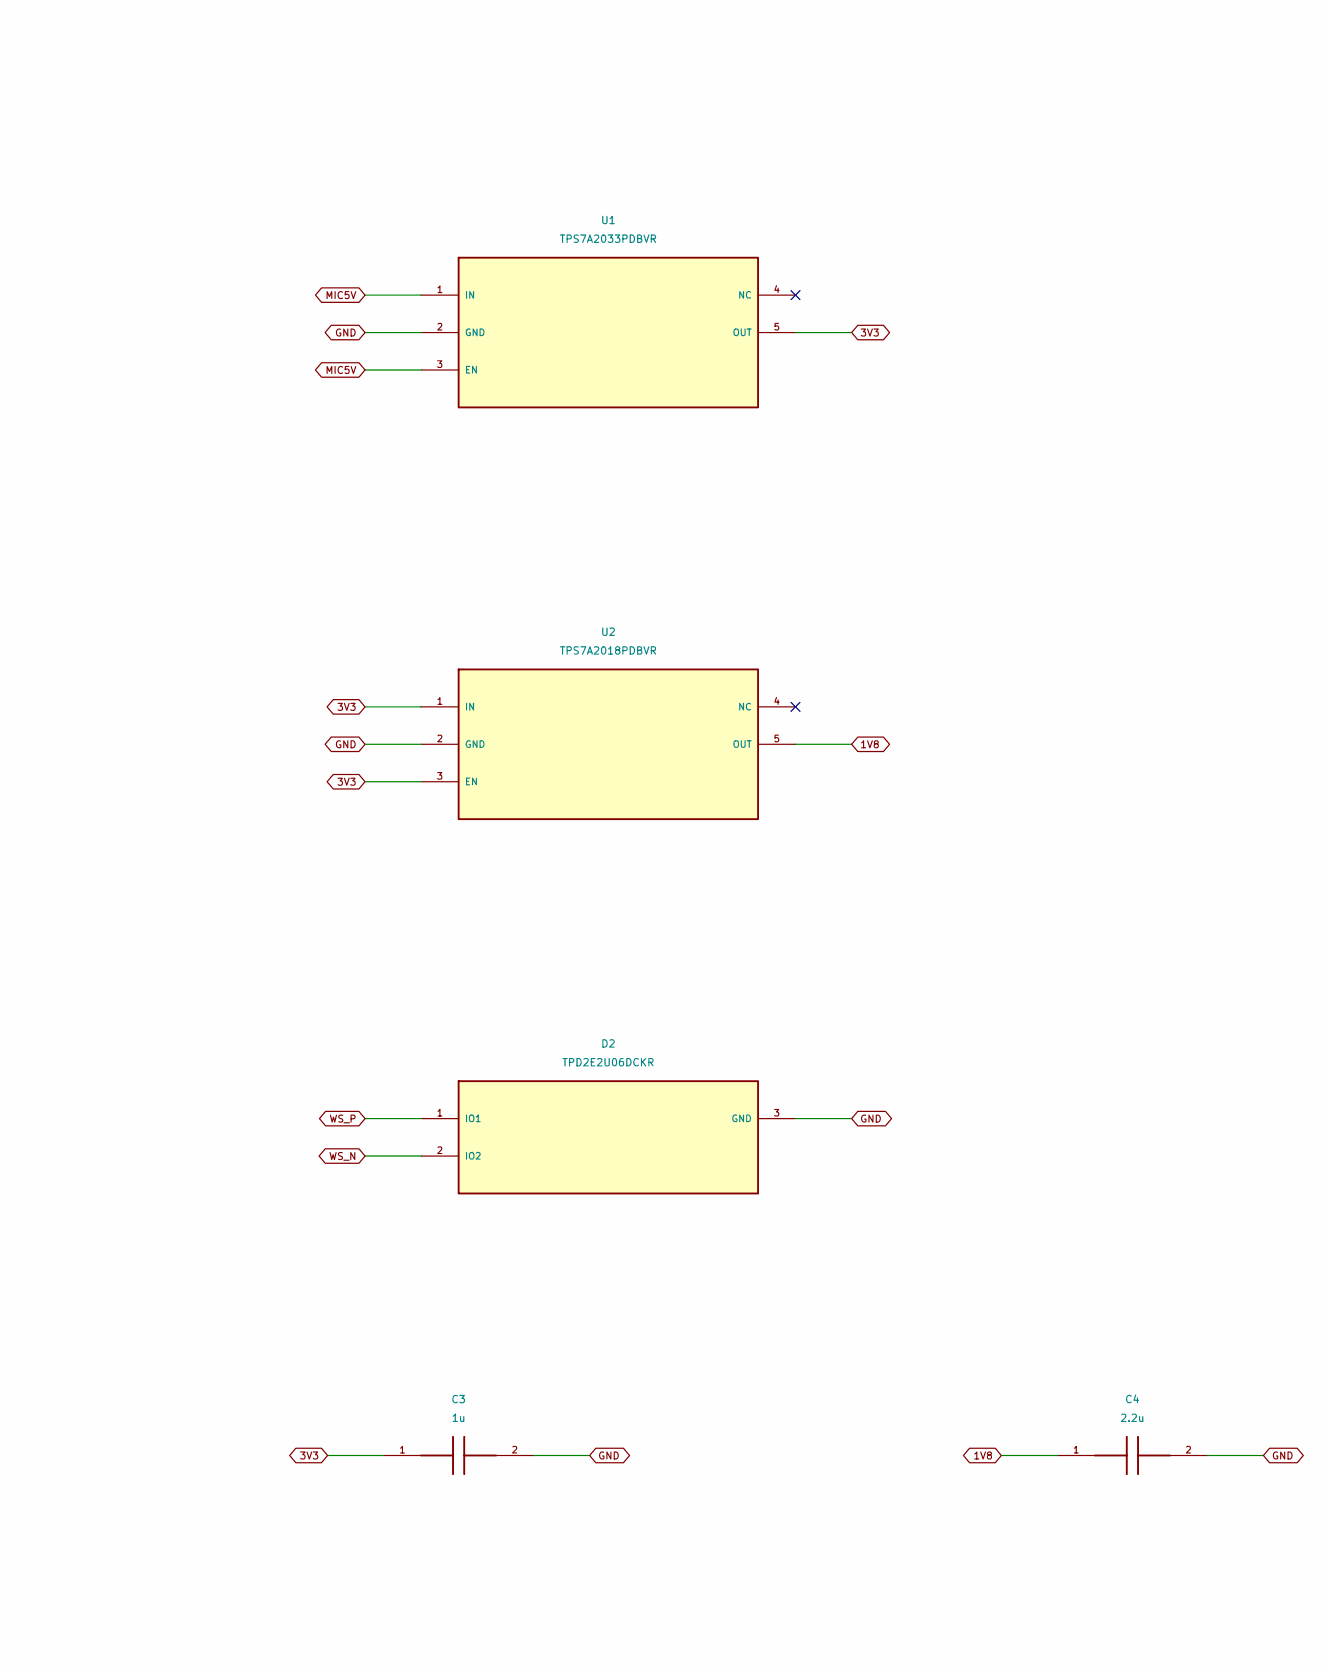
[picture p141: schematic 01_receiver_power.kicad_sch, part in row 1, column 2]

Parts:
C1, C3: 1u; Capacitor_SMD__C_0603_1608Metric; MPN GEN-C-0603-1u-16V-X7R
C2, C4: 2.2u; Capacitor_SMD__C_0603_1608Metric; MPN GEN-C-0603-2.2u-16V-X7R
D1, D2, D3: TPD2E2U06DCKR; Package_TO_SOT_SMD__SOT-323_SC-70; MPN TPD2E2U06DCKR
J1: REMOTE MIC / NOT ETHERNET; Connector_JST__JST_GH_SM08B-GHS-TB_1x08-1MP_P1.25mm_Horizon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; MPN SM08B-GHS-TB(LF)(SN)
U1: TPS7A2033PDBVR; Package_TO_SOT_SMD__SOT-23-5; MPN TPS7A2033PDBVR
U2: TPS7A2018PDBVR; Package_TO_SOT_SMD__SOT-23-5; MPN TPS7A2018PDBVR

Connections:
1V8: C4.1, U2.5 (OUT)
3V3: C2.1, C3.1, U1.5 (OUT), U2.1 (IN), U2.3 (EN)
CLK_N: D1.2 (IO2), J1.4 (BCLK_N)
CLK_P: D1.1 (IO1), J1.3 (BCLK_P)
DATA_N: D3.2 (IO2), J1.8 (DATA_N)
DATA_P: D3.1 (IO1), J1.7 (DATA_P)
GND: C1.2, C2.2, C3.2, C4.2, D1.3 (GND), D2.3 (GND), D3.3 (GND), J1.2 (GND), U1.2 (GND), U2.2 (GND)
MIC5V: C1.1, J1.1 (5V), U1.1 (IN), U1.3 (EN)
WS_N: D2.2 (IO2), J1.6 (WS_N)
WS_P: D2.1 (IO1), J1.5 (WS_P)

Notes on the sheet:
Remote microphone board; supply cable5V. Two clock receivers, one data driver. T5848 is 1.8V ONLY.
