digitie/canview/hardware/microphone/kicad/02_i2s_link.kicad_sch

## KiCad design hardware/microphone/kicad/02_i2s_link.kicad_sch (2026-09-06)

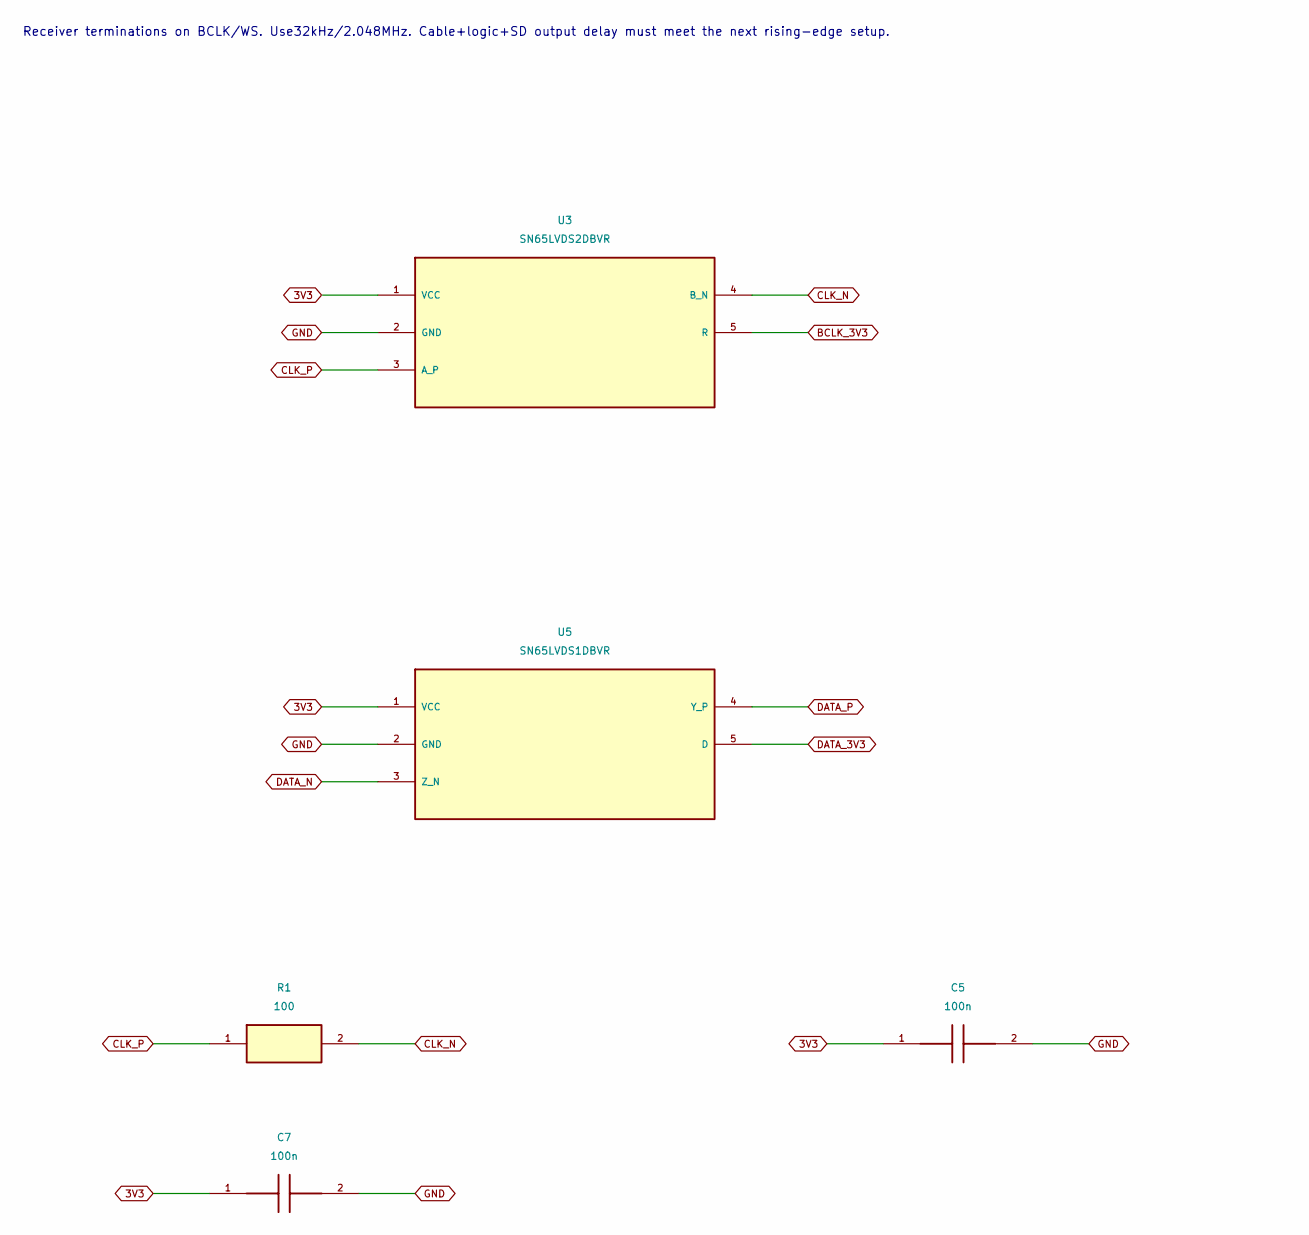
[picture p142: schematic 02_i2s_link.kicad_sch, part in row 1, column 1]

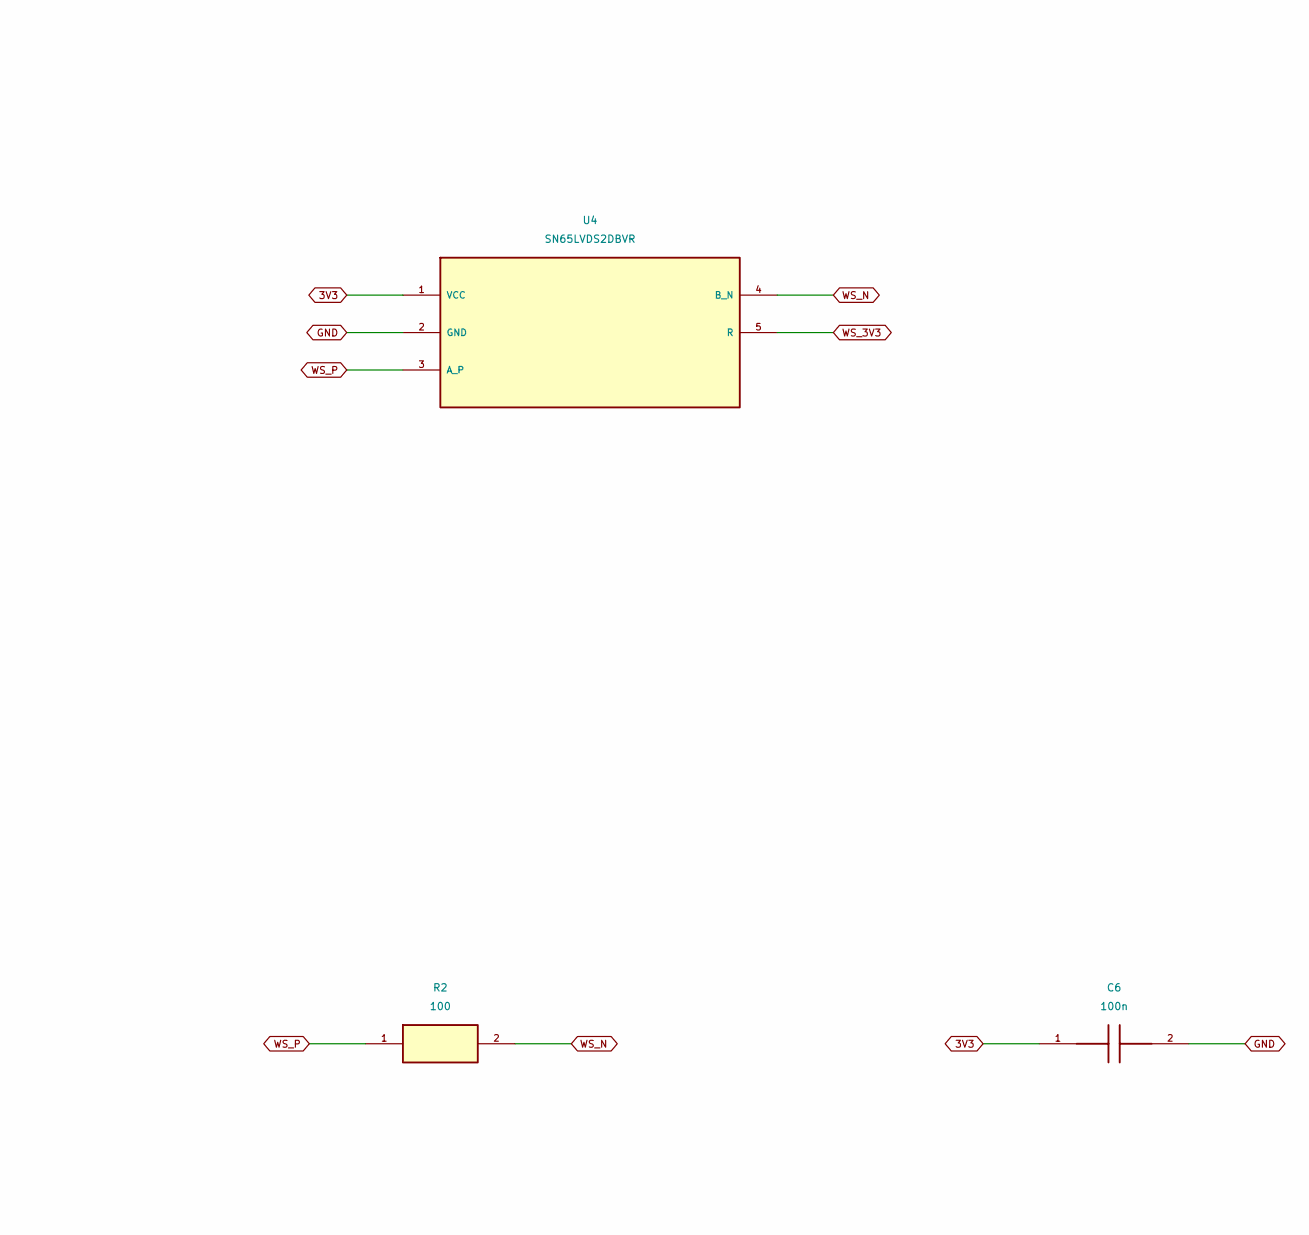
[picture p143: schematic 02_i2s_link.kicad_sch, part in row 1, column 2]

Parts:
C5, C6, C7: 100n; Capacitor_SMD__C_0402_1005Metric; MPN GEN-C-0402-100n-16V-X7R
R1, R2: 100; Resistor_SMD__R_0402_1005Metric; MPN GEN-R-0402-100-1%
U3, U4: SN65LVDS2DBVR; Package_TO_SOT_SMD__SOT-23-5; MPN SN65LVDS2DBVR
U5: SN65LVDS1DBVR; Package_TO_SOT_SMD__SOT-23-5; MPN SN65LVDS1DBVR

Connections:
3V3: C5.1, C6.1, C7.1, U3.1 (VCC), U4.1 (VCC), U5.1 (VCC)
BCLK_3V3: U3.5 (R)
CLK_N: R1.2, U3.4 (B_N)
CLK_P: R1.1, U3.3 (A_P)
DATA_3V3: U5.5 (D)
DATA_N: U5.3 (Z_N)
DATA_P: U5.4 (Y_P)
GND: C5.2, C6.2, C7.2, U3.2 (GND), U4.2 (GND), U5.2 (GND)
WS_3V3: U4.5 (R)
WS_N: R2.2, U4.4 (B_N)
WS_P: R2.1, U4.3 (A_P)

Notes on the sheet:
Receiver terminations on BCLK/WS. Use32kHz/2.048MHz. Cable+logic+SD output delay must meet the next rising-edge setup.
