digitie/canview/hardware/microphone/kicad/03_mems_microphone.kicad_sch

## KiCad design hardware/microphone/kicad/03_mems_microphone.kicad_sch (2026-09-06)

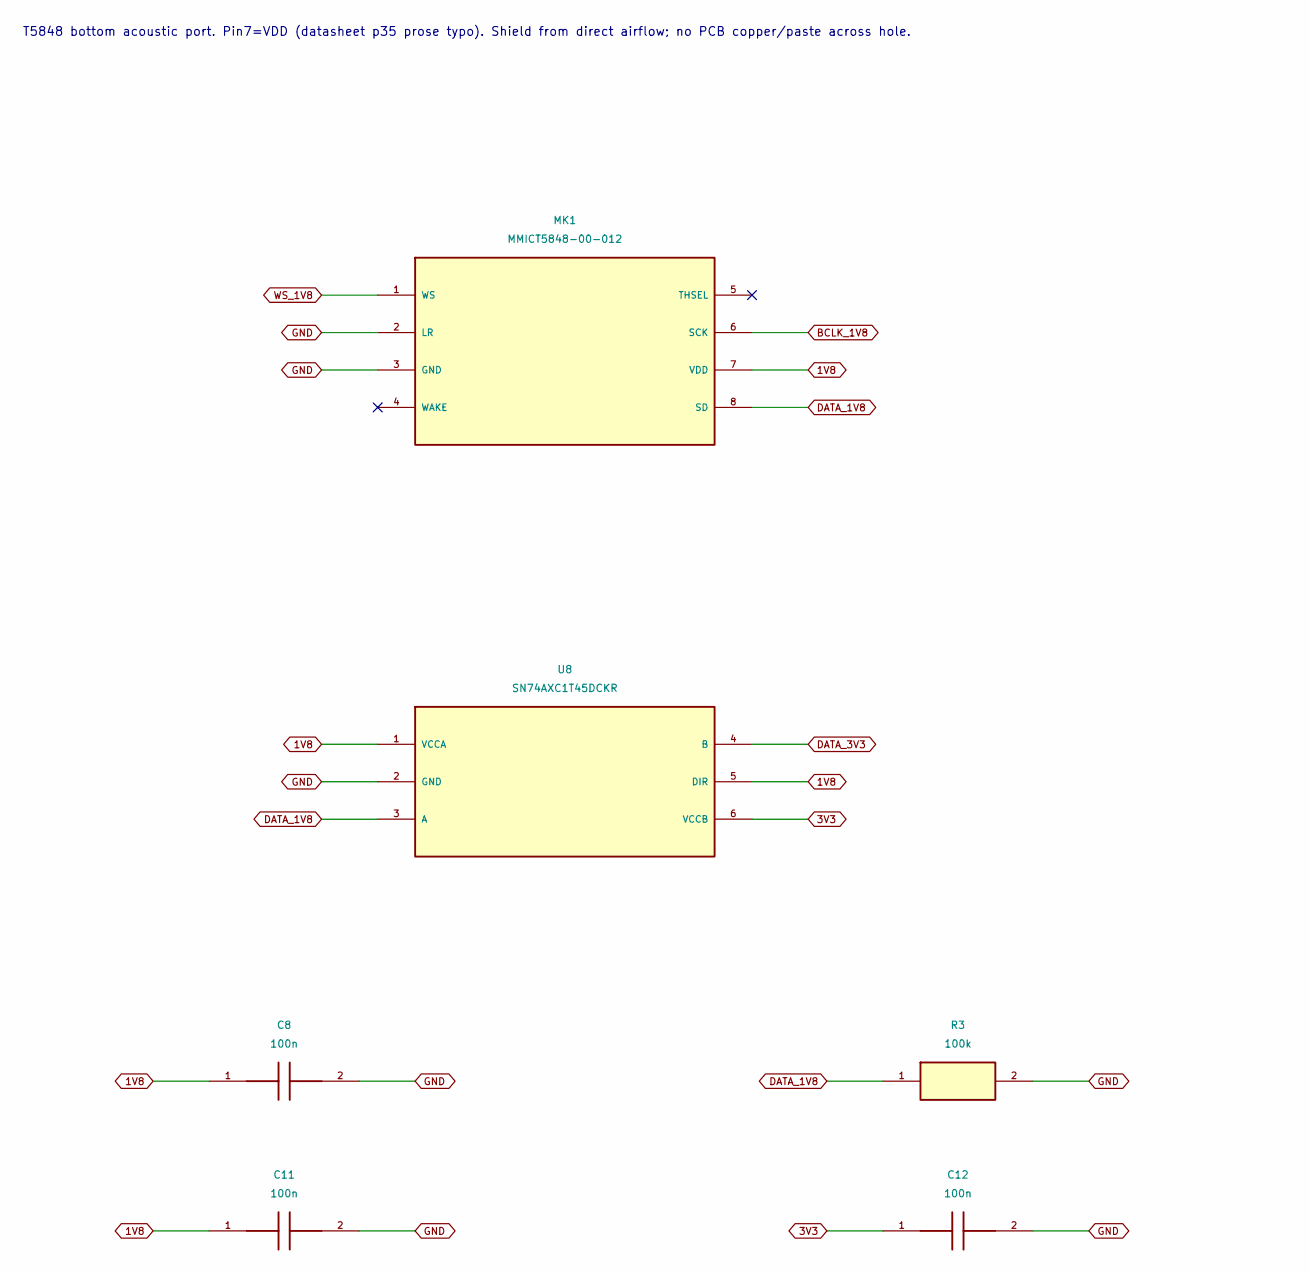
[picture p144: schematic 03_mems_microphone.kicad_sch, part in row 1, column 1]

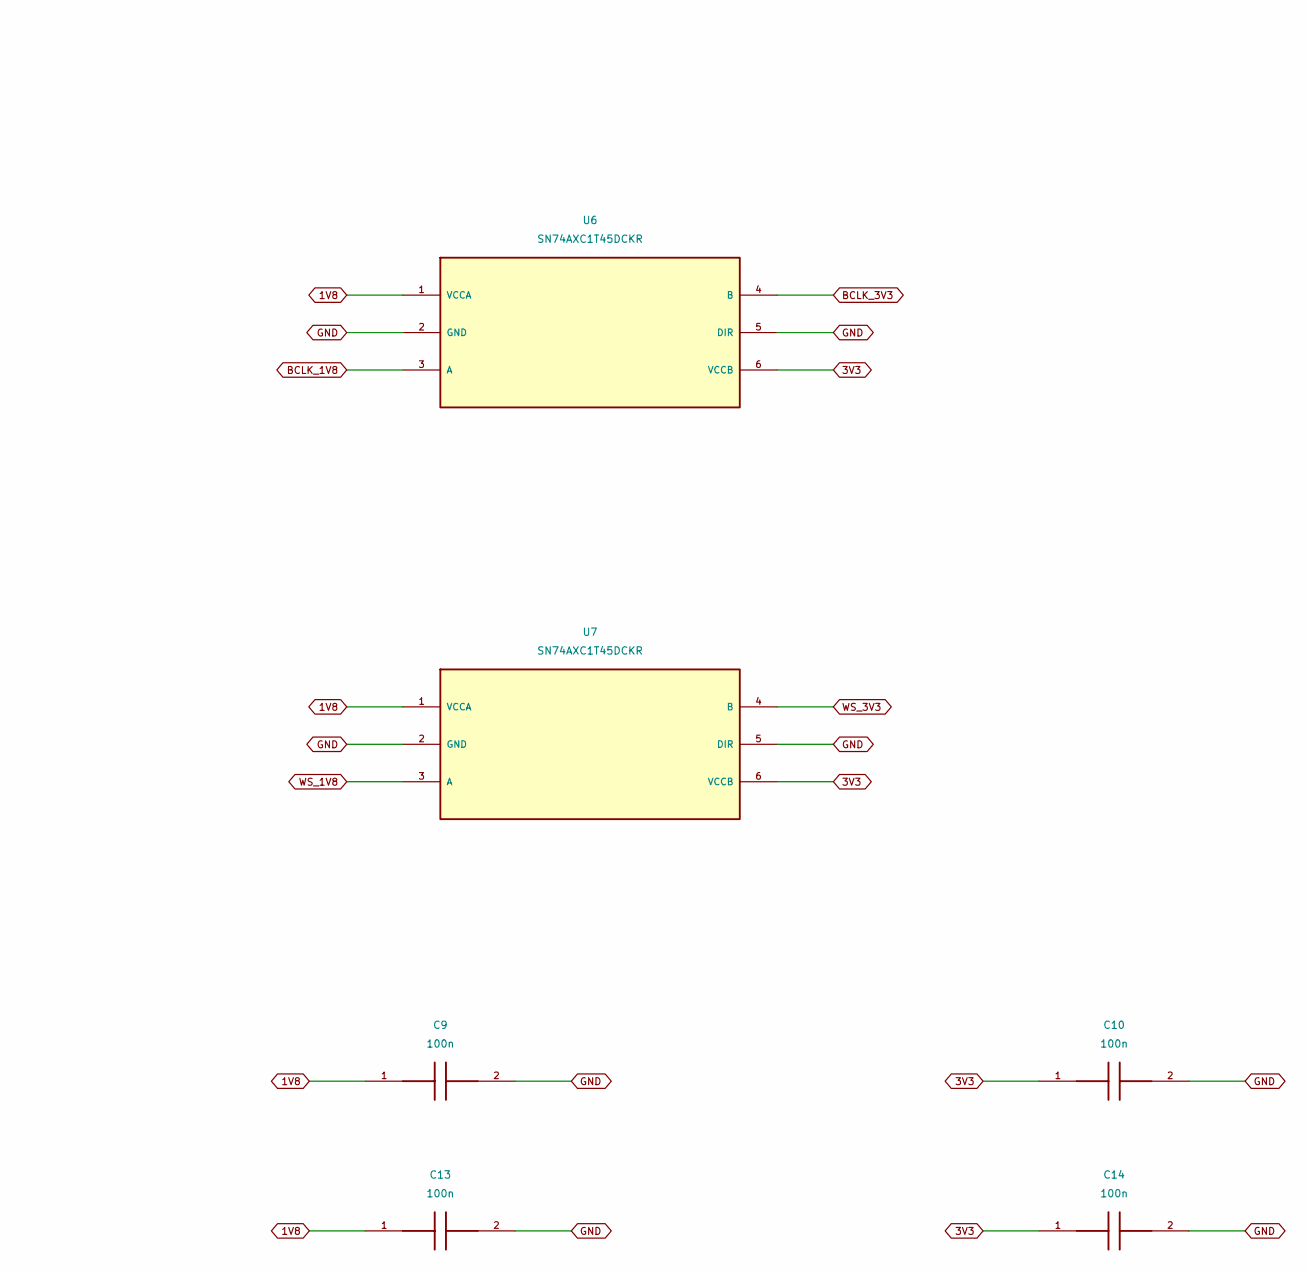
[picture p145: schematic 03_mems_microphone.kicad_sch, part in row 1, column 2]

Parts:
C8, C9, C10, C11, C12, C13, C14: 100n; Capacitor_SMD__C_0402_1005Metric; MPN GEN-C-0402-100n-16V-X7R
MK1: MMICT5848-00-012; TDK_T5848_LGA8; MPN MMICT5848-00-012
R3: 100k; Resistor_SMD__R_0402_1005Metric; MPN GEN-R-0402-100k-1%
U6, U7, U8: SN74AXC1T45DCKR; Package_TO_SOT_SMD__SOT-363_SC-70-6; MPN SN74AXC1T45DCKR

Connections:
1V8: C8.1, C9.1, C11.1, C13.1, MK1.7 (VDD), U6.1 (VCCA), U7.1 (VCCA), U8.1 (VCCA), U8.5 (DIR)
3V3: C10.1, C12.1, C14.1, U6.6 (VCCB), U7.6 (VCCB), U8.6 (VCCB)
BCLK_1V8: MK1.6 (SCK), U6.3 (A)
BCLK_3V3: U6.4 (B)
DATA_1V8: MK1.8 (SD), R3.1, U8.3 (A)
DATA_3V3: U8.4 (B)
GND: C8.2, C9.2, C10.2, C11.2, C12.2, C13.2, C14.2, MK1.2 (LR), MK1.3 (GND), R3.2, U6.2 (GND), U6.5 (DIR), U7.2 (GND), U7.5 (DIR), U8.2 (GND)
WS_1V8: MK1.1 (WS), U7.3 (A)
WS_3V3: U7.4 (B)

Notes on the sheet:
T5848 bottom acoustic port. Pin7=VDD (datasheet p35 prose typo). Shield from direct airflow; no PCB copper/paste across hole.
