digitie/canview/firmware/communicator/esp32/app/main.c

/* SPDX-License-Identifier: GPL-3.0-only */
#include "canview_esp_runtime.h"
#include "canview_board.h"

void app_main(void);
void app_main(void)
{
    static canview_esp_core_t core;
    static canview_esp_pool_t pool;
    static canview_esp_runtime_t runtime;
    canview_esp_runtime_port_t port = {0};
    const canview_platform_port_t board = canview_board_port();
    canview_status_t status = canview_esp_board_runtime(&runtime, &port);
    if (status == CANVIEW_OK)
    {
        status = canview_esp_core_boot(&core, &port.core);
    }
    if (status == CANVIEW_OK)
    {
        status = canview_esp_pool_init(&pool, CANVIEW_ESP_POOL_SLOTS, &port.pool);
    }
    if (port.report != NULL)
    {
        port.report(port.context, &core, status);
    }
    while (status == CANVIEW_OK)
    {
        status = port.wait(port.context);
        if (status == CANVIEW_OK)
        {
            status = canview_esp_core_step(&core);
        }
    }
    /* 최초 실패 이후 feed/재초기화 없음. 등록 후 실패는 TWDT가 reset한다.
     * GPIO 단계 실패로 등록 전이면 safe idle을 유지한다. 외부 TX gate는 별도 필수다. */
    if (port.report != NULL)
    {
        port.report(port.context, &core, status);
    }
    for (;;)
    {
        board.idle(board.context);
    }
}
