digitie/canview/shared/protocol/include/canview_uart.h

/* SPDX-License-Identifier: GPL-3.0-only */
/** @file canview_uart.h
 * @brief Communicator ESP32↔STM32 UART semantic validation and bounded state.
 *
 * The generated header describes the wire ABI. This API validates a decoded
 * envelope before dispatch and owns no UART peripheral, DMA, queue or CAN TX
 * operation. All state is caller-owned and fixed-size.
 *
 * A single worker owns each link/plan/cache/replay context and serializes all
 * feed, admission, session and callback operations. These APIs provide no locks
 * and are not ISR-safe or reentrant. "Atomic" session changes mean an indivisible
 * transaction from that worker's perspective, not cross-thread atomicity. ISR
 * and other tasks post events to the owner; callbacks must not feed/reset the
 * codec or reenter session/admission APIs. Runtime queues and pending commands
 * must be flushed by that same owner on session invalidation (T-104/T-202).
 */
#ifndef CANVIEW_UART_H
#define CANVIEW_UART_H

#include <stdbool.h>
#include <stddef.h>
#include <stdint.h>

#include "canview_status.h"
#include "canview_uart_protocol.h"
#include "canview_wire.h"

#ifdef __cplusplus
extern "C"
{
#endif

#define CANVIEW_UART_COMMAND_DIGEST_SIZE (32U)
#define CANVIEW_UART_CONTROL_TAG_SIZE (16U)
#define CANVIEW_UART_PLAN_DIGEST_SIZE (32U)
#define CANVIEW_UART_HEARTBEAT_ONLINE_MS (300U)
#define CANVIEW_UART_HEARTBEAT_OFFLINE_MS (1000U)
#define CANVIEW_UART_SAFETY_SNAPSHOT_MAX_AGE_MS (300U)
#define CANVIEW_UART_CTS_COMMAND_STOP_MS (100U)
#define CANVIEW_UART_CTS_OFFLINE_MS (1000U)
#define CANVIEW_UART_CONTROL_TIME_MAX_AGE_MS (30000U)
#define CANVIEW_UART_CONTROL_TIME_MAX_UNCERTAINTY_US (50000U)

typedef struct
{
    canview_wire_view_t wire;
    const canview_uart_message_policy_t *policy;
} canview_uart_message_view_t;

/** @brief Find the generated policy for a message ID. */
canview_status_t canview_uart_message_policy(uint8_t message_type,
                                             const canview_uart_message_policy_t **policy);

typedef enum
{
    CANVIEW_UART_ENDPOINT_ESP32 = 0,
    CANVIEW_UART_ENDPOINT_STM32 = 1
} canview_uart_endpoint_t;

typedef enum
{
    CANVIEW_UART_FLOW_INBOUND = 0,
    CANVIEW_UART_FLOW_OUTBOUND = 1
} canview_uart_flow_t;

/** @brief Validate an envelope and enforce its endpoint/flow direction. */
canview_status_t canview_uart_message_validate_for_endpoint(
    const canview_wire_view_t *wire, canview_uart_endpoint_t endpoint,
    canview_uart_flow_t flow, canview_uart_message_view_t *view);

/** @brief Return whether a decoded message is legal for the local endpoint role.
 *
 * This helper is used by the endpoint-aware validator and is not an
 * authentication, lease, safety or CAN-TX permission.
 */
bool canview_uart_message_direction_allowed(const canview_uart_message_view_t *view,
                                            canview_uart_endpoint_t endpoint,
                                            canview_uart_flow_t flow);

/** @brief Encode one endpoint-authorized semantic UART message into COBS + delimiter. */
canview_status_t canview_uart_message_encode(uint8_t message_type, uint8_t flags,
                                             uint32_t sequence, uint32_t correlation_id,
                                             uint64_t sender_time_us, const uint8_t *payload,
                                             size_t payload_size, canview_uart_endpoint_t endpoint,
                                             canview_uart_flow_t flow, uint8_t *scratch,
                                             size_t scratch_size, uint8_t *out, size_t capacity,
                                             size_t *written);

typedef struct
{
    canview_uart_stream_t stream;
    canview_uart_endpoint_t endpoint;
    canview_uart_flow_t flow;
    uint32_t packets_ok;
    uint32_t malformed_packets;
    uint32_t unsupported_messages;
    uint32_t crc_failures;
    uint32_t oversize_packets;
} canview_uart_codec_t;

/** @brief Reset a caller-owned worker-context decoder with a fixed endpoint flow. */
canview_status_t canview_uart_codec_reset(canview_uart_codec_t *codec,
                                          canview_uart_endpoint_t endpoint,
                                          canview_uart_flow_t flow);

/** @brief Feed one byte; successful views borrow codec storage until next feed. */
canview_status_t canview_uart_codec_feed(canview_uart_codec_t *codec, uint8_t byte,
                                          canview_uart_message_view_t *view);

typedef struct
{
    uint8_t bus_id;
    uint8_t flags;
    uint32_t can_id;
    uint32_t can_mask;
} canview_uart_observer_filter_t;

typedef struct
{
    uint32_t revision;
    uint16_t filter_count;
    uint16_t max_records_per_second;
    uint32_t max_bytes_per_second;
    uint8_t bus_mask;
    uint8_t reserved[3];
    uint8_t plan_digest[CANVIEW_UART_PLAN_DIGEST_SIZE];
    canview_uart_observer_filter_t filters[CANVIEW_UART_PLAN_MAX_FILTERS];
} canview_uart_observer_plan_t;

typedef struct
{
    bool pending;
    uint64_t request_token;
    uint32_t revision;
    uint32_t expected_active_revision;
    uint16_t total_chunks;
    uint16_t next_chunk;
    uint16_t expected_filter_count;
    uint16_t received_filter_count;
    uint64_t pending_since_ms;
    canview_uart_observer_plan_t active;
    canview_uart_observer_plan_t candidate;
} canview_uart_plan_context_t;

/** @brief Reset active plan and discard any uncommitted candidate. */
canview_status_t canview_uart_plan_reset(canview_uart_plan_context_t *context);

/** @brief Discard only a pending candidate and retain the active plan. */
canview_status_t canview_uart_plan_discard_pending(canview_uart_plan_context_t *context);

/** @brief Calculate the SHA-256 digest of the canonical observer plan. */
canview_status_t canview_uart_plan_digest(const canview_uart_observer_plan_t *plan,
                                          uint8_t digest[CANVIEW_UART_PLAN_DIGEST_SIZE]);

/** @brief Apply BEGIN/CHUNK/COMMIT/ABORT atomically to the active plan. */
canview_status_t canview_uart_plan_apply(canview_uart_plan_context_t *context,
                                         const uint8_t *payload, size_t payload_size,
                                         uint64_t now_ms);

/** @brief Copy the last committed observer plan. */
canview_status_t canview_uart_plan_current(const canview_uart_plan_context_t *context,
                                           canview_uart_observer_plan_t *plan);

typedef struct
{
    uint64_t origin_device_id;
    uint64_t origin_boot_id;
    uint32_t wireless_session_id;
    uint32_t control_generation;
    uint64_t request_token;
    uint16_t command_id;
    uint8_t canonical_argument_digest[CANVIEW_UART_COMMAND_DIGEST_SIZE];
} canview_uart_command_key_t;

typedef struct
{
    uint16_t slot;
    uint16_t reserved;
    uint64_t generation;
} canview_uart_command_handle_t;

typedef struct
{
    bool valid;
    bool acknowledged;
    bool terminal;
    uint64_t generation;
    uint64_t request_expires_at_ms;
    uint64_t expires_at_ms;
    uint16_t result_size;
    canview_uart_command_key_t key;
    uint8_t result[CANVIEW_UART_COMMAND_RESULT_MAX];
} canview_uart_command_entry_t;

typedef struct
{
    uint32_t initialized;
    uint64_t next_generation;
    canview_uart_command_entry_t entries[CANVIEW_UART_COMMAND_CACHE_CAPACITY];
} canview_uart_command_cache_t;

/** @brief Reset the bounded cache. No live entry is evicted by admission. */
canview_status_t canview_uart_command_cache_reset(canview_uart_command_cache_t *cache);

/** @brief Admit a command or identify a duplicate/conflicting token. */
canview_status_t canview_uart_command_cache_admit(
    canview_uart_command_cache_t *cache, const canview_uart_command_key_t *key,
    uint16_t request_ttl_ms, uint64_t now_ms, canview_uart_command_handle_t *handle);

/** @brief Mark the queue ACK without changing a terminal result or bypassing TTL. */
canview_status_t canview_uart_command_cache_mark_ack(canview_uart_command_cache_t *cache,
                                                     const canview_uart_command_handle_t *handle,
                                                     uint64_t now_ms);

/** @brief Store a terminal result, including when it arrives before ACK. */
canview_status_t canview_uart_command_cache_record_result(
    canview_uart_command_cache_t *cache, const canview_uart_command_handle_t *handle,
    const uint8_t *result, size_t result_size, uint64_t now_ms);

/** @brief Look up a duplicate and expose its retained terminal result if present. */
canview_status_t canview_uart_command_cache_lookup(
    canview_uart_command_cache_t *cache, const canview_uart_command_key_t *key, uint64_t now_ms,
    canview_uart_command_handle_t *handle, const uint8_t **result, size_t *result_size);

/** @brief Expire only entries whose bounded retention window has elapsed. */
canview_status_t canview_uart_command_cache_expire(canview_uart_command_cache_t *cache,
                                                   uint64_t now_ms);

typedef enum
{
    CANVIEW_UART_LINK_OFFLINE = 0,
    CANVIEW_UART_LINK_SUSPECT = 1,
    CANVIEW_UART_LINK_ONLINE = 2
} canview_uart_link_state_t;

typedef struct
{
    bool hello_complete;
    bool hello_ack_complete;
    bool safety_snapshot_valid;
    bool heartbeat_seen;
    bool cts_blocked;
    bool cts_known;
    uint64_t peer_boot_id;
    uint64_t last_heartbeat_ms;
    uint64_t safety_snapshot_time_ms;
    uint32_t safety_revision;
    uint64_t cts_blocked_since_ms;
    canview_uart_link_state_t state;
} canview_uart_link_t;

/** @brief Reset link state to fail-closed OFFLINE. */
canview_status_t canview_uart_link_reset(canview_uart_link_t *link);

/** @brief Complete the HELLO side of link admission for a peer boot epoch. */
canview_status_t canview_uart_link_note_hello(canview_uart_link_t *link, uint64_t peer_boot_id,
                                              uint64_t now_ms, bool *boot_changed);

/** @brief Complete version negotiation for the current peer boot epoch. */
canview_status_t canview_uart_link_note_hello_ack(canview_uart_link_t *link,
                                                  uint64_t peer_boot_id, uint8_t selected_major,
                                                  uint8_t selected_minor, uint8_t result,
                                                  uint64_t now_ms);

/** @brief Mark the current local/peer safety snapshot as fresh for admission. */
canview_status_t canview_uart_link_note_safety_snapshot(canview_uart_link_t *link,
                                                        uint64_t peer_boot_id,
                                                        uint32_t safety_revision,
                                                        uint64_t now_ms);

/** @brief Note heartbeat and report a boot epoch replacement to the caller. */
canview_status_t canview_uart_link_note_heartbeat(canview_uart_link_t *link,
                                                  uint64_t peer_boot_id,
                                                  uint32_t safety_revision, uint64_t now_ms,
                                                  bool *boot_changed);

/** @brief Update CTS state; a block lasting at least the stop threshold halts commands. */
canview_status_t canview_uart_link_set_cts_blocked(canview_uart_link_t *link, bool blocked,
                                                   uint64_t now_ms);

/** @brief Recompute ONLINE/SUSPECT/OFFLINE using heartbeat and CTS deadlines. */
canview_status_t canview_uart_link_tick(canview_uart_link_t *link, uint64_t now_ms);

/** @brief Return true only while heartbeat, HELLO and CTS admission are healthy. */
bool canview_uart_link_command_admission_allowed(const canview_uart_link_t *link,
                                                 uint64_t now_ms);

typedef bool (*canview_uart_command_authorize_fn)(
    const canview_uart_message_view_t *view, uint64_t now_ms, void *context);

typedef struct
{
    canview_uart_command_authorize_fn authorize;
    void *context;
} canview_uart_command_admission_context_t;

/** @brief Synchronously copy a validated command into a bounded owner queue.
 *
 * request itself is stack-borrowed until callback return; its payload is codec-
 * borrowed until the next feed/reset. A callback retaining a command MUST copy
 * the header and all payload bytes into its reserved queue slot before returning
 * CANVIEW_OK, and rebind any stored payload pointer to that slot. Neither pointer
 * may be retained. On failure it must publish no queued command. The callback
 * runs on the single session owner and must not reenter the parser/admission.
 */
typedef canview_status_t (*canview_uart_command_enqueue_fn)(
    const canview_uart_message_view_t *request, void *context);

typedef struct
{
    canview_sequence_window_t sequence;
    bool configured;
} canview_uart_replay_context_t;

/** @brief Reset the single-owner sequence window for one UART direction/session. */
canview_status_t canview_uart_replay_reset(canview_uart_replay_context_t *context);

/** @brief Authenticate, direction-check and atomically commit one decoded sequence. */
canview_status_t canview_uart_message_admit(
    const canview_uart_message_view_t *view, canview_uart_endpoint_t endpoint,
    canview_uart_flow_t flow, canview_uart_replay_context_t *replay,
    const canview_uart_command_admission_context_t *authorization, uint64_t now_ms);

/** @brief Combine transport readiness with STM32-owned command safety results.
 *
 * The callback must be owned by the local authenticated/safety owner. It must
 * verify the exact decoded request's control tag, canonical digest, identity,
 * lease, build mode, state revision and hardware gate. UART CRC or this helper
 * never authenticates a peer and never creates a vehicle CAN frame.
 */
bool canview_uart_command_admission_allowed(
    const canview_uart_link_t *link,
    const canview_uart_message_view_t *request,
    const canview_uart_command_admission_context_t *context, uint64_t now_ms);

/** @brief Validate a command, reserve its queue slot, then commit its sequence.
 *
 * The enqueue callback owns the bounded safety/control queue reservation. The
 * replay window is committed only after that callback returns CANVIEW_OK; a
 * busy/full queue leaves the sequence retryable. CANVIEW_OK requires the
 * synchronous owned copy specified by canview_uart_command_enqueue_fn. The
 * caller must serialize this call with feed/reset and every session operation.
 */
canview_status_t canview_uart_command_dispatch_admit(
    const canview_uart_link_t *link, const canview_uart_message_view_t *request,
    const canview_uart_command_admission_context_t *authorization,
    canview_uart_command_enqueue_fn enqueue, void *enqueue_context,
    canview_uart_replay_context_t *replay, uint64_t now_ms);

/** @brief Atomically clear link, pending observer state, command cache and replay window. */
canview_status_t canview_uart_session_reset(canview_uart_link_t *link,
                                             canview_uart_plan_context_t *plan,
                                             canview_uart_command_cache_t *cache,
                                             canview_uart_replay_context_t *replay);

/** @brief Note HELLO and invalidate state when a new UART session is observed.
 *
 * The replay window is part of the same caller-owned session transaction and
 * must not be shared with another UART direction or task.
 */
canview_status_t canview_uart_session_note_hello(
    canview_uart_link_t *link, canview_uart_plan_context_t *plan,
    canview_uart_command_cache_t *cache, canview_uart_replay_context_t *replay,
    uint64_t peer_boot_id, uint64_t now_ms, bool *boot_changed);

/** @brief Note heartbeat and invalidate state when its boot epoch changes. */
canview_status_t canview_uart_session_note_heartbeat(
    canview_uart_link_t *link, canview_uart_plan_context_t *plan,
    canview_uart_command_cache_t *cache, canview_uart_replay_context_t *replay,
    uint64_t peer_boot_id, uint32_t safety_revision, uint64_t now_ms, bool *boot_changed);

/** @brief Tick link and atomically discard session state on offline transition. */
canview_status_t canview_uart_session_tick(canview_uart_link_t *link,
                                            canview_uart_plan_context_t *plan,
                                            canview_uart_command_cache_t *cache,
                                            canview_uart_replay_context_t *replay,
                                            uint64_t now_ms);

#ifdef __cplusplus
}
#endif
#endif
